ms0216/keyboard-foundry/projects/cckb/docs/fab-checklist.md

# 発注の直前に見るもの（cckb）

**ここに記録が無いと発注しない。書いたら消さない**（次の発注で同じ穴を踏まないため）。
`tools/kb cckb gate` が open-gaps の「発注をせき止めているもの」を見る。
ここに書くのは、それ以外に**機械では確かめられず人が見るもの**。

## 発注履歴

| 日付 | 対象 | 実装枚数 | 表面処理 | 備考 |
|---|---|---|---|---|

## §0 発注フォームで選ぶもの（JLCPCB）

| 項目 | 値 | 根拠 |
|---|---|---|
| 層 / 厚さ / 銅 | 2 層 / 1.6mm / 1oz | 2 層で足りた（HHKB） |
| 表面処理 | 有鉛 HASL | ¥0（無鉛は +¥222） |
| Remove Order Number | Yes | |
| PCBA | Economic・実装面は裏 | Standard は部品から板端 2.5mm 以上・70×70 以上が条件。**電源スイッチ SW_PWR は JLC に実装させない**（2026-09-24 から秋月の SS-12D00G3・スルーホールで LCSC に無い。前の MK-12C02-G025 はつまみが外形から 1.95 出た。Economic は部品を縁から 0.3 以上・はみ出す SMT 部品はキャリアが要る——JLC PCBA FAQ Part 2・PCB Assembly Fixtures。決定記録 2026-09-24-audit-fixes §R2）。利用者が秋月電子で買って手はんだ |
| Confirm Parts Placement | Yes | §1 を見るため |
| Via Covering | **Tented**（既定のまま） | 板の設定が表裏ともテント（`(tenting (front yes) (back yes))`・ガーバーのマスクの開口はパッドの数と一致）。エポキシ充填などは選ばない——XIAO の D0〜D6 の穴はビアではなく部品の穴（スルーホールパッド）で、この選択は効かない（2 回目の監査 C 軽微 4） |

## §0b 実際に発注する道具を本番の板に通した結果

自前の出力で直したつもりの誤りが、発注道具（Fabrication Toolkit）の出力では
直っていなかった（HHKB）。**実際に使う道具で出して、出力を読む。**

    tools/kb cckb fab-fields
    cd ~/Documents/KiCad/10.0/3rdparty/plugins
    "$KICAD_PYTHON" -m com_github_bennymeg_JLC-Plugin-for-KiCad.cli -p <板の絶対パス> -t -nI -nB
    # 出力は projects/cckb/pcb/production/（gitignore）。**道具は板を書き換えなかった**（前後で sha1 と指紋が同じ）

| 見たもの | 期待 | 結果（日付） |
|---|---|---|
| BOM の LCSC Part # | 全行に番号 | ✅ 6 行すべて（C49678・C54110×62・C8598・C17514・C778186・C52287685）（2026-09-24）→ **監査の直しの後: 5 行すべて**（C49678×2・C54110×62・C8598・C17514×2・C52287685×2。電源スイッチ C778186 は手はんだで外れた）（2026-09-24）→ **2 回目の監査の直しの後: 4 行すべて**（C49678×2・**C54110×63**〔キー 62＋D_PWR。D_PWR の既定を BAT46W にした・open-gaps O12〕・C17514×2・C52287685×2）（2026-09-24）→ **電源スイッチを SS-12D00G3 に替えた後も同じ 4 行・69 個**（Fabrication Toolkit で出し直して読んだ・2026-09-24） |
| CPL の Layer | 裏実装の部品が bottom | ✅ 70 行すべて bottom（2026-09-24）→ **69 行すべて bottom**（2026-09-24・監査の直しの後） |
| 手で付ける部品（XIAO・ホルダ・キーのスイッチ 62・**電源スイッチ**） | BOM・CPL に無い | ✅ どれも無い（2026-09-24・監査の直しの後も） |
| CPL の座標と回転で JLC が置く位置 | JLC の部品データ（EasyEDA の原点とパッド）を CPL どおりに置くと、板の同じ番号のパッドに乗る | ✅ 69 個すべて 0.09mm 以内（`tests/test_cckb_pcb.py::test_jlc_places_every_part_of_the_cpl_on_its_pads`。**検査が Fabrication Toolkit を板の写しに毎回通す**。回転を 90°/180° 違える・原点を 0.45 ずらすと落ちる）（2026-09-24） |
| TSSOP の回転 | `-t` で補正が入っている | ✅ U1/U2 は KiCad 180°（裏）→ CPL 270°（道具の表 `^TSSOP-` +270）。**正しいかは §1 のプレビューで**（2026-09-24） |
| ガーバーの層 | 2 層（内層が無い） | ✅ F_Cu・B_Cu・マスク・ペースト・シルク・外形・PTH/NPTH のドリルの 13 ファイル（2026-09-24） |
| ペーストの開口（B_Paste のフラッシュ） | JLC が実装するパッドだけ（ダイオード 63×2・C 2×2・R 2×2・595 2×16 ＝ 166）。手はんだの電源スイッチ（2026-09-24 からスルーホール 3 本・ペーストの層を持たない）に無い | ✅ B_Paste 166・F_Paste 0（2026-09-24・2 回目の監査 B2-1 の直しの後。前は 173 で SW_PWR の 7 個に盛られた。`test_only_the_jlc_parts_get_solder_paste`） |

## §1 配置プレビューで向きを見る

KiCad と JLC ライブラリの回転は一致しない。プレビューの Bottom 表示は X だけ裏返る。
**「+」は Pin 1 ではなくアノード**だった（SOD-123・HHKB で確認）。判定は 3D 本体の
帯（カソード）で。同じフットプリントなら 1 個読めれば全部に同じ結論が使える。

| 部品 | 面 | KiCad の板（CAD 座標・上から見て） | JLC のプレビュー | 判定（日付） |
|---|---|---|---|---|
| U1 SN74LVC595 | 裏 | 1 番 (−73.34, −5.93)＝**右上**（16 番は左上で C_U1 の隣）。CPL 270° | | 未 |
| U2 | 裏 | 1 番 (79.06, −5.93)＝右上（16 番は左上で C_U2 の隣）。CPL 270° | | 未 |
| D1〜D62 BAT46W（**62 個とも縦**。V2 = `cckb-v2`） | 裏 | カソード（帯・パッド 1・行の網）が**手前（−y）**・アノードが奥。板の上で 90°・CPL 90°（2026-09-26 に板と CPL で数えた: 62 個とも同じ） | | 未 |
| ~~D42・D43・D58・D60（横 4 個）~~ | 裏 | **V1 の行**。V2 ではスタビのキーのダイオードもほかと同じ縦（上の行） | — | 対象外 |
| D_PWR BAT46W（既定。O12 で B5819W に戻すなら読み直す） | 裏 | カソード（パッド 1・V3V3）が**右**（x −122.35・XIAO の 3V3 へ。V2 で (−124.0, −28.45) に動いた）。板の上で 180°・CPL 0° | | 未 |
| ~~SW_PWR SS-12D00G3~~ | 表（スルーホール） | **手はんだ（CPL に無い）**。2026-09-24 に MK-12C02-G025（裏）から置き換えた。足 3 本 (141.225, −36.1 / −38.6 / −41.1)・向きは問わない（足が対称） | — | 対象外 |

## §2 在庫（発注の直前に API で取り直す）

    tools/kb cckb parts

| 確認日 | 結果 | 薄い部品と代替 |
|---|---|---|
| 2026-09-24 | 全部在庫あり（parts-audit.md の表） | 74LVC595 C52287685 が 1,446（要 10）→ 代替 C426713（3,534）。電源スイッチ C778186 3,260（**利用者が LCSC で買う**・監査の直しで手はんだに）。**同日に秋月の SS-12D00G3（115707・通販在庫 38,944）へ置き換え** |

## §3 ピン配置を独立した視点で確かめる（**3 つ済むまで「確認した」と書かない**）

同じ人が同じ表を読んだ 1 視点では、読み違いは全視点で同じ方向に外れる。
IC・MCU・基板間コネクタのピン誤りは 0Ω では救えない。コネクタは「面」だけでなく
**口の向きと口から口までの経路**を追う。

| 部品 | A データシート ↔ pinmap | B 商品写真の 1 番 ↔ 描画 | C KiCad GUI でクリック | D 1:1 印刷に実物を載せる |
|---|---|---|---|---|
| 74LVC595 | ✅（TI SCASE93A Table 4-1 ↔ pinmap。HHKB で同じ表） | 未 | 未 | 未 |
| XIAO（表面実装） | ✅（公式 STEP のキャステレーション ↔ 板のパッド。検査） | 未 | 未 | 未 |
| SS-12D00G3 | ✅（図面の 3-φ0.8・2.5 間隔 ↔ 板のパッド。検査） | 未 | 未 | 未（入の向き・open-gaps P5、爪の出・O13） |
| BS-16-B4AK003 | ✅（図面のランド・＋の側 ↔ 板。検査） | 未 | 未 | 未 |

## §4 リスクを承知して発注する記録

open-gaps の `### 承知して発注する #N` と対応させる。

- **発注の前に利用者が決める・測るもの**（監査の直しで残ったもの）: open-gaps O11（595 の末端を D9 に戻すか）・
  P7（アンテナのまわりをアルミ箔で ¥0 で 1 回測る）・P11（スタビのワイヤが上か下か。実物が届いていれば）・
  P5・O13（電源スイッチ SS-12D00G3 の入の向きと、レバーの先の高さ。届いた 1 個と基板の厚さを測る・order-steps §1 の 3）・
  O14（電池の側にバルクコンデンサを後から足す場所を置くか。task-10a §6 の使える量が 96mAh 未満なら決める）
- ~~**O12（D_PWR を BAT46W のままにするか B5819W に戻すか）**~~ **2026-09-25 に BAT46W で決まった**（保証値で決まる・open-gaps O12）。受け入れた差 A1（USB を挿す前に電源スイッチを OFF）は
  どちらでも手順で残す（~~部品を替えられる品が無いことはデータシートで確かめた~~ ← 1 回目の比べ方は誤り。決定記録 §S2）

## §5 通電前の導通試験（基板が届いたら）

GND↔GND・電源↔電源が導通、電源↔GND が非導通。**通るまで電源を入れない。**

## §6 独立監査（電気 / DFM / 機械 / 外部の事実）

| 見つかったもの | 基板に効くか | どうした |
|---|---|---|
| 監査 A〜F（2026-09-24・HEAD 86611d4・`.superpowers/sdd/cckb-autonomy/audit-*.md`）: 致命 0・重要 5（A-1・B-1・C 重要 1/2・D 重要 1・E 重要 1/2/3。うち C 重要 2 と E 重要 1 と B-1 は同じ電源スイッチ）・軽微 23 | 効く: C 重要 1（パッドの中のビア）・C 重要 2/E 重要 1/B-1（電源スイッチ）・D 重要 1（XIAO の NFC2 の下）・E 重要 3（H3 の下）・軽微 C1/C2/C3/D4 | 裁定 R1〜R7 のとおり直した（決定記録 `decisions/2026-09-24-audit-fixes.md`・報告 `.superpowers/sdd/cckb-autonomy/fix-report.md`）。所見ごとの行き先は報告の一覧。直したものは各々に検査を足し、**直す前の板（HEAD 86611d4）でその検査が落ちる**ことを確かめた |
| 2 回目の監査 A〜E（2026-09-24・HEAD f95a7c9・`audit2-*.md`）: 致命 0・重要 2（A2-1 ダイオードの比べ方・E 重要 1 の H5/H6 のナットの下の CS）・軽微 13 | 効く: E 重要 1（禁止域と CS の置き直し）・B2-1/C1（ペースト）・C2（パッド内ビアの輪）。A2-1 は板は同じで BOM の品番 | 裁定 S1〜S3（決定記録 §S1〜S3・報告 `.superpowers/sdd/cckb-autonomy/fix2-report.md`）。**直す前の板（f95a7c9）に新しい金属の検査を当てると H5・H6 の CS（1.603）を出す**。配線が変わった網は CS（1 本 → 3 本）と GND（縫いのビア）だけ |
| 3 回目の監査（2026-09-24・2 回目の直しを・`audit3.md`）: 致命 0・重要 0・軽微 4 | 効かない | 行き先は status.md §5（直した 3・台帳 A10 に 1） |
| 電源スイッチの置き換えの監査（2026-09-24・`audit-psw.md`）: 重要 1（レバーの先の最悪値に基板の厚さの公差が抜けていた）・軽微 4 | 効かない（ケースと文書） | 最悪 0.2 → 0.36 に訂正（open-gaps O13）・軽微は 3f77086 で直した・台帳 A11・A12 |
| 4 回目の監査 A〜F と文書（2026-09-25・main 3f77086・`audit4-*.md`）: 致命 0・重要 3（E ふたの垂れ壁の隙 0・F 打ち止めの判定・文書 ゴーストの試験）＋文書の重要 2・軽微 60 余り。6 視点すべて「発注してよい」 | **効かない**（板の銅・穴・部品の位置は変えていない。sha1 05e23dfe… は前後で同じ） | ケース・ファーム・文書を直し、重要には検査を足して壊して落ちることを確かめた（branch cckb-fix4）。軽微の行き先は status.md §6。D 軽微 4（バルクの置き場）は利用者の判断 O14 |

**問題なしを確認したもの（母数）:** / **見ていないもの:**
