ms0216/keyboard-foundry/projects/cckb-click/docs/decisions/2026-10-04-knob-out-pilot.md

# 電源スイッチを 0.75 外へ（JLC の「2.5 mm」は満たさない）・下穴 φ1.6・蓋は考え直し

- **日付:** 2026-10-04
- **状態:** 決定（**直した板 b442b865… は、まだ独立に見直していない**: open-gaps #36。蓋は決まっていない: #34b・P21）
  **→ そのあと: #36 は 4 回目の監査で閉じた。蓋は「ねじ 2 本で留める」に一度決まり（決定記録 [2026-10-04-cover-screw](2026-10-04-cover-screw.md)）、同じ日に「道具なしで上から落とし込む」に置き換えた（決定記録 [2026-10-04-cover-latch](2026-10-04-cover-latch.md)。枠の口の形も、そこで変えた）**
- **決めた人:** 利用者（試し刷り v2 を刷って触った結果。下の 3 つ）。寸法と形は Claude

利用者の決定（2026-10-04・試し刷り v2 の結果。docs/coupon-test.md 8 章「結果」）:

1. **電源スイッチは (ii) = 0.75 外**。JLC の実装の規約「部品の本体と基板の縁は 2.5 mm 以上」より、**使いやすさを取る**
2. **ねじの下穴は φ1.6**（ふつうの M2×4 の小ねじ。3 つの径とも空回りしなかった。φ1.5 は入れ始めにかなり力が要った）
3. **蓋は 3 つとも使えない。蓋そのものを考え直す**（利用者が考える。ここでは作り直していない）

この記録は、決定記録 2026-10-04-switch-cover の「スイッチを 2.5 内側へ」と「差し込み式の蓋」を**置き換える**（そちらの冒頭に書いた）。

## 1. なぜ決める必要が生じたか

- 2.5 内側の位置（つまみの先は枠の外面の 1.35 内）は、刷って触ると**奥すぎた**（v1 の角の試し刷り）。v2 で 0.75 外の位置と並べて、利用者が (ii) を選んだ
- 下穴 φ1.8 は、最後まで締めると空回りした（v1 のねじの試し刷り）
- 蓋は v1（掛かり 0.25）も、v2 の 3 つ（折り返しばね・細い腕・筋）も留まらなかった

## 2. 事実はどうか（測った・読んだもの）

| 何 | 前の板（fe90b1e6…） | いまの板（b442b865…） | 何で確かめたか |
|---|---|---|---|
| 電源スイッチの足跡の原点 | (141.125, −38.1) | **(141.875, −38.1)**（x だけ +0.75） | 板（前の板と今の板の部品を全部突き合わせた: 動いたのは SW_PWR だけ） |
| 本体の縁 → 基板の縁 | 2.50 | **1.75** | 板の上の突起の穴（本体の中心線）＋ 図面の本体の幅 2.8（tests `psw_edge_problems`） |
| つまみの先 → 基板の縁／枠の外面 | 1.05／1.35 内 | **0.30／0.60 内**（入でも切でも同じ。つまみは前後に滑るだけ） | 同上 ＋ 図面のつまみの出 1.45 |
| スイッチのランドの外の端 → 基板の縁 | 2.45 | 1.70 | 板のパッドの外接 |
| スイッチのランドの左の端 → C_BAT のランド | 1.375 | 2.125（C_BAT は動かしていない） | 同上 |
| 入の向き | つまみを奥 = 入 | **変わらない**（奥の端子 3 番が VBAT_SW・真ん中 2 番が VBAT_IN・手前 1 番は空き） | 板のパッドの網（検査） |
| 枠の入の印 | 切り欠きの内側の面の 1.2 内・入に寄せたつまみの奥の縁の高さ | **高さ（y）は同じ**。x は、斜めに落とした面のすぐ内の平らな上面（内側の面から 3.2 内） | 枠の立体（検査）。斜面の上に置くと、上面から掘る印は空を切る |
| 線・ビア（右手前の角の外） | — | **角の中の 8 本のほか、長い VBAT_SW の右の端が 0.75 延びた**（変わった線は 9 本。x 138.125 → 138.875〔監査の座標では 288.125 → 288.875〕。差は x ≥ 287.6・y 127.9〜143.2 に収まる〔4 回目の監査で言い直した〕） | 板どうしの突き合わせ（線 772 本・ビア 906 → 907 個・ルール領域 134 個・両面のベタの塗り） |
| 線・ビア（角の中） | — | 線 8 本を引き直した（VBAT_IN・VBAT_SW の端と C_BAT の枝・スイッチの枠のランドの GND の 4 本）。GND のビアは 6 個消えて 7 個足した | 同上 |
| ベタの塗りの違い（角の外） | — | 表も裏も 0（角の中は 表 17.7・裏 4.2 mm²） | 同上（塗りの多角形どうしの差） |
| SPI・595 どうし・電源の枝 | 監査した板の線を置き直し | **同じ**（pcb/freerouted.json・線 100・ビア 17） | 検査 `frozen_problems`・route.json |
| DRC | 違反 0・未配線 0・警告 0 | **違反 0・未配線 0・警告 0** | kicad-cli |
| BOM・CPL | 7 行・133 行 | 7 行・133 行。SW_PWR の行は (291.875, −138.1)・90° | 発注道具の出力 |
| 下穴の径（設計） | φ1.8 | **φ1.6**（外周 20 ＋ 予備 2 = 22 個とも） | 枠の立体（検査が 22 個を見る） |
| 下穴の径（刷る線が空ける径） | 1.76〜1.79 | **ふつうの壁 19 個: 1.54**（平均 1.537〜1.543）・**薄い壁 3 個（H16・H17・H18）: 1.49〜1.50** | 本番の枠 2 枚をスライスした G-code（`tools/slice_main.py`・Bambu Studio 2.8.2） |
| 　試し刷り v2 で利用者が締めた切れ端 | — | φ1.6: 1.54／1.50・φ1.5: 1.44／1.40・φ1.7: 1.64／1.60（ふつうの壁／薄い壁） | v2 の G-code（`tools/slice_v2.py`・同じ測り方） |
| ねじ山の掛かり（半径） | 0.10（山の 46 %） | 0.20（92 %） | ISO 724 の M2（外径 2.0・めねじの内径 1.567）から |
| 下穴のまわりの肉（内側） | 0.70／薄い所 0.49 | 0.80／0.59。**ねじの外径 2.0 の外に残る壁は変わらない**（0.6／0.39） | 枠の立体（検査） |
| 指先（半径 7.5 の硬い球・机の上）が、つまみの先より奥へ入る量 | −0.03（新しい切り欠きでも届かない） | **+0.16** | 本番の枠の角の立体に球を当てた（`click_case.finger_reach`）。**球の半径は仮定** |

## 3. 効く条件（候補を並べる前に）

| # | 条件 | 実データ | 何で確かめたか |
|---|---|---|---|
| 1 | 指でつまみを動かせる | 利用者が (ii) を選んだ。物差しでは −0.03 → +0.16 | **外: 利用者が刷って触った**（v2 の B）。数は自分の生成物（物差し） |
| 2 | 外へ出る物が無い（鞄の中で引っ掛からない） | つまみの先は枠の外面の 0.60 内・基板の縁の 0.30 内 | 板の突起の穴と図面（検査）。枠の立体でも見る |
| 3 | JLC の実装の規約「本体と基板の縁は 2.5 mm 以上」 | **満たさない（1.75）** | 外: JLC の規約の頁（docs/order-steps.md の出どころ・2026-10-04 に読んだ値）と、板の寸法 |
| 4 | Economic の注意書き「線と部品は縁から 0.3 mm 以上」 | つまみの先で **名目ちょうど 0.30**（ランドは 1.70・本体は 1.75） | 同上 |
| 5 | JLC が載せないと言ったときの手 | 手はんだ（端子 3 ＋ 枠 4 = 7 か所・C431540 を 1 個）。**基板は変わらない** | 足跡のパッドの数（板） |
| 6 | 監査した配線を変えない | 上の表（線 9 本 = 角の中 8 本＋VBAT_SW の右の端） | 板どうしの突き合わせ |
| 7 | 切り欠きのまわりの壁が弱くならない | 下の §5「枠」。厳しい見方で 20.4 MPa（上限 38）・前の形は 7.3 | 計算（断面は枠の立体から測る）。**利用者が触った (ii) の切れ端と同じ形**（式から作った切れ端と本番の枠が同じ立体であることを検査で見る） |
| 8 | ねじが空回りしない | φ1.5／1.6／1.7 とも空回りしなかった | **外: 利用者が締めた**（v2 の A）。**締め直した回数は聞いていない** |
| 9 | ねじを入れ始められる | φ1.5 は入れ始めにかなり力が要った。φ1.6 は薄い壁でも問題なし | 同上 |
| 10 | 壁が割れない | 利用者の報告に割れは無い（φ1.6・薄い壁でも問題なし） | 同上。本番の枠でも 1 本入れて確かめる（P1） |
| 11 | 本番の枠の下穴が、利用者が締めた物と同じ径で刷られる | 1.54／1.50 で同じ | 本番の枠と v2 の、両方の G-code を同じ測り方で |

## 4. 影響範囲（力と信号の流れに沿って）

- **スイッチの位置 → 足跡 → 電池の＋（VBAT_IN）の最後の区間・VBAT_SW の縦の区間と C_BAT の枝・枠のランド 4 つの GND のビア → 角の GND の縫いのビア**。
  どれも決まった形で引く線（click_routes）なので、足跡と一緒に 0.75 動いた。長い線（VBAT_SW・263 mm）は右の端が 0.75 延びただけ。
  SPI・595 どうし・電源の枝（左手前）は置き直しで、変わらない
- **スイッチの位置 → JLC の規約 → 頼み方**: 2.5 mm を満たさないので、JLC が載せないと言うことがありうる。そのときは手はんだ（docs/order-steps.md の冒頭）
- **スイッチの位置 → 枠の逃げ・切り欠き・厚い屋根 → 壁の強さ**: 切り欠きの内側の面は本体の縁 ＋ 0.4（枠の外面から 1.65）。切り欠きの形は v2 の B と同じ
- **指 → 切り欠き → つまみ → スイッチの本体 → はんだ（端子 3・枠 4・突起 2）→ 基板**: つまみを動かす力（最大 2.45 N）は基板が受ける（前と同じ）。
  ランドと基板の縁の間は 1.70（前は 2.45）
- **下穴 → ねじ山の掛かり → 壁の内側の肉 → キーの穴 → キャップ**: 穴の位置は変えていない。肉は 0.1 増えた。ねじが押し広げる樹脂は増える
  （ねじの外径の外の壁 0.6／0.39 は同じ）
- **下穴 → 試し刷り（ねじ・角・v2）**: どれも本番の枠から切り出すので、下穴と切り欠きが新しい形になる（v2 は、刷った物と同じ形を出し続けるように、
  位置を本番から測り直した: (i) = 本番から 0.75 内・(ii) = 本番）
- **蓋 → 枠の口のまわり・基板の穴 H30・H31**: 蓋を刷る物から外しただけ。枠のひさし・溝・指の切り欠き・基板の穴は前のまま

## 5. 決めたこと

### 基板

| 何 | 決定 |
|---|---|
| 電源スイッチ | 足跡の原点 (141.875, −38.1)。向き・端子の網は同じ。**JLC に載せてもらう（BOM・CPL に入れたまま）。断られたら手はんだ** |
| C_BAT | 動かさない（(136.2, −33.0)。スイッチのランドから 2.125） |
| 決まり（spec） | `PSW_TIP_INSIDE = 0.3`（つまみの先は基板の縁の 0.30 以上内側。これより外へは寄せない）・`PSW_BODY_TO_EDGE = 1.75`（記録。検査が板と突き合わせる） |
| 蓋のねじ穴 H30・H31 | 残す（使い道は蓋を考え直すときに決める） |

### 枠

| 何 | 決定 | 刷って直せるか |
|---|---|---|
| つまみの切り欠き | **利用者が (ii) で触った形**: 内側の面で幅 10・外面へ向かって片側 2.4 ずつ広がる（外面で 14.8）・内側の面の上の縁を 2.0 斜めに落とす（45°）。`PSW_NOTCH = (10.0, 2.4, 2.0)` | 直せる（右の枠だけ） |
| 切り欠きの内側 | 屋根を基板の上 1.8 まで厚くして塞ぐ（前と同じ）。斜めに落とした後、内側の面で 1.2 残る | — |
| 入の印 | 斜面のすぐ内の平らな上面。高さ（y）は前と同じ | 直せる |
| 下穴 | **φ1.6**・22 個とも。**薄い壁の 3 個も補正しない**（下） | 直せる（きつければドリルで広げる） |
| 電池の口のまわり | **変えない**（ひさし・溝・指の切り欠きは前のまま） | — |

**薄い壁の下穴を補正しない理由**: 薄い壁（幅の広いキーの脇の H16・H17・H18）では、刷る線が設計より 0.04〜0.05 内へ寄る（壁が線 1 本になるため）。
φ1.6 は線で 1.49〜1.50 になる。これは、利用者が v2 で「薄い壁でも問題なし」とした切れ端（線で 1.50）と**同じ径**で、入れ始めが固かった φ1.5（線で 1.44／1.40）ではない。
補正して φ1.65〜1.7 にすると、利用者が確かめていない組み合わせになり、ゆるい側へ寄る（ゆるい穴は直せない・きつい穴はドリルで広げられる）。
`tools/slice_main.py` が、本番の枠の 22 個を G-code で測って、利用者が確かめた径（1.54 ± 0.03／1.50 ± 0.03）から外れたら NG を出す。

**切り欠きのまわりの強さ（計算。材料は Bambu PLA Basic の TDS の曲げ強さ 76 MPa の半分 = 38 MPa を上限に置く）**

| 見方 | 前の形（外の角を 1.0 落とすだけ） | いまの形（内側の上の縁を 2.0 斜めに） |
|---|---|---|
| 内側の縁を指で下へ 10 N。**縁の 2.0 幅だけ**が、幅 10 を渡る梁として働く（いちばん厳しい見方） | 7.3 MPa | **20.4 MPa**（上限の 0.54 倍。断面は台形 = 内側の面で 1.2・2.0 奥で 3.2） |
| 同じ。厚い屋根の全幅 5.4 が働く | — | 3.5 MPa |
| 切り欠きの手前に残る壁（角まで）を y の向きに 10 N（せん断） | 0.44 MPa（長さ 7.525） | 0.49 MPa（外面で長さ 5.125） |

余裕は前より減った（5.2 倍 → 1.9 倍・厳しい見方で）。**20 N なら、厳しい見方では上限を超える**（検査に入れた）。断面は枠の立体から測る（式で置いた台形と合うことも検査で見る）。
利用者が触った (ii) の切れ端と同じ形なので、割れやすさは刷った物で分かっている範囲（利用者の報告に割れは無い）。

### 刷る物

| 何 | 決定 |
|---|---|
| 電池の蓋（`cover_battery.stl`） | **刷る物から外した**（STL を出さない・組んだ絵にも入れない）。形（`click_case.cover_solid`）と検査は、枠の口のまわりの形の説明として残してある |
| 試し刷り（ねじ・角・v2） | 済み。作り続ける（本番の枠から切り出す検査が、本番の形を見張る） |

## 検討して捨てた案

| 案 | 捨てた理由 |
|---|---|
| (i) のまま（本体は縁から 2.5）で、爪で使う | 利用者が (ii) を選んだ |
| つまみに被せる刷り物で、位置は (i) のまま | 作っていない（利用者は (ii) を選んだ）。JLC に断られて、手はんだもしたくないときの手として残る |
| 0.75 より外へ | つまみの先が基板の縁の 0.30 内 = Economic の「縁から 0.3 以上」の下限。これより外は、その注意書きも満たさない |
| 薄い壁の下穴だけ φ1.65〜1.7 にして、線の径をふつうの壁に合わせる | 上の「補正しない理由」 |
| 下穴 φ1.5 | 入れ始めにかなり力が要った（利用者）。めねじの内径 1.567 より小さく、ねじが樹脂を押し広げる |
| 下穴 φ1.7 | 空回りはしなかったが、掛かりが半径 0.15（69 %）で、φ1.8（空回り）に近い側 |
| 蓋をこの作業で作り直す | 利用者が蓋そのものを考え直している（頼まれた範囲の外） |

## この決定が乗っている前提（動いたら読み直す）

- **JLC の規約の「2.5 mm」と Economic の「0.3 mm」は 2026-10-04 に読んだ値**（出どころは docs/order-steps.md §2-1）。JLC が実際にどう扱うかは、注文してみるまで分からない
- 電源スイッチは MSK12C02（本体 8 × 2.8・つまみの出 1.45・行程 1.6）。**つまみの出は図面の名目**（置くずれ・基板の外形の公差 ± 0.2 は見ていない）。
  **つまみの出の公差（4 回目の監査 2026-10-04 で直した）**: MSK12C02 の図面（LCSC C431540・2024-12-14）は、つまみの出 1.45・中心から先まで 2.85 に**個別の公差を書いていない**。表題欄の未注の公差は X.xx = ± 0.2（± 0.1 はつまみの幅 1.3・本体の幅 2.8・突起 φ0.75 だけ）。**前の記録の「± 0.1」は誤り → ± 0.2**。出どころ: 図面を自分で開いて読んだ（datasheet.lcsc.com の PDF 1 頁目の表題欄。2026-10-04）。**最悪の場合**: 基板の縁に対して 0.30 − 0.20 − 0.075（φ0.75 の突起と φ0.9 の穴の遊び）= **+0.025**（細い突起 φ0.65 なら −0.025）= 先は**実質、基板の名目の縁まで届きうる**。枠の外面に対して 0.60 − 0.20 − 0.075〜0.125 − 0.1（ねじ穴の遊び）− 0.1（刷りの誤差）≒ **+0.10〜+0.13** = 枠の外へは出ない。
  **利用者の選択肢（まだ決めていない）**: スイッチを 0.2 内へ戻す（先は基板の縁の 0.50 内）と余裕は戻るが、利用者が触って選んだ位置から離れる。
- ねじは**ふつうの M2×4 の小ねじ**で試した（買う物の表のスリムヘッドではない。ねじ山は同じ M2 並目）。掛かりの長さ 2.4
- 刷り方は 0.4 ノズル・層 0.1・Bambu PLA Basic（下穴の線の径は、この設定での値）
- `pcb/freerouted.json` は板 4dc68901… から写した物のまま（左手前の配置は変えていない）
- 利用者の指は 1 人ぶん。指先の球（半径 7.5）は物差し

## 覆す前に読むこと

- スイッチの位置は発注後に直せない。**内へ戻す（2.5）と JLC の規約は満たすが、利用者が「奥すぎる」と言った位置に戻る**
- 下穴を変えるなら、`tools/slice_main.py` の許す幅（利用者が確かめた径）も一緒に見る。小さくする側は φ1.5 が固かった
- 切り欠きの斜めに落とす量を増やすと、内側の縁が薄くなる（3.0 にすると、厳しい見方で上限を超える: 検査）

## まだ決めていないこと・分からないこと

| 項目 | なぜ |
|---|---|
| JLC が電源スイッチを載せるか | 注文画面か、注文の後の確認でしか分からない（docs/order-steps.md）。断られたら手はんだ |
| ねじを何回締め直せるか | **利用者が締め直した回数を聞いていない**（open-gaps P1）。分解のたびに締め直す |
| スリムヘッドのねじでも同じか | 試したのは、ふつうの小ねじ。ねじ山は同じだが、頭が薄いのでドライバーの掛かりが違う |
| 本物のスイッチのつまみを指で動かせるか | 試し刷りのつまみは樹脂の小片（P22） |
| 電池の蓋をどうするか | 利用者が考え直している（#34b・P21）。**新しい蓋が基板に何か要るなら、発注の前に決める** |
| 直した板の独立した見直し | まだ（#36） |
