ms0216/keyboard-foundry/projects/cckb-click/docs/decisions/2026-10-03-board-and-case.md

# 基板と枠: 部品の足跡・配置・配線の形・枠の留め方・分け方・角・電池の出し入れ・底

- **日付:** 2026-10-03
- **状態:** 決定（設計）。`[暫定]` の値は docs/provisional-values.md
- **⚠️ 先に読むこと（2026-10-04）:** 1 回目の独立した監査（致命 0）で、下の数字のうち次が変わった。**正は [2026-10-04-audit-1](2026-10-04-audit-1.md)。**
  ねじの穴: 外周 20 ＋ 予備 2・枠の外面から 2.4（前は 2.5）・下穴のまわりの肉は外 1.5・内 0.7（前は 1.6・0.6）／
  電池: 止めに当たる所に座る（クリップの原点から 0.51 奥）・指の切り欠きの奥行き 4.5（前は 4.0）／
  GND: 595 のいるキーの中も 15 mm 以内（前は 17.2）／ 載せないコンデンサのランド 2 つを足した ／
  JLC の頼み方（Economic か Standard か）は利用者が決める（docs/order-steps.md §2-1）
- **決めた人:** 部品（スイッチ・ダイオード・595・電池クリップ・電源スイッチ・XIAO は表に平置き・裏には何も置かない・基板 1.6・1 枚）は利用者。
  形と数値は Claude。**利用者にしか決められないこと**（底のシート・ねじを買う・基板の表面処理）は status.md にまとめた

## 1. なぜ決める必要が生じたか

試し刷りで 1 マスの形（案 B・穴 17.05 角・つばのキャップ）が決まった（2026-10-03-coupon-result）。基板は発注すると直せないので、
基板・枠・キャップ・ファームを通しで設計し、機械で確かめられる所まで確かめてから、独立した監査へ渡す。

## 2. 事実はどうか（読んだもの・測ったもの）

**部品（データシート・製造元の図・JLC の部品ページ。2026-10-03）**

| 部品 | 読んだ物 | 事実 |
|---|---|---|
| スイッチ SKRAAWE010（C202383） | Alps の製品ページの図（Land dimensions・Circuit Diagram）・製品仕様書 | ランド 4 つ（外外 8.5 × 5.0・内内 3.0 × 3.0）。端子 ①—②・③—④ が中でつながる。定格の下限 1 V・10 µA。跳ね ON・OFF とも 10 ms 以下。10.3(4)「スイッチの下・近くに穴を置かない」。はんだペーストの厚さ 0.15 |
| 同じランドの実績 | 販売者が JLC に実装させた基板（PCB_Data/ClickBoard Tenkey/Assemble Alps Silent・MIT）の足跡 SKRACAE010_1u | Alps の図と同じランド（2.75 × 1.0 を ±2.875, ±2.0） |
| 電池クリップ MY-1632-03-R（C20606805） | MYOUNG の図面 MY-CP-0247 | 高さ 4.0・板の幅 16.9・端子込み 23.2 ± 0.3・止め（幅 6.35）から口まで 15.10。＋のランド 4.15 × 4.20 を中心の間 20.05。**−は電池が基板に直に当たる**（図に寸法なし。LCSC の足跡は中心に φ7.0）。口の縁の真ん中は 1.4 えぐれている（LCSC の足跡の外形） |
| 電源スイッチ MSK12C02（C431540） | SHOU HAN の承認書（2024-12-14）の外形図・安装参考图 | 本体 8 × 2.8・**高さ 1.4**・つまみ 1.3 幅が**本体の横へ** 1.45 出る・行程 1.6・位置決めの突起 φ0.75 × 2・1P2T（2 が共通）・枠は回路図でアースへ。12 V 50 mA・1 万回 |
| JLC の実装の種類 | 部品ページ（jlcpcb.com/partdetail/…）の「PCBA Type」 | 8 品とも **Economic and Standard**（projects/cckb-click/tools/parts_check.py が取り直す） |
| ねじ | MISUMI の規格表（スリムヘッド小ねじ・超極低頭 M2） | 頭 φ4.0・頭の高さ 0.5 ± 0.1 |
| XIAO nRF52840 | 公式 STEP（lib/xiao.3dshapes）を測った | シールド缶の上面が下面から 3.25・USB のシェルの上面 4.47 |

**在庫と単価（JLC の API・2026-10-03）**: docs/shopping-list.md。

## 3. 効く条件

| # | 条件 | 実データ | 何で確かめたか |
|---|---|---|---|
| 1 | 足跡が部品に合う | スイッチ・電池クリップ・電源スイッチ | 外（製造元の図の値・LCSC の部品データ・販売者の足跡）＋検査（0.1 ずらすと落ちる） |
| 2 | JLC が置く位置と向きが板のパッドに合う | 133 個とも 0.15 以内・番号ごと | 外（発注道具の CPL ＋ JLC の部品データ）＋検査（180° 回す・0.3 ずらすと落ちる） |
| 3 | 回路が CCKB と同じ（ファームを共有できる） | 違うのは電池の部品・電源スイッチ・試験用のランドだけ | 検査（CCKB の回路の宣言と突き合わせる） |
| 4 | 宣言どおりに繋がっている | 567 パッド・未配線 0 | 外（KiCad の DRC・板から読んだパッドのネット） |
| 5 | JLC の規則（線・間隔・穴・縁）・短い長円が無い | 違反 0・警告 0・穴は全部丸 | 外（kicad-cli の DRC・規則は foundry.pcb_rules）＋発注道具のドリルのファイル |
| 6 | アンテナの下に銅が無い・XIAO の裏の露出パッドの下の表に銅が無い | 0 mm²（対照は銅あり） | 板から測った面積（CCKB と同じ禁止域の決め方） |
| 7 | ねじの頭（金属）の下に裏の銅が無い | 28 か所とも 0 | 同上 |
| 8 | 電池の下と抜き差しの道に表の銅が無い（電池の缶〔＋〕が擦れても GND に触れない） | 電池のパッドだけ | 同上 |
| 9 | スイッチの本体の下にビアが無い（Alps 10.3(4)） | 84 か所（空きランドも） | 板のビアの位置 |
| 10 | GND の細い帯の先がビアから遠くない | 表 13.3・裏 14.2 mm（595 のいるキーの中だけ 17.2） | 板の塗りを格子に落として銅の上の道のりを測る（ビアを消すと落ちる） |
| 11 | スイッチの定格の下限（1 V・10 µA）を走査で満たす | 打ち止め 2.0 V でも約 109 µA | 計算（BAT46W の Vf の保証値・nRF52840 のプルダウンの最大 16 kΩ）。**実機で測る**（open-gaps #7） |
| 12 | キャップが、置いたとき・押し切り・縁を押し切った傾きで何にも当たらない | 62 個 × 5 通り・干渉 0 | 立体を動かして重ねる（背の高い部品・穴の下の柱・深い押し込みで落ちる） |
| 13 | 組める・外せる | キャップ 62 個が枠の下からまっすぐ入る・基板の部品が枠へまっすぐ入る・電池が口から抜ける・USB が挿さる | 立体の道を枠と重ねる |
| 14 | 刷れる | 枠は上面をベッドに・支え無し・A1 mini に入る（156.4 と 140.0） | 立体の「上を向いた面」を数える＋実際にスライス |
| 15 | 誤入力しない剛性 | 下の §2-2 | 計算（断面は立体から）。**材料の値と、ねじの効きは測っていない** |

### 2-2. たわみ（click_stiffness.py・build/cckb-click/main_stiffness.png）

重さ 約 207 g・長さ 291.75。材料は一般値（FR-4 18〜24 GPa・PLA 2.3〜3.5 GPa。**測っていない**）。枠の断面は作った立体を切って測った。

| 持ち方 | 基板だけ | 枠を載せただけ（ねじが効かない） | 一体（ねじでずれ 0） |
|---|---|---|---|
| 片端を持つ（手の中 30） | 5.3（4.9〜6.5） | 3.6（3.0〜4.2） | 1.2（0.9〜1.3） |
| 両端を持つ | 0.9 | 0.6 | 0.2 |
| 両端を持って真ん中を 10 N で押す | 6.8 | 4.5 | 1.5 |

（mm。かっこは材料の幅。）実物は「載せただけ」と「一体」の間。**どこになるかは、外周のねじ 20 本がずれをどれだけ止めるかで決まり、計算では分からない**
（穴 φ2.2 にねじ φ2.0 = 片側 0.1 の遊び。締めた摩擦でどこまで止まるか）。

**誤入力に効くのは、この全体のたわみではない。**枠の下面と基板の距離が、押していないキーの所で 0.1 縮むと（公差の端の個体で）ON になる。
枠と基板は全部のキーの脇の柱（141 本）で突っ張っているので、縮むのは柱と柱の間だけ:

| 縮む原因 | 量（材料は柔らかい側） | 余裕 0.1 に対して |
|---|---|---|
| 指が底を突いて、枠のリブの交点を 3 N で押す | 0.026 | 26% |
| 同じ所を 10 N で強く押し込む（断面は作った枠を切って測った 2.64 mm²。式だけのときは 2.8 と置いて 0.078 だった） | 0.086 | 86% |
| 柱 1 本が 10 N で縮む | 0.002 | 2% |
| 一緒に曲がるときの、柱の間の弧の差 | 0.000001 以下 | — |

名目の個体（浮き 0.2 ＋ ON まで 0.3 = 0.5）なら 10 N でも 16%。

## 4. 影響範囲（信号・力・手の流れに沿って）

- **指 → キャップ → スイッチ → ランド → ダイオード → 行のバス → XIAO**／**595 → 列の束 → 列のビア → 裏の縦線 → 各段のスイッチ**。
  行は表の横一直線、列は裏の縦線。XIAO からバスまでは裏（XIAO の下の表は銅の禁止）。595 から列までは、段 2 と段 3 の間の表を束で走る
- **指 → 枠のリブ → 柱 → 基板**／**枠の壁 → ねじ → 基板**。ねじは外周だけ（下の「中の押さえ」）
- **電池 → 口（手前の壁）→ クリップの下 → 基板の裸の銅**。指は切り欠きから電池の上面へ
- **USB のプラグ → 枠の切り欠き → XIAO の口**。プラグの樹脂は枠の外面の外 0.7
- 枠を 2 枚に分ける → 継ぎ目の列のキャップは、左の枠のリブと右の枠の穴の両方に触る → 左右のずれが隙 0.2 を食う（open-gaps P3）
- 基板の縁を枠が 0.3 覆う → ~~電源スイッチのつまみは基板の縁から 0.7・枠の外面から 0.4 出る → **JLC が縁からはみ出す部品を載せるか**（order-steps §3）~~
  **2026-10-04 に変えた**: スイッチを 1.75 内側へ。つまみは枠の外面の 1.35 内側（決定記録 2026-10-04-switch-cover）。
  **同じ日にもう一度変えた**: 刷って触ると奥すぎたので 0.75 外へ戻した。つまみは枠の外面の 0.60 内側・本体は基板の縁から 1.75
  = **JLC の「2.5 mm 以上」は満たさない**（決定記録 2026-10-04-knob-out-pilot）

## 5. 決めたこと

### 基板

| 何 | 決定 | なぜ |
|---|---|---|
| 外形 | 291.15 × 100.65・角 R2.0・1.6 mm・1 枚・2 層 | キー領域 ＋ 枠の縁 3.0 − 枠が覆う 0.3 |
| スイッチのランド | Alps の図のまま（SW_Alps_SKRA_6.2x6.2）。**EVQQ2 と重ねたランドにしない** | 大きなランドは、リフローで部品が自分で中心に寄る力を弱め、浮き・傾きを出しやすい。押す面の余裕は 0.1〜0.2。安全と言い切れない |
| 幅の広いキー 11 個 | 真ん中のスイッチ（JLC が実装）＋左右に**空きランド**（真ん中と並列・実装しない・はんだを載せない）。中心は穴の端から 4.3（1.5u ±8.99・1.75u ±11.37・2.25u ±16.13） | 外に置くほど、端を押したときの傾きが小さい。ランドの外端が穴の端のすぐ内側（柱の下に入らないいちばん外） |
| ダイオード | 表・スイッチの手前 5.6・横置き。アノードが手前右のランドの真下 | スイッチ → ダイオードが縦の 1 本。背 1.35 は、縁を押し切ったキャップの下面（公差の端で 1.6）より低い |
| 595 ×2 | **左 Shift（2.25u）の、真ん中のランドと左右の空きランドの間**に 270° で。U2 が左・U1 が右 | 1u のキーの中には入らない（本体と穴の縁の間 5.4）。XIAO のすぐ奥で SPI が短い。奥の列のピン（Q1〜Q7）が束の帯に向く |
| 列の束 | 段 2 と段 3 の間の表を 15 本（0.4 おき）。行き先の近い線ほど手前 | 裏は列の縦線の櫛で、横に長く走れない。段 3 にはほぼ全部の列のキーがある（列 0・12 は裏の縦線へビアで） |
| VBAT_SW の長い線 | 決まった形（段 3 のバスの 1.9 手前・電源スイッチ → 試験用のランド TP_VSW） | Freerouting に任せると、バスとの間にビアの打てない GND の帯（263 mm）ができた |
| 電池の −のランド | 裸の銅 φ7.0・はんだを載せない・中にビア 3 個で裏の GND へ。電池の下と抜き差しの道は表の銅なし | 平らでないと電池が浮く。電池の缶（＋）が GND に触れない |
| 電源スイッチ | ~~つまみを右の縁へ。先が枠の外面から 0.4 出る。~~ **2026-10-04 に変えた: つまみは枠の切り欠きの中。本体は基板の縁から ~~2.5~~ → 1.75**（決定記録 2026-10-04-switch-cover → 2026-10-04-knob-out-pilot）。奥へ寄せると入（**図の読み**。これは変わらない） | 入の向きは基板が届いたらテスターで |
| ねじの穴 | 外周 20（キーの辺の真ん中）＋ 中 8（下） | 下 |
| Freerouting | SPI・595 どうし・電源・電池電圧の 8 網だけ。「最適化」は切る | 行列の 628 本を障害物として渡すと、最適化 1 回が 17 分で何も変わらなかった |

### 枠・ねじ・底

| 何 | 決定 | なぜ |
|---|---|---|
| 外形 | 291.75 × 101.25 × 5.0（基板の上）。縁はキー領域から 3.0 | 外周の壁に M2 を立てる肉（外 1.6・内 0.6） |
| 留め方 | **スリムヘッド M2×4 を基板の下から、枠の壁に直に切る**（下穴 ~~φ1.8~~ → **φ1.6**〔2026-10-04・試し刷り v2 の結果〕・深さ 2.8・掛かり 2.4）。20 本 | 厚さを足さない。インサート（外径 3.2）・ナット（二面幅 4.0）は壁 4.0 に入らない |
| 中の押さえ | **基板に穴だけ開ける（8 個）。枠の足は既定では付けない** | 足は柱から横へ出た円盤で、枠を上面を下にして刷ると宙に浮く（支え材が、キャップの滑る面のすぐ脇に立つ）。掛かりも 1.4 しか取れない（キーの縁を押し切ったキャップの下面が 1.6 まで下りる）。誤入力には要らない（縮む向きは柱が止める）。枠が反って真ん中が浮く（がたが増える）ときの手。**基板の穴は後から開けられない**ので開けておく |
| 分け方 | 左右 2 枚（156.4 と 140.0）。段ごとにキーの境目で。継ぎ目のリブは左が持つ。隙 0.1 | A1 mini（168）。リブを半分に割ると、くぼみを掘って 0.4 しか残らない |
| 左の角（XIAO） | 屋根 1.3（下面 3.7）。USB の口の上は切り欠き（屋根なし） | シェルの上 4.57 から枠の上面まで 0.43 しか無い |
| 右の角（電池） | 屋根 0.7（下面 4.3）。**手前の壁に電池の口**（幅 16.6 × 高さ 3.6）と、その上の指の切り欠き（幅 13 × 奥行き 4） | **分解せずに電池を替える**。クリップの口のえぐりと切り欠きを合わせ、電池の上面が手前から約 3 mm（23 mm²）見える |
| 底 | 基板の下面に厚さ 0.5 のシート（ねじの頭の所は φ5 の穴）。**何を貼るかは利用者**（status.md）。刷った板は付けない | 基板の下へ出るのはねじの頭 0.5 だけ。刷った板は 0.6 以上厚くなる |
| 厚さ | **8.1**（シート 0.5 ＋ 基板 1.6 ＋ キャップの上面 6.0）。枠の上面まで 7.1 | 目標どおり。シートの厚さは買う物で変わる |

## 検討して捨てた案

| 案 | 捨てた理由 |
|---|---|
| 595 を 1u のキーの奥の帯に | 本体 ±3.1 と穴の縁 8.525 の間は 5.4。TSSOP の長さ 5.0 ＋ 余白が収まらない（DRC の重なり） |
| 595 を右の角（屋根の下） | 列 15 本を角から各列へ運ぶ道が無い（裏は列の縦線で塞がる・表は行のバスで塞がる） |
| 列を全部 Freerouting に | 16 回回して 15 本残った。595 を自分の線で囲んでいた・表に通れる所が少ない |
| 表のベタの最小幅を 1.1（ビアの打てる幅）に | 595 の GND のピンのビアが表のベタから切れて、配線の道具が止まった |
| キー領域の中にもねじ（リブの下の柱に） | リブ 2.0 に M2 は立たない。柱を太らせると、押し切ったキャップ・つばの下に入る |
| インサート・ナット | 壁 4.0 に入らない。厚さを足すことになる |
| 枠で基板の縁を巻く | 壁がさらに 1.5 要る。ねじの肉が無くなる |
| USB の口の上に厚さ 0.4 の皮 | 刷れても、押すと割れる |
| 電池を上から替えるふた | ふたとその留め（ねじ・爪）に厚さが要る。横から抜く方が部品が無い |
| 電源スイッチを基板の縁に揃える（つまみが 1.45 出る） | 鞄の中で引っ掛かる |

## この決定が乗っている前提（**動いたら読み直す**）

- 1 マスの形（穴 17.05・つば F・押す面 3.6）。変えたら、押し切り・傾きの検査と、ダイオード・595 の背の余裕を見直す
- スイッチが SKRAAWE010（本体 2.5・ランドは SKRACAE010 と同じ）
- 行列の割り当てが CCKB と同じ（列 0・12 だけ段 3 にキーが無い）。変えたら列の束の形（click_routes.fanout）が成り立つか
- JLC が Economic で、~~縁からはみ出す電源スイッチと、~~背 4.0 の電池クリップを載せる（**注文画面で確かめる**）。電源スイッチは 2026-10-04 に縁の内側へ動かした
- 底のシートが 0.5（買う物で変わる。厚さとねじの頭の出が変わるだけ）

## 覆す前に読むこと

tests/test_cckb_click_pcb.py・test_cckb_click_board.py・test_cckb_click_case.py の、壊すと落ちる検査。build/cckb-click/main_sections.png・main_top.png・pcb_F.png・pcb_B.png。

## まだ決めていないこと

| 項目 | 決められない理由 |
|---|---|
| 底のシートの材料 | 利用者（買う物）。Alps の仕様書 D3 は「硫化ガス・酸化ガスを出す材料（ゴム・接着剤）と一緒に使わない」と書いている |
| 基板の表面処理（HASL か ENIG か） | 利用者（費用）。電池の −は裸の銅に当たる |
| 中の押さえを使うか | 本番の枠を刷って、真ん中の浮きを見てから |
| 入の向きの刻印 | 基板が届いてテスターで確かめてから（枠は刷り直せる） |
