ms0216/keyboard-foundry/projects/cckb-click/docs/decisions/2026-10-04-audit-1.md

# 1 回目の監査の直し: 電池の位置・載せないコンデンサのランド・予備のねじ穴・ねじ穴を 0.1 外へ・戻りの道

- **日付:** 2026-10-04
- **状態:** 決定（**直した板は、まだ独立に見直していない**。open-gaps #30）
- **決めた人:** Claude（監査の所見と裁定 `.superpowers/sdd/cckb-autonomy/audit-click-findings.md` に従った）。
  JLC への頼み方（Economic か Standard か・表面処理）は**利用者が決める**（docs/order-steps.md §2）

## 1. なぜ決める必要が生じたか

5 視点の独立した監査（HEAD 852342f・板 f44c5825…）で、致命 0・発注前に直す物が出た。基板は発注すると直せないので、
**直せない側の余裕を先に取る**向きで直した。

## 2. 事実はどうか（測った・読んだもの）

| 何 | 監査の時の板 | 直した板 | 何で測ったか |
|---|---|---|---|
| 止めに当てた電池の缶の縁から、表の銅まで | **0.00** | **0.72**（抜き差しの道は 0.50） | `tools/click_facts.py`（KiCad が読んだ板の銅と、電池の円の距離） |
| 電池の中心（クリップの原点から奥へ） | 0 と置いていた | **0.51** | 図面 MY-CP-0247（止めから口 15.10・板厚 0.25）と足跡（止めの外面 8.76）: 8.76 − 0.25 − 8.0 |
| 試験用のランドのシルクの輪 → マスクの開口 | 0.124（輪の半径 0.7） | 0.2 以上（半径 0.85・太さ 0.15） | 同上（シルクの図形 207 個を全部） |
| 外周のねじの下穴のまわりの肉（いちばん薄い所） | 0.49（斜め内向き）・真内向き 0.6 | **0.70**（奥・手前の壁と 1u の脇の 19 本）・0.49（幅の広いキーの脇の 3 本） | 作った枠の立体を下穴のまわりで切って、10° おきに測った |
| C_U2 の GND → U2 の GND（8 番）の、GND の銅の上の道のり | 31.6 mm（U1 は 23.7） | 22.3 mm（U1 は 19.7） | tests の `gnd_return`（両面のベタ・線・ビアを 0.25 mm の升で） |
| 同じく OE（13 番）まで | U2 39.1・U1 13.4 | U2 11.5・U1 11.5 | 同上 |
| 表の GND で、ビアから銅の上でいちばん遠い所（595 のいるキーの中） | 17.2 mm | 13.3 mm（板の全部が 15 以内） | tests の `gnd_far` |
| VBAT_SENSE の裏の縦線と行 0 の縦線の間 | 0.76 mm を 23 mm 並走 | 1.8 mm | 板の線の座標 |
| DRC | 違反 0・未配線 0・警告 0 | 違反 0・未配線 0・警告 0（下限をビア φ0.6・穴 0.3 に上げた上で） | kicad-cli |

## 3. 効く条件と、決めたこと

### 3-1. 電池の座る位置（E 重要 1）

| # | 条件 | 実データ | 確かめ方 |
|---|---|---|---|
| 1 | 電池の缶（＋）が、擦れてマスクの剥げた GND に触れない | 止めに当てた位置で 0.72・道で 0.50 | 板の銅を測る検査（電池を 1.0 奥へ置くと落ちる） |
| 2 | 電池を指で出せる | 指の切り欠きを奥行き 4.0 → 4.5（電池の上面が 2.79 見える・真上に枠の無い面積 22.5 mm²。前は 2.8・23） | 枠の立体を点で数える |
| 3 | クリップの位置（基板の上・発注後は直せない）は動かさない | — | 配置の指紋 |

**決めたこと**: クリップは動かさない。電池の中心の想定を「原点」から「止めに当てた位置（0.51 奥）」に直し、表の銅を置かない範囲の奥の端を
「止めの外面 ＋ 1.0」にした（`spec.CELL_KEEPOUT_BACK`）。電池の手前の縁は枠の外面から 1.71（前は 1.2 と置いていた）。

捨てた案: クリップを 0.51 手前へ寄せて電池を元の想定の位置に戻す → クリップの口の縁が指の切り欠きを 0.51 塞ぐ。枠の切り欠きは刷り直せるので、そちらで合わせた。

### 3-2. 載せないコンデンサのランド 2 つ（A 重要 1・D 重要 1）

CR1632 で起動できるか（#32）がまだ分かっていない。だめだったとき、板に打てる手が無い。**ランドを置くだけなら害が無く、後からは足せない。**

| # | 条件 | C_BAT（VBAT_SW–GND） | C_3V3（V3V3–GND） |
|---|---|---|---|
| 1 | どの網に | 電源スイッチの後ろ・D_PWR の手前（**スイッチを切ると電池から外れる**） | D_PWR の後ろ（レール） |
| 2 | 載る部品 | 1206 と 0805 の両方（ランドは内端 ±0.45・外端 ±2.225・高さ 1.8） | 同じ |
| 3 | 部品の背 | **2.8 まで**（右の角の屋根の下。枠の下面 3.0） | **1.45 まで**（Z のキーのキャップの下。縁を押し切ったキャップと立体で重ねた。背 1.9 では当たる） |
| 4 | JLC | 実装しない（BOM・CPL に出ない）・はんだも載らない（ペーストの層が無い） | 同じ |
| 5 | はんだ付け | 手はんだ。GND の側はサーマル | 同じ |
| 6 | 配線 | 電源の長い線の縦の区間へ横に 2.7 mm | U1 のパスコンから裏を 13 mm |

- 置き場所: 表に置けて、背の高い部品が入るのは、枠の屋根の下（左右の角）だけ。左の角は XIAO とアンテナの禁止域で埋まっている。
  V3V3 は板の左にしか無いので、C_3V3 はキャップの下（背の低い 0805 か、薄い 1206）にした。
- **載せるかは利用者が #32 の結果で決める。**載せるのが正しいとは限らない（docs/knowledge/power.md: HHKB では 100 µF で 53 秒リセットできなかった）。
  品番は載せると決めたときに決める（背の上限を満たす物を `foundry.jlcpcb_lookup` で）。
- CCKB の O11（U2 の QH' を D9 へ戻す）は**足していない**（記録だけ。open-gaps O11）。

### 3-3. 予備のねじ穴（E 重要 3）

- **手前の継ぎ目の両側に 2 つ**（H28・H29。継ぎ目から ±6.5）。基板の穴・裏の頭の下の銅の禁止・枠の下穴と厚い壁まで作った。
  **既定では締めない**（継ぎ目が浮く・段が付くときに締める）。±6.5 は、壁を厚くする所（± 2.0）がスペースのキーのつば（穴の角から 3.5）に掛からないいちばん継ぎ目寄り。
- **左手前の角（XIAO のそば）には置けない。**測った理由:
  1. XIAO のいる範囲（x −144.4〜−122.7）は、XIAO の逃げが手前の壁を 1.135 まで・左の壁を 1.43 まで削っていて、下穴 φ1.8 が入らない
  2. その右（x −122.7〜−114.3）は、ねじの頭の下の銅の禁止（r 2.3）の奥の端が y −45.925 で、アンテナの禁止域の手前の端 −45.6 との間が 0.33。
     行 4 の裏の線（y −46.4）が通れなくなる
  3. 鉄のねじが、チップアンテナの中心から 7〜11 mm に来る（open-gaps P9 の電波は実機でしか分からない。金属を足さない）
  4. 左の壁は、左 Shift の空きランドとつばの間にもう 1 本ぶんの幅が無い（いまの H17 でいっぱい）
  いちばん近いねじは左 Alt の手前（H9・XIAO の右端から 18 mm）と左の壁の H17。

### 3-4. 外周のねじ穴を 0.1 外へ・壁を厚くする幅を広げる（E 重要 2）

| # | 条件 | 前 | いま | 限度 |
|---|---|---|---|---|
| 1 | 下穴の内側の肉（発注後は直せない: 基板の穴の位置で決まる） | 0.6（斜めは 0.49） | 0.7（斜めも 0.7 以上。壁を厚くする幅 ±1.2 → ±2.0） | — |
| 2 | 基板の穴の縁から基板の縁まで | 1.1 | **1.0** | foundry の下限 1.0（HHKB #53。JLC の外形の公差 ±0.2 でも 0.8 残る） |
| 3 | ねじの頭（φ4.0）の縁から基板の縁まで | 0.2 | 0.1 | 0 以上（頭が基板からはみ出さない） |
| 4 | 下穴の外側の肉 | 1.6 | 1.5 | 0.4 ノズルの外周 3 本 1.26 |

**決めたこと**: 0.1 だけ外へ（`SCREW_FROM_EDGE` 2.5 → 2.4）。これ以上は基板の縁の下限を割る。**良くなるのは 0.1（17%）だけ**で、効いたのは
壁を厚くする幅の方（斜めの 0.49 → 0.70）。幅の広いキーの脇の 3 本（H16・H17・H18）は、空きランドとつばに挟まれて幅を広げられず、0.49 のまま。
**樹脂に直に切るねじが割れないかは、刷って締めるまで分からない** → 発注の前に `coupon_screw` を刷って試す（open-gaps #33・docs/coupon-test.md）。

### 3-5. 電気の小さな直し（D 軽微 1〜4・C 軽微 1・5）

| 所見 | 直したこと |
|---|---|
| D 軽微 1（C_U2 の戻り 31 mm） | パスコンの GND から 595 の GND（8 番）までを、**GND の線で決まった形に**引いた（`spec.GND_RETURN`・click_routes.gnd_return_run: Q0 のビアの手前を回る・23.9 mm 以下）。**Q0 の裏の線が裏のベタを切る構造は残る**（ピンの並び: VCC 16 番と GND 8 番の間に Q0 15 番）。まっすぐ 11.1 mm に対して 20〜22 mm |
| （途中で捨てた形） | 先に「裏の線を通さない領域」で Freerouting を縛った。配線のたびに結果が変わり（同じ入力で 21〜32 mm）、広げると別の線が XIAO の下を 45 mm 回り込んだ。**ベタの形に頼るのをやめて線で引いた** |
| （595 の本体の下の表の帯） | Freerouting がここに線を通すと、帯が幅 0.5 の 2 本に割れた（ビアから 26.8 mm）。帯に表の線を通さない（`spec.IC_BAND`）・帯のビア 4 本を配線の前に打つ → 595 のいるキーの中も 15 mm 以内（open-gaps P4 の表の方を閉じた） |
| D 軽微 2（表の GND の指 16.8 mm） | 監査が名指しした点（−119.7, −27.35）は、配線し直したら線が通っていてビアを置けなかった。**指そのものが無くなった**（表のいちばん遠い所 13.3 mm）。検査 `gnd_far` が上限 15 で見張る |
| D 軽微 3（VBAT_SENSE） | 決まった形で引く（`spec.SENSE_RUN`）。行 0 の縦線から 1.8。コンデンサは足していない |
| D 軽微 4（アンテナの禁止域を手前の縁まで・任意） | **禁止域は広げない**（広げると行 4 の裏の線 y −46.4 が通れない）。禁止域の手前の端と行 4 の線の間に残っていた裏の GND の帯（幅 0.45・長さ 5・右の端だけで繋がる）は、ベタを塗らない領域（`ANT_FRONT_NO_FILL`）で消した。絵: build/cckb-click/audit/before_B_antenna.png・after_B_antenna.png |
| C 軽微 1（TP_VSW のシルク） | 輪を半径 0.85・太さ 0.15 に。**シルクの図形**（文字でない物）とマスクの開口の距離・太さを見る検査を足した |
| C 軽微 5（DRC の下限） | `spec.DRC_RULES`: ビア φ0.6・穴 0.3。機種は下限を上げられるが、JLC の下限より下げられない（foundry.pcb_rules） |
| （配線し直して見つけた物） | Freerouting が試験用のランドの中にビアを置いた → ランドのまわりにビアの禁止（`TP_VIA_KEEPOUT`）。C_3V3 への線を任せると左 Alt のキーを一周した → 決まった形で引く（`spec.V3V3_RUN`） |

## 4. 影響範囲（端から端まで）

- **基板 → 枠**: ねじ穴が 0.1 外へ → 枠の下穴・厚い壁・底のシートの穴が同じ座標から動く（click_layout を両方が読む）。予備の 2 本も同じ
- **基板 → 発注**: BOM 7 行・CPL 133 行は**変わらない**（足したのは載せない物だけ）。部品 189 個（＋ランド 2・穴 2）
- **基板 → ファーム**: 回路の網は CCKB と同じ（足したのは部品の載らない銅）。overlay の行・列・ADC は変わらない
- **枠 → 刷り方**: 枠 2 枚を刷り直した物でスライスし直した（docs/printing-guide.md）
- **foundry（核）**: `pcb_rules.sync_project_rules(tighten=…)`・`pcb.npth_too_close_to_edge`（丸め 1e-6）・`pinmap` の `cap_land`。HHKB の再現検査と CCKB の検査は緑

## 検討して捨てた案

| 案 | 捨てた理由 |
|---|---|
| ねじ穴を 0.3〜0.5 外へ（内の肉 0.9〜1.1） | 基板の縁までが 0.8〜0.6 になり foundry の下限 1.0 を割る。頭が基板からはみ出す |
| キー領域の端から枠の外形までを 3.0 → 3.5 にして壁ごと厚く | 外形・XIAO・電池・電源スイッチの位置が全部動く（監査の範囲を超える作り直し）。ねじの試し刷りの結果が悪ければ、このときに考える |
| U2 の列を Q1〜Q7 に寄せて Q0 の裏の線を無くす | ファームの列の番号が CCKB と変わる（同じシールドの形でなくなる）。U1 は 8 本使うので Q0 が残る |
| C_3V3 を左の角（アンテナの右）に置いて背の高い部品も載るように | 金属がアンテナの禁止域のすぐ外に来る |
| 595 のまわりを全部手で引く（Freerouting をやめる） | 効果は大きいが監査の範囲を超える。いまは「通さない領域」で Freerouting を縛った（open-gaps P4 に残した） |

## この決定が乗っている前提（**動いたら読み直す**）

- 電池クリップは MY-1632-03-R（止めの外面 8.76・板厚 0.25）。品番を変えたら電池の座る位置が変わる
- 外周の壁の厚さ 3.0・下穴 φ1.8・M2×4。ねじの試し刷りの結果で下穴の径や壁を変えたら、3-4 の数字が変わる
- foundry の「穴の縁から基板の縁まで 1.0 以上」
- 595 の向き（270°）と置き場所（左 Shift の中）。動かしたら `GND_RETURN`・`IC_BAND` は引き直す

## まだ決めていないこと

| 項目 | 決められない理由 |
|---|---|
| C_BAT・C_3V3 に部品を載せるか・品番 | #32（CR1632 の起動の試験）の結果 |
| 予備のねじ 2 本を締めるか | 組んでみないと分からない |
| JLC の Economic か Standard か・電源スイッチを手はんだにするか・表面処理 | 利用者の判断（費用・手間）。docs/order-steps.md §2 |
| 下穴の径・壁の厚さ | ねじの試し刷り（open-gaps #33） |
