ms0216/keyboard-foundry/projects/cckb-click/docs/decisions/2026-10-03-license.md

# ライセンス: 形は CC BY-NC 4.0・名前は借りない

- **日付:** 2026-10-03
- **状態:** 決定
- **決めた人:** 利用者

## 1. なぜ決める必要が生じたか

キャップと枠の形は、Salicylic_acid3 さんの公開データ（ACC_Keycaps・Case_Data）を測って作る。このリポジトリは公開なので、
どの条件で載せるかを先に決めないと載せられない。

## 2. 事実はどうか

| データ | ライセンス | 読んだ物 |
|---|---|---|
| ACC_Keycaps（キャップの STEP） | CC BY-NC 4.0 | リポジトリの LICENSE |
| Case_Data（ケースの STEP） | CC BY-NC 4.0 | LICENSE.txt・README「非商用の範囲で」 |
| PCB_Data・KiCAD_FootPrint | MIT | Licence.txt |

CC BY-NC 4.0 は、改変した物の公開を「出どころの表示・改変したことの表示・非営利」の条件で許す（第 2 条・第 3 条(a)）。

## 3. 効く条件

| # | 条件 | 実データ | 何で確かめたか |
|---|---|---|---|
| 1 | 元のライセンスが二次的な物の公開を許すか | 許す（BY-NC。ND ではない） | 外（各リポジトリの LICENSE） |
| 2 | 非営利か | 利用者の自作・販売しない | 利用者 |
| 3 | 出どころと変えた所を示しているか | projects/cckb-click/LICENSE | 検査（test_the_license_notice_…） |
| 4 | 元の製品名を自分の部品に付けていないか | STL・小片の名前に無い | 検査（test_no_part_is_named_after_…） |
| 5 | 元の STEP をリポジトリに入れていないか | 入れていない（測った数だけを spec.py に） | `git ls-files` に .step が無い |

## 4. 影響範囲

形を作るコード（click_parts.py ほか）→ 生成物（STL・絵・.blend）→ それを刷った物 → 将来この形を核（foundry/）へ抜き出す場合。
**核へ抜き出すと、核のその部分も CC BY-NC 4.0 になる**ので、抜き出す前にこの記録を読み直す。

## 5. 決めたこと

- キャップと枠の形（コード・生成物）は **CC BY-NC 4.0** で公開し、Salicylic_acid3 さんの名前・元のリポジトリ・変えた所を
  projects/cckb-click/LICENSE に書く
- 「ACC」「Acid Caps」「ClickBoard」を自分たちの部品の名前に使わない（出どころの表示と記録の中の言及だけ）
- 公開 STEP はリポジトリに入れない。形は測った寸法からコードで作る
- PCB_Data・KiCAD_FootPrint から借りる物（基板の段）は MIT の表示を残す

## この決定が乗っている前提

- 非営利（販売しない）。販売するなら元の作者の許諾が要る
- 元のリポジトリのライセンスが変わっていない（2026-10-03 に読んだ）
