ms0216/keyboard-foundry/projects/cckb/docs/decisions/2026-09-24-interface.md

# 基板・プレート・ケースの境界を凍結する（角・ネジ・電源スイッチ・スタビの逃げ・継ぎ目・高さ）

- **日付:** 2026-09-24
- **状態:** 決定（利用者に確認したいこと 3 件は仮の既定で進めた。末尾）。**2026-09-24 利用者の決定**: 1（ケースの形）はトレイ＋ふたのまま・3（厚さ）は床を 1.2 にして 13.8（§2-5 を書き換えた）
- **決めた人:** Claude（利用者の不在中、自走の段階 1。利用者の指示「発注できる状態まで」のもとで）

## 結論（先に）

| 何 | 決めたこと | 図 |
|---|---|---|
| ケースの形 | **トレイ（底＋外壁）に、はんだ付けした基板＋プレートを上から落とし、左右の角に「ふた」を載せる。**ネジは全部下から（M2×6 皿、相手は基板の上面に置いたナット） | `build/cckb/interface_plan.png` |
| 外形 | **289.95 × 99.45mm**（目標 約 292×100）。壁 1.6・キャップと壁の隙間 1.025（→ 2026-09-24 の監査の直し R5 で壁 1.3・隙間 1.325。外面は同じ・`spec.CASE_WALL`） | 同上 |
| 厚さ | 机からキャップ上面まで **13.8mm**（目標 約 12 を 1.8 超える。内訳は §2-5。**前は 14.2**: 2026-09-24 利用者の決定で床を 1.6 → 1.2、滑り止めの所だけ 1.6 の島） | `build/cckb/interface_zstack.png` |
| 基板の厚さ（O3） | **1.6mm**。1.2 にしても全体は薄くならない（効いているのはスイッチの足）うえ、たわみが 2.4 倍 | 同上 |
| 左の角 | XIAO を表に**平らに**はんだ付け（キャステレーション）。USB-C の口は外面から 0.3 内側。アンテナの下の銅を抜く | `build/cckb/interface_corner_left.png` |
| 右の角 | 電池ホルダ **BS-16-B4AK003**（C964732）＋CR1632。ふたは 1 本のネジで上から留める | `build/cckb/interface_corner_right.png` |
| 電源スイッチ | **MK-12C02-G025**（G-Switch・C778186）を**裏面**（JLC 実装）の右端に。つまみは右の側面から操作 〔2026-09-24 に SS-12D00G3（表・右のふたの穴から爪で）へ置き換え・decisions/2026-09-24-power-switch.md〕 | 同上（断面 C） |
| スタビの逃げ（O2） | 基板を Keebio の輪郭＋片側 0.5 で切り抜く。ハウジングの下端は床の上 1.3 | `interface_zstack.png` |
| 取付（O4） | **10 か所**（うち 1 つは左のふた）。5 条件を生成した基板と突き合わせて全部満たす。支えの柱 38 本 | `interface_plan.png` |
| 分割（D12・D13） | プレートは段ごとにキーの境目で 2 つ（152.7 / 147.9）。トレイは継ぎ目の案 C（奥 9.53・手前 4.76）で 2 つ（154.5 / 140.2）。ふた 2 つ。**全部 168.4 以下** | `build/cckb/interface_seams.png` |

値は `projects/cckb/spec.py`、形は `projects/cckb/interface.py`、検査は
`tests/test_cckb_interface.py`（各検査の隣に「故意に壊すと落ちる」検査）。図は
`.venv/bin/python3 projects/cckb/tools/draw_interface.py` が出す。

## 1. なぜ決める必要が生じたか

基板は発注すると直せない。基板・プレート・ケースが共有する寸法（角の部品の位置、ネジ穴、
スタビの逃げ穴、外形、電源スイッチ、アンテナの禁止域）を先に固め、基板の段（次）と
ケースの段（後）が手戻り無しに進めるようにする。open-gaps の #2（角の断面）と
O2〜O6 を閉じる。

## 2. 事実はどうか（読んだもの・測ったもの）

### 2-1. 部品（データシート。PDF は再配布の許しが明らかでないので保存せず、URL と読んだ値を書く）

**電池ホルダ BS-16-B4AK003（MYOUNG）** — 図面 MY-CP-0085（2020-04-01）
<https://wmsc.lcsc.com/wmsc/upload/file/pdf/v2/lcsc/2012181808_MYOUNG-BS-16-B4AK003_C964732.pdf>・
製品写真 <https://assets.lcsc.com/images/lcsc/900x900/20230131_MYOUNG-BS-16-B4AK003_C964732_front.jpg>

| | 値 |
|---|---|
| 外形 | 全長 27.0（端子込み）・本体 23.70・幅 16.00・**高さ 5.50**・電池の座 φ16.10 |
| ランド | 3.75 × 4.5 を 2 つ、外外 28.0（中心間 24.25） |
| 極性 | 端子（＋）は片端の**上から押さえるクリップ**、端子（−）は反対の端から出て**座の底のばね**。成形の「＋」「−」の刻印が本体の角にある |
| 出し入れ | 上から。＋のクリップの下へ電池の縁を斜めに差し込み、反対側を押し下げる。座は長辺の中央が開いていて、電池の縁が外に出る（φ16.10 > 幅 16.00）。取り出しはクリップと反対の縁を爪で起こす |
| 材質・定格 | LCP・りん青銅 Sn めっき・接触抵抗 30mΩ 以下・−40〜85℃・1.34g |
| JLC（2026-09-23 API） | C964732・Extended・在庫 1,688・$0.2278 |

比べた候補: **GT-CR1632-1Au**（G-Switch・C2829975・在庫 2,207・$0.40）は全長 28.7・高さ 5.4・
ランド中心間 26（<https://wmsc.lcsc.com/wmsc/upload/file/pdf/v2/lcsc/2208171800_G-Switch-GT-CR1632-1Au_C2829975.pdf>）。
品名は Au だが図面の注記は「NICKEL PLATE」で食い違う。**MY-1632-03**（C2902337）は高さ 4.0 と
1.5 低いが、− 極が基板のパッド（電池の下）で、HASL の凹凸と金めっきが要る。
**QJ BS-1632-1**（C969910）は BS-16 と同形（全長 27.3・高さ 5.5）。
→ **BS-16-B4AK003 に決めた**: 国内（eleshop ¥220）と JLC で同じ品番が買え（設計書 §3）、
全長が最短で角の横に余裕が残り、高さ 5.5 は GT と 0.1 しか違わない。MY-1632-03 の −1.5mm は
魅力だが、縁（リム）の高さは XIAO の USB との兼ね合いで効き方が小さく（§2-5）、基板パッドが
接点になる形は接触の信頼性を基板の仕上げに預けるので採らない。

> **2026-09-24 置き換え**: 電源スイッチは利用者の決定で秋月の SS-12D00G3（表・レバーが上・右のふたの穴から）に替えた。
> 下の表と「右の側面の窪み」は当時の記録。いまの形は [2026-09-24-power-switch.md](2026-09-24-power-switch.md)。

**電源スイッチ**（側面操作・表面実装・JLC 在庫）。条件を先に並べた:
高さ（裏に付けるなら下の空き 1.8 − 余裕 0.3 = 1.5 以下）・つまみの長さ（本体の縁から壁の逃げ 0.2＋
壁 1.6 を抜けて外面に届くこと）・ストローク・在庫・ランドが縁に置けるか・どちらの面か。

| 品番（LCSC） | 高さ | つまみ（本体の縁から） | ストローク | 在庫（09-23） | 判定 |
|---|---|---|---|---|---|
| **MK-12C02-G025**（C778186） | 1.4±0.05 | **2.5±0.1** | 1.5 | 3,260 | **採用**。耳のパッドを縁から 0.3 内に置いてつまみの先が外面と面一（+0.15） |
| MK-12C02-G020（C963206） | 1.4 | 2.0 | 1.5 | 24,386 | 先が外面の 0.35 内側。窪み 1.0 でも爪のかかりが 0.65 しかない。**予備**（在庫が多い） |
| MSK12C02（C431540） | 1.4±0.1 | 1.45 | 1.6 | 167,314 | 先が外面の 0.9 内側で届かない |
| K3-1296S-E1（C128955） | 1.4±0.2 | 図に無い（L±0.2） | 1.5 | 3,108 | 高さの公差が大きく 1.6 まであり得る・つまみの長さが不明 |
| PCM12SMTR（C&K・C221841） | 1.4 | 1.5 | 1.5 | 1,179 | 届かない・$1.05 |

出典: <https://wmsc.lcsc.com/wmsc/upload/file/pdf/v2/lcsc/2304140030_G-Switch-MK-12C02-G025_C778186.pdf>・
汎用図 <https://wmsc.lcsc.com/wmsc/upload/file/pdf/v2/lcsc/2012062037_G-Switch-MK-12C02-G020_C963206.pdf>・
<https://wmsc.lcsc.com/wmsc/upload/file/pdf/v2/lcsc/2304140030_SHOU-HAN-MSK12C02_C431540.pdf>・
<https://wmsc.lcsc.com/wmsc/upload/file/pdf/v2/lcsc/2108131530_Korean-Hroparts-Elec-K3-1296S-E1_C128955.pdf>・
<https://wmsc.lcsc.com/wmsc/upload/file/pdf/v2/lcsc/1912111437_C-K-PCM12SMTR_C221841.pdf>。
**裏面（JLC が実装）**にする理由: 設計書 D8（表は XIAO とホルダだけ・利用者の手はんだ）と、
高さ 1.45 が下の空き 1.8 に 0.35 残して入ること。定格 0.3A/5V（負荷は mA 級）。

**XIAO nRF52840** — Seeed 公式 STEP（`lib/xiao.3dshapes`）を build123d で測った（検査
`test_the_xiao_numbers_are_the_official_step` が毎回測り直す）: 基板 20.95 × 17.78・厚さ 1.25・
USB シェルの上面まで 4.47・シェル 8.94 × 3.2 × 7.3 が基板の端から 1.53 出る・シェルの中心は
下面から 2.87・アンテナのチップ 1.6 × 3.2 は USB と反対の端から 0.27〜1.87、幅方向は中心から
D0〜D6 の列の側へ 0.21〜3.41（フットプリントの 3D の変換で向きを解いた）。HHKB のノギスの
実測 21×18×3・USB 込み 4.5 と一致。

**Kailh Choc V1（CPG135001D01-16）** <https://raw.githubusercontent.com/keyboardio/keyswitch_documentation/master/datasheets/Kailh/CPG135001D01-16.pdf>:
基板の上面からプレートの上面まで 2.20・ハウジングの上面 5.00・ステムの上面 8.00（ハウジング上 3.00）・
足 3.00（公差 L≦5 の欄 ±0.10）。**BAT46W**（CJ データシート <https://wmsc.lcsc.com/wmsc/upload/file/pdf/v2/lcsc/1810251820_Jiangsu-Changjing-Electronics-Technology-Co---Ltd--BAT46W_C54110.pdf>）
の SOD-123 は高さ最大 1.25。

### 2-2. 取付位置の探索（生成した基板の実物から）

`tools/kb cckb pcb` で作った基板を KiCad の Python で世界座標に解き（`projects/cckb/tools/board_geometry.py`・
パッド 434・部品 124）、0.5mm 刻みで 5 条件（下）を**同時に**見た（`projects/cckb/tools/find_mounts.py`）。
置ける点は 2,163、54 区画。**1u のキーが並ぶ所には 1 つも無い**（スイッチの間の桟 5.25 に、ナットの
六角の穴 4.2＋肉 1.2×2 が入らない）。置けるのは 1.5u 以上のキーの端と、角だけ。

探索の途中で自分の道具の誤りを 2 つ見つけて直した（検査を先に疑った）:
- 輪郭を広げる関数の符号が逆で**縮めていた**（スタビの逃げを 1mm 小さく見ていた）→
  `test_poly_offset_matches_build123d` で build123d と突き合わせる
- 高速化で絞ったパッドから配線の通り道を作り、**通り道が欠けて 5 か所を見逃した** → 通り道は基板全体から作る

### 2-3. 5 条件（interface.mount_problems）

1. 縁: 穴の縁から外形まで 1.0 以上
2. キーとプレートの開口: ナットの穴（二面幅 4.2 の外接円）のまわりに肉 1.2 を、スイッチ・スタビの開口・
   プレートの外形・プレートの継ぎ目から残す。角（プレートが無い所）は左のふたの 1 本だけ
3. 部品: 上はナット（外接円 2.31）、下はトレイのボス（φ5.6）が、パッド・足・穴・スタビの逃げ穴・
   角の部品（XIAO＋パッドの張り出し・ホルダ・電池・電源スイッチ・ふたの柱）から 0.3 以上
4. コートヤード: 穴のコートヤード（r 2.45）と表のコートヤード、ボスと裏のコートヤードが重ならない
5. 配線の通り道（設計書 §12）: 行（裏の横・ダイオードの ROW 側のパッドを結ぶ線）と列（表の縦・
   段の境目の帯 ±1.0 で横に渡る）から、穴の縁＋0.3＋線幅の半分

### 2-4. たわみ（O3）

柱と取付の配置で、キーの中心から最寄りの支えまで最大 d = 21.5mm。両端支持の梁（幅 19.05・
スパン 2d = 42.9・中央集中荷重）で δ = F L³ / (48 E I)、I = b t³ / 12、E = 18.6 GPa（FR4 の保守側）:

| F | t = 1.6（I = 6.50） | t = 1.2（I = 2.74） |
|---|---|---|
| 3 N（強い打鍵） | 0.041 mm | 0.097 mm |
| 10 N（手のひら） | 0.136 mm | 0.322 mm |

足の先の最悪の余裕（基板 −10%・足 +0.1 で床まで 0.14）に対し、1.6 は 10N でも収まり、1.2 は超える。
全体の厚さは基板の厚さで変わらない（足は基板の**上面**から 3.0 出るので、薄い基板ほど下の空きが要る）。
→ **1.6**。代償は重さ +約 21g（289 × 99 × 0.4mm × 1.85g/cm³）。検査 `test_the_pcb_thickness_is_stiff_enough`。

### 2-5. 高さの積み上げ（机 = 0）

**2026-09-24 に書き換えた**（利用者の決定・O10）。前の表（床 1.6・キャップ上面 14.2）は §2-5-2 に残した。

| 高さ | 何 | 根拠 |
|---|---|---|
| 0〜1.2 | 床 1.2（0.4×3）。**四隅の滑り止めの所だけ上面 1.6 の島**にして、その下から 0.4 のくぼみ（残り 1.2） | O6・O10 |
| 0.5〜1.7 | 下からの皿ネジの頭（机から 0.5 沈む）。頭の座は床より上に来るが、取付のボス φ5.6（床から基板の下面まで詰まった柱）の中 | `interface.z` の screw_head = ナットの上面＋0.3−6 |
| 1.2〜3.0 | 下の空き 1.8 | 足の最悪 1.66（3.10 − 1.44）＋0.14。ダイオード 1.25・595 1.2・電源スイッチ 1.45（前の裏の電源スイッチ。いまは表で、裏に出るのは切った足〔基板の下面から 1.0・`spec.PSW_PIN_TRIM`〕） |
| 3.0〜4.6 | 基板 1.6 | O3 |
| 5.6〜6.8 | プレート 1.2（基板の上 1.0 空く） | Choc 規格 |
| 9.6 / 12.6 | スイッチのハウジング上面 / ステムの上面 | Kailh 図面 |
| 11.6 | 縁（トレイの壁・角のふたの上面）= 基板＋7.0 | ホルダ 5.5＋隙 0.3＋ふた 1.2 |
| 13.8 | キャップ上面（[暫定] ステムの上 1.2） | 自分で刷る（D14） |

目標の 12 に対し 13.8。超えた 1.8 の内訳: 床 1.2＋下の空き 1.8（スイッチの足）＋キャップ 1.2 − 目標の余裕。
**足は切りそろえない**（利用者の決定: 手間が大きい。切れば −0.25）。

基板より上はすべて 0.4 下がっただけで、基板・プレート・ネジ・インサート・ナットの互いの関係は変わらない
（**板は触っていない**: `cckb_main.kicad_pcb` の sha256 05c75c25…9d20 と `board_geometry.json` は前と同じ）。
床に乗っていた物の追いかけ:

| 何 | 前 | いま | どう追いかけたか |
|---|---|---|---|
| 柱・取付のボス | 床 1.6 → 基板の下面 3.4 | 1.2 → 3.0（長さ 1.8 のまま） | `floor_top`・`pcb_bottom` から |
| 右のふたの柱 | 1.6 → 10.8 − 2.0 | 1.2 → 10.4 − 2.0 | 同上 |
| 下からのネジ（M2×6） | 頭 0.9・先 6.9（ナットの上面 6.6 の 0.3 上・プレート上面 7.2 の 0.3 下） | 頭 0.5・先 6.5（6.2 の 0.3 上・6.8 の 0.3 下） | **沈めを直に書くのをやめ**、先の出（`SCREW_PAST_NUT` 0.3）から導く。沈め 0.9 のままだと先 6.9 がプレートの上面 6.8 を越えた |
| ネジのかかり | ナット 1.6 全部・H3 のインサート 1.9・右のふた 2.8 | 同じ | 3 山（1.2）以上を `retention_problems` が見る |
| 皿の頭（ISO 7046 / DIN 965 / JIS B 1111 の M2 皿の頭の高さ 1.2） | 座 0.9〜2.1 | 座 0.5〜1.7。**床 1.2 より上へ 0.5 出るが、ボス φ5.6 の中**（座の円錐の z 1.2 での径 3.15 → ボスの肉 1.2）。頭の上に 1.3 残る（検査は 1.2 以上） | 島は要らない。断面 `section_mount_h0.png` で見た |
| スタビの下端（O2） | 2.9（床の上 1.3） | 2.5（床の上 1.3） | 変わらない |
| 電源スイッチの指の窪み | 1.2〜3.6 | 1.2〜3.2（上端はひれの下端に揃えて**導く**。前は直書きで、床を下げるとひれを 0.4 削った） | — **電源スイッチの置き換えで窪みごと無くなった**（2026-09-24） |
| 滑り止め | 四隅・外面から 3.0・16 × 10 | **島の上面 1.6 が足の先の最悪 1.34・電源スイッチの下面 1.55（前の裏の電源スイッチ）より高い**ので、島を裏に出る物の下に置けない。前の四隅は奥の 2 つが Esc / BS の足の下、右手前が電源スイッチの下（板の形で数えた）。奥 2 つは最上段と 2 段目の間の帯へ（y 31.4）、右手前は左へ 4.875（前の電源スイッチのコートヤードから島まで 0.53。置き換えの後は、表の電源スイッチの切った足から島まで 2.9・case_spec.py の ANTISLIP_AT の注記）、左手前は前と同じ。帯の高さで 16 × 8 に | `case_spec.ANTISLIP_AT`。隙 0.5 以上を `assembly.island_problems`（板の形）、当たらないことを組み立ての干渉が見る。前の位置に戻すと両方落ちる |

#### 2-5-1. 床のたわみ（1.6 と 1.2）

力の流れ: 打鍵 → 基板 → 柱 38・ボス 10・右のふたの柱 → 床 → 滑り止め（机）。床の下面は机から 0.1 浮いている
（シート 0.5 がくぼみ 0.4 から出る分）。

見積もり（基板の O3 と同じ梁）: 床の上の点から最寄りの柱・ボス・壁までの距離の最大 **d = 22.4mm**
（(−117.7, −9.4)。0.5mm の格子で数えた）。両端支持の梁、スパン L = 2d = 44.8、幅 b = 19.05（1u）、
PLA の E = 3,500MPa、中央に集中荷重 F。δ = F·L³ / (48·E·I)、I = b·t³/12、L³ = 89,800。

| | t = 1.6（I = 6.50 mm⁴） | t = 1.2（I = 2.74 mm⁴） |
|---|---|---|
| ばね k = 48·E·I / L³ | 12.2 N/mm | 5.1 N/mm |
| 3 N（強い打鍵） | 0.25 mm | 0.58 mm |
| 10 N（指で押す・手のひら） | 0.82 mm | 1.95 mm |

1.2 は 1.6 の (1.6/1.2)³ = **2.37 倍たわむ**。効くかどうか:

1. **机の上で打つ**: 床は 0.1 下がると机に着き、それ以上は机が受ける。机に着く力は 1.6 で 1.2N、1.2 で 0.5N
   （Choc の押下圧 約 0.5N）。どちらもキーの沈みの増え方は 0.1 以下で、ストローク 3.0 に対して感じない。**効かない**
2. **手で持つ・鞄の中で下から押される**: 床が上へたわみ、スイッチの足の先（床の上 最悪 0.14・公称 0.40）や
   裏の部品（0.35）に当たる。当たる力は 1.6 で 1.7N（最悪）／4.9N（公称）、1.2 で **0.7N／2.0N**。当たっても
   床は PLA（絶縁）で、足ははんだ付けで何本もの足と柱に力が分かれるので壊れはしないが、**1.2 は指で底を押すと
   柔らかく感じる**。10N ではどちらも当たる（1.6 でも防げていなかった）
3. 梁の見積もりは床を 1u 幅の帯として両端で支えた物で、板としての広がり（2 方向で支える）と壁の剛さを
   無視しているので実際より柔らかく出る。点で支えることは逆に柔らかくする。**大きさの見当**として使う

→ 機能には効かない（打鍵は机が受け、下から押されて足に当たっても壊れない）。代償は「底を指で押すと
たわむのが分かる」こと。刷ったトレイで確かめる（open-gaps P10 と一緒に）。

#### 2-5-2. 前の表（2026-09-24 の最初の決定・**上の表で置き換えた**）

| 高さ | 何 | 根拠 |
|---|---|---|
| 0〜1.6 | 床（四隅は 0.4 のくぼみに滑り止め。残り 1.2） | O6 |
| 1.6〜3.4 | 下の空き 1.8 | 足の最悪 1.66（3.10 − 1.44）＋0.14。ダイオード 1.25・595 1.2・電源スイッチ 1.45 |
| 3.4〜5.0 | 基板 1.6 | O3 |
| 6.0〜7.2 | プレート 1.2（基板の上 1.0 空く） | Choc 規格 |
| 10.0 / 13.0 | スイッチのハウジング上面 / ステムの上面 | Kailh 図面 |
| 12.0 | 縁（トレイの壁・角のふたの上面）= 基板＋7.0 | ホルダ 5.5＋隙 0.3＋ふた 1.2 |
| 14.2 | キャップ上面（[暫定] ステムの上 1.2） | 自分で刷る（D14） |

当時の文: 目標の 12 に対し 14.2。**縮める手段**（利用者の判断）: 足を切りそろえる（−0.25）・床のくぼみを
四隅のパッドだけに（床 1.2 にして −0.4、くぼみの所だけ 1.6 の島）。→ 後者を採った（上）。

### 2-6. スタビ（O2）

Keebio の輪郭（ハウジング 6.30×6.60＋奥行 0.25・切り欠き 0.4）を片側 0.5 広げて基板を切り抜く。
ハウジング（製造図の最大公差 6.32 × 6.60・突起 3.28）との隙は最小 0.5（外形公差 ±0.2 を引いて 0.3）。
ハウジングの高さ 4.30 で、上面がプレートの上面より下がることはない（上からはめて爪で留まる）ので、
下端は最も低くて 7.2 − 4.3 = **2.9**（基板の下面 3.4 の 0.5 下・床の上面 1.6 の 1.3 上。**床 1.2 にした後は** 6.8 − 4.3 = 2.5・床の上 1.3 で同じ）。
二次資料の「プレートの下に 2.5〜3.5 出る」の大きい方（プレートの下面から）でも 6.0 − 3.5 = 2.5 で
床の 0.9 上。**床に穴もくぼみも要らない**（厚くもしない）。実物ではめて確かめる（P1）。

## 3. 効く条件（候補を並べる前に）

| # | 条件 | 実データ | 何で確かめたか |
|---|---|---|---|
| 1 | 基板は発注後に直せない | — | 前提 |
| 2 | 印刷する部品は平面 168.4 角以内 | A1 mini の CLI 実効（HHKB 実測） | 外（HHKB の実測） |
| 3 | 表は XIAO とホルダだけ、JLC は裏だけ | D8 | 設計書 |
| 4 | 電源は側面から・ふたを開けずに | D9 | 設計書 |
| 5 | 電池はふたから替える・ふたの縁はキャップの隙間と外周に重ねる | D6 | 設計書 |
| 6 | 印刷部品は基板に留め、部品どうしの継ぎ目に力をかけない | D13 | 設計書 |
| 7 | USB-C に市販のケーブルが届く | 挿しきると金属が 1.0 見える | 外（HHKB 実機の実測） |
| 8 | アンテナの近くに金属・銅を置かない | 電池 5mm で RSSI 変化なし | 外（HHKB の実測） |
| 9 | ナット・ネジ・インサートは肉が要る | インサート外径 3.2 は薄いボスを割る | 外（HHKB の失敗） |
| 10 | 部品の寸法 | 上の表 | 外（データシート・公式 STEP） |
| 11 | 取付の 5 条件 | §2-3 | **生成した基板**（自分の生成物だが、宣言ではなく基板そのもの） |

## 4. 影響範囲（力と信号の流れに沿って）

- **打鍵の力**: キャップ → スイッチ → （はんだ）→ 基板 → 柱 38 本・取付のボス 9 → トレイの床 → 机。
  プレートはスイッチのはんだで基板に留まるだけで、力の通り道ではない
- **持ち上げる力**: トレイ → ネジ（下から）→ ナット（プレートの六角の穴で回り止め）→ 基板。
  トレイの左右はそれぞれ 4〜5 本のネジで基板に留まり、継ぎ目に力はかからない（D13）
- **電池の電流**: CR1632 → ホルダ（右の角・表）→ 電源スイッチ（右端・裏。→ 表の右の縁へ置き換え）→ 分圧・B5819W → XIAO の 3V3
  （左の角）。**〔注・2026-09-24〕D_PWR の既定はこの後 BAT46W（C54110）に替えた（decisions/2026-09-24-audit-fixes.md §S2・open-gaps O12）。経路は同じ**。右端から左端まで約 250mm を基板で引く（直流・mA 級）
- **電波**: アンテナ（左の角の +x の端）→ 銅の禁止域（XIAO の中へ 3.14・外へ 5.0・幅 ±6.0）→ 樹脂のふた。
  左のふたのネジ H3 はチップから 6.6（要件 5）
- **利用者の手**: USB-C（左の側面）・電源スイッチ（右の側面の窪み → 右のふたの穴から爪で。置き換え）・電池（右のふたをネジ 1 本で外す）・
  ネジ（全部底面から）
- **foundry の核**: `foundry/plate.py` に 2 つ足した（`MOUNT_POCKET_AF` があれば取付をナットの六角の穴に、
  `PLATE_SPLIT` があればプレートを左右に分ける）。どちらも無い機種（HHKB）は挙動が変わらない
  （`tests/test_regression_hhkb.py` で確認）
- **基板の生成**: 取付穴 10 個が増えた（`MOUNTS`）。DRC 違反 0・警告 silk_edge_clearance 2（以前は 17。外形が 0.3 広がった）

## 5. 決めたこと

### 5-1. ケースの形: トレイ＋角のふた（設計書 §5 の「上枠」から変えた）

設計書 §5 は「上枠が角を覆い、基板とプレートを下から入れ、底板で閉じる」だった。作図して、
**上枠の前後の長い辺を基板に留める場所が無い**と分かった: 上枠は外周にしか無く、キャップの
下へは降りられない。外周で基板に届くには、キャップの縁の外に柱（インサート φ3.2 ＋肉）を
立てる幅が要り、前後に 5〜6mm 深くなる（外形 約 105〜108mm）。角にしか留められない上枠は、
継ぎ目の端（中央）が 115〜145mm 先で浮く。

トレイ（底＋外壁を 1 つの部品に）なら、トレイは**キーの下のナット**で基板に何か所でも留められ、
壁と床が一体なので浮く端が無い。D6（ふたの縁をキャップの隙間と外周に重ねる）・D13（印刷部品を
それぞれ基板に留める）はそのまま満たす。代償は、上から見えるキャップ↔壁の隙間からプレートの
縁が見えること（隙間 1.025。→ R5 で 1.325）。**利用者に確認したいこと 1**。

> **✅ 2026-09-24 利用者が決めた: トレイ＋角のふた（案 A）のまま。**上枠には戻さない。
> 見た目（プレートの縁）を隠したくなったら、あとで**案 C**——トレイの壁の上に嵌める飾りの縁（基板には
> ネジで留めない。壁に被せて留める）——を足せる。縁は壁の上に載るだけなので**基板は変わらない**
> （取付穴も外形も使わない）。

### 5-2. 角

- **左**: XIAO を表に平らに（ピンヘッダは使わない。浮かせると 2.5mm 厚くなり、アンテナと地板の距離も変わる）。
  パッドは XIAO の外形から幅方向へ 0.6 出す（こて先用。前は基板の銅の限界、奥はプレートの開口の縁）。
  **XIAO はプレート・スイッチより先にはんだ付けする**（奥のパッドはプレートの下になる）。
  USB-C の口は外面から 0.3 内（HHKB と同じ）。壁は口の下までがトレイ、上はふたの舌（基板を上から
  落とすため）。ふたは奥の垂れ壁を持たない（XIAO 17.78 がセル 19.05 − 隙に入らない）。
  ふたは H3 のネジ 1 本で下から留める（ふたのボスのインサート。2026-09-24-case.md §4-1 で変更）
- **右**: ホルダの＋のパッドの外端を基板の縁から 0.675 内（→ 電源スイッチを右の縁に置くためにホルダを左へ 3.8 動かし 4.475 内・`spec.HOLDER_AT`）。ふたは天板 1.2＋キー側の垂れ壁 2 辺で、
  トレイから立つ柱（φ5.2・基板の穴 φ6.0 を通る・上端に M2 インサート）へ上から 1 本のネジで留める。
  柱はホルダの左、電池を起こす指の場所の外（ホルダから 3.0 以上）
- **電源スイッチ** 〔2026-09-24 に SS-12D00G3（表・右のふたの穴から爪で）へ置き換え・decisions/2026-09-24-power-switch.md〕。以下は当時の形: 裏の右端、ホルダのパッドから位置決めの穴を 0.6 離す y。トレイの右の壁に上に開いた
  切り欠き（ふたの舌が上を塞ぐ）と、外面に深さ 1.0 の指の窪み。つまみの先は外面と面一で、鞄の中で
  引っかからない

### 5-3. 取付 10・支え 38

`spec.MOUNTS`（H0〜H9）: Tab の左右・Ctrl の左・左のふた・左 Meta/左スペースの間・真ん中のスペースの左端・
右スペースの右端・右 Shift の左・Del の左・Enter の右。左のトレイに 5（＋ふた）、右のトレイに 4、
継ぎ目の両側に 1 つずつ（−22.7 と 48.3）。**奥の中央（x −100〜+100 の上 2 段）には置ける所が無い**（1u だけ）。
トレイは壁と床が一体の箱なので、奥の継ぎ目の角は近くのネジ（約 60mm）から支える。
`spec.SUPPORTS`: 段の境目の帯に 2u おきの柱（ネジ無し）。基板の次の段は、**裏の電子部品（595・電源）を
柱とボスに重ねない**（検査が見る）。左右の角の裏は電子部品の場所として柱を置いていない。

### 5-4. 分割

- プレート: 上の段から x = 9.525 / 0.0 / 4.7625 / −4.7625 / 4.7625（どれもキーの境目）。段の境目で横に渡る。
  左 152.7 × 95.85・右 147.9 × 95.85
- トレイ: **案 C（既定）** 奥の壁は最上段の 7|8 の隙間（9.525）、手前の壁は真ん中と右のスペースの隙間
  （4.7625）。どちらもキャップの隙間の線の上で、新しい線に見えない。床は y = 0 で段を付ける。
  左 154.5・右 140.2。案 A（x = 0 まっすぐ・145.0 / 145.0）、案 B（x = 4.76 まっすぐ・149.7 / 140.2）も図に描いた。
  **利用者に確認したいこと 2**
- ふた: 左 30.2 × 20.65・右 49.2 × 20.65（`interface.cover` から計算した値。前は左 30.7 × 20.7 と書いていた）

### 5-5. 基板の次の段に渡すもの（凍結）

1. 外形 286.35 × 95.85（キー領域＋0.3）・角 R1.0（foundry が出す）
2. 取付穴 10（foundry が出す）。**右のふたの柱の穴 φ6.0**（`LID_PILLAR_AT`）は pcb_extra で開ける
3. スタビの逃げ穴 8 つ（`interface.stab_reliefs()` の多角形を Edge.Cuts に）。**スタビのキー 4 つの
   ダイオードを動かす**（O7。いまの位置は逃げ穴にかかる。`test_the_stab_relief_clears_the_diodes` が
   strict xfail で見張り、直ると XPASS で落ちる）→ **O7 で決着**（`spec.DIODE_OVERRIDE`・中心穴の下へ横置き。xfail は外した）
4. XIAO: 表・中心 `XIAO_AT`・USB が −x。表面実装のフットプリント（パッドを幅方向に 0.6 出す・穴なし）。
   XIAO の下の表の銅はソルダーマスクで覆う（XIAO の裏のパッドと短絡させない）
   → 置き換わった: 手前の列 D0〜D6 はパッド内ビア φ0.8/0.3（open-gaps P6）、XIAO の下の表の銅は 0（監査の直し R3）
5. アンテナの禁止域（全層・塗った後のベタで確かめる）: `interface.antenna_keepout()`
6. ホルダ: 表・中心 `HOLDER_AT`・ランド 3.75 × 4.5 を中心間 24.25
7. 電源スイッチ 〔2026-09-24 に SS-12D00G3（表・右のふたの穴から爪で）へ置き換え・decisions/2026-09-24-power-switch.md〕。当時: 裏・中心 `PSW_AT`・つまみ +x。**LCSC の C778186 のフットプリントを取り込み、
   `PSW_*` の値（耳のパッド 0.25・端子 1.35・穴 φ0.9 間隔 3.0）と突き合わせる**
8. 柱・ボス（`SUPPORTS`・`MOUNTS` のまわり φ5.6）と角の部品に、裏の部品を重ねない

## 検討して捨てた案

| 案 | 捨てた理由 |
|---|---|
| 上枠＋底板（設計書 §5 の元の案） | 上枠の前後の辺を基板に留める場所が無い（§5-1） |
| XIAO をピンヘッダで浮かせる | +2.5mm 厚い。アンテナと地板の距離が変わる（rf-antenna.md） |
| 電源スイッチを表（角の中）に | JLC の実装が表に増える（D8）か手はんだの小さい SMD が増える。**→ 2026-09-24 に利用者の決定で採った**（スルーホールの SS-12D00G3 を手はんだ・power-switch.md） |
| 電源スイッチのつまみを外へ 0.7 出す（本体の縁を基板の縁に合わせる） | つまみ側の耳のパッドが外形に 0.25 はみ出す（図を読み直して判明） |
| 取付を 1u のキーの間に | 桟 5.25 にナットの穴と肉が入らない。穴のコートヤード r2.45 がスイッチのコートヤードに重なる |
| 基板 1.2 | 全体は薄くならず、たわみが 2.4 倍（§2-4） |
| 壁 2.4 | XIAO の基板が壁に 0.57 食い込む（USB の口を 1.0 以内に保つと） |
| 電池ホルダ MY-1632-03（高さ 4.0） | − 極が基板のパッド。接触を基板の仕上げに預ける |

## この決定が乗っている前提（動いたら読み直す）

- スイッチの足が基板の上面から 3.0 出る（Choc V1 直付け）。**足を切りそろえるなら §2-5 の下の空きを読み直す**
- ケースに基板を**上から**落とす（だから USB と電源スイッチの壁の切り欠きが上に開き、ふたの舌で塞ぐ。電源スイッチの切り欠きは置き換えで無くなった）
- ネジの相手は基板の上面のナット。**プレートの六角の穴はナットの回り止め**（プレートを外すとナットが回る）
  → **2026-09-26 にプレートを外した（`cckb-v2`・decisions/2026-09-26-plateless.md）**。この前提が動いたので読み直した: ナットは締める・緩めるときに上から押さえる（手順書 手順 8・open-gaps P15）。取付の位置と数（§5-3）はプレートに依らないので変えていない
- 左右の角のプレートの開口は外周まで開いている（`PLATE_OPENINGS`）
- XIAO のアンテナの位置は公式 STEP の向き（フットプリントの 3D 変換で解いた）。XIAO の版が変われば測り直す
- 1u のキーが並ぶ所に取付は置けない（1u の桟 5.25）。配列が変われば find_mounts を回し直す

## 覆す前に読むこと

- `tests/test_cckb_interface.py`（角・高さ・スタビ・分割・取付・支え。各々に故意に壊す検査）
- `projects/cckb/tools/find_mounts.py` の出力（置ける区画の一覧）
- 図: `build/cckb/interface_plan.png`・`interface_corner_left.png`・`interface_corner_right.png`・
  `interface_zstack.png`・`interface_seams.png`

## まだ決めていないこと

| 項目 | 決められない理由 |
|---|---|
| スタビの開口・逃げの嵌め合い（P1） | 実物が無い。試し刷りの小片ではめて押す |
| アンテナの禁止域の外の長さ 5.0・幅 ±6.0（[暫定]） | HHKB の実測を借りた。試作で RSSI を測る |
| ~~電源スイッチの指の窪み 1.0（[暫定]）~~ | 置き換えで無くなった。いまは右のふたの穴に爪がかかるか（open-gaps P4） |
| キャップの寸法（[暫定]） | キーキャップの段（D14） |
| トレイの継ぎ目の位置 | 利用者に確認したいこと 2 |

## 利用者に確認したいこと（仮の既定で進めた）

1. ~~**ケースを「トレイ＋角のふた」にした**~~ → **2026-09-24 利用者の決定: このまま（案 A）**。あとで壁に嵌める飾りの縁（案 C・基板は変わらない）を足せる。以下は当時の文: **ケースを「トレイ＋角のふた」にした**（設計書の「上枠＋底板」から変更。§5-1）。上から見ると
   キャップと壁の隙間（1.025。→ R5 で 1.325）の底にプレートの縁が見える。上枠の案に戻すなら前後が 5〜6mm 深くなる
2. **トレイの継ぎ目**: 案 C（奥 7|8 の隙間・手前はスペースの隙間）を既定にした。A（中央まっすぐ）・B（手前の隙間でまっすぐ）も
   `build/cckb/interface_seams.png` にある
3. ~~**厚さ 14.2mm**（目標 12）。縮めるなら「足を切りそろえる（−0.25）」「床を 1.2 にして滑り止めの所だけ厚く（−0.4）」~~
   → **2026-09-24 利用者の決定: 足は切らない（手間）。床を 1.2 にし、滑り止めの所だけ 1.6 の島 → 13.8**（§2-5・§2-5-1）
