ms0216/keyboard-foundry/projects/cckb/docs/decisions/2026-09-26-plateless.md

# スイッチのプレートを使わずに組む（戻せるように全部残す）

- **日付:** 2026-09-26
- **状態:** 決定（`cckb-v2` の枝。Choc V2 静音・ねじ留めのスタビ）
- **決めた人:** 利用者（2026-09-26）。実装と確かめは Claude

## 1. なぜ決める必要が生じたか

プレート（PLA 1.2・左右 2 枚＋スペースの枠 2）は、**Choc V1 のスタビがプレート留めだった**から要った（設計書 D11。
V1 の枝ではスタビがプレートの 1.2 の開口に掛かる）。V2 の枝ではスタビを遊舎工房のねじ留め（A050001-01-1）に決め、
**スタビは基板にねじで留まる**（決定記録 2026-09-25-choc-v2 §10-9）。プレートが担っていた「スタビを留める」役目が無くなり、
プレートのせいで残っていた重さ・欠け（スペースのキーの周りのプレートが外形まで抜ける・別に刷る枠・O15）だけが残った。

## 2. 事実はどうか（測った・読んだもの。出所を書く）

| 事実 | 出所（外 / 自分の生成物） |
|---|---|
| ねじ留めのスタビはプレートに掛からない。「プレートに引っかかるタイプではないので厚みは何ミリでも良い」「構造的にスイッチプレートレスでも使用できます」 | **外**: 販売者の記事 <https://salicylic-acid3.hatenablog.com/entry/chocv2-stab-guide>（2026-09-26 に本文を取得して引用を確かめた） |
| Choc V2 は基板に中心の突起 φ4.80（穴 φ5.05）・位置決めの突起（丸穴 φ2.1）・足 2 本で立つ。プレートの無い直付けで位置は基板の穴が決める | **外**: Kailh の図面 CPG135301D01・静音 CPG1353S01D0x（決定記録 2026-09-25-choc-v2 §10-1）。板の穴は発注する板 abcd20ff |
| プレートの重さ: 左 7.84・右 7.20・枠 0.29 cm³ = 15.33 cm³ ≒ **19.0g**（PLA 1.24）・刷る時間 1h15m ＋ 1h10m ＋ 3m ≒ **2h28m**。プレートの小片 3 つは 2.85 cm³（約 3.5g）・29 分 | 自分の生成物を**スライサー**（OrcaSlicer・A1 mini・Generic PLA・0.20mm Standard）に通した値（2026-09-26・`build/cckb/plate_optional/` を slice_check と同じ設定で） |
| キャップの底突きはどちらの形でもスイッチ（ステムの底）で止まる。押し切りからさらに 0.1 下げると、プレートの有無によらず最初に当たるのはスイッチ | 組み立てモデル（`assembly.py`・発注する板）で 0.1 刻みに下げて確かめた（2026-09-26） |
| プレートが無いと、キーの下の M2 ナット 9 個の**回り止めが無い**（プレートの六角の穴が回り止めだった・決定記録 2026-09-24-interface.md「前提」） | 自分の設計の記録。**プレートを外したときに初めて効く前提**で、端から端までたどって見つけた（§4） |
| ナットの中心からスイッチの胴まで 3.79〜6.62・つば（基板の上 2.2〜）まで 3.26〜6.09・スタビの箱まで 7.33 以上（ナットの外接円は半径 2.31） | 組み立てモデル（`assembly.nut_access`）。検査 `test_the_nuts_can_be_held_from_above_without_the_plate` |

## 3. 効く条件（候補を並べる前に全部書く）

| # | 条件 | 実データ | 何で確かめたか |
|---|---|---|---|
| 1 | スタビがプレート無しで留まる | 販売者「プレートレスでも使用できます」・スタビは基板にねじと爪（§10-9） | 外（販売者の記事・足跡の実測） |
| 2 | スイッチが基板の上で傾かず・ぐらつかない | はんだ 2 点＋中心の突起＋位置決めの突起。**打鍵感・傾きは評価していない** | **まだ**（実物でしか分からない → open-gaps P16） |
| 3 | 基板は変えない | 板 abcd20ff…（sha256 の前後を比べた） | 外（ファイルの sha256） |
| 4 | ケース・キャップの高さの関係が崩れない | 縁の高さは電池で決まる（`RIM_ABOVE_PCB`）・底突きはスイッチで決まる。プレートに依っていない | 組み立てモデルの干渉・押し切りの干渉（両方の形で 0） |
| 5 | 組み立て・保守ができる | ナットの回り止めが無くなる → 上から押さえる空き（§2） | 組み立てモデルで空きを測った。道具が入るかは実物（open-gaps P15） |
| 6 | 戻せる（プレートを刷ればいつでも戻る） | `spec.PLATE = True` で STL・組み立て・検査が全部戻る | 検査が毎回両方の形で組む（§5） |
| 7 | 重さ・刷る時間 | 本番 −19.0g・−2h28m（小片も −3.5g・−29 分） | スライサー |

## 4. 影響範囲（力と信号の流れに沿って）

- **打鍵の力**: キャップ → スイッチ →（はんだ）→ 基板 → 柱・ボス → 床。**プレートは前から力の通り道ではなかった**
  （決定記録 2026-09-24-interface.md §4）。変わるのは、スイッチの**傾き・横の揺れ**を止めるものがはんだ 2 点と
  基板の穴の突起だけになること（条件 2・P16）
- **持ち上げる力**: トレイ → ネジ（下から）→ ナット → 基板。**ナットの回り止め（プレートの六角の穴）が無くなる**。
  締める・緩めるときに上から押さえる（手順書 手順 8 の 4）。締めた後は座面の摩擦で止まる。
  外すときは、ナットの上のキャップ 7 個（Tab・左 Ctrl・左 Meta・スペースの真ん中・右のスペース・右 Shift・Del）を抜く（P15）
- **スタビ**: 基板にねじと爪で留まる。プレートの羽の開口との隙（V9）・静音の爪とプレート 1.2（V4・V10）は**プレートを戻すときだけ**
- **キャップ**: 底突きはスイッチ。プレートが無いぶんキャップの縁の下は空く（縁が下がっても当たるのはスイッチ）
- **ケース**: トレイ・ふたの形は変わらない（プレートは壁の内側に落とすだけで、ケースの形はプレートに依っていなかった）。
  上から見ると、キャップの隙間の底に**プレートの代わりに基板（緑）とナット**が見える（見た目だけ）
- **刷る物**: プレート 2 枚・枠・プレートの小片 3 つ（`coupon_switch`・`coupon_stab`・`coupon_nut`）を刷る物から外し、
  `build/cckb/plate_optional/` に出す（`case.py` と `tools/kb cckb plate` が毎回作る）
- **検査**: 組み立て（`assembly.Assembly(plate=...)`）の干渉・押し切り・経路・留め方を、**spec の形と逆の形の両方**で毎回回す
  （`tests/test_cckb_case.py` の `both`）。プレートの立体の検査（`tests/test_cckb.py`・`test_cckb_interface.py`）はそのまま残す
- **核（foundry/）**: `foundry.plate` に `uses_plate`・`plate_dir` を足した。`PLATE` を書いていない機種（HHKB）は挙動が変わらない
  （`tests/test_regression_hhkb.py`）

## 5. 決めたこと

1. **`spec.PLATE = False`**。プレートを使わずに組む
2. 戻せるように**全部残す**: プレートの形・妥協（羽・枠・欠け）・コード・検査。`PLATE = True` にすれば `case.py` が
   `build/cckb/` にプレート 2 枚と枠を出し、組み立てがプレートを置く。戻し方は手順書「プレートを戻すとき」
3. 発注の門の **#6（見本を基板の発注の前に）を取り下げた**。スタビの穴は販売者の足跡（実物の実測）、スイッチの穴は
   Kailh の推奨の足跡で決まっていて、見本は刷る物（キャップの受け口・小片）を合わせるためにしか要らない。見本は発注の後でよい
4. ナットは上から押さえて締める（手順書 手順 8）

**重さ・時間**（A1 mini・Generic PLA・0.20mm Standard。2026-09-26 に刷る物を出し直してスライス）:
本番 6 個（トレイ 2・ふた 2・キャップ 2 枚）**12h53m・81.6 cm³（約 101g）**、小片 3 個 1h22m・7.6 cm³（約 9g）。13/13 スライス成功。
プレートがあると本番は 15h21m・96.9 cm³（約 120g）で、**−19.0g・−2h28m**。

## 検討して捨てた案

| 案 | 捨てた理由 |
|---|---|
| プレートを消す（コードごと） | 利用者の指示: 戻せるように。傾き・打鍵感は未評価で、戻す可能性がある |
| プレートを残す | 役目（スタビを留める）が無くなり、重さ・欠け・枠・O15 だけが残る |
| ナットの回り止めに小さな六角の座を刷って足す | 合意の外（黙って足さない）。締めるときに押さえれば足りる見込み。締められなければ P15 で利用者と決める |

## この決定が乗っている前提（動いたら読み直す）

- スタビが**ねじ留め**（基板に留まる）であること。プレート留めのスタビ（V1・Kailh CPG1353G24D01 など）に替えるならプレートが要る
- スイッチを**直付け**すること（D3）。ホットスワップのソケットに替えるならスイッチを押さえるプレートが要る
- ナットを上から押さえられる空き（`nut_access`）。取付の位置を動かしたら検査が見る
- 打鍵感・傾きが許せること（P16。許せなければ戻す）

## 覆す前に読むこと

- 決定記録 2026-09-25-choc-v2 §10-6（プレートの欠けと枠）・§10-9（スタビの穴）
- 決定記録 2026-09-24-interface.md の「前提」（プレートの六角の穴はナットの回り止め）
- 販売者の記事（上の URL）

## まだ決めていないこと

| 項目 | 決められない理由 |
|---|---|
| **傾き・揺れ・打鍵感**（open-gaps P16・暫定） | 実物でしか分からない。組んでからキーの縁を押して比べる。刷ったプレートを 1 枚載せた場合と比べる |
| ナットを上から押さえる道具が入るか（open-gaps P15） | 空きはモデルで測った（胴まで 3.79 以上）。ピンセット・ナット回しの実物で |
