ms0216/keyboard-foundry/docs/templates/decision.md

# 決めたこと（1 行で）

- **日付:** YYYY-MM-DD
- **状態:** 決定 / 確定 / ❌撤回（撤回したら冒頭に「⚠️ 先に読むこと」を置き、本文は取り消し線で残す）
- **決めた人:**

## 1. なぜ決める必要が生じたか

## 2. 事実はどうか（測った・読んだもの。出所を書く）

## 3. 効く条件（**候補を並べる前に全部書く**）

| # | 条件 | 実データ | 何で確かめたか（外 / 自分の生成物） |
|---|---|---|---|

## 4. 影響範囲（信号や力の流れに沿って端から端まで。「隣」で止めない）

## 5. 決めたこと

## 検討して捨てた案

| 案 | 捨てた理由 |
|---|---|

## この決定が乗っている前提（**動いたら読み直す**）

「構造上できない」で決めたなら、その構造を書く。前提が別の変更で消えると、
この決定は嘘になる（HHKB #32 は 5 日間、人を止めた）。

## 覆す前に読むこと

## まだ決めていないこと

| 項目 | 決められない理由 |
|---|---|
