ms0216/keyboard-foundry/docs/templates/open-gaps.md

# 実機・要求とまだ違うところ（$NAME）

**差があること自体は悪くない。悪いのは、差があるのに気づけないこと。**

ここは「まだ解けていないもの」「受け入れた差」の台帳。`python -m foundry.gate $NAME`
（発注の門）が下の「★ 発注をせき止めているもの」の表を読み、取り消し線の無い行が
残っていれば止める。

**書き方の約束**（HHKB で実際に起きたことが理由）:

- 節を直したら**同じ変更で一覧も直す**。一覧を見る人と節を書く人は別人になる
  （解決済みが 4 日間「未解決」で残った）。行の頭だけ「済」にして次の一手を古いまま
  残さない（2 週間残った）
- 閉じるときは**行を消さずに取り消し線**を引き、何で確かめたか（外の事実か・自分の
  生成物か）と「故意に壊して検査が落ちることを確かめた」を書く。次の一手は「無し」
- 見出しは目次のアンカーなので書き換えない。決着は見出しの直下に `> **✅ 日付 …**`
- 番号は発見順。衝突したら改番して、その旨を書く
- 「構造上できない」で閉じるときは、**その構造**を書く（前提が動いたら再評価できるように。
  HHKB #32 は前提が消えたのに 5 日間「不成立」として人を止めた）
- 解けないと結論したあとで先へ進むなら `### 承知して発注する #N` を立て、誰が・いつ・
  駄目だったとき何を作り直すかを書く。**最初に書くものではない**

---

## いま残っているもの（YYYY-MM-DD に棚卸し）

### ★ 発注をせき止めているもの

| # | 何 | 次の一手 |
|---|---|---|

### 物を買う・刷るまで進まないもの

| # | 何 | 要るもの |
|---|---|---|

### まだ決めていない判断

| # | 決めること | いつ決まるか |
|---|---|---|

### 受け入れた差（塞がない。忘れないために残す）

| # | 何 | なぜ |
|---|---|---|

### ファーム（CI でビルド成功・実機未確認）

| # | 何 | 状態 |
|---|---|---|

---

<!-- 項目の雛形（コピーして使う）

## #N (YYYY-MM-DD) 題

**きっかけ**（誰の指摘・どの検査・どの測定）

### 事実（測った）

| | 値 | 出所（実測 / データシート / API / 二次） |
|---|---|---|

### 原因 ／ なぜ検査が気づけなかったか

### 選択肢（決めるのは利用者）

| 案 | 中身 | 代償 |
|---|---|---|

### 決めたこと（誰が・いつ）／やったこと

### 確かめたこと（故意に壊して落ちることを確認: 検査名）

### 触った先（コード / 検査 / 生成物 / 記録 — 消した名前で grep 0 件）

### この節を消してよいのは

-->
