ms0216/keyboard-foundry/docs/templates/task.md

# Task <ID> — 題名

**所要時間の目安:** 

> 先に <前のタスク> を済ませておくこと。失敗したときの原因がそこまでに絞れる。

## 1. なぜやるか

**太字 1 行で主張。**

| # | 確認対象 | 不成立だと |
|---|---|---|

**N が本命。** このタスクが確認しないこと:

## 2. 構成（本番と何が違うか・なぜ変数を 1 つに絞るか）

## 3. 用意するもの

| 品目 | 数 | 備考 |
|---|---|---|

## 4. 配線

図は生成器から出す（**SVG を手で直さない**。挿す穴の出どころは生成器の表だけ）。

| # | 挿すもの | 場所 |
|---|---|---|

### 通電する前に、これだけは見る

| 見るもの | 期待 | 意味 |
|---|---|---|

## 5. 手順

焼くファームはファイル名で名指しする（どのコミットのものか確かめる）。

## 6. 判定

### 測る前の予測（日付に固定。あとで書き換えない）

| 結果 | 見立て | 根拠 |
|---|---|---|

### 測定条件（測る前に書く）

| 条件 | 記入 |
|---|---|

### 対照実験を忘れない

ゼロは「流れていない」でも「測れていない」でも出る。死んだキーはゴースト試験に
自動で「合格」する。**対照が無い合格は無意味。**

### 記録

| 項目 | 期待 | 実測（YYYY-MM-DD） | 判定 |
|---|---|---|---|

## 7. うまくいかないとき

## 8. このタスクで確定しないこと

## 9. 不成立だった場合（順に試す。飛ばさない）
