ms0216/keyboard-foundry/projects/cckb-click/docs/coupon-cover-snap.md

# 電池の蓋の別案 B3（左右のばねの腕で掛ける蓋）の試し刷り

- **日付:** 2026-10-05〜06（B = コミット c62fe4c・B2 = 8dd3d54・**B3 = B2 を、独立の見直しを受けて直した物**。この文書は B3 の説明）
- **状態:** **試し刷りの候補。**本番の蓋（落とし込み式 A・決定記録 [2026-10-04-cover-latch](decisions/2026-10-04-cover-latch.md)）・本番の枠・基板は変えていない。
  門 #34b は閉じていない。採るかどうか・基板を変えるかどうかは、利用者が試し刷りを触って決める
- **経緯:** 利用者の問い「口の両側に爪があって、蓋がそれに掛かる、ふつうの板ばね式では駄目なのか」→ B を作った → 利用者が B を土台に選んだ（「自分の絵にいちばん近い」）→ 弱い所を直したのが B2 → 見直しで「外れない側は固いが、**入らない・戻らない・抜けない側が弱い**」と分かり、直したのが B3

絵: `build/cckb-click/cover_snap.png`（しくみ・開け方・B から直した所・基板の提案・数）・`coupon_cover_snap_howto.png`（組み方・手で見る所）・`slice_cover_snap.png`（スライスした線）。
刷る物: `build/cckb-click/coupon_cover_snap_plate_n04.gcode.3mf`。
コード: `projects/cckb-click/click_cover_snap.py`（立体と数）・`click_cover_snap_figs.py`（絵）・`tools/slice_cover_snap.py`（スライスと G-code の検査）・
`tests/test_cckb_click_cover_snap.py`（検査 18 件）。

## 結論

**形は B のまま、基板を 3 か所変える前提で、強さは足りる所まで来た。残る不確かさは「奥の案内の隙」1 つで、蓋 3 つはそれを振ってある。**

- 形: 蓋 1 個 = 手前の板 ＋ 左右に 1 本ずつのばねの腕 ＋ 腕の先のかぎ。足したのは、角を斜めに落とす所・つまみの段・丸みだけ
- **基板の前提（提案。いまは何も変えていない）**: ① クリップと電池を奥へ 2.0 ② ねじ H15 を右へ 3.5 ③ 使っていない穴 H30・H31 を消す
- 強さ: 指で強く押す 20 N（仮定）を、電池がいちばん悪い所（蓋の真ん中）で当てても、力の道のどこも TDS の強さの半分以内。強さに届くのは 38 N から
- **「片方だけでは開かない」は、案内の隙 0.10 の蓋 1 でしか言えない。**0.25 の蓋 3 は、片方ずつ 2 回に分ければ開く（わざとでないと起きない動きなので、
  利用者の条件「人がわざと外したときだけ」には反しないが、B2 の文書は言い過ぎていた）
- **きつい蓋は、爪で抜けないかもしれない。**蓋を動かす力（座る力 0.2〜0.4 N・爪で引く力）は、案内が 0.05 噛んだときの摩擦（数 N）より 1 桁小さい。
  本番では電池を裏から押せないので、**爪で抜けない蓋は不合格**。どの隙が合格かは、刷らないと分からない

## B2 から直した所（独立の見直しの 6 つ。確かめてから直した）

| # | 見直しで分かったこと | 確かめた結果 | B3 で直したこと |
|---|---|---|---|
| 1 | 蓋を動かす力が、案内 0.10 が噛んだときの摩擦より 1 桁小さい。3 つの蓋が同じ 0.10 | そのとおり（座る力 0.21〜0.39 N・腕 1 本の力は外す所でも 1.2 N。案内の壁の固さ 170 N/mm は見直した人の見積もり）| **蓋 3 つで、案内の隙を 0.10／0.15／0.25 に振った。**腕（0.90）と予圧（0.30）は 1 種類にした。枠の壁は 0.25 の位置で、蓋の側の当てで詰める |
| 2 | 引き抜くのが、爪の摩擦だけ（つまむと、つまみの面が 10° 手前へ開く） | そのとおり（つまみの外の面は、まっすぐな面だけだった） | つまみの手前の端を、外へ 0.4 出す段にした（厚さ 0.4）= **爪が引っ掛かる、奥を向いた面**。入り口の幅 1.0・段の奥の深さ 0.4。入れる道を塞がない・外面より出ない（検査） |
| 3 | 「片方だけでは開かない」は、隙 0.10 のときだけ | そのとおり。片方で出る量: 隙 0.10 で 0.26・0.15 で 0.39・0.25 で 0.66（式: 隙 ÷ 12.5 × 31。探した値は 0.26／0.29／0.57）。かぎの角の斜めは 0.35 | **蓋ごとに正直に書いた**（下の表）。斜めを 0.7 にすれば 3 つとも戻るが、直角の面が 0.4 になるので、やらない。検査を 3 つの蓋に広げた |
| 4 | 「腕の付け根の丸み 0.25」が、形に入っていない（隣の柱を削っていた。丸みを 0 にしても検査が通った） | そのとおり | 腕の内の面と付け根の塊の間の角を、円弧で**埋めた**（腕の付け根に、本当に丸み 0.25）。柱の欠けを無くした。**立体で測る検査を足した**（0 にすると落ちる）。かぎの付け根の埋め・つまみの段・45° の面も同じ検査で測る |
| 5 | 電池を出せるかが判断できない（クリップを動かした後、上から見える電池は 0.94） | そのとおり。ただし、いまの本番も 1.14 で、同じ動き（上面を爪で押し下げながら引く）。違いは、外面から 2.0 奥になること | 出し方を数で書いた（下の「電池の出し方」）。**枠の角に、クリップの板の代わりを付けた**（屋根を、板の下面の高さ 3.5 まで厚くした）→ 見える量と、爪の届き方を試せる。舌の固さは試せない、と手順の絵に書いた |
| 6a | 右の奥の案内の壁が、C_BAT のランドから 0.06 | そのとおり（ランドの手前の縁は −35.22。B2 は部品の箱 −34.7 で見ていた） | **奥の壁をやめた**（薄さ 0.8 で、屋根だけに付いていた壁）。案内の壁の奥の端は −35.95 = ランドから 0.73（検査が、基板のファイルから読む） |
| 6b | 腕の先の 45° の面の重なりが 0.07（ほぼ角） | そのとおり（縁の斜めが、腕の斜めより 0.2 手前から始まっていた） | 腕の先に 0.2 の段を付けて、斜めどうしを 0.25（面の長さ 0.35）重ねた |
| 6c | 電池の上の帯は、7.7 mm を宙に渡る。電池との隙 0.3 | そのとおり | 隙を 0.4 に（帯の厚さ 1.5 → 1.4。板の応力は 13／18 MPa のまま）|
| 6d | 奥の止めの壁（0.8）が、層を跨いで力を受ける | 6a で無くした | 押し切りの止めは、口の真ん中の溝の奥の縁（屋根・隙 0.15）と、その先の電池＋クリップの止め |

### 蓋 3 つ（切り欠きの数で見分ける）

| 蓋 | 案内の隙 | 片方だけつまんで引くと | 見ること |
|---|---|---|---|
| 1 | 0.10（きつい） | 0.26 出る < 斜め 0.35 → **手を離すと戻る**（差 0.09 は、刷りの誤差と同じ桁） | 噛まずに入るか・**爪だけで抜けるか** |
| 2 | 0.15（中） | 0.39 出る ≈ 斜め → 戻るとは言えない | 同じ |
| 3 | 0.25（緩い） | 0.66 出る > 斜め → **片方ずつ 2 回で開く** | 噛まないはず。がたつくか |

腕（厚さ 0.90・予圧 0.30）と、かぎは 3 つとも同じ。

### 電池の出し方（蓋を外した後）

- 口の真ん中は、幅 19 × 奥行き 4.65 × 深さ 5 の、**手前と上の両方へ開いた箱**。電池は外面から 3.7 奥（いまの本番は 1.7）
- 上から見える電池の上面: 奥行き 0.94 × 幅 7.3（クリップの板が公差の端まで手前なら 0.89）。その奥は、クリップの板の下。**いまの本番は 1.14** で、同じ板に隠れている
- 動き: 見えている上面と手前の縁を、爪か指の先で**下へ押しながら手前へ**引く。出てくるほど、押せる面が増える（本番の蓋の手順と同じ）
- **本物では、クリップの舌が電池を押さえている。その固さは、図面に値が無く、試し刷り（代わりは、ただの円板）でも分からない。**基板とクリップが届いてから見る
- 固かったときの手（**作っていない**）: クリップの板は、口の側の真ん中に切れ込みがある（図面 MY-CP-0247 の絵から読んで 幅 4〜5・奥行き 1.5 ほど。**寸法の記入は無い**）。
  その上の屋根（厚さ 0.7）に爪の窓を開ければ、電池の上面を 2.4 ほど押せる。代わりに、上面に穴が 1 つ見え、電池の缶（＋）が上から見える。
  切れ込みの寸法を実物で測ってから決める
- 電池の缶（＋）と、−のランド: −のランドは電池の真下（縁から 3.9 内）で、蓋を外しても見えない。缶は、蓋を外した口から見える（本番の蓋と同じ）

## B から B2 で直した所（前 → 後。B3 でも同じ）

| # | 弱い所 | B | B2 | 直し方 |
|---|---|---|---|---|
| 1 | 手前の板が薄い | 厚さ 1.27。20 N・真ん中で当たると 44／75 MPa（引っ張り／圧縮）。**22 N で強さに届く** | 厚さ 3.28。同じ条件で **13／18 MPa**（強さ 35／76 の 37 %／24 %）。板が強さに届くのは 54 N | クリップと電池を奥へ 2.0（基板の提案 ①） |
| 1' | 柱・腕（板の次に弱い所） | 柱 53・腕 32 MPa（20 N） | 柱 37・腕 35 MPa（強さ 76 の 49 %・46 %）。強さに届くのは 柱 41 N・**腕 38 N（いちばん弱い所）** | ランドが奥へ動いた分、柱の細い所が腕の撓みの小さい側へ移り、太くできた（0.96 → 1.10） |
| 2 | 右の腕の通り道に H15 | 140.0 へ動かす | 同じ（ほかの手は下の表で捨てた） | 基板の提案 ② |
| 3 | 片方ずつ 2 回で開く | 片方をつまんで 0.3 引くと、その側は外れたままになる | **案内の隙 0.10 の蓋 1 だけ**: 片方では 0.26 しか出ず、手を離すと、ばねが引き戻す。隙 0.15・0.25 の蓋は、戻るとは言えない／片方ずつで開く（上の「蓋 3 つ」）| かぎの外の角を 45° に 0.35 落とす |
| 4 | 押さえが弱い・座りが決まらない | 腕が縁を横へ 0.11 N で押すだけ（前後は摩擦だけ） | 腕 2 本が 45° の面を押して、**蓋を手前（かぎが縁に当たる向き）へ 0.21〜0.39 N**（摩擦 0.3 を引いて〜引かずに）= 蓋の重さ（0.86 g）の 25〜46 倍。予圧が誤差の端でも 0.10〜0.58 N | 腕の先と口の縁を 45° の面で当てる・予圧 0.15 → 0.30 |
| 4' | カチッと入るか | 奥へ押し切る余裕 0.15 だけ | 押し切る 0.35 手前から、かぎの角の斜めが蓋を引き込む（誤差を引いて 0.10 残る） | 3 と同じ斜め |
| 5 | 爪の掛かり・角 | 掛かり 0.75・角は鋭い | つまみに、爪が引っ掛かる段（出 0.4）・入り口の幅 1.0。腕の付け根に丸み 0.25（**B3 で本当に入れた**）・かぎの付け根を 0.2 埋める。入れるとき 0.3 ずれていても真ん中に寄る | 段・丸み・角を落とす |
| 6 | 確かめていなかったこと | 枠の角・クリップの公差 | 下の「数」の表 | 検査にした |

**直せなかった所・新しく弱くなった所（正直な所）**

- 座りの力は 1 N に届かない。腕の力は「外すときのひずみの上限」で頭が決まる（腕 1 本が出せる力は、外す所でも 1.2 N）。0.2〜0.4 N は、蓋が自分の重さで鳴らない力であって、指で押せば 0.15 引っ込む
- かぎの掛かり 1.10 のうち、直角の面は 0.75（残り 0.35 は 3 の斜め）。誤差を全部悪い側に取ると、掛かり 0.65・直角の面 0.30
- 奥の案内の隙は、蓋 3 つで振った（0.10／0.15／0.25）。**どれが合格かは、刷らないと分からない**
- Shift・Fn の穴のくぼみと、クリップの上の薄い屋根の間に残る厚い屋根が 4.1 → 2.1 になる（基板の提案 ① の代償）
- 力の仮定（20 N）と強さ（TDS）は、どちらも測った値ではない

## 比べた手と、選んだ理由

### 1. 手前の板

| 手 | 測った数 | 判断 |
|---|---|---|
| (a) クリップと電池を奥へ動かす | 板の厚さ = 1.28 ＋ 動かす量。1.5 で 20 N・真ん中当たりの引っ張りが強さの約 49 %（手計算）・2.0 で 37 %（立体から）。**2.3 を超えると**、電池の下の銅の逃げが、奥のビアの列（y = −29.1）に掛かり、3.0 では VBAT_SW の線（y = −28.35）に 0.2 まで寄る。枠は、Shift・Fn のくぼみまでの厚い屋根 約 4.1 が、動かした分だけ減る（3.0 動かすと 1.1） | **2.0 を採った** |
| (b) かぎを電池の近くへ | 腕の付け根はランドの外（x < 109.5）にしか置けず、かぎは腕の先に要る。腕を斜めにすると、押し縮める柱が曲がる | 作れない |
| (b') 板を、枠の屋根・基板の縁にも掛ける | 手前からまっすぐ入れる蓋は、入れる向きに枠の出っ張りを越えられない（上下に動かす動きが要る = 形が増える） | 捨てた |
| (c) 板の形（帯・高さ） | B で、電池の上の帯（高さ 1.5）まで使い切っている。真ん中の奥行きは、電池の手前の縁で決まる | これ以上は無い |
| (d) 電池を、支えの近くで当てる | くぼみの角で当てるのは B で入れてある（真ん中当たりの 0.74 倍）。角は、クリップの板の端より手前にしか置けない | 入れてある。検査は、悪い側（真ん中）で見る |

### 2. H15

| 手 | 測った数 | 判断 |
|---|---|---|
| (140.0, −48.225) へ動かす | H14（104.0）と、電池の中心で対称。動かす先の、穴の縁 ＋ 0.5 以内に線は無し・ビア 1 つ。つまみの切り欠きと電源スイッチのランドから 3 以上。右の壁の内面まで 2.1。手前の辺のねじの間隔 32.5 → 36.0（ほかは 18〜60） | **採った** |
| 右だけ、腕を非対称にする | 右のランドの外の縁 134.5 と、H15 の下穴の縁 135.7 の間は 1.2。腕 0.9 ＋ 隙も入らない | 作れない |
| 腕を H15 の上・下に通す | 下穴は基板の上 0〜2.8・腕も 0〜2.8・屋根の下面 3.0 | 作れない |
| H15 を消す | H14 から右の壁のねじ（143.475, −19.05）まで、角を回って 73 mm 空く（いまの最大は 60）。しかも口で壁を 30 mm 切る場所 | 捨てた |
| クリップと蓋ごと左へ寄せる | 左は H14 の下穴とランドの間 4.7 がいっぱい。寄せるなら H14 を動かす | 変える物が増えるだけ |

### 3. 片方ずつ

| 手 | 測った数 | 判断 |
|---|---|---|
| 案内をきつくして、回る量を 0 に近づける | 回る量 = 案内の隙 ÷ 12.5（かぎから案内までの奥行き）× 31（かぎの間）。隙 0.10 で 0.26・0.15 で 0.39・0.25 で 0.66。0 にはできない。きついと噛む | 蓋 3 つで振った |
| かぎの角を斜めに落として、ばねに引き戻させる | 斜め 0.35 > 出る量 0.26（隙 0.10 のとき）。代わりに、直角の面が 1.10 → 0.75。斜め 0.7 なら隙 0.25 でも戻るが、直角の面が 0.4 | **0.35 を採った** |
| 真ん中に鍵（回り止め）を足す | 口の真ん中の溝（隙 0.15）が、すでにその役。奥行き 4.4 しか無く、案内（奥行き 12.5）より効かない | 足さない |

### 4. 座り

| 手 | 測った数 | 判断 |
|---|---|---|
| 腕の先を 45° の面で当てる | 外へ開く力がそのまま前後の力になる（摩擦 0.3 で 0.54 倍）。腕 2 本で 0.21〜0.39 N | **採った** |
| 予圧を増やす | 0.30 で、外すときのひずみが 1.49 %（上限 1.52 %）。これ以上は、かぎを小さくするしかない | 上限まで使った |
| 腕を高く（屋根を薄く）して力を増やす | 高さ 2.8 → 4.1 で 1.46 倍。代わりに、窓の上の壁が 2.0 → 0.7（10 N で 2.5 下がる） | 捨てた |
| かぎの掛かる面を斜めにして引き込む | 電池に押されたとき、かぎが内へ逃げる向きの斜め | 捨てた（掛かる面は直角のまま） |

## しくみ（座標は CAD・基板の上面 = 0。左右は電池の中心 x = 122 で対称。クリップと電池は、いまより 2.0 奥）

| 働き | 形 |
|---|---|
| 入れる | 手前からまっすぐ押し込む。かぎの斜めの面が口の縁に乗って、腕が内へ逃げる → 縁の裏でカチッ |
| 腕 | 蓋の奥（y = −37.5）で付いて、手前へ戻る片持ち梁。長さ 13.0 × 高さ 2.8 × 厚さ 0.90。付け根に丸み 0.25。先（つまみ）が手前の面に出る |
| かぎ | 腕の先から 1.5 奥・外へ 1.3（縁との掛かり 1.1）。掛かる面は直角。口の縁（手前の壁の残り・厚さ 1.6）の裏に掛かる |
| 電池が押す力 | 電池 → 蓋のくぼみの左右の角（隙 0.2）→ 蓋の板 3.28 → 左右の柱（引っ張り）→ 腕（押し縮め）→ かぎ → 口の縁。かぎは外へ開く向きに押され、外は縁が止める |
| 座る | 腕は、先が 0.3 外へ開いた形で刷る → 掛けた後、腕の先の 45° の面（長さ 0.35）が、縁の 45° の面を押す → 蓋が手前へ寄り、かぎが縁に当たって止まる |
| 上・下・倒れ | 上は枠の屋根（腕の通る窓の上に、手前の壁が高さ 2.0 × 奥行き 3.0 残る）・下は基板。蓋は奥行き 14 の間、屋根の下にいる |
| 左右・奥 | 奥の左右に、枠の案内の壁（隙は蓋ごとに 0.10／0.15／0.25）。口の真ん中の溝（隙 0.15。奥の縁が、押し切りの止め） |
| 開ける | 左右の口の縁の斜めの面から爪を入れ、つまみの手前の端の段の奥に掛け、内へ 1.6 つまんで（1.2 N ずつ）手前へ引く |
| 刷る向き | 蓋は**底をベッドに**（腕とかぎは平面の形そのまま）。枠は上面をベッドに。支え無し |

## 基板の変更の提案

**いまは何も変えていない**（`pcb/cckb-click_main.kicad_pcb`・`spec.py` はそのまま）。下の数は、配線済みの基板のファイルを読んで数えた物（検査 `test_the_board_proposal_against_the_routed_board` が同じ数え方をする）。

| # | 変えること | 座標（CAD） | 一緒に動く・消える物 | 掛かる銅 |
|---|---|---|---|---|
| ① | 電池クリップ BT1 を奥へ 2.0 | `CLIP_AT` (122.0, −41.425) → **(122.0, −39.425)** | ＋のランド 2 つ（中心 (111.975／132.025, −41.425) → (同, −39.425)・4.15 × 4.2）・−のランド φ7 と、その中のビア 3 つ（フットプリントごと）・電池の下の銅の逃げ CELL_KEEPOUT の奥の端 −31.665 → −29.665（手前の端は基板の縁のまま）・VBAT_IN の線（ランドから出る 5 本と、裏の y = −44.06 の線・ビア 2 つ。配線の生成が CLIP_AT から引き直す） | 逃げの奥に入る **GND のビア 3 つを外す**: (115.375／121.375／127.375, −30.625)。その奥のビアの列（y = −29.1）までは 0.26・VBAT_SW の線（y = −28.35・幅 0.3）までは 1.2 残る。動かした＋のランドと、まわりのビアの隙は 0.4 以上。C_BAT（136.2, −33.0）・電源スイッチは動かさない |
| ② | ねじ H15 を右へ 3.5 | (136.5, −48.225) → **(140.0, −48.225)** | 枠の座と下穴・底のシートの穴（`click_case.sheet_solid` は `spec.SCREWS_PERIMETER` から作るので、自動で動く）・**裏の、ねじの頭の銅の逃げ SCREW_HEAD_KEEPOUT**（`pcb_extra.py` が、ねじの位置から作る） | **GND のビア 1 つを外す**: (139.375, −48.625)。穴の縁 ＋ 0.5 以内に線は無い |
| ③ | 使っていない穴 H30・H31 を消す | (115.0, −48.225)・(129.0, −48.225) | `spec.SCREWS_COVER` を空に。底のシートは、もともと塞いでいる。裏の、頭の銅の逃げがこの 2 つにもあれば、一緒に消える（`pcb_extra.py` を見て確かめる）| なし（銅の無い穴）。消さなくても B2 は成り立つ（蓋の真ん中の塊の下になるだけ） |

任意: 手前の面の左右の隙間（腕と胴の間）の床に、GND の縫い付けのビアが 2 つ見える: (108.375, −42.625)・(109.375, −48.625)。GND なので害は無いが、動かせば床に銅が見えなくなる。

**C_BAT との隙**: 蓋の右の案内の壁（枠・y ≤ −35.95）は、C_BAT の手前のランド（−35.22〜）から 0.73。C_BAT は動かさない。手はんだの盛りが、ランドの外へ 0.7 以上はみ出すなら当たる。

**電池の出し方が変わる**: 電池が外面から 1.7 → 3.7 奥になる（上の「電池の出し方」）。手順書の「電池の替え方」を書き直す。

**枠の側で変わること**（本番に採るとき）: クリップの空間（屋根の下面 4.3）が奥へ 2.0 伸びる・その手前の 2.0 は厚い屋根（下面 3.0）に戻る・口・窓・縁・案内の壁・H15 の座。

**変えた後に、見直す・回し直すこと**

- 基板: DRC・配線の生成（`tools/route_click.py`）の引き直し・`tests/test_cckb_click_board.py`／`_pcb.py`（電池の逃げ・ランド・ねじの検査）・縫い付けのビアの数・発注用のファイル一式
- 監査 1 回目（決定記録 2026-10-04-audit-1）の E 重要 1「電池の缶の縁と、表のベタの縁」: 逃げが動くので、缶の縁（止めに当てた位置）との関係を取り直す
- 枠: Shift・Fn のくぼみまでの屋根 2.1 で、キーを押したときの枠のたわみ（`click_stiffness.py`）・右の枠の刷り（屋根 0.7 の範囲が 2 mm 広がる）
- 底のシートの穴・組み立ての手順書（ねじの位置）・`docs/open-gaps.md` の #34b と P25
- 落とし込み式（A）の決定記録の前提「クリップの位置 CLIP_AT」「基板を変えない」が動く → 読み直す

## A・S・B3 の比べ

| | A（落とし込み式 v2 = いまの本番） | S（横ずらし） | B3（左右のばねの腕） |
|---|---|---|---|
| 複雑さ | 斜めの耳 ＋ 上下 2 本の棒 ＋ 歯 2 つ ＋ つぶれる筋 | 耳 ＋ 斜面の出っ張り ＋ 枠の板ばね ＋ つぶれる筋 ＋ 橋 2 つ | **板 ＋ 腕 2 本 ＋ かぎ 2 つ**。枠は 縁・案内の壁 |
| 電池の力を受ける物 | 樹脂の塊（耳 → 溝）。ばねを通らない | 樹脂の塊（耳 → 縁）。ばねを通らない | かぎと腕（押し縮め）と、蓋の板の曲げ |
| 20 N（指で強く・仮定）での応力 | 板 18／26 MPa | 18／42 | 板 13／18（真ん中当たり）・柱 37・腕 35 |
| 強さに届く力（計算） | 39 N（板の引っ張り） | 38 N（板の引っ張り） | **38 N（腕）**・柱 41・板 54 |
| 開き方 | 棒 2 本を押して上へ = 爪 1 つの 1 回の擦り | 板ばねを奥へ ＋ 右へ ＋ 上へ | 左右 31 mm 離れた 2 か所を、内へつまんで手前へ引く |
| 片方だけ | その端が 1.1 浮き、浮いたままになりうる | 浮かない | 案内の隙しだい: 0.10 なら 0.26 出て、手を離すと戻る。0.25 なら 0.66 出て、片方ずつ 2 回で開く |
| ばねを押す力 | 2.2 N（2 本） | 0.7〜0.9 N | 1.2 N ずつ |
| がた | 上下 0.2〜0.4 は摩擦だけ | つぶれる筋 | 腕のばねが、かぎの当たる向きへ 0.2〜0.4 N で押す |
| 見える隙間 | 手前の面の切れ目 0.4 × 3 本 | 手前のくぼみ・上面の穴 2 つと溝 | 手前の面の左右に 幅 1.8 × 高さ 3 の隙間（行き止まり）と、爪の入る斜めの角。上面は蓋の輪郭だけ |
| クリップの上（公差の端 4.35） | 上の板の下面 4.3 に当たりうる | 同じ | 蓋はクリップの板の上に掛からない。板が 0.25 手前へずれても 0.1 空く |
| 基板 | 変えない | 変えない | **クリップを奥へ 2.0・H15 を右へ 3.5・H30 と H31 を消す** |

## 数と、何で確かめたか

| 項目 | 値 | 確かめ方 |
|---|---|---|
| 掛けた蓋の動ける量 | 手前 0.05 未満・上 0.2。胴の遊び（腕を 0.3 内へ逃がして）: 奥 0.15・左右は蓋ごとの案内の隙（0.10／0.15／0.15。蓋 3 は、口の真ん中の溝の 0.15 が先に当たる）| 立体を 0.05 ずつ動かして当たるまで。縁の無い枠・かぎの無い蓋では 2 以上進む（壊して見た） |
| 電池の代わりが手前へ | 0.2 で蓋に当たる。蓋を外せば 15 以上、何にも当たらない | 立体 |
| かぎの掛かり | 1.10（立体で測って 1.08）・直角の面 0.75。誤差を全部悪い側で 0.65 | 立体の重なりの幅・最後は計算 |
| 片方だけつまむ | **腕を、外す所まで実際に撓ませた形**で、蓋 3 つとも: まっすぐは 0.05。ずらす・回すを探して 0.26／0.29／0.57（式の見積もり 0.26／0.39／0.66 と 0.15 以内で合う。文書と絵は、大きい方を書く）。蓋 1 だけが、斜め 0.35 − 0.05 以内。蓋 1 で、その姿勢で手を離した形は、縁に重なる（そこでは止まれない）。両方をつまめば、同じ探し方で 1.2 以上 | 立体を平面の中で乱数で動かして探す。**残り**: 蓋と枠は固いと見ている。片方をつまんだまま強く引けば、腕と柱が撓んで、もう少し出る（手を離せば戻る向きは同じ） |
| 入れる・抜く道 | 腕を外す所まで内へ動かせば、14 手前から座る位置まで当たらない。0.3 横へずれていても、口に入り始める所で当たらない | 立体（0.5 おき） |
| 腕のひずみ | 外すとき 1.49 %（上限 1.52 %）・入れるとき 1.39 %・胴に当たって止まるとき 1.68 %（曲げ強さのひずみ 2.76 %） | 計算（TDS の値・名目の断面）。**付け根の丸み 0.25 での集中は、入れていない**（A・S と同じ扱い）。丸みそのものは、立体で測る |
| つまむ力 | 1.2 N ずつ | 計算 |
| 座る力（腕 2 本・手前へ） | 0.21〜0.39 N。予圧が ± 0.15 ずれて 0.10〜0.58 N。**案内が噛んだときの摩擦（数 N）には勝てない** | 計算。小さい側は摩擦 0.3（仮定）を引いた値 |
| 応力（20 N・真ん中当たり） | 板 13／18・柱 37・腕 35・かぎのせん断 1.4・縁の面圧 4.8 MPa | 板の断面は立体から測る（A と同じ測り方）。柱は、腕と柱の間の偶力を全部柱が受けると見た上側の見積もり |
| 強さに届く力 | 腕 38・柱 41・板の引っ張り 54・板の圧縮 86・腕の座屈 147 N | 同じ式を逆に解く。**38 N は、電池 1.8 g の慣性に直すと 2130 G**（導いた値。要求ではない・落として測った値でもない） |
| 落下 1500 G（仮定）で、かぎが自分の重さで揺れる量 | 0.49（外れるのは 1.40 = 2.9 倍） | 計算（固有の振動数と半波 0.5 ms の倍率） |
| クリップの公差 | クリップが前後・左右に ± 0.25 ずれても、蓋・枠に当たらない。蓋は、クリップの板の範囲の、電池の上面より上に何も無い | 立体（図面から作ったクリップを、4 つの向きにずらす）。0.6 手前なら当たる（壊して見た） |
| 窓の上の壁 | 高さ 2.0 × 奥行き 3.0・張り出し 5.6。先を 10 N で押して、下がり 0.11（蓋との隙 0.2）・付け根 28 MPa | 計算（奥の屋根とのつながりを数えない、弱い側）。高さ 0.7 なら 2.5 下がる |
| 裸の銅 | −のランドは電池の真下で、電池の縁から 3.9 内。左右の隙間は、蓋の付け根の塊で行き止まり。床のビアは GND 2 つ。＋のランドは、蓋の柱の内側 | 立体と、基板のファイル |
| つまみの段・丸み・45° の面 | 段: 出 0.4 × 厚さ 0.4・入り口 1.0。丸み: 腕の付け根 0.25・かぎの付け根 0.2。45° の面: 重なり 0.25（面の長さ 0.35） | 立体に点を打つ（丸みを 0 にした蓋では落ちる）。入れる道は、段があっても当たらない |
| 電池の出し方 | 上から見える電池 0.94 × 7.3（公差の端で 0.89）・本番は 1.14。電池の代わりは、クリップの板の代わりの下を通って抜ける | 立体（枠に、板の代わり）。**舌の固さは、試せない** |
| C_BAT のランドと、案内の壁 | 0.73 | 配線済みの基板のファイルから、ランドを読む |
| 電池の缶（＋）が触れる物 | クリップ（＋）・蓋と枠（樹脂）・基板の、銅の逃げの中（−のランドは缶の底の真ん中だけ）| 形から。逃げが動いた後の基板で、取り直す |
| 刷れるか | 蓋: 宙に浮くのは、電池の上の帯だけ。枠: 上を向いた面を足していない | 立体。G-code: 腕は線 2 本以上・腕と胴の隙に線が無い（1 層目も）・帯の最初の層は左右へ渡る線・縁と案内の壁は線・空洞と窓は空 |

## 刷り方

- `coupon_cover_snap_plate_n04.gcode.3mf`: A1 mini・0.4 ノズル・層 0.1・PLA・支え無し。**造形 47 分 23 秒（準備込み 53 分 52 秒）・5.89 cm3・7.42 g**・6 個
  （枠の角・当て板・電池の代わり・蓋 3 つ）。刷り方の設定は、精度優先のまま変えていない
- **当て板は、提案どおりに変えた基板の形**（クリップの脚と止めが 2.0 奥・H15 が 140.0・H30 と H31 なし）。いまの本番の試し刷りの当て板とは合わない
- **枠の角には、クリップの板の代わりが付いている**（試し刷りだけ。屋根を、板の範囲で、下面の高さ 3.5 まで厚くした）
- 蓋の見分け: 上の板の奥の縁の切り欠きの数 = **奥の案内の隙**: 蓋 1 = 0.10・蓋 2 = 0.15・蓋 3 = 0.25（上の「蓋 3 つ」）。腕・予圧・かぎは 3 つとも同じ
- **きつくて、爪だけで引き抜けない蓋は、その隙が不合格。こじらない**（本番では、電池を裏から押せない）
- 回した検査: 立体の検査 18 件・スライスと G-code の検査（設定 25 個・警告 0・支えの線なし・見る点をずらすと落ちる）。
  **回していない検査: 刷った物での全部**

## 刷らないと分からないこと

| 項目 | 理由 |
|---|---|
| a〜l（`coupon_cover_snap_howto.png`） | 前の 4 つの差し込み式は、計算が 4 回とも「留まる」と言って外れた |
| **どの案内の隙なら、噛まずに入り、爪だけで抜けるか** | 蓋を動かす力が、噛んだときの摩擦より 1 桁小さい。蓋 3 つで見る |
| 蓋 1 で、手を離すと本当に戻るか（片方だけ）・押し切る手前で引き込まれるか | 斜め 0.35 と出る量 0.26 の差 0.09 は、刷りの誤差と同じ桁 |
| 爪が、つまみの段に掛かるか・段（0.4 × 0.4）が欠けないか | 手でしか分からない |
| **本物のクリップで、電池を爪で出せるか** | 舌の固さの値が無い。試し刷りでは再現できない。基板とクリップが届いてから |
| 座りの固さ（0.2〜0.4 N）が、手で触って足りるか・へたって抜けないか | PLA のクリープは計算していない |
| 腕・柱が、何 N で白くなるか | 38 N は TDS の値での計算 |
| 本物のクリップ・電池での固さ | 当て板にクリップの板と舌の代わりは無い |

## どれを刷るか

利用者が B を土台に選んだので、**B3 を刷る**。A の試し刷り（`coupon_corner_plate_n04.gcode.3mf`）は基板を変えずに済む形なので、B3 が駄目だったとき・基板を変えたくないときの比べる相手として残す。

## 採るなら要ること（いまは何もしていない）

- 上の「基板の変更の提案」を決める（費用と、配線・検査のやり直し）
- 寸法を `spec.py`（`[暫定]`）と `click_layout` に移し、`click_case` の枠・蓋・試し刷りを置き換える（落とし込み式の名前を、コード・生成物・記録から消す）
- 決定記録を書く（この文書は試し刷りの説明で、決定ではない）
