ms0216/keyboard-foundry/projects/cckb-click/docs/coupon-cover-slide.md

# 電池の蓋の別案 S（横ずらしで掛ける蓋）の試し刷り

- **日付:** 2026-10-05
- **状態:** **試し刷りの候補。**本番の蓋（落とし込み式・決定記録 [2026-10-04-cover-latch](decisions/2026-10-04-cover-latch.md)）・本番の枠・基板は変えていない。
  門 #34b は閉じていない。採るかどうかは、利用者が 2 つの試し刷り（いまの蓋 = `coupon_corner_plate`・S = `coupon_cover_slide_plate`）を触って決める
- **なぜ作ったか:** いまの蓋は「爪 1 つで、棒 2 本を押しながら上へ擦ると開く」（決定記録の「満たせていないこと」）。
  S は、上へ抜けないことを**ばねを通さずに**作り、開ける動きを 3 つの別の向きに分ける

絵: `build/cckb-click/cover_slide.png`（しくみ・開け方・数）・`coupon_cover_slide_howto.png`（組み方・手で見る所）・`slice_cover_slide.png`（スライスした線）。
刷る物: `build/cckb-click/coupon_cover_slide_plate_n04.gcode.3mf`。
コード: `projects/cckb-click/click_cover_slide.py`（立体と数）・`click_cover_slide_figs.py`（絵）・`tools/slice_cover_slide.py`（スライスと G-code の検査）・
`tests/test_cckb_click_cover_slide.py`（検査 16 件）。

## 結論

**「上へ抜けない」は形で満たせた。「わざとでないと開かない」は、いまの蓋より形で決まる部分が増えたが、形だけでは言い切れない。刷って決める。**

- 掛けた蓋は、板ばねを押し切っても・板ばねが折れても、**右へ 1.45 ずらすまで上へ抜けない**（立体を 6 つの向きに動かして探した）
- 板ばねに触れなければ、蓋は右へ **0.25 までしか動かない**（板ばねの鼻に、直角の面で当たる）
- 板ばねを押せる所は、蓋の右の外にある幅 1.0 の溝の中。**そこにある物が蓋を押せる向きは、左（閉まる向き）だけ**。
  開けるには「溝の中で奥へ押す物」と「蓋を右へ動かす物」が別々に要る = いまの蓋の「1 回の擦り」では開かない
- **言い切れない所:** 板ばねを押す力は 0.7〜0.9 N と小さい。細い物が溝に入って板ばねを押し、同時に別の物が蓋の上面を右へ擦れば、蓋は右へずれる
  （その後、上へ持ち上げる 3 つ目の動きが要る）。鞄の中でこれが起きるかは、刷って擦って見る
- **S がいまの蓋より悪い所**（下の表）: 蓋の胴の応力・見える隙間・枠の刷りの危険（橋が 2 つ）・開け閉めに両手の指が要る

## しくみ（座標は CAD・基板の上面 = 0）

| 働き | 形 |
|---|---|
| 入れる | 蓋を、掛ける位置より 1.6 右で上から落とす → 左へ 1.6 ずらす → 枠の板ばねがカチッと戻る |
| 電池が手前へ押す力 | 電池 → 蓋の手前の塊の真ん中（隙 0.2）→ 蓋の胴 → 左右の耳（上から下まで）→ 口の左右の縁（手前の壁の残り。左 1.25・右 1.0）の奥の面 |
| 上へ抜けない | 耳の奥の「出っ張り」（上面が 45° の斜面）が、枠の屋根（左）と出っ張り（右）の下に入る。掛かりは左右とも 1.45。持ち上げる力は、斜面で「下へ・手前へ」に変わり、手前は縁が受ける |
| 右へ戻らない（留め） | 枠の右の壁の上面に切れ目で作った板ばね（厚さ 1.0 × 高さ 1.3 × 長さ 9.0・**前後に撓む**）。先の「鼻」が、蓋の右端の「当て」の端面と直角に突き合う |
| がたを取る | 枠の斜面の細い筋（つぶれる筋・高さ 0.30）に、蓋の出っ張りの斜面が乗る。蓋を「下へ・手前へ」押すので、上下と前後の遊びを 1 つで取る。蓋 3 つで斜面の隙を振る |
| 開ける | ① 右の溝に爪の先を入れ、板ばねを奥へ押す ② もう 1 本の指で蓋を右へずらす ③ 上へつまみ上げる |
| 刷る向き | 枠も蓋も上面をベッドに（支え無し） |

## いまの蓋（落とし込み式 v2）と S の比べ

| | いまの蓋（落とし込み式 v2） | S（横ずらし） |
|---|---|---|
| 電池の力を受ける物 | 樹脂の塊（耳の 45° の面 → 溝） | 樹脂の塊（耳の平らな面 → 縁） |
| 上へ抜けないのは | **ばね**（棒 2 本の先が歯の下） | **樹脂の塊**（出っ張りが屋根の下・掛かり 1.45） |
| 留めのばねが受ける力 | 蓋を持ち上げる力の全部 | 蓋が右へ戻ろうとする力だけ（蓋の重さ × 1500 G = 4.3 N・座屈は 9.1 N と見積もった） |
| 開く動き | 棒 2 本を 0.43 押す ＋ 上へ = **爪 1 つの 1 回の擦り** | 板ばねを奥へ 0.6〜0.75 ＋ 蓋を右へ 1.6 ＋ 上へ = **向きの違う 3 つ・押す物と動かす物が別** |
| ばねを押す力 | 2.2 N（2 本） | 0.7〜0.9 N（1 本）。**S の方が小さい** |
| ばねが無くなったら | 上へ抜ける | 右へ 1.45 ずらすまで抜けない（振れば、ずれうる） |
| 片側だけ浮く | 棒 1 本を押すと、その端が 1.1 浮く | 浮かない（どちらの端も、塊の下） |
| 上下の遊び | 0.2〜0.4（摩擦で押さえるだけ） | つぶれる筋が効けば 0。筋なしで探すと 四隅が 0.31（いちばん緩い蓋が誤差ぶん緩いと 0.55）まで |
| 蓋の胴の応力（電池 26.5 N） | 引っ張り 23.7・圧縮 34.1 MPa | 引っ張り 24.4・**圧縮 55.3 MPa**（真ん中で受けるので、曲げが 81 → 134 N·mm）。**S の方が悪い** |
| ばねの落下の余裕 | 1.1〜1.9 倍 | 先の揺れ 0.10 に対し重なり 0.5 = 5 倍 |
| 見える隙間 | 手前の面の切れ目 0.4 × 3 本 | **手前の面の右に 幅 1.75・奥行き 1.15 のくぼみ**・上面の右に 穴 2 つ（1.75 × 1.25・2.15 × 1.25）と、板ばねのまわりの溝（幅 2.2〜2.8 × 長さ 9.1）。**S の方が悪い** |
| 開け閉めの手数 | 押し下げるだけ／爪 1 つ | 落として左へ寄せる／**指 2 本** |
| 無くす危険 | 0.22 g の蓋 | 0.29 g の蓋（同じ） |
| 枠の刷りの危険 | 歯（角柱）2 つ | **橋 2 つ**（板ばねの溝の底 幅 2.2〜2.8・右の空洞の底 1.6 × 2.9）と、板ばね（溝の底と 0.4 しか離れていない）。**S の方が悪い** |
| 蓋の刷り | 手前の面をベッドに（棒・切れ目 0.4） | 上面をベッドに（切れ目なし・宙に浮く面なし） |
| 枠を変える範囲 | 口の左右の溝・歯 | 口の左右の空洞・屋根・右の壁の上面 9 mm（ねじ H15 の上を通る） |
| 基板 | 変えない | 変えない |

## 数と、何で確かめたか

| 項目 | 値 | 確かめ方 |
|---|---|---|
| 蓋が上がる量（板ばねは上がったまま・筋なし） | 名目の蓋 0.31・いちばん緩い蓋が誤差ぶん緩いとき 0.55（検査の上限 0.75）・傾き 約 1.4°（上限 2.5°） | 立体を 6 つの向きに乱数で動かして探す（`wiggle`）。屋根を取った枠では 2 mm 以上上がる = 探し方が抜け道を見つけられる |
| 板ばねが無いとき、抜けるまでのずらし | 1.4 まで上がらない・1.5 で抜ける | 同じ探し方で、ずらす量を決めて |
| 掛かり（上へ）| 1.45／1.25（右は枠の出っ張りの幅）。蓋が右へ 0.25 寄り、両側が 0.15 ずつ短く刷れても 0.9 | 立体の重なりの長さ |
| 掛かり（縁の裏）| 左 2.2・右 1.5（同じ端で 1.2 以上） | 立体 |
| 電池が出ない | 26 の向きとも 1.0 以内で当たる（手前 0.2） | 立体（電池の代わりを動かす）。蓋を外せば、手前へ 22 mm 何にも当たらない |
| 入れ方・外し方 | 落とす 25 歩・ずらす 17 歩で、枠・当て板・クリップ・電池と重ならない | 立体。クリップは図面から作った形（外） |
| クリップの板の下を通らない | 耳より奥の出っ張りは、落とす位置から掛けた位置まで、板の外（x ≤ 113.35／≥ 130.65） | 立体 |
| 板ばね | 重なり 0.65（蓋が座ると 0.5・誤差で 0.35）・押し込み 0.6〜0.75・力 0.7〜0.9 N・ひずみ 1.39 %（上限 1.52 %）・止めで 1.48 % | 計算（TDS の値・名目の断面）。押し込みで通れることは立体 |
| 板ばねの座屈 | 9.1 N（先が自由と見て）／74 N（先が滑らないと見て）。受ける力は 4.3 N | 計算。**上下に撓む薄い舌（厚さ 0.6）は 1.6 N で、捨てた** |
| 応力（電池 26.5 N） | 蓋の胴 24.4／55.3・耳の首 18.4・枠の縁 14.9 MPa | 断面を立体から測る。同じ測り方で本番の蓋を測ると `cover_beam` と合う |
| がた取り（筋のしめしろ） | 蓋 1 +0.16・蓋 2 +0.09・蓋 3 +0.02。刷りの誤差 ±0.15 のどこでも、1 つは 0〜0.2 に入る。蓋 1 がきつく刷れると、筋の無い所も当たる（そのときは 2・3） | 計算と立体（座った蓋は、筋とだけ重なる） |
| 右の空洞から、ねじ H15 の下穴まで | 1.45。板ばねの溝の底は、下穴の上 0.5 | 立体に点を打つ |
| 刷れるか | 蓋: 45° より寝た下向きの面なし。枠: S が足した宙に浮く面は、橋 2 つだけ | 立体の面の向き。G-code: 橋の線が溝の短い方へ渡っている・板ばねのまわりに線が無い・板ばねと溝の底の間の 4 層に線が無い・筋が線になっている |

## 刷り方

- `coupon_cover_slide_plate_n04.gcode.3mf`: A1 mini・0.4 ノズル・層 0.1・PLA・支え無し。**造形 36 分 54 秒（準備込み 43 分 22 秒）・4.40 cm3・5.55 g**・6 個
  （枠の切れ端・当て板・電池の代わり・蓋 3 つ）。当て板と電池の代わりは、いまの蓋の試し刷りと同じ物
- **刷り方を 1 つだけ変えてある: 橋の向きを板の前後に固定（`bridge_angle = 90`）。**自動のままだと、板ばねの溝の底の橋が、長い方（左右 9 mm）へ渡る
  （G-code で見た）。**Bambu Studio で STL から切り直すときは、この設定を入れること。**渡した `.gcode.3mf` は、入れて切った物
- 回した検査: 立体の検査 16 件（`tests/test_cckb_click_cover_slide.py`）・スライスと G-code の検査（設定 26 個・警告 0・支えの線なし）。
  **回していない検査: 刷った物での全部**（留まるか・固さ・擦る・振る・落とす・回数）

## 検討で分かったこと（次に形を変えるときに効く）

- **横ずらしの蓋は、左右の足で電池を受けられない。**蓋を 1.6 右で落とすので、左の足（電池の円のすぐ外まで詰めた塊）が電池の上に載る（検査が見つけた）。
  電池と同じ中心の丸い面を残せるのは、真ん中の左 1.3 ほどまで（検査が立体で見る）→ 真ん中で受けるしかなく、蓋の胴の曲げが大きくなる。これが、S の応力が悪い理由
- **ずらすと、蓋の一部がクリップの板の下を通る。**耳より奥の部分は、板の外（x ≤ 113.35／≥ 130.65）にいなければ、上から落とせない
- **蓋を手前の面をベッドに刷る限り、平らな受け面の耳は作れない**（縁の裏に入る耳が宙から始まる）。S の蓋は上面をベッドに刷る
- **上面をベッドに刷ると、蓋に板ばねを置けない**（長さ 7 mm 以上が要り、電池の力を運ぶ手前の板が切れる）。留めのばねは枠の側に置いた
- **ずらす分の隙間は、どこかに必ず見える**（落とす位置で蓋がいた所が、掛けると空く）
- **薄い舌を軸の向きに押すと座屈する**（厚さ 0.6 × 幅 0.9 × 長さ 8.3 で 1.6 N）。板ばねは、高さを取れる向き（ベッドから立つ板）にした
- 決定記録が横ずらしを捨てた理由「掛かりを作れるのは片側だけ」は、離れていく側に「奥の壁から出た出っ張り」を置けば成り立たない

## まだ確かめていないこと

| 項目 | 理由 |
|---|---|
| 刷った物で、留まるか・固さ・擦る・振る・落とす・20 回の開け閉め | 刷っていない。見る所は `coupon_cover_slide_howto.png` の a〜l |
| 板ばねが、溝の底（橋）に付かずに刷れるか | G-code では 0.4（4 層）離れている。橋の垂れは刷って見る。**刷り上がったら、まず板ばねを爪で押して見る** |
| つぶれる筋の固さ（手で左へ寄せ切れるか）・何回で削れるか | しめしろは計算。筋は、蓋が横から擦って乗る |
| 細い物が溝に入り、別の物が蓋を右へ擦って開くことが、鞄の中で起きるか | 形では防げていない。利用者が擦って決める |
| 蓋の胴が、電池に強く押されて白くならないか | 圧縮 55 MPa は曲げ強さ 76 の 1/1.4。1500 G は借りた仮定 |
| 本物のクリップで、上の板（下面 4.3）とクリップの上（公差の端 4.35）が当たらないか | いまの蓋と同じ未解決。当て板にクリップの板の代わりは無い |
| 左右の空洞（基板まで抜けている所）の下の基板の面に、裸の銅が見えないか | 見ていない（本番に採るときに、基板の検査に足す）。右の空洞の右半分と、板ばねの溝には底がある |
| キャップ・電源スイッチのつまみとの取り合い | 変えた範囲は口のまわりと右の壁の上面だけで、つまみの切り欠きは範囲の外（検査）。キャップは変えた範囲に無い |

## 本番に採るなら要ること（いまは何もしていない）

- 寸法を `spec.py`（`[暫定]`）と `click_layout.cover` に移し、`click_case` の枠・蓋・試し刷りを置き換える（置き換えられた落とし込み式の名前を、コード・生成物・記録から消す）
- 右の枠の刷り方に `bridge_angle = 90` を入れてよいかを、枠全体の橋で見直す
- 決定記録を書く（この文書は試し刷りの説明で、決定ではない）
- **基板を変える提案は無い。**S は基板を変えずに成り立つ。蓋の胴の応力を下げるには、蓋の奥行きを増やすしかなく、それを止めているのはクリップの板
  （基板の上 3.5〜4.35）で、基板の形ではない
