ms0216/keyboard-foundry/projects/cckb-click/docs/provisional-values.md

# まだ実測していない値（cckb-click）

`spec.py` で `[暫定]` を付けた値の一覧。**tests/test_meta.py が名前と数値をコードと突き合わせる。**
確定したら行を消し、コードのタグも外す（残ると落ちる）。

| 定数 | 現在値 | 何の値か | どうやって確かめるか | 外したときの影響 |
|---|---|---|---|---|
| `SW_OVERTRAVEL` | 0.1 | ON のあと底を突くまで | 基板が来たら実物を押して測る | 押し切りでキャップが沈む量・スイッチの本体までの残り 0.1 |
| `POCKET_DEPTH` | 1.0 | 枠の下面のくぼみの深さ（押す面の高さを決める） | 試し刷り standin・基板が来たらステムの高さ | 浮き・押しっぱなし |
| `TAB_T` | 0.4 | つばの厚さ（押す面から掛かる面まで） | 試し刷り latch（1 番 0.4 と 2 番 0.6） | 押す面の高さ・つばの強さ |
| `HOLE_A` | 16.5 | 案 A の 1u の穴（x。y は 16.0） | 試し刷り a | キャップの大きさ・リブ |
| `HOLE_CHAMFER` | 0.4 | 穴の上の縁の面取り | 試し刷りで見る・触る | くぼみの上の皮の厚さ（0.6）・見た目 |
| `CAP_TOP_CHAMFER` | 0.8 | キャップの上の縁の面取り | 試し刷りを触る | 指ざわり |
| `TAB_R` | 1.0 | つばの外の角の丸み | 試し刷りで、斜めにこじっても抜けないか | 角の掛かり |
| `POCKET_CLEAR` | 0.3 | つばとくぼみの横の隙 | 試し刷りで擦れないか | 擦れ・壁の厚さ |
| `SEAM_NOTCH` | 2.0 | 継ぎ目の溝（幅。深さは 0.5）。キャップの胴の奥の面と、枠の穴の奥の壁 | 最小の一式を刷って、継ぎ目のこぶが溝の中に収まっているか・見た目が許せるか | 継ぎ目が滑る面に出る（擦れる）／上から見える切れ込み |
| `POST_W` | 1.6 | 柱（リブを横切る向き） | 試し刷り strip・基板の段 | 柱の強さ・基板の置けない場所 |
| `POST_L` | 5.0 | 柱（リブに沿う向き） | 同上 | 同上 |
| `FRAME_SEAM_GAP` | 0.1 | 左右の枠の間の隙 | 本番の枠を刷って合わせる | 継ぎ目の列のキャップが挟まる／隙が見える |
| `HOLDDOWN_H` | 1.4 | 中の押さえの足の高さ | 本番の枠を刷る。キーの縁を押し切って当たらないか | キャップの下面に当たる／ねじの掛かりが足りない |
| `HOLDDOWN_D` | 4.4 | 中の押さえの足の直径 | 同上 | 足が割れる／スイッチのランドに近づく |
| `BOTTOM_SHEET_T` | 0.5 | 底に貼るシートの厚さ | 利用者が買う物で決まる | 全体の厚さ・ねじの頭が出る量 |
| `COVER_CLEAR` | 0.15 | 電池の蓋（落とし込み式）と枠の口の隙（片側） | 蓋の試し刷り（docs/coupon-test.md 10 章）で、入るか・片方だけ押したときに端がどこまで浮くか | きつくて入らない／片側が大きく浮く（蓋だけ刷り直す） |
| `COVER_MAIN` | 2 | 本番の蓋にする組（歯と棒の上下の隙 0.3・つぶれる筋 0.50）。蓋 1 は 0.2・0.40、蓋 3 は 0.4・0.60 | 蓋の試し刷りで、利用者が 3 つを触って選ぶ | 留まらない（隙が 1 層目の太りで食われる）／がたつく・入れるのが固い（蓋だけ刷り直す） |
| `FOOT_REACH` | 0.4 | 比べる形（S・C）の足が穴の縁から出る量 | 試し刷り latch の 3〜6 番 | 本番の形には効かない |
| `FOOT_H` | 1.0 | 比べる形（S・C）の足の高さ | 試し刷り latch の 3〜6 番 | 本番の形には効かない |

**2026-10-04 に確定して外した値**: `SCREW_PILOT_D` = 1.6（利用者が試し刷り v2 で締めて決めた）・`PSW_NOTCH` = (10.0, 2.4, 2.0)（利用者が試し刷り v2 の (ii) で触った形）。
決定記録 2026-10-04-knob-out-pilot。

## 確定させる順番

1. 試し刷りで決まるもの（docs/coupon-test.md の記入表）
2. 基板の段で決まるもの（外形・柱）
3. 基板が届いてから測るもの（ステムの高さ・底を突くまで）
