ms0216/keyboard-foundry/projects/cckb/docs/provisional-values.md

# まだ実測していない値（cckb）

`spec.py` で `[暫定]` を付けた値の一覧。**tests/test_meta.py が名前と数値をコードと
突き合わせる**（文書を見て部品を買うので、ずれていると入らない物を買う。HHKB で
倍以上ずれていたことがある）。確定したら行を消し、コードのタグも外す（残ると落ちる）。

| 定数 | 現在値 | 何の値か | どうやって確かめるか | 外したときの影響 |
|---|---|---|---|---|
| `ANTISLIP_SHEET_T` | 0.5 | 底の四隅に貼る滑り止めシートの厚さ（くぼみ 0.4 より 0.1 出て接地） | 買うシートの型番を決め、ノギスで測る | 薄いと接地せずがたつく・厚いと浮く（くぼみの深さを直す） |
| `KEYCAP_GAP` | 0.525 | セルの境目からキャップの縁まで（キャップ 18.0 角） | キーキャップの段（自分で刷る）で決め、刷った物を測る | 角のふた・壁とキャップの隙間（1.0 以上を検査が見る）が変わる |
| `KEYCAP_TOP_T` | 1.0 | ステムの上面からキャップの上面まで = ステムの真上の膜（2026-09-28 利用者の決定で 1.2 → 0.6、**2026-10-03 利用者の決定で既定 1.0**: 0.6 は見積りでつばの上の輪 0.2 が縁の押しに割れる。決定記録 2026-09-28-keycap-skin §8） | `coupon_skin`（膜 0.6 / 0.8 / 1.0 の本番の 1u のキャップ）を静音のスイッチに 10 回抜き差しし、縁を押して、膜・つばの上の輪（0.2 / 0.4 / 0.6）が割れないか・筒が抜けないか。0.8 が割れなければ 0.8 に下げてよい | 全体の厚さ（キャップ上面 14.2）が変わる。0.8 にすると 14.0・つばの上の輪は 0.4 |
| `STAB_SCREW_HEAD_H` | 1.6 | スタビのねじの頭の厚さ（基板の下面から下へ。仕入れ先の図の断面を画素で。読みが 2 つ: 1.5〔監査 E 重要 2〕・1.6〔2 回目の V2 監査 E-6〕。大きい方） | 届いたスタビのねじをノギスで | 床の止まり穴の底まで 0.6（床の上面まで 0.2）。1.9 を超えると穴の底に 0.1 残らない |
| `STAB_SCREW_HEAD_D` | 3.85 | スタビのねじの頭の径（同。読み 3.7 / 3.85 の大きい方） | 同上 | 床の止まり穴 φ4.85（頭 ＋ 片側 `STAB_SCREW_POCKET_CLEAR` 0.5 = 位置のずれ ±0.275 ＋ 0.2）。刷った穴の縮み 0.2 とずれ 0.275 の最悪を重ねても、頭 φ3.9 までは縁に当たらない。超えたら `STAB_SCREW_POCKET_CLEAR` を広げて床を刷り直す（基板は変わらない） |
| `ANT_KEEPOUT_OUT` | 5.0 | アンテナの端から外（Alt の側）へ銅を抜く長さ | HHKB の「電池から 5mm」の実測を借りた。試作で RSSI を測る（rf-antenna.md の手順） | 短いと電波が弱る・長いと配線の場所が減る |
| `ANT_KEEPOUT_HALF_W` | 6.0 | 同、幅（XIAO の中心から ±） | 同上 | 同上 |
| `USB_PLUG_BODY_W` | 12.0 | 利用者が挿す USB-C プラグの樹脂の幅 | HHKB で利用者が手持ちのケーブル数本を測った最大。使うケーブルを測る | 樹脂が隣の物に当たる（いまは外に何も無い） |
| `USB_PLUG_BODY_H` | 7.0 | 同、厚さ | 同上 | 樹脂の下端が机に当たる（いま 4.37 の余裕） |
| `USB_SHELL_EXPOSED` | 1.0 | 挿しきったとき樹脂と口の間に見える金属 | HHKB 実機＋ケーブル 1 本の実測。使うケーブルで測る | 口を引っ込められる上限（いま 0.3 引っ込め） |
| `FLOOR_POCKET_CLEAR` | 0.4 | 床の内側の止まり穴（V2 の中心の突起 φ4.8・スタビの箱の下）を物の外形から広げる量（半径） | 試し刷りの小片で、突起・箱が穴の縁に触れずに入るか見る（突起は基板の穴 φ5.05 の中で 0.125 ずれ、基板はネジで 0.1 ずれ、刷った穴は縮む） | 狭いと突起・箱が床に乗って基板が浮く・広いと床の肉が減る |
| `SWITCH_COLLAR_D` | 7.9 | 静音の V2 のステムの周りのつば（ハウジングの上 0.40・上面 5.70）の径。図に数字が無く、上面図を縮尺で読んだ | 見本（静音 PG1353S）をノギスで | キャップの窪み（φ8.7 = これ ＋ 0.8。天板は窪みの所で膜より 0.4 薄い。膜 1.0 で 0.6・2026-10-03）がつばを避けきれないと、押し切りでキャップがつばに当たる（打鍵が硬く・静音の効きが変わる） |
| `PSW_TAB` | 0.4 | 電源スイッチ SS-12D00G3 の枠の爪が台座の下面から下へ出る量（本体はこの分浮く。図面に寸法が無く、図面の縮尺で 0.30〜0.39・秋月の写真で 0.36） | 部品が届いたらノギスで、基板に押し付けたときの基板の上面からレバーの先までを測る（名目 6.9） | レバーの先の高さ（ふたの上面との差・いま名目で 0.1 下）と、足の出（切る長さ）が変わる |

## 確定させる順番

1. 買う・刷る前に決まるもの（データシート・API で閉じるもの）
2. 部品が届いたら測るもの（ノギス。**定義と測定対象を一致させる**——「箱」と書いて
   測ったのが電極だった）
3. 組んでから測るもの

## 確定させたときの手順

1. spec.py の値を直し、`[暫定]` を外す
2. この表から行を消す（残ると検査が落ちる）
3. 根拠（測り方・日付・値）を docs/ のどこかに残す
4. `.venv/bin/pytest tests` と、形に関わるなら `tools/kb <機種> plate` / `pcb` を回す
