ms0216/keyboard-foundry/projects/cckb/docs/provisional-values-case.md

# まだ実測していない値（cckb のケース・キーキャップ）

`projects/cckb/case_spec.py` で `[暫定]` を付けた値の一覧。**tests/test_cckb_case.py が名前と数値を
コードと突き合わせる**（spec.py の [暫定] は provisional-values.md。ケースの段の値はこちらに分けた）。
確定したら行を消し、コードのタグも外す（残ると落ちる）。組の値は最初の数を書く。

| 定数 | 現在値 | 何の値か | どうやって確かめるか | 外したときの影響 |
|---|---|---|---|---|
| `INSERT_OD` | 3.2 | M2 熱圧入インサートの外径 | 買う品の型番を決め、図面かノギスで測る（3 回目の監査 軽微 4） | 基板の H3 の表の銅の禁止域（半径 1.9 ＝ 1.6＋0.3）がこの値に乗っている。外径 3.6 なら縁から銅まで 0.1、3.8 を超えると銅に触れる。下穴 `INSERT_HOLE_D` もこの値で選び直す |
| `INSERT_L` | 3.0 | M2 熱圧入インサートの長さ | 買う品の型番を決め、ノギスで測る | 下穴の深さ・ネジのかかり（いま右のふた 2.8・H3 1.9） |
| `INSERT_HOLE_D` | 3.0 | インサートの下穴 | `coupon_insert` の 2.9 / 3.0 / 3.1 に実物を熱圧入して選ぶ | 緩いと回る・きついと柱（肉 1.1）が割れる |
| `CAPTIVE_HOLE_D` | 1.6 | 電池のふたのネジを捕まえる膜の穴 | `coupon_insert` の膜 1.4 / 1.6 / 1.8 に M2 をねじ込んで、抜け落ちず・回せるものを選ぶ | 大きいとネジがふたから落ちる・小さいと膜が割れる |
| `PSW_SLOT_NAIL` | 1.0 | 右のふたの電源スイッチの穴を、レバーの動く向きの両端で伸ばす長さ（爪を差し込む場所） | ケースの試し刷りに部品を付けた基板を入れて、爪でレバーを両向きに動かせるか | 短いと爪が入らない・長いと穴が大きくなる（鞄の中の物が入りやすい） |
| `PSW_MARK_SIZE` | 5.0 | 右のふたの「ON」の刻印の文字の大きさ（Text の size） | 刷って読めるか（1 層目の潰れ） | 小さいと潰れて読めない |
| `ANTISLIP_PAD` | 12.0 | 滑り止めのくぼみの大きさ（12 × 6。2026-09-26 に V2 で 16 × 8 から: V2 の位置決めの長穴が最上段の中心の 5.15 下に来て、段 0|1 の帯が高さ 5.9 しか空かない。4 つとも同じ大きさ） | 買うシートを決めて切る大きさ | ネジの座ぐりとの取り合い・島と裏に出る物の隙（検査が見る）。大きくすると島がスイッチの足の下に入る |
| `STEM_CROSS_SLOT` | 4.15 | キャップの十字の穴（4.15 × 1.40。スイッチの十字 4.00 × 1.30 に +0.15 / +0.10） | `coupon_stem` の格子（幅 1.35〜1.50 × 長さ 4.10〜4.20）に静音の V2 を挿して、抜けず・割れず・ぐらつかない物 | きついと筒が割れる（腕の先の肉 0.675）・緩いとキャップが抜ける |
| `STEM_TUBE_OD` | 5.5 | 筒の外径（静音の窪み φ5.70 の中） | `coupon_stem` の 5.3 / 5.4 / 5.5 | 太いと窪みに入らない・細いと腕の先の肉が減る |
| `STEM_TUBE_L` | 3.0 | 筒の長さ（天板の下面から） | 見本の窪みの深さをノギスで（図に無い。標準 V2 の立体で約 4.3） | 長いと窪みの底に当たってキャップが浮く |
| `STAB_CROSS_SLOT` | 4.10 | スタビの十字の穴（4.10 × 1.36。スタビの十字 3.95 × 1.26 に +0.15 / +0.10・非公式の図） | `coupon_stem` のスタビの板 3 枚（幅 1.31 / 1.36 / 1.41・支点は本番の 23.8・切り欠き 1〜3 本）に届いたスタビを挿し、`coupon_stab_return` で軸が戻るか | きついと挿さらない・緩いとスタビがキャップから外れ、軸がキャップと一緒に戻らない。長さ 4.10 は変えない（台 φ5.1 との端の肉 0.5 = (5.1 − 4.10)/2。長くすると 0.4 ノズル 1 本を割る） |
| `STAB_SOCKET_GRIP` | 2.0 | スタビの受け口の台の高さ = 軸を掴む深さ（2026-09-26 に 0.45 から・監査 E 重要 1） | `coupon_stab_return` で、押し切って離したときスタビの両端の軸がキャップと一緒に戻るか（10 回） | **戻らなければ、まず `STAB_CROSS_SLOT` の幅を締める**（`coupon_stem` の 1.31 の板で戻るか見る。掴む強さを上げる方が先・2 回目の V2 監査 E-3）。それでも戻らなければ深くする（上限は軸の出 3.60 − 0.1。keycaps.stab_grip が落とす）。深いと挿すのが固い |
| `STAB_SLIDER_W` | 5.5 | スタビの箱の上面の口（スライダーの胴）の幅（仕入れ先の図の断面を縮尺で。組み立てモデル用） | 届いたスタビをノギスで | 口がこれより狭いと、押し切りで台（φ5.1）が箱に当たる |
| `STAB_SOCKET_BOSS_D` | 5.1 | スタビの受け口の台の径（口 5.5 − 片側 0.2） | `coupon_stab_return` で押し切りに擦れ・引っ掛かりが無いか。見本の口をノギスで | 太いと押し切りで箱に当たる・細いと十字の穴の端の肉（0.5）が減る |
| `KEYCAP_PLATE_T` | 1.0 | ステムから離れた所の天板の厚さ（2026-09-28。押し切って何にも当たらない所だけ。1u はハウジングの逃げがスカートまで届くので無く、1.5u 以上の両脇とスタビの上だけ） | 刷った 2.25u のキャップ（`coupon_stab_return` のキャップ）の縁を押して、たわみ・透けを見る。決定記録 2026-09-28-keycap-skin §3 の見積り（縁に 3N）と比べる | 厚いとスタビの箱（上面 5.00）に押し切りで当たる（上限 1.05。`keycaps.plate_levels` が落とす）・薄いと 2.25u の端がたわむ |
| `KEYCAP_SKIRT_H` | 1.0 | キャップの縁（スカート）の高さ | 刷って押し切り、どこにも当たらないか | プレートを使わない（2026-09-26）いまは、押し切りでスイッチが先に止まり、縁の下に当たる物は無い。プレートを戻すと、高すぎれば縁がプレート（7.2）に当たる（1.8 空く） |
| `SW_RECESS_FLOOR` | 4.3 | 静音の V2 の十字の窪みの底（基板の上面から・検査用のモデル） | 見本をノギスで | 筒の長さの余裕（いま 1.3） |
| `STAB_SHOULDER_H` | 3.0 | スタビの箱と爪の間の肩の高さ（検査用のモデル。側面図を縮尺で） | 届いたスタビをノギスで | プレートの羽の開口の大きさの検査（肩はプレートを貫く）。**プレートを戻したときだけ** |
| `STAB_WIRE_Z` | 1.47 | スタビのワイヤの中心の高さ（同） | 同上 | ワイヤがプレートの帯を通る検査（**プレートを戻したときだけ**）・基板と床の間の干渉 |
| `STAB_CLAW_TOP` | 1.8 | スタビの爪の上端（同） | 同上 | 同上 |
| `CELL_Z_IN_HOLDER` | 1.3 | 電池の下面が基板の上面から上がる量 | ホルダの実物に電池を入れて測る（図面 MY-CP-0085 に無い） | 電池とふたの隙（いま 1.3） |
| `USB_PLUG_INSERT` | 6.5 | プラグの金属がメスの口から奥へ入る長さ | 使うケーブルで測る | メスの奥行 7.3 との取り合い |
| `DRIVER_D` | 3.0 | 下からネジを回す精密ドライバーの軸の径 | 手持ちのドライバーを測る | 座ぐり φ4.2 に入らないと回せない |
| `PSW_NAIL_REACH` | 0.5 | 爪が電源スイッチのレバーの横の面にかかる長さ（レバーの先から下へ） | 試し刷りで爪がかかるか | 爪がかからない |
| `NAIL_T` | 1.0 | 爪の厚さ（レバーの横に入る箱・レバーの動く向き） | 同上 | 同上 |
