ms0216/keyboard-foundry/projects/cckb-click/docs/decisions/2026-10-04-cover-latch.md

# 電池の蓋は、道具なしで上から落とし込む形にする（電池が押す向きと、外れる向きを分ける。基板は変えない）

- **日付:** 2026-10-04（作業は 10-05 にかけて。**v2 = 独立の見直しを受けて直した形**: 下の「見直しで分かったことと、直したこと」）
- **状態:** 決定（形）。**刷って確かめるまでは「立体と G-code では成り立つ」まで**（蓋の試し刷り: docs/coupon-test.md 10 章・蓋 3 つ）。門 #34b は閉じていない。
  **利用者の条件「しっかり付いた蓋を、人がわざと外したときだけ」のうち、「わざと」の部分は、形だけでは満たし切れていない**（下の「満たせていないこと」）
- **決めた人:** 利用者（道具なし・しっかり留まる・電池は CR1632 のまま・枠の外形を太らせない・押しても振っても電池が出ない・人が蓋を外したときだけ出せる・
  基板は、蓋が成り立つために要るなら変えてよい）。形と寸法は Claude が測って出した（刷って直す値は `[暫定]`）

絵: `build/cckb-click/cover_latch.png`（しくみ・開け方・閉め方・電池の替え方）・`main_corner.png`・`assembly_main/corner_front.png`。
試し刷り: `build/cckb-click/coupon_corner_plate_n04.gcode.3mf`・見る所は `coupon_cover_howto.png`・スライスした線は `slice_cover.png`。
見直しの絵（見直した人が作った物）: `build/cckb-click/study/review_cover_states.png`・`review_gcode_cover2_tips.png` ほか。

## 1. なぜ決める必要が生じたか

- ねじで留める蓋（決定記録 2026-10-04-cover-screw）を見た利用者が、**道具が要る蓋は使えない**と決めた（「出張先で電池が切れたときにドライバーが要るのは致命的」）。
- 同じ日に分かった事実（open-gaps P25）: 電池クリップは電池を上から押さえるだけで、手前の止めが無い。**電池を手前へ止める物は蓋だけ** = 蓋は飾りではなく、力を受ける部品。
- 差し込み式の蓋は 4 つ刷って 4 つとも使えなかった（v1 の掛かり 0.25・v2 の折り返しばね 0.60／細い腕 0.45／筋）。計算は 4 回とも「留まる」と言っていた。
  共通の弱さ: **同じ小さな爪が、(a) 蓋の抜ける向きの力を受け、(b) 刷りの誤差 0.1〜0.15 と隙 0.1 の中で掛かる、の両方を、長さ 6.3 以下の腕でやっていた。**

## 2. 事実はどうか（測った・読んだもの。出所を書く）

| 事実 | 値 | 出所 |
|---|---|---|
| 電池 CR1632 | φ16.0（15.75〜16.00）× 3.2（3.00〜3.20）・**1.8 g** | Energizer のデータシート CR1632（Form No. 1632NA0618。2026-10-05 に取り直した） |
| 電池の蓋の作り方の注意 | 「道具（ねじ回し・硬貨）で開ける形」か「手で、同時に行う 2 つの独立した動きで開く形」に | 同じデータシートの Safety (2)（子どもの誤飲の注意書き）。**この蓋は、これを満たしていない**（指 1 本の「押して上へずらす」は 1 つの動きに数えられる: 見直しの指摘 2） |
| クリップ MY-1632-03-R | 板厚 0.25・高さ 4.0・止め（幅 6.35）は奥だけ・電池を押さえる舌 2 本・**手前の止めも保持力の値も無い**・未注の公差 ± 0.25 | 図面 MY-CP-0247（build/cckb-click/ds_MY-1632-03-R.png） |
| 止めに当てた電池 | 中心 (122.0, −40.915)・手前の縁は枠の外面から 1.71 内 = **手前の壁（厚さ 3.0）の中に 1.29 入り込んでいる** | 立体（図面の寸法から） |
| クリップの板の口の側の端 | 外接の矩形で、枠の外面から 2.85。その手前だけが、蓋の足を上から下まで置ける場所 | 図面・立体 |
| 落下の加速度 | **1500 G・半波 0.5 ms を仮定に置く** | JEDEC JESD22-B111（携帯機器の部品の基板落下試験）の条件 B。携帯機器を落としたときの厳しい側の値として借りた。**キーボードを実際に落として測った値ではない** |
| 材料 | 曲げ弾性率 2750 MPa・曲げ強さ 76 MPa・引っ張り強さ 35 MPa・密度 1.24 | Bambu PLA Basic の TDS。**刷った物を測った値ではない** |
| 1 層目の太り | 0.2〜0.3（この機種がほかの所で見ている量。スライスの設定に、太りの補正は入っていない） | spec の面取りの注記・見直しの G-code の絵（1 層目の線が名目の縁まで来ている） |
| 参考にした実物 | 屋根ごと外れる板を手前から滑らせる蓋（板の左右の縁に段・金具の舌が見える窓） | 利用者が示した写真（X の投稿・2026-09-30）。寸法は読めない |
| 刷り | A1 mini・0.4 ノズル・層 0.1・PLA。刷りの誤差は 0.1〜0.15 と見る | 利用者の試し刷り 4 回（docs/coupon-test.md 7・8 章） |

## 3. 効く条件（**候補を並べる前に全部書く**）

| # | 条件 | 実データ（決めた形 v2 で） | 何で確かめたか（外 / 自分の生成物） |
|---|---|---|---|
| 1 | 道具なしで開け閉めできる | 棒 2 本を爪で押し込みながら持ち上げる／閉めるのは上から押すだけ | 立体（押し込んだ形を 0.25 おきに上へ動かす）。**爪でできるかは刷って見る** |
| 2 | 電池の止めは、形で止まる（ばね・摩擦を通らない） | 電池 → 蓋の足 → 蓋の胴（横向きの梁）→ 耳の 45° の面 → 枠の溝の手前の壁。棒を切り取った蓋でも同じ所で止まる | 立体（電池と蓋を動かす）。応力は、立体から測った断面で計算 |
| 3 | 電池が押す向きと、蓋が外れる向きが違う | 押す向き = 手前・外れる向き = 上（直角） | 立体（棒を押し込んだ蓋は、上にだけ動く） |
| 4 | 蓋を付けたら、電池はどの向きにも出ない | 10 の向きとも 1.0 以内で枠・蓋・クリップ・基板に当たる（手前 0.23・上 0.5） | 立体。クリップは図面の名目の形（外） |
| 5 | 蓋は、わざとでないと開かない | 留めは直角の面。**棒 1 本を押しただけでは開かない**（その側の端が 1.1 浮くまで）。**2 本にまたがる物で押しながら上へ擦れば開く = 形では防げていない**。押す力は 2 本で 2.2 N | 立体（姿勢を振って探す）・計算。**刷って、擦る・振る・落とすを見る** |
| 6 | 内側へ落ちない・倒れない | 平行に 6 の向き・回す 5 つの軸 × ± 4〜12° のどれも、枠か基板に当たる | 立体（回す） |
| 7 | 枠の外へ出る物が無い・手前の壁を厚くしない | 上面は枠と面一・手前の面は外面の 0.25 内（溝に座っても 0.04 内）。枠の外形・壁の厚さ 3.0 は変えない | 立体 |
| 8 | 蓋を外せば、電池を指で出せる | 歯の間 17.0 を電池 16.0 が通る・手前へ 22 mm 何にも当たらない | 立体 |
| 9 | サポート無しで刷れる | 枠: 上面をベッドに。蓋: **手前の面をベッドに**（宙に浮くのは、幅 0.7・長さ 1.6〜1.8 の橋 2 つだけ） | 立体と G-code（Bambu Studio 2.8.2・外）: 切れ目に線が通っていない |
| 10 | 刷りの誤差 ± 0.15・1 層目の太りでも掛かる | 耳: 1.7 → 寄り切って 1.1 以上。棒の先と歯: 左右 0.85・前後 0.73 → 寄り切って 0.55・0.59。ベッドの面の縁は全部 0.25 落とした。**歯との上下の隙は、蓋 3 つで 0.2／0.3／0.4 に振る** | 立体（蓋を寄せて、重なりの大きさを測る） |
| 11 | 50 回以上の開け閉め | 外すときの棒の付け根のひずみ 1.49 %（上限に置いた 1.52 % いっぱい）。行き過ぎの止めで 1.68 % まで。閉じている間は棒に力が掛からない | 計算。**回数は刷って見る**（試し刷りで 20 回） |
| 12 | 電池・クリップ・基板・部品・キャップに当たらない | 重なり 0。足はクリップの板の下へ入れない | 立体（クリップは図面から作った形 = 外） |
| 13 | −の裸の銅に触れない・電池の缶（＋）を何かに短絡させない | 蓋は樹脂だけ。足は電池の道（表に銅の無い範囲）に立つ | 立体・基板の検査 |
| 14 | がたつかない | 耳の奥の面のつぶれる筋が、蓋を手前へ寄せる（しめしろ 0.04／0.14／0.24 を蓋 3 つで振る）。**上下の遊び 0.2〜0.4 は、摩擦で押さえるだけ** | 立体。**固さは刷って見る** |
| 15 | 無くしにくい（任意） | **満たしていない**（つなぎ留める穴は作れなかった）。本番の板に予備を 1 つ並べた | — |
| 16 | 基板を変えない（変えてよいが、費用が掛かる） | 変えない（b442b865… のまま）。穴 H30・H31 は使わない | 板のハッシュ |

## 4. 影響範囲（力の流れに沿って端から端まで）

- **電池が手前へ押す力**（1500 G で 26.5 N）: 電池の缶の縁 → 蓋の左右の足の、内の奥の角（0.23 動いた所で当たる）→ **蓋の胴が横向きの梁として曲がる**
  （力の入る所が、受ける耳より 6.15 内にある = 4 点曲げ・曲げモーメント 81 N·mm）→ 耳の付け根の柱（上から下まで）→ 耳（45° のくさび・上から下まで 5.0）
  → 枠の溝の斜めの面（面圧 1.6 MPa）→ 手前の壁。
  **いちばん苦しいのは蓋の胴の真ん中**（立体から測った断面 4.4 mm²）: 手前の縁の引っ張り 23.7 MPa（引っ張り強さ 35 の 0.68 倍）・奥の縁（上の板の端・厚さ 0.7）の圧縮 34.1 MPa
  （曲げ強さ 76 の 0.45 倍）。**余裕は 1.5 倍で、大きくない**（750 G なら 3 倍）。上の板は、クリップの上の隙 0.2 のために 0.7 より厚くできない。
- **蓋が上へ抜ける力**（蓋の重さ 0.22 g × 1500 G = 3.2 N・指でこじる力）: 蓋 → 棒の先の下の硬い受け（隙 0.2）→ 棒の先 → 枠の歯の下面（直角）。
  歯は枠の上面から生えた 1.0 × 1.0 の角柱（右は高さ 2.6・左は 1.2）。こじる力が大きいと、先に壊れるのは歯か棒の先。
- **枠**: 右手前の角だけ変わる。口の幅 19.0・口の左右に溝（先に壁 = 左右の案内）・手前の角に歯 2 つ・溝の奥に壁。→ **右の枠は刷り直し**（まだ本番は刷っていない）。
- **基板**: 変えない。穴 H30・H31 は残る（使わない）。底のシートは、この 2 つの所に穴を開けない。
- **ねじ**: 20 本（＋ 予備の穴 2）。
- **組み立て**: 枠を外すとき、蓋は先に外す（蓋は枠の歯に掛かっている）。

## 5. 決めたこと（v2）

1. **蓋は上からまっすぐ落とし込む。**外れる向きは上だけ。
2. **電池の止め**: 蓋の左右の耳（45° のくさび・左右へ 1.7・先は平ら）が、口の左右の壁の溝に入る。足（幅 5.3）の内の奥の角が電池を受ける（隙 0.2）。
   耳は、蓋の側面のすぐ内の柱（幅 0.7・上から下まで）で胴につながる。上の帯（基板の上 3.9 から上）は、足の奥の端まで詰まった梁。
3. **留め**: 口の手前の左右の角に、枠から歯（1.0 出る・厚さ 1.0）。蓋の手前の面の 2 本の棒（高さ 1.0・厚さ 1.05・長さ 13.4）の先が、歯の下に入る（直角の面）。
   棒の先は 1.2 で柱に当たって止まる（行き過ぎの止め）。棒の先の下には、0.2 の隙で硬い受け。
4. **がたつきを取る**: 耳の奥の面に、縦のつぶれる筋 2 本ずつ。溝の奥の面に当たって、蓋を手前（耳が座る向き）へ寄せる。
5. **1 層目の太りの逃げ**: 蓋の手前の面（ベッドの面）の横の縁を、全部 0.25 落とす。
6. **刷って決める寸法**: 蓋 1（歯との隙 0.2・筋 0.40）・蓋 2（0.3・0.50）・蓋 3（0.4・0.60）。本番の候補は蓋 2（`COVER_MAIN`）。棒は 3 つとも同じ。
7. **基板は変えない。**

## 見直しで分かったことと、直したこと（2026-10-05・独立の見直し。前の形 = コミット e4b7cdd）

| # | 分かったこと（自分でも確かめた） | 直したこと | 残っていること |
|---|---|---|---|
| 1 | 蓋のベッドの面の縁のうち、**歯のすぐ下の棒の先の上の縁**と**足の下の縁**が落としてなかった。歯との隙 0.2 が 1 層目の太りで食われると、棒が歯の下へ戻れない（3 つの蓋に共通） | 横の縁を全部 0.25 落とした。**蓋 3 つで、歯との隙を 0.2／0.3／0.4 に振った**（前は 3 つとも 0.2） | 刷って、どの隙で留まるかを見る |
| 2 | **棒を 1 本押すだけで、その側が傾いて上がった**（同じ探し方で 1.8 以上。見直した人の探し方で 2.1〜3.0）。前の検査は、まっすぐ上へ動かすだけだった。押す力も 0.25〜1.5 N と小さい。「同時に行う 2 つの動き」には当たらない | 耳の先を平らにして、溝の先の壁と隙 0.15 で向き合わせた（左右の案内）→ **棒 1 本を止めまで押しても、端が上がるのは 1.13**（上限 1.5 と置いて検査にした）。行き過ぎの止め・付け根の丸み・棒を高さ 1.0 に（力 2.2 N）。電池メーカーの注意書きを根拠に使うのをやめた | **下の「満たせていないこと」** |
| 3 | 落下で棒が動く量を、静的に見ていた。固有の振動数（1.0 厚で約 1300 Hz）と半波 0.5 ms の揺れの倍率 1.7 を入れると、前の蓋 1（厚さ 0.8）は自分の仮定で外れる・蓋 2 は余裕 1.3 倍 | 棒を 1 種類（厚さ 1.05・1407 Hz・倍率 1.75）に。つぶれる筋で蓋を座らせ、外れる量を 1.06 に → 揺れ 0.51 に対して **余裕 1.9 倍**（蓋が奥へ寄り切っていれば 1.5 倍・棒が 0.15 薄く刷れれば 1.4／1.1 倍） | 余裕は 2 倍に届かない。棒が一瞬外れても、その瞬間に蓋が「歯との隙」より多く浮かなければ戻る。実物で落として見る |
| 4 | 耳は、幅 0.53 の首と上の板（0.7）だけで胴につながり、右の耳は棒の高さで離れ小島だった。「面圧 1.3 MPa」は力の道を単純にしすぎていた | 耳の付け根に、上から下までの柱。上の帯を足の奥まで詰めた梁に。**応力を、立体から測った断面で出す検査にした**（引っ張り 23.7・圧縮 34.1 MPa） | 余裕 1.5 倍（上の §4）。上の板を厚くできない限り、これ以上は増やせなかった |
| 5 | 押さえが無い（上 0.2・前後 0.36・左右 0.15〜0.2 の遊び）・閉めるときの斜めの面の余りが 0.1・開けるには爪が要る・0.2 g で無くしやすい・上の手前の縁もベッドの縁 | つぶれる筋・歯の上の斜め 0.6 → 0.8（余り 0.5）・手順を「爪で」に・予備を本番の板に並べた・上の縁も落とした | 上下の遊びは摩擦で押さえるだけ。つなぎ留める穴は作れなかった（穴を開けられる厚い所が、電池の空間に面している） |
| 6 | 棒の先と歯の掛かりの検査が、設計値の足し算だけだった | 蓋を寄せて持ち上げ、**重なりの大きさを立体で測る**検査にした | — |

### 満たせていないこと（**利用者が決めること**）

- **爪 1 つで開く。**2 本の棒は上下に並んでいて、真ん中では 0.4 の切れ目を挟んで隣り合う。0.4 より太い物が 2 本にまたがって 0.43 押し込み、押したまま上へ動けば、蓋は開く。
  力は約 2.2 N（キーボードの重さ 約 1.9 N と同じ桁）。**鞄の中で、角のある物が手前の面を下から上へ強く擦れば、開きうる。**
- **端を 1 つずつ、2 回に分けても開く。**棒 1 本を押して、その側を 1.1 持ち上げると、棒の先が歯の奥の面に寄り掛かって、浮いたままになりうる。そこからもう 1 本を押せば開く。
- **なぜ形で防げなかったか**（測った範囲で）:
  - 押す力を上げるには、棒を厚く・短くする。厚さ 1.05 で、外すときの付け根のひずみが、上限に置いた 1.52 % いっぱい。3〜5 N にするには、棒の高さを 2 倍にするか（2 本を上下に並べられなくなる）、ひずみを 2 倍にする
  - 棒の真ん中を押せなくする物（棒の手前の覆い・奥の止め）は、蓋を手前の面をベッドに刷る限り、棒の上に宙に浮く（刷れない・棒に張り付く）。ほかの向きに刷ると、棒そのものが宙に浮く
  - 片側だけ浮く量は、高さ 5 の蓋と左右の隙の合計 0.3 で決まる（18.7 × 0.3 ÷ 5 = 1.1）。上から落とす形の限り、0 にはならない
- **利用者の選べる道**: (a) この蓋を刷って、擦る・振る・落とすを試し、足りるかを見る。(b) 足りなければ、樹脂のばねをやめる: 小さな磁石か金属のばね（**買う物が増える**）、
  または硬貨で回す留め（**道具に当たるか**は利用者が決める）。(c) 蓋の形から考え直す（下の表の「屋根ごとの戸」は、電池の力を爪が受ける形になる）。

## 検討して捨てた案（同じ条件で比べた）

| 案 | 捨てた理由（測った数） |
|---|---|
| **屋根ごと外れる戸を、手前から滑らせて入れる ＋ 長い爪**（利用者の写真の形） | **電池が押す向き = 戸が抜ける向き**なので、爪が電池の力 26.5 N を受ける。屋根の板の中の腕（幅 1.0 × 高さ 2.0 × 長さ 12）で計算すると: 付け根が奥なら腕は圧縮で、座屈する力が 7.4 N。付け根が手前なら引っ張りだが、爪の出 1 mm の偏りで先が外れる向きに 4.3 mm 曲がる計算。爪を外す動きは「上面を押す ＋ 手前へ滑らす」= **鞄の中で上面を押されながら、電池が中から押すと開く向き**。屋根はクリップの上で厚さ 0.7 しか無い |
| **屋根ごと外れる戸を、奥の壁に差し込んで手前を押し下げる**（奥の 4.9 の壁を使う） | 奥の差し込みは屋根（基板の上 3.0 から）の下にしか作れず、回る軸の高さが 3.0 になる。電池の力（高さ 1.6）の線が軸の 1.4 下を通る → 電池が押すと戸が開く向きに 36 N·mm。棒は戸を平らに刷ると橋になって刷れない。**大きくて無くしにくい・奥は形で留まる・片側だけ浮かない、は良い所**（見直しを受けて、もう一度比べた: 留めが 1 か所になり、指 1 本で開くのは同じ） |
| 落とし込み ＋ 奥の縁を枠の下に引っ掛ける（手前を回して下ろす） | 片側だけ浮く動きを、形で止められる（奥の左右の引っ掛け ＋ 手前の棒 1 本で、3 点が押さえる）。しかし耳（高さ 5）は、溝の中で前後に 2° しか傾けられない（傾けるには、溝の手前の面を上へ向かって逃がす = 電池の力が蓋を持ち上げる向きの面になる） |
| 落とし込み ＋ 棒を左右に 1 本ずつ・真ん中に硬い柱（真ん中を押しても開かない） | 棒の長さが 8.4 になり、外すたわみ 1.1 で付け根のひずみ 2.6 %（上限 1.52 %）。歯の厚さを 0.5 に減らせば成り立つが、掛かり 0.5 は前の 4 つと同じ寸法 |
| 落とし込み ＋ 歯を段々にする（半分浮いても、上の段に掛かり直す） | 棒の先を、段に合う斜めの形にする要がある（平らな先は、下の段の斜面に寄り掛かって、上の段の下へ入れない）。左の歯は高さ 1.2 で 1 段しか取れない |
| 落とし込み ＋ 棒 1 本（片側だけ留める）／片側は固定の爪（傾けて入れる） | 留めていない側が 1.1〜2.2 浮く／高さ 5 の蓋は 3.4° しか傾かないので、固定の爪の掛かりは 0.3 以下 |
| 落とし込み ＋ 足をクリップの板の下まで伸ばす | 作って測った: 上へ 0.5 持ち上げた所で板に当たる |
| 上から落としてから横へずらす（差し込み錠） | 固定の掛かりを作れるのは片側だけ（もう片側は、ずらすと掛かりから出ていく）。口の脇に、ずらす分 1.2〜1.5 の隙間が見える |
| 基板の穴 H30・H31 に、蓋の足のピンを落とす（電池の力を、足の真下で受ける = 胴の曲げを減らす） | ピンの手前の面は、刷る向きで宙から始まる（斜めにすると、電池の力が蓋を持ち上げる）。枠と基板の位置のずれ（ねじ穴の遊び 0.1〜0.2）と、耳の座りが取り合う |
| 差し込み式のまま、掛かりを増やす／ねじで留める | 前者は 4 つ刷って 4 つとも使えなかった。後者は道具が要る（利用者が退けた） |
| **基板を変える**（穴・切り欠き・クリップの位置） | 測った範囲では、樹脂のばねの限り、得る物が無い（棒の力を決めているのは、ひずみの上限）。磁石や金属のばねを使うなら、置き場所のために変える所が出うる（そのときに決める） |

## この決定が乗っている前提（**動いたら読み直す**）

- クリップが MY-1632-03-R のまま・位置 `CLIP_AT`（足の奥の端・電池の縁の位置・上の板の高さが、これで決まる）。電池を CR2032 にするなら、口の幅から全部やり直す。
- 手前の壁の厚さ 3.0（`PLATE_MARGIN_Y`）。歯 1.0 と、耳の溝が、この中と、そのすぐ奥にある。
- 蓋を**手前の面をベッドに**刷ること（上面をベッドに刷ると、棒と下の帯が宙に浮く: 検査が見ている）。
- 刷り方 `cckb-click precise 0.10 @A1M 0.4`（切れ目 0.4・棒の先の下の隙 0.2 が線で埋まらないことは、この設定の G-code で見た）。
- PLA の値（TDS）と、落下の仮定 1500 G・0.5 ms。**どちらも外から借りた数で、この蓋を測った値ではない。**

## 覆す前に読むこと

- 棒を厚くしたい・短くしたい（押す力を上げる・落下に強くする）: 厚さ 1.05 で、ひずみが上限いっぱい。`tests/test_cckb_click_case.py` の「棒の数」の検査が落ちる。
- 足を奥へ伸ばしたい: クリップの板の下に入ると、上へ抜けない（検査 `under_clip`）。足を狭くすると、電池が足より先に棒・下の帯に当たる。
- 耳の面を平らにしたい: 蓋を刷るとき宙に浮く。耳の先の平らな面を無くすと、片側が 1.5 より上がる（検査が見ている）。
- 歯を大きくしたい: 歯の間 17.0 が電池 16.0 の道。右の歯は電池の高さ（3.2 まで）に掛かっている。
- 上の板を薄くしたい: 蓋の胴の応力が 40 MPa を超える（検査が見ている）。

## まだ決めていないこと・確かめていないこと

| 項目 | 決められない・確かめていない理由 |
|---|---|
| **刷った蓋で、留まるか・擦っても振っても落としても外れないか・爪で開けられるか・何回もつか** | 刷っていない。計算は前の 4 つで外れた。蓋の試し刷り（docs/coupon-test.md 10 章）で見る |
| **この留め方で足りるか（爪 1 つで開く・力が小さい）** | 利用者が、試し刷りを擦って・振って決める。足りなければ、上の「利用者の選べる道」 |
| 歯との隙・つぶれる筋（蓋 1・2・3 のどれか） | 利用者が触って選ぶ |
| 落下で棒が一瞬引っ込むか | 計算の余裕は 1.1〜1.9 倍（上の表の 3）。実物で落として見る |
| 蓋の胴・耳の付け根が、電池に強く押されて白くならないか | 計算の余裕は 1.5 倍（1500 G の仮定で）。試し刷りで、電池の代わりを強く押して見る |
| 本物のクリップ・電池で、足と電池の隙 0.2・上の板とクリップの隙 0.2 が足りるか | 試し刷りの当て板には、クリップの板の代わりが無い。クリップの上面は公差の端で 4.35（上の板の下面 4.3 より上）になりうる。基板が届いたら見る |
| 歯（右は高さ 2.6・左は 1.2）が、こじる力で折れないか | 刷って見る。折れたら右の枠を刷り直す |
| つぶれる筋が、何回の抜き差しまで効くか | 刷って見る（筋は、つぶれて低くなる） |
| 門 #34b を閉じるか | **利用者が、試し刷りを触って決める** |
