ms0216/keyboard-foundry/projects/cckb-click/docs/decisions/2026-10-04-coupon-v2.md

# 試し刷り v2: ねじの下穴・電源スイッチの位置・蓋の留め方を、刷って決め直す

- **日付:** 2026-10-04
- **状態:** **結果が出た**（2026-10-04 に利用者が刷って試した）: 下穴は φ1.6・電源スイッチは (ii) 0.75 外・蓋は 3 つとも使えない（考え直す
  → ねじで留める形（決定記録 [2026-10-04-cover-screw](2026-10-04-cover-screw.md)）を経て、道具なしの落とし込み式に決まった: 決定記録 [2026-10-04-cover-latch](2026-10-04-cover-latch.md)。**蓋 3 つの形と検査は、そのときコードから消した**）。
  決めたことは決定記録 [2026-10-04-knob-out-pilot](2026-10-04-knob-out-pilot.md)・結果そのものは docs/coupon-test.md 8 章「結果」。
  ここは、何を試すことにしたかと、その理由の記録（下の「いまの位置」は、この記録を書いた時の位置 = 本体が縁から 2.5 の位置のこと）
- **決める人:** 電源スイッチの位置と蓋の見た目は利用者。下穴の径と蓋のばねの形は、刷った結果で Claude が出す

## 1. なぜ決め直すか（利用者が刷った結果・2026-10-04）

| 何 | 結果 | 記録 |
|---|---|---|
| ねじ（下穴 φ1.8・M2×4 の小ねじ） | 入るが、最後まで締めると空回りする。割れは無い | docs/coupon-test.md 6 章の「結果」 |
| つまみ | 動かせるが奥に入りすぎ | 同 7 章 |
| 電池の代わり | 楽に出し入れできる（クリップのばねが無いので、本物の固さは分からない） | 同 |
| 蓋 | 留まらない（載っているだけ・傾けると落ちる） | 同 |

## 2. 事実（測った物）

| 何 | 値 | 何で確かめたか |
|---|---|---|
| M2 並目: おねじの外径・めねじの内径 | 2.0・1.567（山の高さ 半径 0.2165） | 外: ISO 724（検索で確かめた値） |
| φ1.8 の下穴の掛かり | 半径 0.10（46 %） | 上の値から。G-code の下穴の外周の線は 1.76〜1.79 を空けていた |
| v1 の蓋の山 | 設計 0.25。線では、頂まで届くのは 1 層（0.1 mm）・前後 2 層は 0.10 | v1 の G-code（Bambu Studio）を読んだ |
| v1 の蓋の上下の遊び | 下へ 0.1・上へ 0.15。下がると掛かり 0.15 | 立体（検査 `test_v1_cover_diagnosis…`） |
| 指先（半径 7.5 の硬い球・机の上）が、つまみの先より奥へ入る量 | v1 −0.22・切り欠きを広げて −0.03・0.75 外へ寄せて +0.16 | 立体を当てた（`click_coupon_v2.finger_reach`）。**球の半径は仮定** |
| M2 のナットの二面幅 | 4.0（六角 ISO 4032・四角 DIN 562） | 外: 販売者の規格の表（検索） |
| ねじの中心 → キーの穴の縁 | 1.6 | 立体（下穴 φ1.8 の肉 0.70 ＋ 半径 0.9） |

## 3. 効く条件

| # | 条件 | 数 | 何で確かめたか |
|---|---|---|---|
| 1 | ねじが空回りしない | 掛かり 0.15〜0.22（φ1.7〜1.5） | 計算だけ。**効くかは v2 を締めないと分からない** |
| 2 | 壁が割れない | 内の肉 0.77〜0.87／薄い所 0.55〜0.65。ねじの外径の外は 0.6／0.39 で変わらない | 立体。割れるかは v2 |
| 3 | 基板を変えない（できれば） | 下穴だけなら枠の直し。ナット・インサートは穴を 0.8 以上外へ = 基板 | 立体・規格 |
| 4 | 指でつまみを動かせる | 上の表 | 立体（物差し）。実物の指では v2 |
| 5 | JLC の「本体と縁は 2.5 以上」 | (i) 2.50・(ii) 1.75 | 板の寸法（(ii) は割る） |
| 6 | 蓋が留まる（刷る誤差 0.1〜0.15 と遊び 0.1 を引いても掛かる） | 蓋 1: 0.60 → 残り 0.35 以上・蓋 2: 0.45 → 0.2 以上 | 立体から測った掛かり。留まるかは v2 |
| 7 | ばねが折れない | ひずみ 0.71 %／0.84 %（刷り上がりの太りで 0.77 %／0.96 %）・許容 1.0 % | 骨組みを解いた値（片持ち梁の式と突き合わせ）。回数は v2 で 20 回 |
| 8 | 0.4 ノズルで刷れる | 腕は線 2 本／1 本・山の頂まで 3〜4 層・隙間に線が無い | スライスした G-code（Bambu Studio・OrcaSlicer） |
| 9 | 枠と面一・電池とクリップに触れない・道具なしで外せる・蓋が無くても使える | — | 立体の検査 |

## 4. 影響範囲

- **ねじ → 壁 → キーの穴 → キャップ**: 下穴を変えても穴の位置は同じ。ナットにすると壁からはみ出して、キャップの胴に当たる
- **つまみの位置 → スイッチの足跡 → 電池の＋の線（VBAT_IN・VBAT_SW の右の端）・C_BAT・GND のビア → JLC の規約 → 監査**:
  (ii) にするなら、前に 1.75 動かしたときと同じ所を直して、監査し直す（決定記録 2026-10-04-switch-cover）
- **蓋 → 枠の口の上の壁の溝 → 右の枠**: 蓋 1・2 は溝を深くした枠が要る。基板には触れない

## 5. 試す物（v2）と、捨てた案

v2 の中身は docs/coupon-test.md 8 章の表。蓋の留め方で**捨てた案**:

| 案 | 捨てた理由（数） |
|---|---|
| v1 の腕のまま掛かりを 0.6 に | ひずみ 2.1 %（許容 1.0 %） |
| 長い腕 1 本（口の幅いっぱい・山は片側） | ひずみは 0.6 % で足りるが、山の無い側が留まらない: 蓋が山を軸に回って、反対の端が約 1.1 mm 開く（上の板の案内 4.35 と隙 0.15 × 2 から） |
| くさび（先細り）で擦り合わせる | 面一にならない: 刷る誤差 0.1 で、止まる深さが 0.6〜2.9 mm 変わる（傾き 10°〜2°） |
| 手前の面が垂直の山（引いても抜けない・押して外す） | 蓋を手前の面を下にして刷ると、垂直の面は宙に張り出す（0.75）。刷れない |
| 上の板の中の腕・枠の屋根の中の腕 | 上の板の下はクリップまで 0.2 しか無い（たわめない）。枠の側に付けると、傷むのが 4 時間かけて刷る枠になる |
| 横へ滑らせて掛ける | 口を蓋より 0.8 広くする = 手前の面に 0.8 の隙が見える |
| ナット・熱圧入インサート（ねじ） | 壁から 0.4 はみ出す。基板の変更になる（下穴の 3 通りが全部だめだったときの手） |

## この記録が乗っている前提

- 刷り方は 0.4 ノズル・層 0.1・Bambu PLA Basic（腕の太さ 0.7 = 線 2 本・0.45 = 線 1 本）
- ねじは M2×4 の小ねじ（タッピングではない）。掛かりの長さ 2.4
- 電源スイッチは MSK12C02・電池クリップは MY-1632-03-R

## まだ分からないこと

| 項目 | なぜ |
|---|---|
| どの下穴で効くか・薄い壁が割れないか | 刷って締める（v2 の A） |
| 指でつまみに届くか・(ii) にするか | 刷って触る（v2 の B）。決めるのは利用者 |
| どの蓋が留まるか・何回もつか | 刷って 20 回抜き差し（v2 の C） |
| 本物の電池クリップでの電池の出し入れの固さ | 基板が来るまで分からない（P2） |
