ms0216/keyboard-foundry/projects/cckb-click/docs/decisions/2026-10-04-cover-screw.md

# 電池の蓋は、基板の下から M2×4 のねじ 2 本で留める（基板は変えない）

> ⚠️ **先に読むこと（2026-10-04・同じ日に撤回）**: 利用者が、この蓋を見て「**道具が要る蓋は使えない**（出張先で電池が切れたときにドライバーが要るのは致命的）」と決めた。
> 蓋は、道具なしで上から落とし込む形に置き換えた → 決定記録 [2026-10-04-cover-latch](2026-10-04-cover-latch.md)。**この蓋は刷っていない。**
>
> - **もうコードに無い名前**: `COVER_BOSS`・`COVER_ROOT`・`COVER_RAIL`・`COVER_GRIP`・`COVER_TOP_RELIEF`・`click_case.cover_screw_solids`・`screw_solids(cover=…)`・
>   絵 `cover_screw.png`・蓋の下穴を G-code で測る検査（`tools/slice_cover.py` は、同じ名前で新しい蓋の検査に書き換えた）
> - **生きているもの**: 基板の穴 H30・H31 は基板に残る（使わない。`spec.SCREWS_COVER`）。下の §2 の事実（クリップの板の高さ・電池の位置）と、
>   「ねじを上から、は、いまの基板では成り立たない」の測定。**クリップの板の下へ蓋の足を入れる形は、上から落とす蓋では使えない**（上へ抜けなくなる）
> - 下の本文は、退けた形の記録としてそのまま残す（数は当時の形の値）

- **日付:** 2026-10-04
- **状態:** ❌ 撤回（上）。~~決定（留め方）~~
- **決めた人:** 利用者（ねじで留める・基板の穴 H30・H31 を使う）。ねじの向き・蓋の形・枠の口の形は Claude が測って出した

絵: `build/cckb-click/cover_screw.png`（ねじを通る断面・上から・電池の替え方）・`main_corner.png`・`assembly_main/corner_front.png`。
試し刷り: `build/cckb-click/coupon_corner_plate_n04.gcode.3mf`・見る所は `coupon_cover_howto.png`。

## 1. なぜ決める必要が生じたか

差し込み式の蓋は、刷った 4 つ（v1 と、v2 の折り返しばね・細い腕・筋）がどれも使えなかった（ゆるくて外れる・内側へ落ちる。
決定記録 2026-10-04-knob-out-pilot・docs/coupon-test.md 7 章・8 章）。利用者が 2026-10-04 に「ねじで留める。基板に取ってある穴 H30・H31 を使う」と決めた。
基板（b442b865…）は 4 回の監査を通っていて、変えたくない。**いまの基板のままで、ねじで留める蓋が成り立つか**を測る必要があった。

## 2. 事実はどうか（測った・読んだもの。出所を書く）

| 事実 | 値 | 出所 |
|---|---|---|
| 蓋のねじ穴 H30・H31 | (115.0, −48.225)・(129.0, −48.225)。電池の中心から x ± 7.0。φ2.2 の素通しの穴（めっき無し） | 基板（tests/test_cckb_click_pcb.py が板と突き合わせる） |
| 電池（止めに当てた位置） | φ16 × 3.2・中心 (122.0, −40.915)。x 114〜130 を通って出入りする | Energizer のデータシート・クリップの図面 |
| ねじの軸から電池の縁まで（横） | 1.12（穴の中心から電池の中心まで 10.12 − 半径 8 − ねじの半径 1） | 立体 |
| クリップの板 | 厚さ 0.25・上面は基板の 4.0 上（はんだで ＋0.1）。未注の公差 ± 0.25 → **下面のいちばん低い所は 3.5** | 図面 MY-CP-0247（build/cckb-click/ds_MY-1632-03-R.png） |
| クリップの板の、口の側の端 | 外接の矩形で y −47.775。本物は丸い 2 つの出っ張りで、これより奥（図面に半径の寸法が無いので、矩形で見る） | 図面・LCSC の足跡 |
| クリップの板の下で、電池の通り道の脇 | 金属は無い（脚はランドの上 = y −43.5 より奥・止めはいちばん奥）。電池を押さえる舌 2 本は電池の円の中 | 図面の上面図・正面図 |
| 樹脂に直に切るねじ | 下穴 φ1.6・ふつうの M2×4 で止まる（空回りしない）。線が空ける径で ふつうの壁 1.54・薄い壁 1.50 | **利用者が試し刷り v2 の A を締めた**（決定記録 2026-10-04-knob-out-pilot） |
| 締め直しの回数 | **聞いていない**（open-gaps P1） | — |

## 3. 効く条件（**候補を並べる前に全部書く**）

| # | 条件 | 実データ | 何で確かめたか（外 / 自分の生成物） |
|---|---|---|---|
| 1 | 基板を変えない（穴 H30・H31 だけを使う） | 蓋・ねじは基板の面とこの 2 つの穴にしか触れない | 立体の重なり 0（基板・部品・クリップ・電池）。穴の位置は板と突き合わせ済み（外） |
| 2 | ねじ山を切る相手がある | 基板の穴は素通し → 相手は**蓋の樹脂**しか無い。下穴 φ1.6 × 深さ 2.8・掛かり 2.4（基板が厚い側で 2.24） | 径と留まることは利用者の試し刷り（外）。掛かりは立体 |
| 3 | ねじの頭が机に当たらない | 頭は基板の下面・シート 0.5 の厚さの中（外周のねじと同じ。公差の端で 0.1 出る） | spec（頭の高さは MISUMI の規格表）・立体 |
| 4 | ねじの先・蓋の足が、電池・クリップ・枠・部品・キャップに当たらない | 先は基板の上 2.4（基板が薄い側 2.56）: クリップの板まで 0.94・電池の縁まで横に 1.12。足は板の下で高さ 3.1 まで（板まで 0.4）・電池の縁から 0.3 | 立体（クリップは図面から作った形 = 外） |
| 5 | 下穴のまわりの肉 | 0.87（基板の上 0.3〜1.9）。先の近く（2.3）は奥の斜めの面で 0.47。利用者が締めた壁は 0.81／0.59 | 立体。比べる相手は利用者の試し刷り（外） |
| 6 | 内側へ落ちない・浮かない・面一 | ねじを入れれば、前後・左右・倒れる向きはねじの軸・下は基板・上はねじ山。上面と外面は枠と同じ面 | 立体（動かす・倒す） |
| 7 | 枠を組んだまま入れられる・外せる | ねじを抜けば、手前へまっすぐ 6.35 抜ける間、何にも当たらない | 立体（0.25 おきに動かす） |
| 8 | 蓋が無くても使える・電池を替えられる | 蓋とねじ 2 本を外せば、電池の道は蓋の無いときと同じ | 立体 |
| 9 | サポート無しで刷れる・利用者が確かめた下穴と同じ刷り方 | **上面をベッドに**（枠と同じ向き）: 下穴は縦の穴。線が空ける径 1.49〜1.50（利用者が締めた薄い壁の 1.50 と同じ）。宙に浮く面は爪の溝の底（幅 0.4）だけ | G-code（Bambu Studio 2.8.2・外）と立体 |
| 10 | 電池を替える手間 | **替えるたびに、裏返してねじ 2 本**（ねじは電池の通り道に立つ: 穴は x 115・129、電池は x 114〜130） | 立体。穴の位置は基板で決まっていて動かせない |

## 4. 影響範囲（信号や力の流れに沿って端から端まで。「隣」で止めない）

- **ねじを締める力**: 頭 → 基板の下面（頭の下は裏の銅を抜いてある）→ 基板 → 蓋の足の下面（基板の表。電池の道なので表にも銅は無い。足の外の端 0.25 だけ、
  銅を置かない範囲の外に掛かる = マスクの上に樹脂が載るだけ）→ 足のねじ山。**枠には力が掛からない**（蓋は枠に 0.15 の隙で入っているだけ）
- **枠**: 電池の口を、手前の壁を上から下まで抜く 1 本の溝（幅 17.8）にした。前は、下が幅 16.6 の口・上が幅 13.0 の切り欠きで、その間に幅 1.8 × 高さ 1.4 の
  出っ張りが左右にあった（前の蓋の山の溝があった所）。**その出っ張りと溝が無くなった。**口の左右の壁・クリップの上の屋根・ねじ H14・H15 の厚い壁は変わらない。
  → **右の枠は刷り直し**（まだ本番は刷っていない）
- **電池**: 蓋の足は、止めに当てた電池の縁の 0.3 手前まで来る。電池が奥まで入っていないと、蓋を入れるときに足が電池を奥へ押す（害は無い向き）
- **底のシート**: 蓋のねじの頭の所にも φ5 の穴（全部で 24 か所: 外周 20・予備 2・蓋 2）。シートを貼ったまま蓋のねじを外す
- **ねじの数**: 20 → **22 本**（買う数は 30 のままで足りる）
- **試し刷り v2 の蓋 3 つ**: 形と検査をコードから消した（口の形が変わり、同じ物はもう出せない。刷った結果は docs/coupon-test.md 8 章に残る）
- **基板・ファーム・配線・発注のファイル**: 変わらない（板のハッシュ b442b865… のまま）

## 5. 決めたこと

1. **ねじは基板の下から**。外周と同じ M2×4（スリムヘッド）を H30・H31 に通し、蓋の左右の「足」の下穴 φ1.6 に切る。
2. **蓋の形**: 手前の板（厚さ 1.2）＋ 上の板（厚さ 0.7・枠の上面と面一）＋ 左右の足（基板の上に立つ。幅 3.5・奥行き 4.05）。足は、手前は上の板までつながる柱。
   クリップの板の下へ入る奥の所は、柱から 45° で下がる（板の下で高さ 3.1 まで）。電池の縁から 0.3 離す。上面に爪を掛ける溝。
3. **枠の口**: 手前の壁を上から下まで幅 17.8 で抜く（外面から奥行き 4.5）。上の縁に、内へ 0.6 のひさし（前と同じ）。前の蓋の山の溝は消した。
4. **刷る向き**: 上面をベッドに（枠と同じ）。サポート無し。
5. **電池の替え方**: 裏返してねじ 2 本を外す → 蓋を手前へ抜く → 電池を替える → 蓋を入れる → ねじ 2 本（docs/assembly-guide.md）。
6. **蓋を付けないなら、ねじ 2 本も入れない**（何も留めていないねじが、電池の通り道に立つだけになる）。

## 検討して捨てた案

| 案 | 捨てた理由 |
|---|---|
| **ねじを上から**（蓋の上面から通す。電池を替えるのに裏返さなくて済む） | **いまの基板では成り立たない。**(1) 基板の穴は φ2.2 の素通しで、上からのねじにはねじ山を切る相手が無い。基板の下にナットを置くと厚さ 1.6（M2 の六角ナットの規格の値。今回取り直してはいない）で、シート 0.5 から 1.1 出て机に当たる。(2) ねじの軸が、クリップの板の端（外接の矩形）に 0.55 重なる（立体で測った。軸 φ2.0 を穴の位置で基板の上 0〜5 に立てた重なり 0.42 mm³）。(3) 頭 φ4 が口の幅から 0.1 はみ出して、枠のひさしに掛かる。**基板を変えれば別の答えがありうる**（穴を手前へ寄せる・圧入ナット）が、基板は変えない条件 |
| ねじを上から、枠の樹脂に切る（基板の穴を使わない） | 利用者の決定は「基板の穴 H30・H31 を使う」。それに、口のまわりで枠の樹脂が厚いのは左右の壁だけで、蓋の耳を壁の上へ伸ばす形になり、外へ出っ張る |
| 蓋を手前の面をベッドに刷る（前の蓋の向き） | 下穴が横向きの穴になる = 利用者が確かめた穴（縦の穴）と違う刷り方。ねじ山の力が積層を割る向きに掛かる |
| 口の幅は 16.6 のまま、足を口の幅に収める | 下穴の外側の肉が 0.35 しか残らない（線 1 本ぶんも無い）。口を左右に 0.6 ずつ広げて 0.95 にした |
| 足を、クリップの板の下でも高くする | 板の下面はいちばん低くて 3.5。足の上面はその 0.4 下（3.1）まで |
| 差し込み式のまま、掛かりを増やす | 4 つ刷って 4 つとも使えなかった。利用者が、ねじにすると決めた |

## この決定が乗っている前提（**動いたら読み直す**）

- 基板の穴 H30・H31 の位置（電池の中心から x ± 7.0・基板の縁から 2.1）と、電池クリップの位置（`CLIP_AT`）・止めに当てた電池の位置
- 基板の厚さ 1.6（ねじの掛かり 2.4・先の高さ 2.4 がこれで決まる。JLC の ± 10 % は見てある）
- クリップが MY-1632-03-R のまま（板の高さ 4.0・厚さ 0.25・脚と止めの位置）。**クリップを替えたら、足が板の下に入る所を読み直す**
- ねじが M2×4（長いねじを入れると、先がクリップの板に届く: 検査が M2×6 で落ちることを見ている）
- 下穴 φ1.6 が、上面をベッドに刷った縦の穴で止まること（利用者の試し刷り v2。刷り方 `cckb-click precise 0.10 @A1M 0.4`）

## 覆す前に読むこと

- 「ねじを上から」に変えたいとき: 上の「捨てた案」の 1 行目。**基板を変えないと成り立たない**。
- 蓋の足を太く・高くしたいとき: クリップの板（3.5）と電池の縁（0.3）が上限。tests/test_cckb_click_case.py の蓋の章が、足を高くする・電池へ寄せると落ちる。
- 口の幅を戻したいとき: 下穴の外の肉が 0.35 になる。

## まだ決めていないこと・確かめていないこと

| 項目 | 決められない・確かめていない理由 |
|---|---|
| **刷った蓋で、ねじが止まるか・何回締め直せるか** | 刷っていない。蓋の試し刷り（docs/coupon-test.md 9 章）で 5 回まで見る。電池を替えるたびに 1 回ずつ使う |
| 蓋の足が、本物のクリップの板の下に入るか | 図面から作った形では 0.4 空く。**試し刷りの当て板にはクリップの板の代わりが無い** → 基板が届いてから本物で見る。当たるなら蓋だけ刷り直す（足を低く） |
| 蓋と枠の隙 0.15 がちょうどよいか | 刷って決める（前の蓋は同じ隙で滑って入った）。きつければ蓋だけ刷り直す |
| なぜ前の蓋が内側へ落ちたか | 立体では再現できていない（硬い立体としては、前の形も同じ所で止まる）。**ねじを入れた後は、どの向きにも動かないことを立体で見た**。ねじを入れる前（滑らせただけ）は、下が奥へ入る向きに 2〜3° の遊びがある |
| スリムヘッドのねじでの手応え | 利用者が試し刷りで締めたのは、ふつうの M2×4 |
| 門 #34b を閉じるか | **利用者が決める**（「基板はいまのままでよい」と言えば閉じる）。測った限りでは、基板に足す物は無い |
