ms0216/keyboard-foundry/projects/cckb-click/docs/decisions/2026-10-04-switch-cover.md

# 電源スイッチを内側へ・電池の蓋（差し込み式）・蓋のねじ穴を取っておく

> ⚠️ **先に読むこと（2026-10-04・同じ日に前提が動いた）**: 利用者が角の試し刷りと試し刷り v2 を刷って触った結果、この記録のうち 2 つは**置き換えた**
> （決定記録 [2026-10-04-knob-out-pilot](2026-10-04-knob-out-pilot.md)）:
>
> - **電源スイッチの位置**: 「本体は基板の縁から 2.50（JLC の規約を満たす）」→ **1.75**（0.75 外。つまみの先は基板の縁の 0.30 内・枠の外面の 0.60 内）。
>   **JLC の「2.5 mm 以上」は、いまの板では満たさない。**切り欠きの形も変えた（外へ広がる・内側の上の縁を斜めに）。下の「2.50」「1.05／1.35」
>   「幅 10・外の角を 1.0 落とす」「手はんだの案は要らなくなった」は、前の板（fe90b1e6…）の話
> - **差し込み式の蓋**: v1 も、v2 の 3 つも留まらなかった。→ ねじで留める形（決定記録 [2026-10-04-cover-screw](2026-10-04-cover-screw.md)）を経て、
>   **道具なしで上から落とし込む形に変えた**（決定記録 [2026-10-04-cover-latch](2026-10-04-cover-latch.md)。穴 H30・H31 は使わない）。下の蓋の寸法・ばねの計算は、刷って使えなかった形の記録。
>   **そこに出てくる名前（`COVER_ARM`・`COVER_BUMP`・`PLA_STRAIN_LIMIT`・`cover_spring`・`cover_detent`・口の上の壁の溝）は、もうコードに無い**
>
> 生きているもの: つまみを枠の外へ出さない・蓋のねじ穴 H30・H31 を基板に取っておく・電池は CR1632・載せないコンデンサのランド・
> VBAT_IN の決まった形・SPI ほかの線を置き直す仕組み。（枠の電池の口のまわりの形は変えた: 手前の壁を上から下まで幅 17.8 で抜く溝・ひさしは残した・山の溝は消した。
> 下の「蓋のねじ穴にねじを入れる設計をするときは…立体で見る」は、cover-screw の記録でやった。）

- **日付:** 2026-10-04
- **状態:** **一部を置き換えた**（上）。直した板（fe90b1e6…）は 3 回目の監査〔差分・2026-10-04〕で見直した: 基板は致命 0・重要 0。蓋のばねに重要 1 件 → 直した: 下の「3 回目の監査と直し」。そのあと角の試し刷りを刷って、位置と蓋を決め直した
- **決めた人:** 利用者（下の 4 つ）。寸法と形は Claude（刷って直す値は `[暫定]`）

利用者の決定（2026-10-04・下調べの絵 build/cckb-click/study/s1〜s3 を見て）:

1. **電源スイッチを内側へ動かす**（つまみを外へ出さない = 鞄の中で勝手に切り替わらない・JLC の Economic で載る）。枠に爪を入れる切り欠き
2. **蓋をねじで留める日のための穴を 2 つ、基板に取っておく**（既定では使わない）
3. **電池の蓋は差し込み式**（枠だけで留まる・道具なし）。蓋が無くても同じに使える。厚さ 8.1 のまま・外形から出ない・ねじ 20 本を外さない
4. 電池は **CR1632 のまま**。載せないコンデンサのランド 2 つも残す

## 1. なぜ決める必要が生じたか

- 前の板は、電源スイッチ MSK12C02 のつまみの先が**基板の縁から 0.70・枠の外面から 0.40 外へ出ていた**。本体は縁から 0.75。
  JLC の実装の規約は「部品の本体と基板の縁は 2.5 mm 以上」で、載るかは注文してみないと分からなかった（open-gaps #31・D4 の「手はんだにするか」）。
  鞄の中で引っ掛かって勝手に切り替わるおそれもあった（P8）
- 電池の口は開いたままで、電池の縁（＋の缶）が手前の壁の口から 1.71 奥に見えていた

## 2. 事実はどうか（測った・読んだもの）

| 何 | 前の板（4dc68901…） | いまの板 | 何で確かめたか |
|---|---|---|---|
| 電源スイッチの本体の縁 → 基板の縁 | 0.75 | **2.50** | 板の上の突起の穴（本体の中心線）＋ 図面の本体の幅 2.8（その時の検査 `jlc_edge_problems`。いまは `psw_edge_problems` に置き換えた） |
| つまみの先 → 基板の縁／枠の外面 | +0.70／+0.40（外） | **−1.05／−1.35（内）**。入・切のどちらでも | 同上 ＋ 図面のつまみの出 1.45 |
| スイッチのランドの左の端 → C_BAT のランド | 2.125 | 1.375（C_BAT を 1.0 左へ。クリップの右のランドまで 1.2・高さは重ならない） | 板のパッドの外接 |
| つまみの行程・力 | — | 1.6 ± 0.2 mm・150 ± 100 gf（最大 2.45 N） | 承認書 2024-12-14 の 4.1・4.2（build/cckb-click/study/ の絵・docs の PDF） |
| 蓋のねじ穴 | 無い | 非めっき φ2.2 を (115.0, −48.225) と (129.0, −48.225) に（H30・H31） | 板の事実（tests `cover_hole_problems`） |
| 　止めに当てた電池の缶の縁まで | — | 1.02 | 電池の中心（図面から）と穴の中心 |
| 　穴の縁 → 基板の縁 | — | 1.0（ほかのねじと同じ） | 同上 |
| 　裏の VBAT_IN の線まで | — | 穴の中心から 4.16（頭の禁止円 r 2.3 の外 1.7） | 板の線 |
| 止めに当てた電池の缶の縁 → 表の銅 | 0.72 | 変わらず 0.5 以上（検査の下限） | `tools/click_facts.py` |
| SPI・595 どうし・電源の枝の線 | Freerouting が引いた | **同じ線**（線 100・ビア 17 を置き直した） | 前の板と今の板の線・ビア・部品を全部突き合わせた: 右手前の角の外で違うのは VBAT_SW の長い線の右の端だけ |
| DRC | 違反 0・未配線 0・警告 0 | 違反 0・未配線 0・警告 0 | kicad-cli |
| 入の向き | つまみを奥 = 入 | **変わらない**（足跡を x に 1.75 動かしただけ。奥の端子 3 番が VBAT_SW） | 板のパッドの網・図面の回路図（つまみのある側の端子と共通が繋がる） |

## 3. 効く条件（候補を並べる前に）

| # | 条件 | 実データ | 何で確かめたか |
|---|---|---|---|
| 1 | JLC の実装の規約: 本体と基板の縁 2.5 mm 以上・縁から出る物が無い | 本体 2.50・つまみは縁の 1.05 内側 | 外: JLC の規約の頁（docs/order-steps.md の出どころ）・板のパッド |
| 2 | つまみを爪で動かせる（上からも横からも） | 切り欠き 10 幅・壁を上まで抜く・つまみの脇に 3.0 ＋ 余り 0.55 | 自分の生成物（立体で包絡を当てる検査）。**指で動かせるかは、角の試し刷りでしか分からない** |
| 3 | 切り欠きのまわりの壁が弱くならない | 切り欠きの内側は屋根を基板の上 1.8 まで厚くした（厚さ 3.2）。指で 10 N 押して 7.3 MPa（目安の上限 38） | 計算（click_case.notch_strength）。材料は Bambu PLA Basic の TDS の曲げ強さ 76 MPa の半分 |
| 4 | 蓋は枠だけで留まる・電池とクリップに触らない・厚さと外形を変えない | 手前の板と電池の隙 0.51・上の板はクリップの上 0.2・枠の上面と外面に面一 | 立体の検査（当たらない・出ない・滑らせて抜ける・ひさしと山で留まる） |
| 5 | 蓋のばねが折れない | 腕 6.3 × 0.7・山は腕の先の 0.8 だけ・掛かり 0.25 → **ばねとして効く長さ 5.5**（付け根から、壁の下面が最後まで当たる所まで）→ ひずみ 0.87 %（許容 1.0 %）。3 回目の監査の前は「腕 5.5・山 1.5」で、効く長さ 4.0・ひずみ 1.64 % だった（式が腕の全長を使っていた） | 計算（`click_case.cover_spring`）。**寸法は枠と蓋の立体の重なりから測る**（検査が、直す前の形で落ちることを見る）。許容は TDS の**曲げ**の 76 ÷ 2750 = 2.76 % の 0.36 倍（腕は曲げで使い、同じ梁の式で比べる。スナップフィットの手引きは繰り返しで 0.42 倍）。引張の 35 ÷ 2750 = 1.27 % で見ると 0.79 倍で、手引きの 0.42 倍（0.53 %）より上 = **何回もつかは計算では言えない。刷って 20 回試す** |
| 6 | 刷れる（支え無し） | 枠は上面をベッドに（足した形は全部、下を向かない）・蓋は手前の面をベッドに（45° より寝た下向きの面 0） | 立体の面の向きの検査・実際にスライス |
| 7 | 蓋が無くても同じに使える | 電池の道・指の届く面積は前と同じ | 前からある電池の検査（蓋なしの枠で） |
| 8 | 監査した配線を変えない | 上の表 | 板どうしの突き合わせ・検査 `frozen_problems` |

## 4. 影響範囲（力と信号の流れに沿って）

- **電池 ＋ → クリップの左右のランド → 電源スイッチの共通の端子 → 入の端子 → VBAT_SW の長い線 → TP_VSW・D_PWR・分圧**。
  スイッチを動かしたので、VBAT_IN（＋）と VBAT_SW の右の端を引き直した。**VBAT_IN は決まった形にした**（前は Freerouting）。
  C_BAT はスイッチのランドに近づくので 1.0 左へ（VBAT_SW の縦の区間に横で繋がるのは同じ）
- **Freerouting は同じ入力でも引くたびに形が変わる**（前の監査の所見）。角だけ直すのに SPI・電源の枝が変わらないよう、
  監査した板の線を `pcb/freerouted.json` に写して置き直すようにした（`route_click.py --freeroute` で引き直せる）
- **指 → 切り欠き → つまみ → スイッチの本体 → はんだ（端子 3・枠 4・突起 2）→ 基板**。つまみを動かす力（最大 2.45 N）は基板が受ける。枠には掛からない
- **蓋 → ひさし（上）・切り欠きの壁（左右）・奥の壁（奥）・山と溝（手前）→ 枠**。基板には触れない（下の隙 0.1）。電池にもクリップにも触れない
- **蓋のねじ穴 → 電池を抜き差しする道の下**（表の銅は元から無い）。裏は頭の円の中の銅を抜いた（ほかのねじと同じ）。
  電池クリップの足跡のコートヤードは、口の側の両脇を欠いた（そこはクリップの板の端が基板の 3.7 上に張り出すだけで、基板の面には何も無い）
- **JLC の頼み方**: スイッチは縁の規則を満たすので、「電源スイッチだけ手はんだ」の案は要らなくなった（docs/order-steps.md §2-1）。
  Economic か Standard か（リフローの温度）は残る
- **試し刷り**: スイッチの位置は基板で決まり、発注後は直せない。だから発注の前に、角の試し刷りで爪が届くかを見る（#34）

## 5. 決めたこと

### 基板

| 何 | 決定 |
|---|---|
| 電源スイッチ | 足跡の原点 (141.125, −38.1)（前は 142.875）。向き・端子の網は同じ。JLC が載せる |
| C_BAT | (136.2, −33.0)（前は 137.2） |
| 蓋のねじ穴 | H30 (115.0, −48.225)・H31 (129.0, −48.225)。非めっき φ2.2。**枠に下穴は無い**。ねじは入れない |
| VBAT_IN | 決まった形（spec.VBAT_IN_RUN）: 左のランド → ビア → 裏を電池の下（y −44.065）→ 右のランドの手前のビア → 右のランド → スイッチの 2 番 |
| SPI・595 どうし・電源の枝 | 監査した板の線を置き直す（pcb/freerouted.json） |

### 枠

| 何 | 決定 | 刷って直せるか |
|---|---|---|
| つまみの切り欠き | 右の壁を幅 10・上まで抜く。内側の面は本体の縁 ＋ 0.4。外面の側の角を 1.0 落とす | 直せる（右の枠だけ刷り直す） |
| 切り欠きの内側 | 屋根を基板の上 1.8 まで厚くして塞ぐ（スイッチの本体の上 0.3）。薄い垂れ壁にしない | — |
| 入の印 | 切り欠きのすぐ内側の上面・つまみを入（奥）に寄せた所 | 直せる |
| 蓋の座 | 指の切り欠き（13 × 4.5）の壁の上の縁に、内へ 0.6・高さ 0.7 のひさし（斜め）。口の上の壁の下面に、山の入る溝（左右） | 直せる |

### 蓋（`cover_battery.stl`）

L 字。手前の板（厚さ 1.2・口を塞ぐ）＋ 上の板（厚さ 0.7・付け根 1.15）。手前の板の上の両端が腕（長さ 6.3・太さ 0.7。真ん中の柱は幅 3.7）で、**腕の先の 0.8 だけ**にある山（掛かり 0.25）が溝に入る。
上面の手前寄りに、爪を掛ける溝（幅 9）。**手前の面をベッドに刷る**（腕がベッドの面の中で曲がる）。引き抜く力の見積もりは約 1.6 N（腕 1 本 0.43 N・斜面 45°・摩擦 0.3。計算だけ）。絵: build/cckb-click/cover_spring.png（腕を手前から見た断面。直す前と並べた）。

## 検討して捨てた案

| 案 | 捨てた理由 |
|---|---|
| つまみを外へ出したまま（前の形） | JLC の規約に当たる・鞄で切り替わる |
| 上向きのつまみのスイッチ（MSS12C02 系）を枠の上面の長穴から | 利用者が案 1b（同じ部品を内側へ）を選んだ。部品を替えない |
| 切り欠きの内側を薄い垂れ壁（厚さ 0.5〜0.6）で塞ぐ | 爪で押すと根元が積層を剥がす向きに曲がる（5 N で 30 MPa 前後）。屋根を厚くする方が強くて刷りやすい |
| 蓋のばねを、上の板の脇（滑る向き）に付ける | 長さが 4.4 しか取れず、ひずみが 1.9 % になる |
| 腕を長さ 6.5・太さ 0.9 に | 手前の板の下半分が、真ん中の幅 3.3 の柱だけで繋がる。5.5 にして柱を 5.3 に。**3 回目の監査の直しで、腕は 6.3・柱は 3.7 になった**（この行の判断は目分量で、数は無かった。柱の数は下の「3 回目の監査と直し」） |
| 山を手前の板の真ん中（厚さの中ほど）に | 溝の手前に残る肉が 0.2 しか無い。奥へ寄せて 0.4 |
| 蓋を基板の穴にねじで留める | 利用者が「枠だけで留まる・道具なし」を選んだ。穴だけ取っておく |
| 角だけ Freerouting で引き直す | 引くたびに SPI・電源の枝の形が変わり、監査した配線でなくなる |

## この決定が乗っている前提（動いたら読み直す）

- 電源スイッチは MSK12C02（本体 8 × 2.8・つまみの出 1.45・行程 1.6）。**部品を替えたら、本体の縁・切り欠き・角の試し刷りを全部見直す**
- JLC の規約の「2.5 mm」は 2026-10-04 に読んだ値。名目でちょうど 2.50（本体の幅の公差 ± 0.1 の半分と、置くずれは見ていない）
- 電池クリップは MY-1632-03-R・電池は CR1632（φ16 × 3.2）。蓋の手前の板の隙 0.51 は、止めに当てた電池の位置（図面から）に乗っている
- 枠の上面 5.0・クリップの上 4.1・口の上の壁の下面 3.6
- 刷り方は 0.4 ノズル・層 0.1（腕の太さ 0.7・溝の手前の肉 0.4 は、線の幅 0.42 が前提。**G-code で数えた: 腕は幅 0.42 の線 2 本〔中心の間 0.34〕・1 層目だけ幅 0.5 の線 1 本**。Bambu Studio と OrcaSlicer で同じ）
- `pcb/freerouted.json` は板 4dc68901… から写した。**左 Shift のまわり（595・パスコン・分圧）の配置を変えたら、置き直せなくなる**（`--freeroute` で引き直して監査し直す）

## 覆す前に読むこと

- 基板の上の物（スイッチの位置・蓋のねじ穴）は発注後に直せない。枠と蓋は刷り直せる
- 蓋のねじ穴にねじを入れる設計をするときは、ねじの先（基板の上 2.4）と電池の道・クリップの板（基板の 3.7 上）を、そのとき立体で見る（いまは検査していない）。
  **H30・H31 に立てたねじは電池の道を塞ぐ**（穴は x 115・129、電池は x 114〜130 を通る）= 電池を替えるたびに、ねじを外すことになる。上からのドライバーは入るがぎりぎり（3 回目の監査）
- 蓋の腕と山の寸法を変えるときは、`click_case.cover_spring` の出すひずみ（立体から測る）を見る。**掛かりを上げる・腕を太くする・山を付け根の側へ延ばす、はどれもひずみを上げる**

## まだ決めていないこと・分からないこと

| 項目 | なぜ |
|---|---|
| 爪でつまみを動かせるか・切り欠きの幅 10 で足りるか | 刷って触らないと分からない（#34・角の試し刷り）。試し刷りのつまみは樹脂の小片で、**本物の固さ（150 ± 100 gf）ではない** |
| 蓋が何回の抜き差しに耐えるか・留まる強さ | 計算だけ（ひずみ 0.87 %・約 1.6 N。効く長さを立体から測り直した後の値）。刷って 20 回試す。蓋は基板の上 0.1 に浮いていて、引くと下へ 0.1 逃げうる（そのときの掛かりは 0.15・力は約 0.9 N）。上へこじりながら引くと、ひさしまで約 0.2 浮いて腕が約 0.45 たわむ（ひずみ 約 1.6 %。許容より上・曲げの 2.76 % より下）。**どちらも設計では消していない** |
| 蓋と枠の隙 0.15 で滑るか | 刷って決める（蓋だけ刷り直せる） |
| JLC の実装を Economic にするか Standard にするか | 利用者（リフローの温度。docs/order-steps.md §2-1） |

## 3 回目の監査（差分・2026-10-04）と直し

直した板（fe90b1e6…）と角の枠・蓋を、前の板（4dc68901…）との差分で独立に見た。**基板は致命 0・重要 0。板は変えていない**（sha256 は同じ）。
重要 1 件は刷る蓋で、直した。軽微は記録だけ（open-gaps「軽微・承知しているもの（3 回目の監査）」）。

### 重要: 蓋のばねのひずみ（直した）

- **何が違っていたか**: ひずみの式 ε = 1.5·t·δ/L² に、腕の全長 L = 5.5 を入れていた。山は腕の先の 1.5（口の上の壁の下いっぱい）にあり、
  壁の下面は平らなので山の全体に当たる。たわんだ腕は先へ下がるから、**最後まで当たっているのは山の、付け根の側の端**（付け根から 4.0）。
  正しくは 1.5 × 0.7 × 0.25 ÷ 4.0² = **1.64 %**（許容 1.0 % を超える）。記録の 0.87 % は、効いていない長さで出した数だった
- **型**: 式に入れた寸法が、作った立体の寸法ではなかった（自分の定数どうしの一致 = 作法 3）。いまは `click_case.cover_detent` が
  蓋を手前へ 0.1 ずつ引いて**枠と蓋の立体の重なり**を取り、たわむ量・当たる所・付け根・太さ・幅・隙間を全部そこから測る

| 案（どれも 0.4 ノズル・幅 1.2） | 効く長さ | ひずみ | 腕 1 本の力 | 引き抜く力 | 判断 |
|---|---|---|---|---|---|
| 直す前: 腕 5.5 × 0.7・山 1.5・掛かり 0.25 | 4.0 | 1.64 % | 1.11 N | 4.1 N | 許容を超える |
| 山だけ 0.8 に縮める | 4.7 | 1.19 % | 0.68 N | 2.5 N | まだ超える |
| 山 0.6・掛かり 0.25 | 4.9 | 1.09 % | 0.60 N | 2.2 N | まだ超える |
| 山 0.6・掛かり 0.20 | 4.9 | 0.88 % | 0.48 N | 1.8 N | 通るが、掛かりが減る（蓋が基板まで 0.1 下がると掛かりは 0.10）。山 0.6 は線の幅 0.42 に対して細い |
| 山 0.8・掛かり 0.20 | 4.7 | 0.95 % | 0.55 N | 2.0 N | 余裕が 5 % しか無い。掛かりが減る |
| 山 0.8・腕 5.5 × **0.6** | 4.7 | 1.02 % | 0.43 N | 1.6 N | 超える。太さ 0.6 が線 2 本になるかも見ていない |
| **山 0.8・腕 6.3 × 0.7・掛かり 0.25（採用）** | **5.5** | **0.87 %** | **0.43 N** | **1.6 N** | 掛かり・太さ・力は元の狙いのまま。腕の付け根を 0.8 内へ |
| 山 0.8・腕 6.3 × 0.6 | 5.5 | 0.74 % | 0.27 N | 1.0 N | 力が下限。太さ 0.6 は切っていない |

（数は `click_case.cover_spring` が立体から測った物。力は E = 2750 MPa・幅 1.2。）

- **決めたこと**: `COVER_ARM = (6.3, 0.7, 0.5)`・`COVER_BUMP = (0.25, 0.8, 0.8)`（3 つ目 = 山の、腕に沿う長さ）。枠は変わらない（STL は前と同じ。溝は壁の幅いっぱいのまま）
- **山を越えるとき**の腕の先の下がりは 0.31（腕の下の隙間 0.5 に収まる）
- **代わりに払ったもの**: 真ん中の柱が幅 5.3 → 3.7（厚さ 1.2・高さ 1.6）。手前の板の下の端の角を 5 N で奥へ押すと、柱のねじりは約 28 MPa（前は約 18。目安の上限 38。
  式で置いた値）。蓋は枠の面と面一なので、指で下の角だけを押し込むことは起きにくい。**刷って、柱が白くならないかも見る**（P21）
- **刷れるか（G-code で数えた）**: 腕は 11 層のうち 10 層が幅 0.42 の線 2 本（中心の間 0.34 = 刷り上がりの太さは約 0.76。その太さならひずみ 0.94 %）・
  1 層目だけ面取りで細く、幅 0.5 の線 1 本。山は各層で長さ 0.35〜0.44 の線 1 本（山の頂の線は腕の線から 0.38 = 山の高さ 0.40 のうち 0.38 が線になっている）。
  Bambu Studio 2.8.2 と OrcaSlicer 2.4.2 で同じ
- **許容 1.0 % の出どころ**（spec.PLA_STRAIN_LIMIT のコメントと同じ）: Bambu PLA Basic の TDS の曲げ強さ 76 MPa ÷ 曲げ弾性率 2750 MPa = 2.76 % の 0.36 倍。
  **曲げの値を使う**: 腕は曲げで使い、ひずみも曲げ試験と同じ梁の式で出しているので、同じ物差しどうしで比べられる。
  引張強さ 35 MPa ÷ 2750 = 1.27 % で見ると、1.0 % はその 0.79 倍（1 回で切れる値よりは下）だが、手引きの繰り返しの係数 0.42 倍（0.53 %）よりは上。
  **だから「何回もつか」は計算では言えない**。角の試し刷りで 20 回抜き差しして、腕が白くならないかを見る。TDS の数は監査が挙げた物で、今回取り直してはいない
- **検査**: tests/test_cckb_click_case.py `test_the_cover_spring_strain_is_measured_from_the_solids_...`。spec を直す前の値（腕 5.5・山 1.5）に戻すと
  「0.0164 <= 0.01」で落ちることを見た。前の式（全長 5.5 で 0.87 %）なら通っていたことも同じ検査に書いた

### 軽微（記録だけ・基板は変えない）

| 何 | 中身 |
|---|---|
| #35 の「ほかは前の板と同じ」の言い方 | 正しくは: **角の中では GND の縫いのビアを置き直した**（8 個消えて 9 個足した。新しい 1 個は (261.7, 144.815)）。**角の外には、無視できる違いが 2 つ**: ビア 1 個が 1 nm 動いた・ベタの塗りの差が 2.6e-5 mm² 以下。線・部品は同じ（3 回目の監査が板どうしを突き合わせた数） |
| 電池クリップのコートヤードを欠いた所 | **KiCad はもう、そこに物が重なっても言わない。**そこにある物: クリップの板の、口の側の丸い端（基板の 3.7 上）と、電池の通る道。**将来そこに何か置くなら、自分で検査を書く**（P24） |
| 蓋のねじ穴 H30・H31 にねじを立てると | 電池の道を塞ぐ（電池を替えるたびに外す）。上からのドライバーは入るがぎりぎり（O15・P24） |
| 蓋の、45.7° の下向きの面 | 山の斜面。直す前 1.68 mm² → 山を縮めて 0.89 mm²（45° の検査の境目のすぐ上。害は無い） |
| 電源スイッチの本体から基板の縁まで | 名目でちょうど 2.500・つまみの先は縁の 1.05 内側。JLC に断られたときの手はんだの手は docs/order-steps.md §3 に残してある（P23） |
