ms0216/keyboard-foundry/projects/cckb-click/docs/decisions/2026-10-03-structure.md

# 構造: 積み上げ・キャップと枠の形・刷る向き

- **日付:** 2026-10-03
- **状態:** 決定（方式と、試し刷りに出す形）。数値は `[暫定]`——試し刷りを触って確定する。**刷る条件は 2026-10-03-print-recipe で置き換えた**（層 0.2 → 0.1・継ぎ目の溝を追加。高さは変えていない）
- **決めた人:** 利用者（方式・A と B の両方を刷る・まず基板なしで試す）／形と数値の案は Claude

## 1. なぜ決める必要が生じたか

販売者は「工業用の 3D プリントでもバリで 10% くらい動作不良が出たので射出成形にした」と書いている（記事 acc-introduction）。
こちらは家庭用の FDM（A1 mini・0.4 ノズル・0.2 層・PLA）で刷るので、販売者の形をそのまま刷ると同じ所で失敗する。
基板は発注すると直せないので、**基板を設計する前に**、刷れる形と高さを決める。

## 2. 事実はどうか

**販売者の形（公開 STEP を切って測った。build/cckb-click/clickboard_research.png・cap_ACC_1u_sections.png・case_hole_zoom.png）**

| 物 | 値（基板の上面 = 0） |
|---|---|
| 枠 | 下面 3.0・上面 5.0・穴 16.5 × 16.0・角 R2.25・穴の上の縁に面取り 0.5 |
| 1u のキャップ | 17.29 × 16.79 × 4.5。上面 6.0・押す面（φ3.08 の当て面）3.5・足の上面（掛かる面）3.0・足の下面 1.5 |
| 足 | 四隅・約 2.95 角・穴の縁から 0.395 外へ・首（押す面から掛かる面）0.5・掛かる面積 1 足 1.82 mm² |
| 隙 | 胴と穴 0.163（下端）〜0.293（上端）・首と穴の角 0.11 |

**スイッチ（SKRAAWE010 の仕様書。決定記録 2026-10-03-switch）**: 本体 2.5・ステムの上面 3.4 ± 0.2・ON まで 0.3 ± 0.2・戻す力 0.1 N 以上・
押す側は φ3 の平らな面・傾き 3° 以内。

**販売者の高さの読み**: 押す面 3.5 − ステム 3.4 = 浮き 0.1（公差で −0.1〜+0.3。ステムが高い個体は 0.1 押し込まれ、ON までの最小 0.1 を使い切る）。

**FDM で刷ると何が起きるか（販売者の形を上面を下にして刷る場合）**: 足の掛かる面は、首から 0.5 外へ宙に張り出す下向きの平らな面になる。
0.4 ノズルの外周 1 本（幅 0.42）が丸ごと宙に浮き、垂れる。垂れた分だけキャップは低い位置で掛かり、スイッチを押し込む。
0.1 垂れれば余裕が無くなる。**これが販売者の言う「バリで動作不良」の面。**

**スライサーの設定**: A1 mini の Bambu の設定は象の足の補正 0（当初ここに書いた「外周 2 本・Arachne・上 4 層・下 3 層」は、CLI が設定の継承をたどらずに出した OrcaSlicer の既定値だった。いまの設定は 2026-10-03-print-recipe）。
1 層目の太りは形で逃がす必要がある。

## 3. 効く条件（候補を並べる前に）

| # | 条件 | 実データ | 何で確かめたか |
|---|---|---|---|
| 1 | スイッチを押しっぱなしにしない（公差の端でも） | ステムの最大 3.6 ≦ 押す面 3.6 | 外（仕様書）＋検査 test_the_stack_never_preloads… |
| 2 | 掛かる面が垂れない（宙に張り出す平らな面にしない） | F: つばの上面は上向き・2 層目 | 検査 print_problems（S の形では落ちることも確かめた） |
| 3 | 押す面が平ら（傾き 3° 以内・φ3） | F: ベッドの面。横にずれ切っても φ3 が入る | 検査 test_the_production_cap_prints… |
| 4 | 機能する面の高さが層（当初 0.2・いま 0.1）の境目 | 0.4 / 1.0 / 2.0 / 2.4 / 5.0 | 検査 test_every_height_in_print_orientation… |
| 5 | キャップが擦れない（戻す力 0.1 N） | 胴と穴 0.20（販売者 0.16）。1 層目の太りは面取り 0.3 で逃がす | **まだ**（刷って触る。穴を 0.1 刻みで 3 通り） |
| 6 | 下から入り、上へ抜けない。横にずれ切っても掛かる | 掛かり 2.76 mm²／つば（穴を 0.2 広げて斜めにずれ切っても 0.52）。販売者 1.82 | 検査 insert_problems（立体を動かして重なりを見る） |
| 7 | 押し切っても基板の上の物に当たらない | 押す面の最低 2.6 ＞ 本体 2.5。柱はリブの幅の中 | 検査 assembly_problems |
| 8 | 幅の広いキーの端を押しても、遠い側が擦らず近い側が着かず、傾き 3° 以内 | 2.25u: 1.38°・押した側の縁 0.99 下がる・横 0.02（1u は 3.2°: open-gaps #9） | 検査 end_press_problems（立体を回す）。**感触は刷って** |
| 9 | 全体の厚さ | 0.5 ＋ 1.6 ＋ 6.0 = 8.1 | 計算（検査） |
| 10 | 隣のくぼみとの間の壁が刷れる | 案 B で 0.8（穴 +0.2 で 0.6） | 検査 pocket_wall（立体の中の点を数える）＋スライスした線（slice_n04.png: 線 2 本が出ている） |
| 11 | 見た目・指ざわり（キャップの上面は刷る向きの上 = 積層の跡が見える） | — | **まだ**（刷って見る。アイロンがけを試す） |
| 12 | 販売者のキャップ（買える）がそのまま入るか | 入らない（くぼみがあるので 1.0 余分に上がる） | 形から。**利用者に確認**（open-gaps #12） |

## 4. 影響範囲（力と寸法の流れ）

指 → キャップの上面 → 胴（穴の壁に沿って動く）→ 下面（押す面）→ ステム。戻りはスイッチ → 下面。上の止まりは つばの上面 → くぼみの底 →
枠 → 柱 → 基板。

- つばの厚さ 0.4・くぼみ 1.0・枠の下面 3.0 → 押す面 3.6 → 浮き 0.2（0〜0.4）→ がた・押し始めの空走り → 感触（試し刷りの standin）
- 押す面 3.6 と浮きの最大 0.4 → 押し切りの沈み最大 1.0 → **公差の端ではキャップの上面が枠の上面と同じ高さまで沈む**（販売者は 0.9）
- くぼみ（深さ 1.0・穴の縁から 0.6）→ リブの中の壁 0.8 → 枠の強さ・くぼみの上の皮 0.6
- 柱（1.6 × 5.0・リブの中点）→ 基板の上の置けない場所 → ダイオード・595 の置き場（基板の段）
- 枠は上面を下に刷る → 上面はベッドの肌・穴の上の縁の面取りが 1 層目の太りを逃がす → 枠の反り（試し刷りの strip）
- キャップは下面を下に刷る → 上面は刷る向きの上（見た目）・9 個で 27 分（精度優先の設定・0.4 ノズルのスライスの結果）なので 62 個で約 3 時間

## 5. 決めたこと

**積み上げ（基板の上面 = 0）**

| 面 | 高さ | 決め方 |
|---|---|---|
| スイッチの本体の上面 | 2.5 | 仕様書 |
| ステムの上面 | 3.4 ± 0.2 | 仕様書 |
| 枠の下面（= 柱の高さ） | 3.0 | 販売者と同じ。15 層 |
| 押す面（キャップの下面） | **3.6** | = ステムの最大。販売者 3.5 より 0.1 高い（押しっぱなしを無くす側） |
| 掛かる面（くぼみの底） | 4.0 | 枠の下面 ＋ くぼみ 1.0 |
| 枠の上面 | 5.0 | 販売者と同じ |
| キャップの上面 | 6.0 | 販売者と同じ。全体 8.1（底のシート 0.5 ＋ 基板 1.6 ＋ 6.0） |

**なぜ押す面を 3.6 にしたか（直せる側に倒す）**: 押しっぱなし（誤入力）は機能の失敗、浮き（がた）は感触の問題。キャップと枠は刷り直せるので
どちらも後から直せるが、基板が来て初めて分かる失敗（リフローでスイッチが浮く・個体差）は押しっぱなしの側にしか出ない。
層 0.2 の倍数で取れる押す面は 3.4 か 3.6 で、3.4 は公差の端で 0.2 押し込む。**3.6 が害の無い側。**（層を 0.1 にしたので 3.5 も取れるが、公差の端で 0.1 押し込むので取らない: 2026-10-03-print-recipe）浮きが気になるかは試し刷りで触る。

**キャップ（本番の形 F）**: 厚さ 2.4 の板（中は詰まっている）＋四隅の薄いつば（厚さ 0.4・穴の縁から 0.3 外へ・角から辺に沿って 3.0・
外の角は R1.0 で、穴の角 R2.25 の外に掛かりを作る）。
上の縁に面取り 0.8、下の縁に面取り 0.3。**下面をベッドに刷る。**
- 押す面 = 下面の全部 = ベッドの面（いちばん平らに出る）。φ3 の当て面を作らないので、当て面の高さの誤差が無い
- 掛かる面 = つばの上面 = 2 層目の上向きの面（宙に張り出さない・高さは層で決まる）
- 首が無い（販売者の「首と穴の角 0.11」という一番狭い隙が無くなる）
- 1 層目の太りは下の縁の面取りで穴・くぼみから離す

**枠**: 厚さ 2.0（3.0〜5.0）。穴の四隅の下面に、つばが入るくぼみ（深さ 1.0・つば ＋ 0.3。胴と穴の隙より広くして、横は胴で受ける）。穴の上の縁に面取り 0.4。
柱は 1.6 × 5.0 をリブの中点に。**上面をベッドに刷る**（くぼみの底・枠の下面・柱の先が上向きの面になる。支え無し）。

**平面**: A = 穴 16.5 × 16.0（販売者の 1u）、B = 穴 17.05 角（リブ 2.0）。どちらも 19.05 ピッチ・角 R2.25・キャップは穴より片側 0.20 小さい。
**A か B かは、試し刷りを触って利用者が決める。**

## 検討して捨てた案

| 案 | 捨てた理由 |
|---|---|
| 販売者の形のまま、上面を下に刷る（S） | 掛かる面が宙に張り出す（上の 2）。試し刷り latch の 5・6 番に入れて、実際にどれだけ垂れるかを見る |
| 掛かる面を 45° の斜面にする（C） | 垂れないが、掛かる高さが「首と穴の隙」で決まり、横の誤差 0.1 がそのまま高さ 0.1 になる。キャップが斜面で片側に寄る。試し刷り latch の 3・4 番で比べる |
| つばを「穴を一様に広げた形」にする | 穴を 0.1 広げた列で斜めにずれ切ると、角のつばの掛かりが 0.06 mm² まで減る（検査が落とした）。外の角を R1.0 にして角に掛かりを作った |
| 販売者の形を、足を下にして刷る | 押す当て面が宙に浮く（支えが要り、支えの跡が押す面に残る）。胴の下の縁も橋になる |
| 押す面 3.4（つば 0.6） | 公差の端で 0.2 押しっぱなし（検査が落とす）。試し刷り latch の 2 番で触る |
| くぼみを掘らず、枠の下面を 4.0 にする（枠を 1.0 薄く） | 枠の厚さが 1.0 になり、たわみで誤入力しやすい（販売者の記事「ケースの剛性が低いと誤動作」） |
| 中を空にして φ3 の当て面を立てる | 当て面の上が橋になる・幅の広いキーが柔らかくなる。板のままの方が硬くて刷りやすい（1u で 0.5 cm³ ≒ 0.62 g。スライスの結果） |

## この決定が乗っている前提（**動いたら読み直す**）

- スイッチが SKRAAWE010（ステムの上面 3.4 ± 0.2）。**SKRACAE010 は 3.5 ± 0.2 なので押す面を上げ直す**
- 刷る条件（当初 0.4 ノズル・0.2 層 → いまは 0.1 層。2026-10-03-print-recipe）。機能する面の高さ（0.4・1.0・2.4）は 0.1 でも 0.2 でも層の境目にある。**0.1 でも 0.2 でも割り切れない層にするなら取り直す**
- 基板の上の、キャップの下に来る部品がスイッチの本体（2.5）より低い
- キャップを刷る（買わない）。販売者のキャップを買って使うなら、枠はくぼみ無し（下面 3.0 で掛ける）にする

## 覆す前に読むこと

docs/coupon-test.md の記入表（刷った結果）。掛かり方を F から変えるなら、tests/test_cckb_click.py の print_problems が
その形を通すかを先に見る。

## まだ決めていないこと

| 項目 | 決められない理由 |
|---|---|
| A か B か | 触って決める（試し刷り a / b） |
| 穴の広げ方（隙 0.20 / 0.25 / 0.30） | 刷って擦れを見る |
| 押す面 3.6 のままか | 浮き 0.2 のがたを触る（standin）。基板が来たら実物のステムの高さを測る |
| キャップの上面の仕上げ | 刷って見る |
| 枠を何枚に分けるか・基板との留め方 | 基板の段 |
