ms0216/keyboard-foundry/projects/cckb-click/docs/decisions/2026-10-03-switch.md

# スイッチは Alps Alpine SKRAAWE010（JLC C202383）

- **日付:** 2026-10-03
- **状態:** 決定（品番）。基板の足跡・はんだ付けの可否は基板の段で確かめる
- **決めた人:** 利用者

## 1. なぜ決める必要が生じたか

cckb-click は「薄い表面実装のスイッチを JLCPCB に実装してもらい、軸の無いキャップで押す」方式。キャップ・枠・柱の
高さは全部スイッチの寸法（本体 2.5・ステムの上面 3.4±0.2・ON まで 0.3±0.2）から決まるので、形を作る前に品番が要る。

## 2. 事実はどうか（読んだもの）

| | SKRAAWE010 | SKRACAE010 | Omron D2LS-21 | Panasonic EVQQ2（0.6 N） |
|---|---|---|---|---|
| 種類 | タクト（6.2 角・表面実装） | タクト（本体 6.2 角・**ランドは同じ** 8.5×5.0） | 超小型の基本スイッチ（マウス用） | タクト（6.0 角・表面実装） |
| 作動力 | 0.6 ± 0.3 N | 0.6 ± 0.15 N | 0.6 ± 0.2 N | 0.6 N |
| ON までの移動量 | 0.3 ± 0.2 mm | 0.25 ± 0.1 mm | 自由位置 3.5±0.2 → 動作位置 3.2±0.2 | 0.3 mm |
| 戻す力 | 0.1 N 以上 | 0.1 N 以上 | 0.15 N 以上 | — |
| 高さ | 本体 2.5・ステムの上面 **3.4±0.2**・ステム φ2・端子込みの幅 6.8 | 本体 2.5・ステムの上面 **3.5±0.2**（0.1 高い）・ステム φ2・端子込みの幅 6.5 | 自由位置 3.5±0.2 | 本体 2.5 |
| 寿命 | 400 万回（1.2 N） | 1,000 万回（0.75 N） | 500 万回 | 200 万回 |
| 操作音の規格 | **仕様書に無い** | 60 dBA 以下（リフロー前） | —（販売者の記事: 「マウスのクリック音そのまま」） | — |
| 押す側の指定 | φ3 の平らな面・傾き 3° 以内・中心を押す | φ2.5〜3.0 の平らな面 | — | — |
| JLCPCB（2026-10-03 の API） | C202383・Extended・在庫 2,832・$0.20（50〜149 個） | C54897500・**在庫 0**・$0.35（30〜99 個） | C3823622・在庫 8,210・$0.52（30〜99 個） | 未調査（基板の段） |

出どころ（どれも外の事実。調査の作業場に保存した原本を読んだ）:

- SKRAAWE010 PRODUCT SPECIFICATIONS: 7.1 Operating force 0.6 ± 0.3 N / 7.2 Travel 0.3 ± 0.2 mm / 7.3 Return force 0.1 N Min. /
  9.1 Life cycles 4,000,000 / C10 中心を押す / C11 φ3 mm flat / C12 push angle within 3° / 外形図（6.2・2.5・3.4±0.2・φ2・ランド 8.5×5.0）
- SKRACAE010 製品仕様書: 7.1 0.6 ± 0.15 N / 7.2 0.25 ± 0.1 mm / 9.1 10,000,000 cycles / 11.1 Operating Sound 60 dBA Max. / 外形図（6.2・2.5・**3.5±0.2**・φ2・端子込み 6.5・ランド 8.5×5.0）。
  **AWE とランドは同じだが、ステムの上面が 0.1 高い**（build/cckb-click/ds_SKRAAWE010_outline.png と ds_SKRACAE010_outline.png を見比べた）
- Omron D2LS データシート: OF 0.6 ± 0.2 N / RF 0.15 N / OT 0.1 mm min / OP 3.2 ± 0.2 / FP 3.5 ± 0.2 / 5,000,000 operations
- Panasonic EVQP0/EVQQ2 カタログ: Short Push Travel 0.6 N・0.3 mm・2,000,000 cycles
- JLCPCB の部品 API（在庫・区分・単価。**発注の直前に `tools/kb cckb-click parts` で取り直す**）

## 3. 効く条件

| # | 条件 | 実データ | 何で確かめたか |
|---|---|---|---|
| 1 | JLCPCB が実装できる（在庫がある） | AWE 2,832・CAE 0・D2LS 8,210 | 外（JLC の API 2026-10-03） |
| 2 | 62 個＋予備が買える単価 | AWE $0.20 × 70 ≒ $14 | 外（同上） |
| 3 | 高さ（全体 8.1 mm に収まる） | AWE はステムの上面 3.4±0.2・CAE は 3.5±0.2・D2LS は 3.5±0.2 | 外（外形図） |
| 4 | ON までの移動量と公差（キャップの浮き・押しっぱなしの余裕を決める） | AWE 0.3±0.2（0.1〜0.5）・CAE 0.25±0.1 | 外（仕様書 7.2） |
| 5 | 戻す力（キャップが擦れても戻るか） | AWE・CAE とも 0.1 N 以上しか無い | 外（仕様書 7.3） |
| 6 | 音（利用者は静かな側を選ぶ） | AWE は規格値が無い。CAE は 60 dBA 以下。D2LS は販売者いわく「カチカチ」 | 外（仕様書・記事）。**AWE の音は実物まで分からない** |
| 7 | 寿命 | AWE 400 万・CAE 1,000 万・D2LS 500 万 | 外（仕様書 9.1） |
| 8 | 長押し（修飾キー） | AWE・CAE とも仕様書が「押しっぱなしで長く使わない」と注意（C8 / C1） | 外。**残る課題**（open-gaps #8） |
| 9 | 低い電圧・小さい電流での接触（CR1632・3.0→2.0 V・走査の電流） | 未調査 | **まだ**（open-gaps #7。基板の段で仕様書 6 章と突き合わせる） |
| 10 | リフローのあとの高さ・作動力の変化 | CAE の仕様書は「リフロー前」と断っている | **まだ**（open-gaps #2。実物まで分からない） |

## 4. 影響範囲（力の流れに沿って）

指 → キャップの上面 → キャップの下面（押す面）→ ステム → ドーム → 端子 → 基板のランド → 基板 → 柱 → 枠。

- ステムの上面 3.4±0.2 → 押す面 3.6（決定記録 2026-10-03-structure）→ つばの厚さ・くぼみの深さ・枠の下面・柱の高さ
- ON まで 0.1〜0.5 → 押し切りでキャップが下がる量 → キャップが枠から出る量 1.0・幅の広いキーの傾き
- 作動力 0.3〜0.9 N が基板を押す → 基板のたわみ → 隣のスイッチの誤動作（open-gaps #4）→ 柱の間隔
- ランド 8.5×5.0 → キーごとのダイオード・柱・つばの逃げと取り合う（基板の段）
- 62 個のスイッチの戻す力 0.1 N → キャップと穴の隙（擦れたら戻らない）

## 5. 決めたこと

- **SKRAAWE010（JLC C202383）を本番の品番にする。**在庫があり、利用者が静かな側として選んだ
- 基板のランドは SKRACAE010 も載る形にする（ランドが同じ 8.5×5.0。CAE は移動量の公差が半分・寿命 2.5 倍で、在庫が戻れば替えられる）。
  **ただし CAE はステムの上面が 0.1 高い（3.5±0.2）。**いまの押す面 3.6 のままだと公差の端（3.7）で 0.1 押しっぱなしになるので、
  CAE に替えるときはキャップか枠を刷り直して押す面を上げる（基板は同じでよい。試し刷りの台 3.7 がこの端に当たる）
- Panasonic EVQQ2 を同じ基板に載せられるか（ランドを重ねる）は、はんだ付けできるかを基板の段で確かめてから

## 検討して捨てた案

| 案 | 捨てた理由 |
|---|---|
| Omron D2LS-21（販売者と同じ系統のマウス用スイッチ） | 音が大きい（販売者の記事）。単価 2.6 倍 |
| SKRACAE010 を本番に | JLC の在庫が 0（2026-10-03） |

## この決定が乗っている前提（**動いたら読み直す**）

- JLC の在庫（C202383 がある・C54897500 が無い）
- AWE と CAE のランドが同じ（外形図を見比べた。基板の段でフットプリントを作るときに数字で突き合わせる）。ステムの高さは違う（上）
- 「AWE は静か」は実物で確かめていない（仕様書に音の規格値が無い）

## まだ決めていないこと

| 項目 | 決められない理由 |
|---|---|
| EVQQ2 を載せられるランド | はんだ付けの可否を基板の段で |
| 予備の数 | JLC の最小の単位・不良率を発注の直前に |
