ms0216/keyboard-foundry/projects/cckb/docs/decisions/2026-09-25-choc-v2.md

# スイッチを Kailh Choc V2（PG1353）に替える——事実の洗い出しと、スタビ・高さ・基板の決め方（下書き）

- **日付:** 2026-09-25
- **2026-09-26 追記:** **スイッチのプレートを使わないことにした**（[2026-09-26-plateless.md](2026-09-26-plateless.md)）。この記録のプレートの節（§10-6 の欠けと枠・V4・V8・V9・V10）は**プレートを戻すときだけ**効く。§10-5 の見本は基板の発注の後でよい（open-gaps #6 を取り下げた）
- **状態:** 下書き。**`cckb-v2` の枝で核・プレート・基板（§10）、プレートの欠けの直し・ケース・キャップ・小片（§10-6・§10-7、2026-09-26）まで V2 にした**。**スタビの穴は §10-9（2026-09-26・利用者と決めた）**。見本で確かめること（§10-5）が残る。
  main は V1 の完成した設計のまま（利用者が 2 つを比べて選ぶ）
- **決めた人:** 利用者（V2 に替えること）・Claude（事実の調査と、この記録の案）

**結論（案）**

1. **基板の端子の位置は変わらない。**kiswitch の `SW_Kailh_Choc_V2` の端子は (0, −5.9)・(5, −3.8) で、いまの V1 の足跡と同じ。
   Kailh の図面 CPG135301D01 の推奨穴から、V1 と同じ手順（パターン側 → 部品側）で変換し、V2 の十字は 90° ごとに対称なので
   180° 回した向きで一致する（§2-3）。**ただし穴が 2 つ変わる**: 中心穴 φ3.45 → **φ5.05**、ボス φ1.9 ×2 → **位置決め穴 φ1.6 ×1（−5, 5.15）**。
   この φ1.6 が**行のバス（キー中心の 4.3 下）に 62 キー全部で当たり**、基板の下の**支え 5 本にも当たる**（§5）。配線は引き直しになる。
2. **スタビは遊舎工房の「Choc v2用スタビライザー 2U（スクリュータイプ）」**（SKU A050001-01-1・¥330・在庫あり）を 4 個。
   基板 1.6mm にねじで留める型で、プレートには掛からない（§3）。
3. **厚さはキャップの上面で 13.8 → 14.7（+0.9）**が既定の案。内訳はスイッチの背 +0.6 と、基板の下の空き 1.8 → 2.1（+0.3）。
   V2 の中心の突起（φ4.8・ハウジングの下面から 3.30）が、基板が薄い側（1.44）で基板の下面から 1.96 出て、いまの空き 1.8 に収まらない。
   床に 66 個の穴を開ければ 14.4（+0.6）で済む（§4。**どちらにするかは利用者が決める**）。
4. **キャップの天板の下限は変わらない（1.2 = 0.4 × 3）。**キャップを V2 用にすると、ステムの「十字を受ける筒」が要る（§6）。

> **2026-09-25 時点で「まだ」が残っている。**
> スタビは非公式の図面しか無い。スイッチの下面の 0.30±0.2 の突起は何なのか分からない。
> プレートの厚さも決まっていない（V2 の爪の隙は 1.65 で、V1 の 1.30 と違う）。
> だから決定ではなく下書きにしてある。§8 の「まだ決めていないこと」が片付いたら「決定」に上げる。

---

## 1. なぜ決める必要が生じたか

利用者が 2026-09-25 に、Choc V1（PG1350）から V2（PG1353）へ替えると決めた。理由（利用者の観察）は次の 3 つ。

- V1 は終わりに向かっている様子がある（kailh.net のデータシートの頁に V2 しか載っていない。**この記録では確かめていない**）。
- V1 を選んだ当初の理由が 2 つとも消えた。CFX のキーキャップはやめて自分で刷る（D14）。ホットスワップのソケットもやめて直付けにした（D3）。
- 払うのは高さ 約 0.6mm。

基板はまだ発注していない。この段では**事実を集めて決め方を固める**。コード・基板・ケースは次の段で変える。

## 2. PG1353 の機構（Kailh の図面 CPG135301D01 を自分で読んだ）

出典: <https://raw.githubusercontent.com/keyboardio/keyswitch_documentation/master/datasheets/Kailh/CPG135301D01.pdf>
（1 ページ目が外形図。「临时版」＝暫定版と書かれている。2019-10-25 の日付。赤軸）。450dpi で描き出し、上面・側面・正面・底面・推奨穴の
5 つの図を切り出して読んだ。V1 の図面 CPG135001D01 も同じやり方で並べて描き方を比べた。
遊舎工房の商品ページにも同じ型番 CPG135301D01（赤）・D02（茶）・D03（青）とストローク 3.2±0.25 が書かれている。

### 2-1. 数値（高さはすべてハウジングの下面から＝基板の上面から。§8 の突起の件が片付くまでは前提）

| 項目 | V2（PG1353） | V1（PG1350・いまの値） | 出典（V2） |
|---|---|---|---|
| つば（上から見た外形） | 15.00 × 15.00 | 15.00 × 15.00 | 上面図 |
| プレートを通る下のハウジング | **13.95±0.05** 角 | 13.80 角（開口 13.8 に使った） | 底面図 |
| プレートの上面（＝つばの下面）の高さ | **2.20** | 2.20 | 正面図 2.20（正面図の 6.40・3.10 と同じ基準線） |
| ハウジングの上面 | **5.30**（プレート上 3.10） | 5.00（プレート上 2.80） | 側面図 5.30・正面図 3.10 |
| ステムの上面（押していない） | **8.60**（プレート上 6.40） | 8.00 | 正面図 6.40 ＋ 2.20 |
| ステムがハウジングの上に出る量 | 3.30 | 3.00 | 8.60 − 5.30 |
| ストローク（全行程） | **3.2±0.25** | 3.0 +0/−0.5 | 仕様欄 8・遊舎工房 |
| 接点の位置 | 1.3±0.30 | 1.5±0.5 | 仕様欄 7 |
| 押下圧 | 50±10gf（赤） | 50±10gf（赤） | 仕様欄 5 |
| つばの下面から爪の先まで（プレートが入る隙） | **1.65** | 1.30 | 側面図（V1 は同じ場所に 1.30） |
| 足（金属 2・位置決め 1）の長さ | **3.00±0.2**（「3-」＝3 本） | 3.00（L≦5 の欄で ±0.10） | 側面図 |
| 中心の突起 | **φ4.80 × 3.30**（下面から） | φ3.20 × 2.65 | 側面図 |
| 正体の分からない突起 | **0.30±0.2**（下面の下。正面図の足の脇） | 図に無い | 正面図（§8 の未確認 1） |
| 十字（ステム） | **4.00±0.05 × 1.30±0.03**（2 方向とも） | —（V1 は 1.20 × 3.00 の穴 2 つ・中心間 5.70） | 上面図「2-4.00」「2-1.30」 |
| 十字のまわりの窪み・ステムの外径 | **φ5.50**（窪み）・φ6.50（ステムの円柱） | — | 上面図・側面図 |
| 推奨の穴（パターン側から見た図・中心原点・Y 上） | 端子 φ1.20 ×2: (+5.90, 0)・(+3.80, +5.00)。位置決め φ1.60: (−5.15, −5.00)。中心 φ5.00。LED (−4.93, 0) | 端子 (−5.90, 0)・(−3.80, −5.00)。中心 φ3.40。ボス φ1.90 (0, ±5.50) | 推奨 PCB 図（Pattern Side） |

- 側面図の 0.80 は足の幅と読んだ（上の足のところの縦寸法）。穴 φ1.20 に対して十分に細い。
- 図面の一般公差（表題欄）: L≦5 ±0.10・5<L≦10 ±0.15・10<L≦30 ±0.20。中心の突起 3.30 は ±0.10 として扱った。

### 2-2. V1 との差（高さ）

- ステムの上面は **+0.60**（8.00 → 8.60）。プレートの上面の高さ 2.20 は同じ。
- 押し切ったときのステムの上面は 8.60 − 3.2 = **5.40**（V1 は 8.0 − 3.0 = 5.0）。つまり押し切りでも +0.40。
- ステムはハウジングの上に 3.30 出る。ストロークの上限 3.45 まで押すと、ステムの上面はハウジングの上面より 0.15 下がる。
  **平らなキャップはハウジングの上面に当たって 3.30 で止まる**（ストロークの公差の中）。止まる所はキャップの形で決まる（§6）。

### 2-3. 端子の位置（基板の配線を残せるか）

V1 で確かめた変換（tests/test_choc.py の `_to_kicad`: X を反転 → +90° → Y を反転）を V2 の推奨穴にそのまま当てた。

| | 図（パターン側） | `_to_kicad` の後 | さらに 180° 回す | kiswitch `SW_Kailh_Choc_V2` |
|---|---|---|---|---|
| 端子 | (+5.90, 0) | (0, +5.90) | **(0, −5.90)** | pad 1 (0, −5.9) |
| 端子 | (+3.80, +5.00) | (−5.00, +3.80) | **(5.00, −3.80)** | pad 2 (5, −3.8) |
| 位置決め φ1.6 | (−5.15, −5.00) | (5.00, −5.15) | **(−5.00, 5.15)** | 穴 1.6・ランド 2.6（スルーホール・網なし） (−5, 5.15) |
| 中心 | φ5.00 | | | NPTH **φ5.05** |

- **180° 回してよい理由**: V1 で +90° が要ったのは、キャップの脚 2 本（横並び）とステムの穴の向きを合わせるためだった。
  V2 の十字は 4.00 × 1.30 が 2 方向で同じ（90° ごとに対称）。だからスイッチはどの 90° の向きで座ってもキャップは挿さる。
  鏡映（左右反転）はしていない。X と Y を 1 回ずつ反転しているので、全体では回転になる。
- だから **V2 の端子は V1 の足跡の端子とぴったり同じ位置に置ける**。列の配線（端子 1 から）とダイオードへの L 字（端子 2 から）は形を残せる。
- 同じ向きの足跡を持つライブラリが 2 つある:
  - kiswitch（perigoso の後継）`library/footprints/Switch_Keyboard_Kailh.pretty/SW_Kailh_Choc_V2.kicad_mod`
    （<https://github.com/kiswitch/kiswitch>。V1 版はいまの `lib/keyswitch.pretty/SW_Kailh_Choc_V1.kicad_mod` と一字一句同じ）。
  - サリチル酸さんの `kbd_SW.pretty/Choc_v2.kicad_mod`（<https://github.com/Salicylic-acid3/KiCAD_FootPrint>）。
    端子 (0, 5.9)・(−5, 3.8)・中心 φ5.0 で、`_to_kicad` の後と同じ向き（kiswitch を 180° 回した物）。位置決めは (5, −5.55) の長穴で、図の 5.15 と 0.4 違う。**図に合うのは kiswitch**。
  - Keebio `MX-Alps-Choc_V1V2-1U-NoLED-Alt` は MX・Alps と兼用の穴で、単独の照合には使わない。
- **中心穴 φ5.05**: 図の推奨は φ5.00、突起は φ4.80 で、片側 0.10〜0.125 の隙になる。kiswitch の 5.05 を使う（JLC の穴の公差でも入る側）。

## 3. スタビ（2.25u ×4: Enter・左 Shift・スペースの左右）

### 3-1. 効く条件（候補を並べる前に全部書く）

| # | 条件 | なぜ効くか |
|---|---|---|
| S1 | V2 のステムと**同じ高さ・同じストローク**で動く | キャップの両端と真ん中が同じ高さで沈む。押していないときの上面は 8.60、ストロークは 3.2±0.25 |
| S2 | 支点の間隔がはっきり分かる | 自分で刷るキャップの脚の位置と、基板・プレートの穴の位置 |
| S3 | 軸の形がはっきり分かる | 刷るキャップの受け口（§6） |
| S4 | いま国内で 4 個（＋予備）買える | 発注前に品番を決める（CLAUDE.md） |
| S5 | 基板 1.6mm（O3）に付く／プレートの厚さを縛らない | V2 に替えるとプレートの厚さも決め直しになる（§4-3） |
| S6 | 基板の下に出る量が、床の上の空きに収まる | 床は肉厚の下限 1.2 で、削れない（O10） |
| S7 | 組み立ての順に入る（スイッチは直付け） | プレート・スイッチ・基板ははんだで一体になる（D11） |
| S8 | 図面がある | 寸法を外の事実で確かめる |

### 3-2. 候補

| 候補 | S1 高さ | S2・S3 | S4 国内 | S5 | S6 基板の下 | S8 図面 |
|---|---|---|---|---|---|---|
| **A. 遊舎工房 Choc v2用スタビ 2U スクリュー**（A050001-01-1） | **8.60**（スイッチと同じ） | 支点 24.00・十字 **3.95±0.05 × 1.26±0.03** | **¥330・在庫あり**（数は非公開） | 基板 1.6 にねじ止め。プレートは 2.2mm まで何でも | 箱が基板の上面から **3.30** 下（基板 1.6 で下面から 1.70）・ねじの頭 1.15・爪 2.65 | あり（**非公式**。販売者が仕入れ先から取った抜粋） |
| B. Keeb-On Choc V2 スタビ 2u（スクリュー・クリップ） | A と同じ物（スクリュー） | 同上 | **2u は両方とも売り切れ**（6.25u のクリップだけ在庫） | クリップはプレートに留める型（寸法の図は無い） | ― | スクリューは A と同じ・クリップは無い |
| C. Gateron KS-57（ロープロのプレート留め・KS-33 用） | **ステムはプレートの上 4.05**（V2 は 6.40）。2.35 低い | 支点 24.00±0.15・十字 3.90 × 1.08/1.25 | 国内の在庫は確かめていない | **プレート 1.20±0.1**（いまの PLA と同じ） | プレートの下 4.45 | Gateron の公式 PDF（KS-57B210T） |
| D. いまの Choc V1 スタビ（A0500ST-00-1）を V2 に流用 | V1 用（ステム 8.0 に合わせた物）。0.6 低い | 支点 24.0・軸は V1 の 2 枚刃 | 共立・遊舎で在庫あり | **プレート 1.2 が前提**（§4-3 の V2 の爪の隙 1.65 と取り合う） | プレートの上面から 4.3 下 | 製造図（二次・AliExpress） |
| E. スタビ無し | ― | ― | ― | ― | ― | ― |

- C を V2 に使うなら、キャップの脚を 2.35 長くして高さの差を吸収する必要がある。ただし次の 2 点が分からない:
  スライダーの行程が 3.2 以上あるか（KS-33 のストロークは 3.0±0.2・Gateron KS-33 の図面）、国内で買えるか。
  「KS-57 は KS-33／Choc V2 用」という前の調査の一行を裏付ける外の事実は見つからなかった。
- D も同じで、V1 のスタビに 3.2 の行程があるかが分からない。さらに V1 と同じく 1.2mm のプレートに留まる型なので、プレートの厚さを 1.2 に縛る。
- サリチル酸さんの記事は「未検証ですが、Choc v1用にも使用できないと思います」。これは A を V1 に使う話で、D の向きではない。

### 3-3. 選ぶ: **A**（遊舎工房・スクリュータイプ）

条件ごとに、何で確かめたか。

| # | 何で確かめたか | 外の事実か |
|---|---|---|
| S1 | スタビの図のステムの上面 8.60（基板の上面から）が、スイッチの 2.20 ＋ 6.40 = 8.60 と一致する | 外（2 つの図面。スタビの図は非公式） |
| S2 | 図の 24.00（支点の間）。**サリチル酸さんの足跡は ±11.9（実物を測った値・23.8）で 0.2 違う** | 外。ただし 2 出典が 0.2 食い違う（§8 の未確認 3） |
| S3 | 図の十字 3.95±0.05 × 1.26±0.03（スイッチの 4.00 × 1.30 と別の値）。立体図で十字の形を見た | 外（非公式） |
| S4 | 遊舎工房の Shopify の `/products/13985.js` で `available: true`・¥330（2026-09-25 取得）。在庫の数は非公開。Keeb-On は 2u が売り切れ | 外 |
| S5 | 図の「PCB-H = 1.6mm」。爪の隙 1.65。記事「基板は1.6mmを推奨」「スイッチプレートに引っかかるタイプではないので厚みは何ミリでも良いですが…2.2mmまでが上限」 | 外 |
| S6 | 図の 3.30（箱の下端・基板の上面から）・1.15（ねじの頭）・2.65（ワイヤ側の爪）。**いまの空き 1.8 には入らない側がある**（§4） | 外（数値）→ 自分の計算 |
| S7 | ねじは基板の裏から締める（断面 A-A に「螺母」＝ナットがハウジングの中）。スタビは先に基板へ留め、そのあとプレートとスイッチを載せてはんだ付けする | 外（図）。**外せるかどうか（保守）は確かめていない**（§8 の未確認 4） |
| S8 | 記事の「データシートは…ありません」「製造元は明言しません」。販売者が仕入れ先から取った図 3 枚を公開している | 外。ただし**メーカーの公式の図ではない** |

B は A と同じ物で、いま売り切れている。C と D は S1 を満たさず、行程が 3.2 あるかも確かめられない。E は、刷ったキャップの 2.25u が傾く。

### 3-4. A の寸法（非公式の図。基板への穴）

片側（支点を原点・図の向き）。

- 箱の穴: **8.00 × 6.00**（角を丸める）。サリチル酸さんの足跡では 6.0（X）× 7.5（Y）。
- ねじ: **φ3.00** を支点から 6.20（ワイヤの反対側）。ワイヤの爪（足）: **φ4.00** を支点から 8.50（ワイヤ側）。
  サリチル酸さんの足跡では、ねじ 3.2 × 3.4 の長穴が −6.2、爪 3 × 4 の長穴が +8.24。
- ワイヤ φ1.20（V1 は φ1.00）。爪の側にある。
- 基板の下に出る量（基板の上面から）: 箱 **3.30**・爪 2.65。ねじの頭は基板の下面から 1.15（φ2.78）。
- ステムの上面 8.60・ねじのボスの上面 2.85・箱の上面 5.00。**箱はプレートの上面（2.20）を突き抜ける**ので、プレートには大きな開口が要る。
  サリチル酸さんのプレート用足跡 `Stab_Hole_Choc_v2_PCBMount_2u` はスイッチの穴とつながった U 字で、±14.94 × (−9.45 〜 +10.85)。
  **キーのセル（±9.525）から 1.33 はみ出す**ので、隣の段のスイッチの開口との桟は 1.2 しか残らない。
- 記事: Shift キーは「スイッチを横にしないとスタビライザー裏の突起部分と干渉してしまいます」。
  載っている絵はホットスワップの足跡（ソケットが裏にある）。直付けの CCKB で同じことが起きるかは確かめていない。
  スタビの箱は X 9〜15 にあり、スイッチの端子（X ≦ 6.1）とは平面で重ならない。**組み立てモデルで見て決める**（§8 の未確認 5）。

## 4. 高さ（spec の数値から計算）

### 4-1. 基板の下の空き（いま `UNDER_PCB` = 1.8。床の上面から基板の下面まで）

基板の上面から下へ出る物を、基板の下面から測り直した。JLC の基板 1.6 は ±10% で、最小 1.44。

| 物 | 基板の上面から下へ | 基板の下面から（1.6） | 最悪（基板 1.44・長さは公差の上限） | 1.8 に対して |
|---|---|---|---|---|
| V1 の足（いま） | 3.00（+0.10） | 1.40 | 1.66 | 0.14 空く（いまの根拠） |
| V2 の足・位置決め | 3.00（**±0.2**） | 1.40 | 1.76 | 0.04 |
| **V2 の中心の突起 φ4.8** | 3.30（±0.10） | 1.70 | **1.96** | **−0.16（当たる）** |
| **スタビ A の箱** | 3.30（公差は不明） | 1.70 | **1.86** | **−0.06（当たる）** |
| スタビ A の爪 | 2.65 | 1.05 | 1.21 | 0.59 |
| スタビ A のねじの頭 | ―（下面から） | 1.15 | 1.15 | 0.65 |

中心の突起はプラスチックの円柱で、62 本を切るのは現実的でない。床は 1.2（肉厚の下限・O10）で、削れない。案は 2 つ。

- **案 1（既定）: `UNDER_PCB` 1.8 → 2.1。**V1 と同じ 0.14 の余裕を最悪の 1.96 に足した値。全体が +0.3。
- 案 2: 1.8 のまま、中心の突起 62 本とスタビの箱 4 つの下の床に穴を開ける（φ4.8 ＋ 余裕・箱 8 × 6 ＋ 余裕）。
  全体は増えないが、底面に 66 個の穴が見え、埃も入る。**見た目の判断なので利用者が決める。**

### 4-2. キャップの上面（interface.z() の式どおり。キャップの天板 `KEYCAP_TOP_T` 1.2 のまま）

| | いま（V1） | V2・案 1 | V2・案 2 |
|---|---|---|---|
| 床の上面 | 1.2 | 1.2 | 1.2 |
| 基板の下面 | 3.0 | **3.3** | 3.0 |
| 基板の上面 | 4.6 | 4.9 | 4.6 |
| プレートの上面（＋2.2） | 6.8 | 7.1 | 6.8 |
| ハウジングの上面 | 9.6（＋5.0） | 10.2（＋5.3） | 9.9 |
| ステムの上面 | 12.6（＋8.0） | 13.5（＋8.6） | 13.2 |
| **キャップの上面** | **13.8** | **14.7（+0.9）** | **14.4（+0.6）** |
| 縁（基板 ＋7.0。電池で決まる） | 11.6 | 11.9 | 11.6 |
| 押し切ったキャップの上面（ステム − ストローク ＋ 1.2） | 10.8 | 11.5 | 11.2 |
| 縁 − 押し切ったキャップ | 0.8 | **0.4** | **0.4** |

- **キャップの天板の下限は 1.2**（docs/knowledge/case-and-print.md「肉厚はノズル径の倍数（1.2 / 2.4）」。0.4 ノズルで 3 本、0.2 層で 6 層）。
  V1 と同じく「ステムの上面から天板の上面まで 1.2」として数えた。V2 は十字をキャップの筒に挿すので、
  **筒の底がステムの上面に当たる形なら 1.2 のまま、筒がステムの上に天板を足す形なら厚くなる**（§6）。
- 縁と押し切ったキャップの差は 0.8 → 0.4 に減る（「鞄の中でキーが押されにくい」の余裕）。まだ負にはならない。
- 設計書 §1 の目標「厚さ 約 12mm」からは、いま（13.8）よりさらに離れる。

### 4-3. プレートの厚さ（V2 で決め直し）

V1 はつばの下から爪の先までが 1.30 で、プレート 1.2 が 0.1 の遊びで挟まった。V2 はここが **1.65** ある。
1.2 のままだとプレートが 0.45 浮く。スイッチは基板にはんだ付けするので位置はずれないが、プレートがカタつく。
0.2 層で刷れる厚さなら **1.4（遊び 0.25）か 1.6（遊び 0.05）**。プレートの上面は 2.2 のまま動かないので、厚くしても全体の厚さは変わらない。
プレートの下面と基板の間は 1.0 → 0.8 / 0.6 に減る。そこに入る物（ナット 1.6 はプレートの六角の穴に入る・角は開口）は、次の段で確かめる。
スタビ A は厚さを縛らない（2.2 まで）。**試し刷りの小片で決める**（1.2 / 1.4 / 1.6）。
スイッチの開口は、下のハウジングの 13.95±0.05 を挟んで小片で 13.90 / 13.95 / 14.00 / 14.05 を比べる（V1 は図の 13.80 と同じ値を開口にした）。

## 5. 基板への影響（いまの板の座標で数えた）

`projects/cckb/interface.py` のキーの位置と `spec.py` の値で、V2 の穴（kiswitch の向き）を 62 キーに置いて数えた（2026-09-25）。

- **行のバス（裏・キー中心の `ROW_BUS_DY` 下）は 62 / 62 キーで位置決め穴 φ1.6 に当たる**（最悪 −0.65。穴と銅の間に要る 0.3 に対して）。
  φ1.6 の上端はキー中心の 4.35 下で、バス（4.3 下・線幅 0.2）の上に重なる。
  - 中心穴が φ5.05 になっても、下端は 2.525 下。バスをおおむね **3.9 下へ上げれば**、穴にも位置決め穴（上端 4.35 下）にも 0.3 以上空く。
    V1 でバスを 4.3 に下げた理由（V1 のスタビの逃げの下端 −3.55）は、スタビが替わると消える。
  - **スタビのキー 4 つでは、スタビ A の箱の穴（±4.0）とねじ（φ3.0 を 6.2 下）がバスの通り道にかかる。**
    ワイヤを奥にすると、箱の穴（+4.0）と爪の穴（+6.5〜+10.5）の間に 2.5 の隙があり、そこを通すか、ねじの下（−8.1 より下）へ回す。
    どちらにするかは `matrix_routes` で決める。最下段はねじの下を通すと外形（−47.925）に近い。
  - スイッチをどの 90° に回しても、何か（端子か位置決め）がキー中心の 4〜6 下の帯に来る。だから回して逃げることはできない。
- **支え（トレイから基板を下から押す柱 φ3.0）5 本が位置決めの足と重なる**: (−95.18, −26.43)・(−57.18, −26.43)・(−19.18, −26.43)・
  (18.82, −26.43)・(57.32, −26.43)。隙はそれぞれ −0.05〜−0.07・−0.03。ほかに (18.82, −44.43) は 0.35。支えの位置を選び直す。
- 取付（ナット・ボス）・U1/U2・C_U*・D_PWR・R_* と V2 の穴の間は 3.0 以上空いている（同じ計算）。
- V1 のボス穴 φ1.9 ×2 が消えるので、列の配線（`COL_JOG` 3.1「左のボスの縁から 1.35」）の根拠は書き直す。中心穴の縁（2.525）から 0.575 − 0.1 = 0.475 残る（0.3 以上）。
- スタビのキー 4 つのダイオード（`DIODE_OVERRIDE` の (5.55, 2.9, 180)）は V1 のスタビの逃げに合わせた位置なので、スタビ A の穴で置き直す。
- 実際の当たりは、生成し直した板の DRC で数え直す（ここの数は平面の円どうしの計算）。

## 6. キャップの軸（十字の受け口）

- スイッチの十字: **4.00±0.05 × 1.30±0.03**（2 方向とも同じ）。十字は **φ5.50 の窪み**の中に立つ（ステムの外径 φ6.50）。
  Gateron KS-33 の図面も同じ作りで、十字 4.00 × 1.10 / 1.28・窪み φ5.70。
- スタビ A の十字: **3.95±0.05 × 1.26±0.03**。
- **公開されている「MX-LP／Choc V2 のキャップ側の受け口の規格」は見つからなかった。**Kailh の図面はスイッチ側の寸法だけ。
  販売店の説明に「MX用のキーキャップは嵌りますが、スイッチプレートと干渉する」（遊舎工房・共立）とあり、MX のキャップの筒が窪みに入ることは分かる。
- 刷るキャップの筒は、窪み φ5.50 の中に入る太さにしなければならない。十字の穴 4.0 ＋ 嵌め合いに対して、腕の先の肉は片側 ≦ 0.75。
  **0.4 ノズル 2 本（0.8）より薄い**。刷れるかどうかが最大の不確かさ（§8 の未確認 6）。
  **窪みの深さ（十字の上端とステムの縁の段差）は図に無い**。筒の長さと、天板が 1.2 のままでよいかはこの深さで決まる。
- いまの `STEM_SLOT`・`STEM_PITCH`・`STEM_POST_*`・`coupon_stem` は V1 の 2 枚刃の穴に挿す脚で、全部置き換わる。

## 7. 入手（2026-09-25 に取った値。70 個＝62 ＋予備）

| 店 | 品 | 値段 | 在庫 | 取り方 |
|---|---|---|---|---|
| 共立エレショップ（シリコンハウス） | Kailh Choc v2 Red 単品 Q5DV1F（A0200C2-RE-1） | ¥115 | **135** | 商品ページの「在庫 : 135（現在庫数）」 |
| 同 | Kailh Choc v2 Red 35個入 Q5DV1T（A0200C2-RE-1-35P） | ¥2,695 | **3** | 同「在庫 : 3」 |
| 遊舎工房 | Kailh Choc V2 赤 35pcs（A0200C2-RE-35） | ¥2,695 | あり（数は非公開） | `/products/kailh-choc-v2.js` |
| 同 | 茶・青 35pcs／1pcs | ¥2,695／¥115 | **売り切れ** | 同 |
| Keeb-On | Choc v2 Deep Sea Silent・White Rain・Spring Mini | 10 個 ¥1,500 ほか | **全部売り切れ** | `/products.json` |
| 遊舎工房 | Choc v2用スタビライザー 2U スクリュー（A050001-01-1） | ¥330 | あり（数は非公開） | `/products/13985.js` |
| Keeb-On | Choc V2 スタビ 2u スクリュー／クリップ | ¥300 | 売り切れ | `/products/stabilizer-chocv2.js` |
| Amazon.co.jp | Kailh Choc V2（出品者 DRAOZA ほか・36/72/108 個） | ― | 見ていない | 検索で出品は見えた。「5ピン」と書かれていて図面（金属 2 ＋ 位置決め 1）と合わない。同じ品か確かめられないので候補にしない |

- **いま 70 個揃うのは赤（リニア・CPG135301D01）だけ。**共立なら 35 個入 2 箱で ¥5,390（2 箱とも在庫 3 の内）。単品 70 個だと ¥8,050。
  遊舎工房の 35 個入 2 つでも ¥5,390。
- 共立に V2 のスタビがあるかは見つからなかった（商品コードを当てて探した範囲で 0。**無いとは言い切れない**）。
  スイッチとスタビを 1 店で揃えるなら遊舎工房。共立はいまスイッチだけ。前の「シリコンハウス 1 店」（shopping-list）は崩れる。
- 図面（CPG135301D01）は**赤軸の物**。茶（D02）・青（D03）の図は見ていない。

## 8. まだ決めていないこと・未確認

| # | 何 | どうすれば決まるか |
|---|---|---|
| 1 | **ハウジングの下面の 0.30±0.2 の突起**（正面図）。これで立つなら、全部の高さが 0.3 上がり、足と中心の突起は 0.3 浅くなる | 実物をノギスで測る。スタビ A の 8.60 が「突起なし」の 2.20 ＋ 6.40 と合うので、下面が基板に着くと読んでいる（間接の根拠） |
| 2 | プレートの厚さ 1.2 / 1.4 / 1.6（爪の隙 1.65） | 試し刷りの小片にスイッチを挿す |
| 3 | スタビの支点 24.00（図）と 23.8（サリチル酸さんの実測の足跡 ±11.9） | 届いたスタビを測る。キャップの脚と基板の穴は同じ値を使う |
| 4 | スタビ A の爪の隙 1.65 と基板の最大 1.76（JLC ±10%）。ねじが付いてくるか。組んだ後に外せるか | 実物。基板の厚さの公差を詰める発注オプションがあるかは JLC の頁で確かめる |
| 5 | スイッチの向き（記事の「横にしないと干渉」）が直付けでも要るか | 組み立てモデルにスタビ A を入れて見る |
| 6 | 十字の窪みの深さと、刷った筒（肉 ≦ 0.75）が嵌まるか | 実物を測って、試し刷りの小片（筒の太さ・穴の幅を振る） |
| 7 | 案 1（空き 2.1・+0.3）か案 2（床に 66 個の穴） | **利用者** |
| 8 | 軸の色（いま 70 個あるのは赤だけ） | **利用者** |
| 9 | スタビの行程が 3.2 以上か | 実物（図に行程の記載が無い） |
| 10 | 見本を先に買うか（本番と同じ品番。スイッチ数個＋スタビ 1 個） | **利用者**（購入）。1〜6・9 は実物が無いと決まらない |

## 9. 影響範囲（grep で数えた。2026-09-25・`cckb-v2` の 38f7f11）

V1 固有の名前と値（`choc_v1|CHOC_V1|PG1350|CHOC_STAB_OUTLINE|STAB_KERF|SWITCH_*_ABOVE_PCB|STAB_HOUSING|STEM_*|SW_FLANGE|SW_POST_BELOW|A0500ST|A0200KL|stab_kind`
などと、`ROW_BUS_DY|COL_JOG|DIODE_OVERRIDE|UNDER_PCB|KEYCAP_TOP_T|3.45|13.8`）で `git grep` した。
ZMK の設定（`firmware/`・シールド）に当たりは無い（`battery_alkaline.c` の 3.45 は電圧で無関係）。**ファームは変わらない**
（端子の位置も行列も同じ）。

| ファイル | 何が変わるか |
|---|---|
| `foundry/mech.py` | `CHOC_V2 = Switch(...)` を足す（cutout 13.95〜14.0・plate_t 1.4/1.6・fp `SW_Kailh_Choc_V2`・value `PG1353`・stab_offset {2.25: 12.0}・stab_kind 新しい種類）。スタビ A の輪郭（プレートの U 字・基板の穴）の定数。`CHOC_V1`・`CHOC_STAB_OUTLINE` は HHKB に関係しないが、CCKB が使わなくなったら**消す**（作法 8）。`STAB_KERF` のコメント（Choc にも使う）を直す |
| `foundry/plate.py` | `choc_stab_polygons` と `stab_kind == "choc"` の枝 → スタビ A のプレートの開口（U 字）。**HHKB の再現検査を通す** |
| `lib/keyswitch.pretty/` | `SW_Kailh_Choc_V2.kicad_mod` を kiswitch から入れる（V1 と同じく無改変）。位置決め穴を NPTH にするかスルーホールのまま（kiswitch）にするか決める。V1 の足跡は使わなくなったら消す。`lib/README.md`（7 か所） |
| `lib/`（新規） | スタビ A の基板の穴（箱 8×6・ねじ φ3.0・爪 φ4.0）の足跡。図の値で作り、サリチル酸さんの `Choc_v2_PCBMountStab_2u` と突き合わせる |
| `projects/cckb/spec.py` | `SWITCH = "choc_v2"`。高さ `SWITCH_TOP_ABOVE_PCB` 5.0→5.3・`SWITCH_STEM_ABOVE_PCB` 8.0→8.6・`SWITCH_PIN_L` 3.0（公差 0.1→0.2 `SWITCH_PIN_TOL`）・中心の突起 3.30 を足す。`UNDER_PCB` 1.8→2.1（案 1）。`STAB_RELIEF_MARGIN`・`STAB_HOUSING_H` 4.3・`STAB_HOUSING` はスタビ A の値に。`ROW_BUS_DY`（−4.3 → 約 −3.9・スタビのキーは迂回）・`COL_JOG` の根拠・`DIODE_OVERRIDE` 4 キー・`SUPPORTS` 5 本・`RIM_ABOVE_PCB` のコメント（押し切りとの差 0.8 → 0.4） |
| `projects/cckb/interface.py` | `z()` に中心の突起・スタビ A の下端（基板の上面から 3.30）。`stab_reliefs`・`_stab_poly`・`stab_housings`（`CHOC_STAB_OUTLINE` 由来）をスタビ A の形に。`keycap_bottomed`（ストローク 3.2・ハウジングで止まる 3.30） |
| `projects/cckb/matrix_routes.py` | 行のバスの高さと、スタビのキーの迂回。列の `COL_JOG` はボスが無くなって条件が変わる |
| `projects/cckb/pcb_extra.py` | スタビの逃げ穴 8 つ（Edge.Cuts）→ スタビ A の箱の穴 8 つ＋ねじ・爪の穴 8 つ |
| `projects/cckb/pcb/`（`cckb_main.kicad_pcb`・`board_geometry.json` 62 か所・`route.json`・`production/`） | 生成し直し・配線し直し・DRC と発注の門をやり直す |
| `projects/cckb/case_spec.py` | `STEM_SLOT`・`STEM_PITCH`・`STEM_POST_FIT`・`STEM_FIT_STEPS`・`STEM_POST_L` → 十字の筒の寸法。`SW_FLANGE`（15.0 のまま）・`SW_FLANGE_T`・`SW_POST_BELOW` 2.65 → 3.30・`SW_STEM_BLOCK` → φ6.5 の円柱。`KEYCAP_SKIRT_H` のコメント（押し切りの下端）。`COUPON_SWITCH_CUTOUTS`（13.7〜14.0 → 13.90〜14.05）・`COUPON_STAB_KERFS` |
| `projects/cckb/keycaps.py` | 脚 2 本 → 十字の筒（スイッチ 4.00×1.30・スタビ 3.95×1.26）。`stem_xs` は ±12.0 のまま（未確認 3） |
| `projects/cckb/coupons.py` | `CHOC_V1` を直接 import している（3 か所）→ `switch_of(spec)`。スタビの小片を U 字に。キャップの軸の小片を十字の筒に。プレートの厚さの小片を足す |
| `projects/cckb/assembly.py` | スイッチの包絡（つば・胴・ステムの穴 2 つ・足の長さ `SW_POST_BELOW`）→ V2 の形。スタビ A を部品として入れる（ねじの頭・爪・箱）。支えと足の干渉 |
| `projects/cckb/case.py`・`tools/draw_interface.py` | 高さは `interface.z()` から読むので追随する。`draw_interface.py` の最悪の足の式（`SWITCH_PIN_L + SWITCH_PIN_TOL`）に中心の突起を足す |
| `tests/test_choc.py`（18 か所） | V2 の図面の生の値（§2-1 の推奨穴）を `_to_kicad` ＋180° で照合する検査に。**壊して落ちる検査**（端子を 0.1 動かす・鏡映・中心穴を 3.45 に戻す）も V2 で。スタビの検査は A の図面の値に |
| `tests/test_cckb.py`・`test_cckb_interface.py`・`test_cckb_case.py`・`test_cckb_pcb.py` | 開口 13.8・スタビの逃げ・ダイオードの逃げ・足の隙の検査を V2 の値で |
| `projects/cckb/docs/`（shopping-list 11・open-gaps 5・provisional-values・printing-and-assembly・assembly-guide・order-steps・status・references/README と `Kailh-PG1350-Stab-Cutout.kicad_mod`・decisions/README） | 部品（スイッチ・スタビ・店）と手順（スタビを先に基板へねじ止め）を書き直す。V1 のスタビの参照は、置き換えたら消す |
| `projects/cckb/docs/decisions/2026-09-23-choc-stabilizer.md`・`2026-09-24-interface.md`（§2-6 の O2 など）・`2026-09-24-case.md` | 前提（「Choc V1 をプレートマウントで使う」）が動いた。「置き換えた」と注記する |
| `docs/superpowers/specs/2026-09-23-cckb-design.md` | D2（V1 を選んだ理由と V2 を退けた理由）・§1 の妥協の表・§3 部品・§7（`choc_v1`）・D14（支点の出典） |
| `docs/superpowers/plans/2026-09-23-cckb-plan1-foundation.md`（89 か所） | 過去の計画。書き換えない（記録） |
| `docs/templates/spec.py.tmpl` | `SWITCH` の選択肢に `choc_v2` |
| HHKB（`tests/test_regression_hhkb.py`） | `MX_HOTSWAP` は触らない。核を直したら再現検査を通す |

## 10. `cckb-v2` の枝で実装した設計（2026-09-25・核・プレート・基板の段）

### 10-1. 静音の V2（利用者が買う見込みの物）の図面を読んだ

利用者は会議・出張用に**静音**を買う見込み。Kailh の静音の V2 の図面は 2 枚あり、どちらも「临时版」（暫定版）:

| 図面 | 品 | 入手先 | 読んだ値（標準 CPG135301D01 と違う所だけ） |
|---|---|---|---|
| CPG1353S01D01-01（2023-05-12） | PG1353 静音 赤（リニア 43±10gf） | keyboardio/keyswitch_documentation `datasheets/Kailh/` | 下記と同じ |
| CPG1353S01D02-01（2024-01-23） | PG1353 静音 茶（タクタイル 45±10gf・触感 55±10gf）。表題「**配1.2铝板**」 | 同上。Kailh の公式サイト <https://www.kailhswitch.com/uploads/15927/files/CPG1353S01D02-01-data-sheet.pdf> と**同じファイル**（sha1 b7654171…・並行して調べたエージェントの写しと突き合わせた） | ↓ |

- **位置決めの穴: 長円 2.0 × 1.5**（パターン側の図で横長。中心は標準と同じ (−5.15, −5.00)）。図の注「此孔开成此形状便于所有此系列轴共用」
  （この系列のどの軸にも共用できるようにこの形で開ける）。底面図は位置決めの足を中心から **5.15 と 5.50** の 2 か所に描いている。
  サリチル酸さんの足跡の長穴 (5, −5.55) は 5.50 の版に合わせた物と読める。
- **つばの下面から爪の先まで 1.35**（標準 1.65）→ プレートは 1.35 以下。
- ステムの周りの窪み φ5.70（標準 5.50）・ハウジングの上に高さ 0.40 のつば（プレートの上から 3.50 = 基板の上から 5.70）・
  全行程 2.8±0.25・接点 1.2〜1.3±0.3。
- 同じ所: 端子 φ1.20 の位置・中心 φ5.00・下のハウジング 13.95±0.05・つば 15.00・プレートの上から 6.40（ステム）・3.10（ハウジング）・
  足 3.00±0.2・中心の突起 φ4.80 × 3.30・正面図の 2.20。
- 「Deep Sea Silent MINI」（Kailh・Choc V2 静音）は、販売店の値（43gf リニア・45gf タクタイル・全行程 2.8）が上の 2 枚と同じ。
  **品番で同じ物かは確かめていない**（Deep Sea の図面は見つけていない）。

### 10-2. 決めたこと（値は foundry/mech.py・projects/cckb/spec.py。出典は各値のコメント）

| 項目 | 決めた値 | 理由 |
|---|---|---|
| スイッチの足跡 | **（2026-09-26 に §10-8 で置き換えた: `SW_Kailh_Choc_V2_Common`・位置決めは丸 φ2.1）** `lib/keyswitch.pretty/SW_Kailh_Choc_V2_Slot` = kiswitch `SW_Kailh_Choc_V2` の**位置決め穴だけ**を「非めっきの長円 1.6 × 2.0」に替えた物（上流の写しは docs/references/） | 標準の φ1.6 と静音の 2.0 × 1.5 の**和**。長穴の上端はキー中心の 4.15 下。めっき（kiswitch はランド φ2.6）を無くしたので行のバスを近くに通せる。tests/test_choc_v2.py が 3 枚の図と照合し、0.1 ずらすと落ちることを見る |
| プレートの厚さ | **1.2 のまま**（[暫定]） | 静音の爪の隙 1.35 と「配1.2铝板」。§4-3 の 1.4 / 1.6 は標準だけを見た値で、静音は入らない。標準なら 0.45 遊ぶ |
| プレートの開口 | 13.95（[暫定]。試し刷りで 13.90〜14.05） | 3 枚とも 13.95±0.05 |
| プレートのスタビの開口 | サリチル酸さんの U 字（スイッチの開口・帯・羽が 1 つの穴）を外接する矩形で・羽の外を +0.1（支点 24.0 用）。**最下段のスペース 2 つは、羽の手前の端が外形から 0.225 しか残らない**ので、羽を外形の外まで伸ばし、切り離される島（スイッチの開口の手前と桟）ごと抜いた → **スペースの左右 2 キーのスイッチの周りにはプレートが無い**（mech.choc_v2_stab_plate_polys・spec.PLATE_MIN_WEB 1.2）。**→ 2026-09-26 に置き換えた: 切り離した枠を捨てずに別に刷る・羽の奥の端 10.72（§10-6）** | 0.225 の帯は刷れず、刷れても島を 1 本の細い帯で吊るだけになる。スイッチは基板にはんだ付けで留まる（D11）。**利用者に見てほしい所**（下の V7） |
| スタビの足跡 | `lib/keyswitch.pretty/Stab_Kailh_Choc_V2_Screw_2u`（ねじ・爪の非めっきの長円）＋ 箱の穴（Edge.Cuts・pcb_extra） | 下の 10-3 |
| ダイオード | 全部のキーで (7.1, −1.0)・縦（V1 の DIODE_OVERRIDE は消した） | スタビのキーでも箱の穴からコートヤードまで 0.35 |
| 行のバス | キー中心の **3.35 下**（全段）。スタビの箱・ねじ・取付の穴の所だけ下へ回り道（matrix_routes.buses） | 中心穴 φ5.05 の下端 2.525 と長穴の上端 4.15 の間（両側 0.425） |
| 高さ | 基板の下の空き 1.8 のまま・床の内側に 0.4 の止まり穴（突起 62・スタビの箱 8）。**2026-09-26 に足（端子 2・位置決め 1）の下にも（§10-7）**。キャップの上面 13.8 → **14.4** | 利用者の決定（§4-1 の案 2）。穴の位置と大きさは `interface.floor_pockets()`（ケースの段はここから読む） |

### 10-3. スタビの図が非公式であることと、支点の 24.0 / 23.8

> **2026-09-26 に §10-9 で置き換えた**: 販売者の足跡（実物の実測）を正、図を参照にし、支点 ±11.9・丸穴 φ3.0 / φ4.0 に。下の「和で開ける」は前の考え方の記録。

- スタビの寸法は**メーカーの公式の図ではない**（販売者が仕入れ先から取った抜粋・サリチル酸さんの記事）。記事自身が
  「実測値と違ったりするので、あくまで参考程度に」と書く。もう 1 つの出典（サリチル酸さんの足跡）は実物を測った物。
- 支点の間が図 24.0・足跡 23.8 で 0.2 食い違う。**基板の穴は両方の実物が入る和にした**（どちらの支点でも入る）:
  箱の穴 = x は両方の支点の箱を含む ＋ 片側 0.3（JLC の外形公差 ±0.2 ＋ 0.1）、**y はサリチル酸さんの 7.5（±3.75）で広げない**
  （図の推奨 8.00 に余裕を足すと、ねじの穴との基板の橋が 0.2 まで細った。1 回目の板の絵で見つけた。7.5 なら橋 0.75 で
  サリチル酸さんの足跡と同じ。箱〔図の 7.30〕との y の隙は片側 0.1 で、見本で確かめる）、ねじの穴 = 長円 3.2 × 3.4（足跡の形。図の φ3.0 を含む）、
  爪の穴 = 長円 4.2 × 4.4（両方を含む最小に近い形）。プレートの羽も外へ 0.1 広げた。tests/test_choc_v2.py が
  「両方の出典の形を含む」「0.1 狭めると落ちる」を見る。
- **支点そのもの（キャップの脚の位置）は穴では決まらない。**キャップを刷る前に、届いたスタビの支点の間をノギスで測る（下の 10-5）。

### 10-4. 当たりと、その解き方（生成した板で数えた）

| 当たり | 解き方 |
|---|---|
| 行のバス（V1 は 4.3 下）が位置決め穴に 62 キー全部で当たる | 3.35 下へ上げた（長穴の上端 4.15 と中心穴の下端 2.525 の間） |
| スタビのキー 4 つで、バスが箱の穴・ねじの穴に当たる | その範囲だけ下へ回り道（Enter・左 Shift は 5.0 下、スペースは 5.1 下＝基板の縁の帯の手前）。取付 H4〜H7 の穴の所も同じ仕組みで回る |
| 列の線が段の境目で Enter のスタビの爪の穴をまたぐ | 渡る高さを境目から ±0.5〜2.0 ずらす候補を足した（matrix_routes.CROSS_OFFSETS） |
| XIAO から行 0〜2 へ上がる線が左 Shift の左のスタビ（ねじ・箱）に塞がれる | XIAO の下（裏は使える）で先に左へ寄せてからビアへ（spec.XIAO_ESCAPE の turn_y） |
| 行 3 の線と D_PWR が囲まれて、VBAT_SW（電源スイッチまで約 280mm）が Freerouting で引けない | D_PWR を XIAO の奥の縁の上へ下ろし（(−124.0, −28.45)）、VBAT_SW の長い 1 本を決まった形で引く（spec.POWER_RUNS）。V1 の通り道（y −28.39）はスペースのスタビの爪が 4 か所で塞ぐ |
| 基板の下の支え 8 本が長穴・スタビの穴に当たる | 最寄りの候補へ動かした（6 本は 0.6 下、ほか 2 本）。1 本は外して H9 の前の場所へ |
| 取付 H9（Enter の右）がスタビに当たり、Enter の右に置ける所が無い | Del の右下 (139.35, 14.95) へ。H0 はスイッチの開口 13.95 で肉が 0.01 欠け、0.25 左へ |
| Freerouting が長円の穴を正しく避けず、穴と銅 0.3 を割る（縫いの GND ビアも） | 長円の穴の縁に配線禁止の帯（NPTH_KEEPOUT）を置き、route_pcb のビアの判定を穴の実物の形にした |

### 10-5. まだ確かめていないこと（見本を買って測る。**発注の前**）

| # | 何 | どうすれば決まるか |
|---|---|---|
| V1 | ~~静音の足の**位置決めの足が 5.15 と 5.50 のどちら**か~~ **（2026-09-26 §10-8: 5.50 は穴の中の突起の位置と読み直した。穴は丸 φ2.1 で両方を含む。残りは V13）** | 見本を基板の試し（または刷った小片）に挿す |
| V2 | スタビの支点の間 24.0 / 23.8 | 届いたスタビをノギスで（キャップの脚の位置を決める） |
| V3 | スタビの箱の大きさ（図の 5.80 × 7.30）と基板の下へ出る 3.30・爪の隙 1.65 と基板 1.6（最大 1.76） | 同上 |
| V4 | 静音の爪の隙 1.35 にプレート 1.2 で遊び 0.15（刷った PLA の厚さのばらつき） | 試し刷りの小片 1.2 |
| ~~V5~~ | ~~足の先と床の上面の間が最悪 0.04~~ | **2026-09-26 閉じた**: 足（端子 2・位置決め 1）の下にも止まり穴を掘った（§10-7）。穴の底から最悪 0.44 |
| V6 | 下面の「0.30±0.2」（標準の図）の正体 | 見本をノギスで（§8 の 1） |
| ~~V7~~ | ~~最下段のスペース 2 キーの周りにプレートが無い~~ | **2026-09-26 閉じた**: 切り離された枠を別に刷る（§10-6）。一枚板にしたいなら V8 |
| V8 | **一枚のプレートでスペースを囲むか**（別に刷る枠 2 つをやめる）。そのためにはケースの手前の面を約 1.0〜1.1 前へ出す（奥行き 99.45 → 約 100.5・キャップと壁の隙が手前だけ 2.4）。§10-6 の (a) | **利用者**（見た目・大きさ）。何も言わなければ枠のまま |
| V9 | スタビのプレートの高さでの奥の端（図の数字で 10.25、上面図の 0.70 の先 10.95 は基板の下で開く爪と読んだ）と、羽の奥の端 10.72 の隙 0.47 | 届いたスタビを基板の試し（または coupon_stab）に留めて、羽の奥の縁に爪・ワイヤが触れないか。触れたら 10.85 に戻し、奥の帯 1.075 を認めるか利用者と決める |
| V10 | 静音の V2 の爪が **±x の辺**にあること（図の上面図のつばの切り欠きから読んだ）。枠は桟の爪 4 つで留まる | 見本をプレートの小片（coupon_switch）にはめて、爪の位置を見る。±y なら枠は手前の爪 1 つとつばで挟まる（落ちないが緩い） |
| V11 | キャップの筒の腕の先の肉 0.675（0.4 ノズル 2 本より薄い）が刷れるか・こじって割れないか。窪みの深さ（筒 3.0 に対し約 4.3 と読んだ）・静音のつばの径 φ7.9（縮尺で） | coupon_stem（格子・外径 3 通り・10 回の抜き差し）。見本をノギスで |
| V12 | スタビの受け口のかかりが 1.05 しかない（軸が箱の上 3.60 しか出ず、押し切りで 0.55 しか残らない）。キャップを押し上げたときにスタビの軸が外れないか。**2026-09-26 の監査 E 重要 1: 実は 0.45（天板の中の穴は軸より上の空洞）。スタビの品の選び直しの後で直す（§10-8）** | coupon_stem のスタビの板を届いたスタビに挿して押す。外れるなら台を低い物にして箱の上面の穴（図の 5.50 の枠）に入るか見本で確かめる |
| V13 | 静音・標準の下面の小さな突起（位置決めの穴の中に来る。画素で 約 0.9 × 0.4 の矩形を 5.50・約 0.5 × 0.4 の角を 4.71。§10-8） | 見本を位置決めの穴 φ2.1 の基板の試し（または刷った小片）に挿す |

### 10-6. プレートの欠け（2026-09-26 に直した）

**何が起きていたか**: 10-2 の表のとおり、スペース 2 キーの羽の手前の端が外形から 0.225 しか残らず、羽を外形の外まで伸ばして
スイッチの周りの板（開口の手前の板と桟）ごと抜いていた。絵 `build/cckb/v2_plate_bites.png`（前）・`v2_plate_bites_after.png`（後）。

**検査を先に足して、直す前の板で落ちることを確かめた**（tests/test_cckb.py）:

| 検査 | 直す前の板で見つけた物 |
|---|---|
| `test_every_switch_is_framed_by_plate`（62 個の開口の手前・左・右〔スタビでないキーは奥も〕に板があるか。辺から 0.3 と 1.0 を 5 点ずつ刺す） | スペース 2 キーの手前・左・右（6 か所） |
| `test_no_plate_web_is_thinner_than_the_minimum`（`foundry.plate.thin_webs`: 上面を 0.6 縮めて戻し、消えた所を数える） | 13 か所: 羽の奥の端と 1 段奥のスイッチの開口の間の帯 **1.075**（スタビのキー 4 つの羽 8 つ）・桟の上の小さな突起 **0.525 幅**（Enter・左 Shift） |

帯 1.075 は前の絵では見えていなかった（Enter は「問題なし」と書いていた）。

**効く条件**: (1) どのスイッチも周りに板があり爪が掛かる (2) 板の帯は PLATE_MIN_WEB 1.2（0.4 ノズル 3 本）以上
(3) スタビの本体・ワイヤがプレートに当たらない（サリチル酸さんの開口は実物を測った物で、狭めるなら図の数字で根拠を書く）
(4) ケースの外形・見た目を変えない（変えるなら利用者が決める） (5) 基板は変えない（配線済み・DRC 0）
(6) プレートは上から落とせる（壁との隙） (7) 刷れる・組める・外せる

**候補と、何で確かめたか**:

| 案 | 数（スペース） | 結果 |
|---|---|---|
| (a) プレートの外形をその所だけ手前へ伸ばす | 帯 1.2 には外形を **0.975** 伸ばす要がある。壁の内面までは CASE_PCB_GAP **0.5** しか無い。壁 1.3 は肉厚の下限 1.2 に近く削れない | **ケースの手前の面を約 1.0〜1.1 前へ出さないと成り立たない**（奥行き 99.45 → 約 100.5・キャップと壁の隙が手前だけ 1.3 → 2.4）。見た目と大きさの話なので**利用者が決める**（下の V8）。左 Shift は角（XIAO の上・y −29.21）へ伸ばす所が無い |
| (b) 羽をスタビが要るだけに縮める | 図の数字（上面図の全長 18.75・爪の輪 φ3.50 を 8.50 に）で、プレートの高さ（基板の上 1.0〜2.2）に出るねじの側の端は支点から **8.50**（ボスの上面 2.85 はプレートの上面 2.2 より上）。帯 1.2 には羽の手前の端（広げた後）が 8.625 より内でなければならず、**ボスそのもの（8.50）と隙 0.125 しか残らない**。支点の位置のずれ（箱と穴の y の遊び 0.1・外形の公差 ±0.2）と刷った穴の縮みを見ると成り立たない | スペースは**不可**。ただし奥の端は図の数字でプレートの高さの奥の端が **10.25**（爪の輪）で、サリチル酸さんの 10.85 は 0.6 余る → **10.72 に詰めた**（帯 1.205・図との隙 0.47 ＋ STAB_KERF 0.15）。上面図の「0.70」（10.95 まで）は基板の穴を通って下で開く爪の先と読んだ（側面図で返しは基板の下）。**読みなので見本で確かめる**（V9） |
| (c-1) 切り離されたスイッチの枠を捨てずに**別に刷る** | 枠 = 開口の手前の板（幅 2.85）と両脇の桟（幅 1.745）。どちらも 1.2 以上。爪は図の上面図のつばの切り欠き（2.00 幅 ×2・両辺）から ±x の辺と読み、**桟に 4 つとも掛かる**。つばが上から押さえるので落ちない | **採った**（スペース 2 キー。`build/cckb/plate_frames_main.stl`・2 個で 1 枚・約 3 分）。**2026-09-26 訂正（監査 E 重要 4）: 枠はプレートにも基板にも留まらず、スイッチに挟まってぶら下がるだけ。スイッチを留めるのは基板のはんだで、枠は見た目と爪の掛かる所。「落ちない」は枠がスイッチから落ちないの意で、スイッチを保持してはいない** |
| (c-2) ワイヤの帯の上に橋を架けて枠を奥の板と繋ぐ | ワイヤの上端 2.07（側面図を縮尺で）＋0.3 → 橋 2.4〜3.6。押し切ったキャップの縁の下端は 4.15（標準）/ 4.55（静音）。橋はスペースのキャップとその奥の段の間から見える | 捨てた（見える・縮尺の読みに乗る・刷り方が難しい） |
| (c-3) スペースのスタビを 180° 回す（ワイヤを手前） | 爪の穴（支点から 8.37 ± 2.2）が基板の外形（キーの中心の 9.825 下）の外へ出る | 不可（基板） |
| (c-4) スタビを前後にずらす | スペースは手前（外形）と奥（段 3 の開口）の間 21.9 に羽 20.6 で、ずらしても和は 1.3 | 不可 |
| そのまま（板の無いスイッチ 2 つ） | — | 捨てた（依頼: 黙って受け入れない） |

**左 Shift** は左の羽が角の開口（XIAO の角）へ 0.075 かかって抜けるが、スイッチの枠は右の羽の外側（x −114.3〜−112.72・幅 1.58）で板に繋がっている。
枠は要らない（`test_the_frames_are_the_two_space_keys`）。**Enter** は奥の帯が 1.205 になった。

**壊して落ちることを確かめた**: 奥の端を 10.85 に戻す・突起を戻す → `thin_webs` が 1.08 / 0.5 を見つける（`test_the_web_check_notices_salicylics_back_edge`）。
枠を刷らない → 6 か所（`test_the_frame_check_notices_a_plate_without_frames`）。奥の端を 10.5 にする → 図との隙が 0.4 未満
（`tests/test_choc_v2.py::test_the_back_check_notices_a_back_edge_at_the_ring`）。サリチル酸さんの開口を含む検査は、奥の端だけを 0.13 の例外にした。

### 10-7. ケース・組み立て・キャップ（2026-09-26）

- **床の止まり穴を足の下にも**（V5 を閉じた）: `interface.switch_holes` が板に置いた足跡のファイルから穴 4 つを読み、
  端子 φ1.2 ×2・位置決めの長穴にも止まり穴（＋片側 0.4・深さ 0.4）。全部で 62 × 4 ＋ スタビの箱 8 = **256**。トレイが実際に掘り、
  外の底面は平ら・穴の下の床は 0.8（生成したトレイを刺して測る `test_the_floor_under_the_pockets_is_0_8`）。
  足の先の最悪（基板 1.44・足 3.2）は穴の底から **0.44**。剛性の検査は裏に出る物の最小の余裕（中心の突起 0.24）とたわみ 0.136 を比べる。
- **支えの柱 6 本を 0.5〜0.55 動かした**（止まり穴との肉 0.4。`interface.support_problems` と `assembly.pocket_problems`）。基板は変わらない。
- **滑り止めを 12 × 6 に**（4 つとも）。V2 の位置決めの長穴が最上段の中心の 5.15 下に来て、奥の 2 つの島（前は y 27.0〜35.8）の中に入った。
  段 0|1 の帯は高さ 5.9 しか空かず、16 × 8 は奥の角の近くのどこにも入らない（0.25 おきに総当たり）。奥は (−130.25, 31.5)・(136.75, 31.5)（左奥は §10-8 で −130.05 へ）。
- **組み立てモデルを V2 に**: 静音のスイッチ（胴 13.95・つば 15・上の胴 5.30・静音のつば φ7.9 を 5.70 まで・ステム φ6.5・窪み φ5.7・十字 4.00 × 1.30）、
  ねじ留めのスタビ（ボス・箱・肩・爪・ワイヤ・ねじの頭・軸。数字は図、図に無い肩・ワイヤ・爪の高さは縮尺で読んで [暫定]）、別に刷る枠。
  下へ出る物は**薄い板（−0.16）の分を足した包絡**（板は下面でボスに載るので、薄い板ほど先が下がる）。押し切りは静音の最大 **3.05**。
  干渉 0・入れる経路 0・止まり穴を消すとスタビの箱と突起がトレイに当たる（`test_the_stab_check_notices_a_tray_without_pockets`）。
- **電源スイッチのレバー（O13）とふた**: 基板の上面からの縁の高さ（7.0）は変えていないので、レバーの先とふたの上面の差は同じ（名目 0.1 下・最悪 0.36 出る）。
  ふたの検査（嵌め合い・爪・レバー）は全部通る。押し切ったキャップの上面は縁より 0.25 低い（V1 は 0.8・V2 の下書きの案 2 では 0.4 と見積もった。静音の行程で 0.25）。

**キーキャップ**（keycaps.py）: V1 の脚 2 本を、**静音の窪み φ5.70 に入る十字の筒**に替えた。

| 所 | 値 | 理由 |
|---|---|---|
| 筒 | 外径 5.5・長さ 3.0・十字の穴 4.15 × 1.40 | 研究の数。**腕の先の肉 0.675**（0.4 ノズル 2 本 0.8 より薄い）。窪みの深さは図に無く、標準 V2 の立体で約 4.3 → 1.3 余る |
| つばの窪み | 天板の下面を輪 φ6.5〜8.7・深さ 0.25 | 押し切り 3.05 で天板の下面は 5.55、つばの上面は 5.70。0.25 − 0.15 = 0.1 残る。**最初は内径 6.7 にして、押し切りの干渉検査でつばの内の縁（0.05 幅）に当たった**ので 6.5（ステムの外径）に |
| スタビの受け口 | 天板の下の台 φ5.5・高さ **0.45** に十字の穴 4.10 × 1.36、穴は天板の中へ（上に 0.6 残す）。かかり 1.05 | スタビの軸は箱の上面（5.00）から 8.60 まで 3.60 しか出ず、押し切り 3.05 で 0.55 しか残らない。**筒にすると押し切りで箱に当たる**。支点は ±12.0（図の 24.0）。23.8 かは見本で（V2） |
| 天板 | 1.2（いまの決まり）。つばの窪みの所だけ 0.95 | 依頼どおり 1.2 のまま。**→ 2026-09-28 に天板を場所ごとの厚さへ（ステムの上は膜）。2026-10-03 から既定の膜 1.0（上面 14.2）: decisions/2026-09-28-keycap-skin.md §8** |

**天板 0.8 の案（実装していない・測った数の記録）**: 天板を 1.2 → 0.8 にすると全体は 0.4 薄く（キャップの上面 14.4 → 14.0）、
キャップ 62 個の天板の面積 23,170mm² × 0.4 で約 −9.3cm³・約 −11.5g（PLA 1.24。研究 calc.py と同じ数え方）。0.2 層で 4 層。つばの窪み（0.25）の所は 0.55 で 3 層を割る。
縁との差（押し切り）は 0.25 → 0.65 に増える（鞄の中で押されにくい）。刷ったときのたわみ・透けは見ていない。**利用者が決めること**。

**試し刷りの小片**（coupons.py）: スイッチの開口 13.90〜14.05・V2 のスタビの U 字の開口（広げ 0.05 / 0.15 / 0.25）・
`coupon_stem` = 十字の穴の格子（幅 1.35 / 1.40 / 1.45 / 1.50 × 長さ 4.10 / 4.15 / 4.20）＋筒の外径 5.3 / 5.4 / 5.5 の小さな天板 3 枚
（**こじって外し、腕の先が割れないかを見る**: 1 枚ずつ静音のスイッチに挿し、天板の縁に爪をかけて 10 回抜き差しする）
＋スタビの受け口の板 2 枚（支点 24.0 / 23.8。届いたスタビを基板の試しか手で持って、両端が同時に入る方）。

### 10-8. 発注前の独立監査（5 視点）の直し（2026-09-26。所見と裁定は .superpowers/sdd/cckb-autonomy/audit-v2-findings.md）

**板**（前 sha256 dae52e33… → 後 **6b886491…**。DRC 違反 0・未配線 0・警告 0〔前は silk_edge_clearance 4〕）。
描いた絵: `build/cckb/pcb_v2_locator_round_{one_key,enter,left_shift,space_left}.png`（前と後を並べた）。

**スタビに関わる所見（C 重要 1 のうちスタビのねじ・爪の長円 16 個・C 軽微 1〔箱の穴〕・C 軽微 2・E 重要 1〜3・E 軽微 2・C 軽微 4 の
スタビのコートヤード）は保留**。利用者の依頼で、24.0 / 23.8 を両方含めて逃げるのでなく本当の仕様を探したところ、Kailh 公式の
Choc V2 スタビ **CPG1353G24D01**（プレート留め・Keebio が販売。Keebio の KiCad の足跡 `Kailh-Choc-V2-2u-Stabilizer-CPG1353G24D01-Cutout`
の切り抜きは x ±8.75〜±15.25・y ±4.75 = 支点 ±12.0）が見つかり、スタビの品を選び直すかもしれない（選べば基板のねじの穴そのものが
無くなる）。**スタビの足跡・穴・キャップの受け口・手順書のスタビの手順は 931af25 のまま。**スタビのねじ・爪の長円 16 個は JLC の
長円の規則を満たさないので、**発注は止める**（open-gaps ★ #6）。

**C 重要 1（位置決めの長円 62 個）: 丸 φ2.1 にした。**JLC の能力表（<https://jlcpcb.com/capabilities/pcb-capabilities>・2026-09-26 に読んだ）:
「The length of the slot should be at least 2 times of the width」・非めっきの長円の最小幅 1.0・長円の公差 ±0.2・穴の位置 ±0.05。
丸穴の公差は JLC のブログ（npth-design-guide）で ±0.08、能力表の穴で +0.13 / −0.08。前の長円 1.6 × 2.0 は比 1.25。Kailh の静音の推奨の
長円 2.0 × 1.5 も比 1.33 で、そのままでは作れない。**KiCad の DRC はこの比を見ない。**

| 条件 | 何で確かめたか |
|---|---|
| 1. JLC が作れる形（長さ/幅 ≧ 2 か丸） | 丸 φ2.1。発注の道具が出した NPTH.drl を読む検査（下） |
| 2. 入る物 | 3 枚の図の推奨の穴（標準 φ1.60・静音 長円 2.0 × 1.5・どちらも中心から (5.15, 5.00)）の和を、公差 −0.08 でも含む（2.02 ≧ 2.0）。**底面図の「5.50」は穴の位置ではなく穴の中の突起**（細い矩形の中心。静音 茶の図 CPG1353S01D02-01〔Kailh 公式サイトの PDF〕を 600dpi で描き出し画素で読んだ。5.15 の寸法線は破線の長円の中心に当たる。標準 CPG135301D01 の底面図にも同じ突起）。突起の最も遠い角 約 0.79 に対し、公差の最悪（−0.08・位置 ±0.05）の半径 0.96。前の「位置決めの足が 5.15 と 5.50 の 2 版」の読みは改めた |
| 3. 銅との間 | 前の板の銅に丸 φ2.1 を当てて最短 0.336（GND の縫いビア。縫いは穴の形で打ち直す）。DRC 違反 0 |
| 4. 波及 | 床の止まり穴が丸 φ2.9 に（x に 0.25 広がる）→ 支えの柱 4 本を 0.1・左奥の滑り止めの島を 0.2 動かした（肉 POCKET_WALL 0.4） |

捨てた案: Edge.Cuts の切り抜き（ルータ・外形の公差 ±0.2 で幅 1.6 が 1.2 まで縮む）・比 2 の長円 1.6 × 3.2（奥へ伸ばすと行のバスに近づき、
幅は公差で 1.2 → 突起 0.9 が入らない）・そのまま出して JLC の確認に任せる（裁定で不可）。足跡は名前も替えた
（`SW_Kailh_Choc_V2_Slot` → `SW_Kailh_Choc_V2_Common`）。

検査を先に足し、**前の板で落ちることを確かめた**: `tests/test_cckb_pcb.py::test_every_slot_on_the_board_is_long_enough_or_round`（板の穴 285・
非めっき 151・長円 78。保留したスタビの 16 を除いて前の板で 62 件）と `test_the_drill_files_sent_to_jlc_have_no_short_slot`（**発注の道具が出した
zip の NPTH.drl** を読む。前の板で短い長円 78 ≠ 保留の 16）。いまの板の長円は保留したスタビの 16 だけで、数を固定した例外（`HELD_STAB_SLOTS`）。位置決めの 1.6 × 2.0 に戻すと
`test_the_slot_check_notices_the_first_v2_board` が落ちる。`tests/test_choc_v2.py` は丸であること・推奨の穴を公差の最悪で含むこと・突起が
入ることを見て、長円に戻す・φ2.0 / φ1.6 にすると落ちる。

**配線**: 全部を引き直すと Freerouting が COL5・COL6（U1 の 5・6 番から SW34・SW35 へ）を余裕 30・35µm で引けなかった（位置決めの穴が
x に 0.25 広がって U1 の脇が狭まった）。**監査の済んだ配線を動かさない**ために `route_pcb.py --reroute CS` で前の板の線とビア
（GND と計画が引く ROW*・SW*_D を除く 22 網・315 本）をそのまま持ってきた。持ってきた線は新しい禁止域に掛からず、Freerouting を回さずに
繋がった（島・縫いの数も前と同じ）。route_pcb は、計画が引く網を前の板から持ってこないようにした（計画が変わったとき前の線が残る）・
長円が無いときは NPTH_KEEPOUT を求めないようにした。

**C 軽微 3: 名札。**D42・D43・D58・D60 の名札をダイオードの左へ（spec.REF_TEXT_AT）。DRC の警告 4 → 0。

**E 重要 4**（スペースの枠がスイッチを保持していない）: 記録・手順書・検査の説明を直した。枠をやめるか・ケースを前へ出すかは利用者（O15）。
**E 軽微 1**: ダイオードの向き（62 個とも帯が手前・D_PWR だけ左。板のパッド 1 の位置で数えた）を手順書に。**B 軽微 3**: 端子 2 のはんだ。
**A 軽微 1**: `&xiao_i2c { status = "disabled"; }`（commit ecc3ca9・main にも要る）。

### 10-9. スタビの穴を販売者の実測に合わせ、きつい側に倒す（2026-09-26・利用者と決めた）

**何を正にするか**: 販売者（遊舎工房／自キ温泉街販売所・サリチル酸さん）に確かめた結果、記事の仕入れ先の図
（支点 24.00・ねじ φ3.00・箱の穴 8.00 × 6.00・爪 φ4.00 を 8.50）は「参考程度」、KiCad の足跡
（`Choc_v2_PCBMountStab_2u`・`Stab_Hole_Choc_v2_PCBMount_2u`）は「実際のパーツの実測から割り出しています」。
**足跡（実測）を正、図を参照**にする。足跡に無い値（箱の大きさ・高さ・十字・爪の輪・ねじの頭）だけ図から読む（[暫定]・見本で測る）。

**なぜ前の決め方（2 出典の和・§10-3）を捨てたか**: 和は「どちらの実物でも入る」だけを見て、ゆるさの害を見ていなかった。
ねじ留めのスタビは締める前に穴の遊びの分だけ動く（監査 E 重要 3: x ±0.2）のに、キャップの受け口の隙は片側 0.05〜0.075。
しかも長円 3.2 × 3.4・4.2 × 4.4 は JLC の「長さ ≧ 幅 × 2」を満たさず作れない（C 重要 1）。基板は発注後に直せないので、
**直せる側（きつい・小さい）に倒し、直す手段（広げる余地）を設計に入れる**（docs/method/lessons.md K・CLAUDE.md）。

**基板の穴（決めた値。スタビの座標: 箱の中心が原点・y はワイヤ〔爪〕の側が +。板ではワイヤは奥）**

| 所 | 値 | 理由 |
|---|---|---|
| 支点 | **±11.9**（23.8） | 足跡の実測。1 つのスタビの穴は全部この x に揃う |
| ねじの穴 | **丸 φ3.0（非めっき）を y −6.2** | 図の φ3.00・足跡の y。前の長円 3.2 × 3.4 を置き換え。箱の中のナットの胴 φ2.78（図）が下から 1.15 入る: 片側 0.11。JLC の丸穴の公差 −0.08 でも 2.92 |
| 爪の穴 | **丸 φ4.0 を y +8.24** | 足跡の位置（図は 8.50）と足跡の長円 3 × 4 の長い幅（= 図の φ4.00）。前の長円 4.2 × 4.4 at 8.37 を置き換え |
| 箱の穴（Edge.Cuts） | **x 支点 ± 3.0（8.9〜14.9）・y ±4.0** | x は足跡・図とも 6.0。y は図の推奨 8.00（足跡 7.5 より広い。箱 7.30 との隙 片側 0.35）。前の「x に片側 0.3 足す」（`STAB_RELIEF_MARGIN`）は消した。x の隙は片側 0.1 で、外形の公差 ±0.2 できつければやすりで広げる |
| 穴の周りの禁止域 | **ねじ・爪の穴の中心から半径 2.6 の中は GND のベタのほかに銅なし**（線・ビア・ほかの網のパッド。両面。`spec.STAB_HOLE_KEEPOUT_R`・`pcb_extra` の `STAB_HOLE_KEEPOUT`） | 穴がきつければ手でリーマ・やすりで広げる。そのとき信号を切らない。2.6 = 爪の穴の半径 2.0 ＋ 0.6（広げる余地 0.3 ＋ JLC の穴と銅 0.3） |

- ねじの穴と箱の穴の間の基板の橋: 6.2 − 1.5 − 4.0 = **0.7**（外形の公差 ±0.2・穴の位置 ±0.05 の最悪で約 0.45）。**ねじを締めすぎない**（C 軽微 2・手順書 手順 5）。
- 締める前のずれ（E 重要 3 を丸穴で計算し直した）: ナットの胴 φ2.78 とねじの穴 φ3.0 で **±0.11**（穴の公差 +0.13 の最悪で ±0.175）、
  箱 5.80 と箱の穴 6.0 で x ±0.1（最悪 ±0.3）、爪の輪 φ3.5 と爪の穴 φ4.0 で ±0.25。x はナットと箱の小さい方の **±0.1**。
  キャップのスタビの十字の穴 4.10 × 1.36 と軸 3.95 × 1.26 の隙は片側 0.075 / 0.05 なので、**2.25u のキャップ（かスイッチ）を挿した状態で本締めする**（手順書 手順 5・6）。
- 足跡 `lib/keyswitch.pretty/Stab_Kailh_Choc_V2_Screw_2u` に**コートヤード**を付けた（スタビの本体・図の全長 18.75 ＋ 0.25。C 軽微 4 のスタビの分）。
  DRC の courtyards_overlap は見るが、missing_courtyard を ignore にしている事情（A15 (2)）はスタビについては無くなった。
- 検査: `tests/test_cckb_pcb.py::test_the_stab_holes_are_what_we_decided`（**発注する板**を KiCad で読み、決めた数そのものと比べる:
  4 つのスタビ・16 の丸穴の位置と径・長円でない・箱の穴の 4 辺・半径 2.6 の中の線 / ビア / パッド 0・GND 以外のベタ無し）と、
  壊す検査 `test_the_stab_hole_check_notices_a_break`（線を通す・ビアを置く・穴を 0.1 動かす・長円に戻す・爪を φ4.4 に・箱の穴を 0.4 広げる・V3V3 のベタを足す、の 7 通りで落ちる）。
  足跡は `tests/test_choc_v2.py::test_the_stab_holes_are_what_we_decided`（足跡・図との照合。壊す 8 通り）・`test_the_stab_footprint_is_the_holes`（壊す 4 通り）。
  **長円の例外 `HELD_STAB_SLOTS` を消した**: 板の長円 0・JLC に送るドリルのファイルの短い長円 0（`test_every_slot_on_the_board_is_long_enough_or_round`・
  `test_the_drill_files_sent_to_jlc_have_no_short_slot`。前の長円に戻すと 16 件で落ちる `test_the_slot_check_notices_the_old_stab_slots`）。

**プレートの開口（§10-6 の見直し）**: 販売者のプレートの足跡の値に戻した（支点 11.906・羽の幅 6.0625 = 8.87125〜14.9375・手前 −9.45・
奥 10.85・桟 1.82・ワイヤの帯 ±8.375 を 9.85 まで）。**支点 24.0 のための +0.1（羽の外の辺 15.0375）を消した。**残した妥協は 5 つだけ
（`foundry/mech.py` の `CHOC_V2_STAB_PLATE` のコメントにも同じ理由）:
1. 羽の奥の端 10.85 → **10.72**: STAB_KERF を足すと 1 段奥のスイッチの開口との帯が 1.075 で、刷れる帯の下限 1.2 を割る（10.72 で 1.205）
2. スペースの羽の手前（外形から 0.225）を外形の外まで伸ばし、切り離された枠を別に刷る（O15 で利用者の判断待ち。変えていない）
3. 桟の上の小さな突起（幅 0.525 になる）を穴に含めた
4. 円弧・角の丸みを外接する矩形に（穴が大きくなる向きだけ）。羽の内の辺は左右の和 8.87125
5. **左 Shift の左の羽が角の開口（XIAO の角）へ 0.075 かかって、プレートの外の開口とつながる**（§10-6。角へ伸ばして板を足す所が無い。スイッチの枠は右の羽の外側〔幅 1.58〕で板につながるので、別に刷る枠は要らない。2 回目の V2 監査 E-7 で「妥協は 4 つだけ」から足した）
刷った穴の縮みは STAB_KERF（片側 0.15・HHKB #30 の実測）が受け持つ。これは形の妥協ではなく刷り方の補正。
検査: `tests/test_choc_v2.py::test_the_plate_stab_opening_is_salicylics_but_the_listed_changes`（15.0375 に戻すと落ちる）・
`test_the_plate_stab_opening_contains_salicylics`（羽を 0.1 縮めると落ちる）。

**キャップ・ケース・組み立て**
- キャップのスタビの受け口: 支点 **±11.9**。**E 重要 1（掴みが 0.45）を直した**: 図の断面 A-A（ねじの軸 1.94 = M2 と同じ縮尺）で、軸の十字の下は
  スライダーの胴（幅 約 5.5）が箱の上面の口の中を上下する。台の下端と胴の上面の距離は押しても変わらないので、**台を口より細く（φ5.1）して
  2.0 掴む**（前の 4.4 倍）。押し切ると台は箱の上面から 1.45 下へ入る（組み立てモデルで押し切りの干渉 0。台を φ5.9 にすると当たって落ちる検査）。
  値は [暫定]。**新しい小片 `coupon_stab_return`**（基板の代わりの板 1.6〈本番と同じ穴の位置・刷った穴は片側 0.15 広げる〉＋本番の 2.25u のキャップ）で、
  スタビをねじで留め、スイッチを挿し、キャップを押し切って離し、**スタビの両端の軸がキャップと一緒に上まで戻るか**を 10 回見る。
- **E 重要 2（ねじの頭）**: 図の断面で頭 φ3.7・厚さ 1.5（[暫定]）。床の内側に頭の下の止まり穴 8 個（φ3.7 ＋ 片側 0.4・深さ 0.4）を足した（止まり穴は 264）。
  頭の下の床まで 0.3 → 穴の底まで 0.7。組み立てモデルの頭も φ3.7 × 1.5 に。
- 組み立てモデルのスタビ: 爪・ワイヤを足跡の 8.24 に、押したときは箱の上面の口（5.5 角）が行程だけ空く。

**配線（スタビのキーの周り）**: 板の生成し直しと `route_pcb.py --reroute`（監査の済んだ配線は持ってくる）。
- 行のバス: 箱の穴とねじの穴の禁止域の下を回る。回り道の高さはスタビのキー 4 つともキーの中心の **8.95 下**（バスから 5.6 下。前は 8.35 下）。スペースでは基板の縁（9.825 下）の配線禁止の帯まで線の縁から 0.46。`matrix_routes` の計画のまま引けた（禁止域の円を障害物に足した。板から数えた）
- 左 Shift の左のねじの穴の禁止域が XIAO の奥の列のパッドのすぐ上に来て、VBAT_SW（R_HI への枝）・V3V3（XIAO の 3V3 へ）・SPI_MOSI（D10 へ）の
  通り道を塞いだ（禁止域の下とパッドの上の間 0.73 に、3V3 と D10 へ上から入る 2 本が表で交わる）。Freerouting は余裕 30µm で 3 本引けないまま 14 回回った。
  **決まった形で引いた**（`spec.FIXED_RUNS`・`matrix_routes.fixed_runs`）: VBAT_SW は箱の穴の右を上がり、箱の穴と爪の禁止域の間（y −14.1）を左へ回って R_HI へ（約 30mm 長い・0.3 幅で 0.05Ω）。
  V3V3 は裏で禁止域の下をくぐり、3V3 のパッドの上でビアを立てる。SPI_MOSI は前の表の形のまま、裏の線の端でビアを立てる
- Enter の左の行 2 の回り道が、Freerouting が前に引いた COL14 の裏の線（y −9.14）と重なった（DRC の短絡 1）。COL14 だけ Freerouting で引き直した

**基板の嵌め合いの総点検（非対称の規則・lessons K。2026-09-26）**: めっきの穴は削ると銅が取れるので「きつい側が直せない」。非めっきの穴と外形は削って広げられる。

| 嵌め合い | きつい側に外れたら | ゆるい側に外れたら | いまの選び | 判定 |
|---|---|---|---|---|
| スイッチの中心穴 φ5.05（NPTH）と突起 φ4.8 | 突起が入らずスイッチが浮く → リーマで広げられる（行のバスは穴の縁から 0.725） | スイッチが ±0.125 動くが、位置はプレートの開口 13.95 と端子のはんだで決まる（害なし） | 片側 0.125（公差 −0.08 でも 0.085） | よい |
| 位置決めの丸穴 φ2.1（NPTH） | 下面の突起が当たって浮く → 広げられる | 何も位置決めしていない（害なし） | 突起の角と最悪 0.17 | よい |
| スイッチの端子の穴 φ1.2（めっき） | 足が入らない → **直せない**（めっきを削れない） | はんだが埋める（害なし） | Kailh の推奨 φ1.20・足 0.8 幅 | よい（めっきはゆるい側が正しい） |
| 取付の穴 H0〜H9 φ2.2（NPTH）と M2 | ねじが通らない → 2.4 に広げられる（ナットの下の禁止域の中） | 基板がケースに対して ±0.1 動く（壁との隙 0.5・害なし） | M2 の普通の通し穴 | よい |
| XIAO のパッド・パッド内ビア | ― | パッドは公式 STEP のキャステレーションより 0.6 外へ（はんだの余裕。害なし） | 検査が STEP と照合 | よい（嵌め合いではない） |
| 電池ホルダ BS-16-B4AK003 | ― | パッドは図のランドの大きさ（表面実装・穴なし） | 図のまま | よい |
| 電源スイッチ SS-12D00G3 の穴 φ0.8（めっき） | 足が入らない → **直せない** | はんだが埋める（害なし） | 図の推奨 φ0.8・足の対角 0.58 | よい（めっきはゆるい側） |
| ふたの柱の穴 φ6.0（NPTH）と柱 φ5.2 | ― | 柱は基板の位置を決めていない（害なし） | 片側 0.4 | よい |
| スタビのねじの穴 φ3.0（NPTH） | 入らない → **手で広げる**（半径 2.6 に信号なし） | スタビが締める前に動き、キャップと合わない（直せない） | きつい側（足跡の長円 3.2 × 3.4 より小さい）＋ 禁止域（§10-9） | よい（今回直した） |
| スタビの爪の穴 φ4.0（NPTH）の **y** | 入らない → 手で広げる | 爪が掛からない | 足跡の長円 3 × 4 の長い辺（y）と同じ 4.0 | よい |
| スタビの爪の穴 φ4.0 の **x**（**販売者の 3.0 より 1.0 ゆるい**） | ― | 爪の輪 φ3.5 が x に ±0.25 動ける | ゆるい側を選んだ | **害なし（数で示す）**: スタビの x と y はナット（ねじの穴 φ3.0 の中の胴 φ2.78・±0.11）と箱（箱の穴で x ±0.1）が決め、爪の穴は位置を決めていない。爪が掛かる（返しが基板の裏に引っ掛かる）向きは y で、y の幅は足跡と同じ 4.0。しかも足跡の長円 3 × 4 は JLC の「長円の長さ ≧ 幅 × 2」を満たさず作れない（C 重要 1） |
| スタビの箱の穴の **x** 6.0（Edge.Cuts） | x が片側 0.1 で、外形の公差 −0.2 だときつい → 縁を平やすりで削れる。箱の穴の縁から信号の銅の縁まで最短 0.371（板で測った）で、0.2 削っても 0.17 残る | ― | 足跡・図とも 6.0 | よい（削る余地は 0.2 まで。GND のベタは縁から 0.3 引いてある） |
| スタビの箱の穴の **y** 8.0（**販売者の 7.5 より 0.5 ゆるい**） | ― | 箱 7.30 が y に ±0.35 動ける | 図の推奨 8.00 | **害なし（数で示す）**: y はねじの穴（ナットの胴・±0.11）が決め、箱の穴は位置を決めていない。しかも**JLC のルータの内の角は R0.5**（刃 φ1.0。JLC の記事 <https://jlcpcb.com/blog/rounded-corners-pcb-design>）で、角の丸みに箱（5.80 × 7.30）の尖った角が入るのは y 8.0 だけ: 丸みの中心 (±2.5, ±3.5) から箱の角 (±2.9, ±3.65) まで 0.427 ≦ 0.5（隙 0.073）。7.5 だと中心 (±2.5, ±3.25) から 0.566 > 0.5 で、4 つの角が当たる。x は片側 0.1 なので外形の公差 −0.2 側では 8.0 でも角が当たりうる → **角を丸やすりで削る**（手順書 手順 5 の 1・C-2） |

ゆるい側を選んだ物は 2 つ（爪の穴の x・箱の穴の y）。どちらも位置を決めていない穴で、ゆるさの害が無いことを上の数で示した。
（2026-09-26 の 2 回目の V2 監査 B-1・E-1・E-2: 前の表は爪を「きつい側」と一括りにし、この 2 つのゆるい側を書いていなかった）
直した物はスタビの穴だけ。

### 10-10. 2 回目の V2 監査（5 視点・致命 0・重要 0）の軽微の直し（2026-09-26 夜）

**基板（変えたのは GND の縫いのビアと名札とコートヤードと規則だけ。網の差は 92 網のうち GND のビアだけ）**: 板 5f02d2b0 → **abcd20ff**。
DRC 違反 0・未配線 0・警告 0。`route_pcb.py --keep`（GND 以外の線・ビアを全部前の板から持ってくる。変更前の板で線・ビア・塗りが
同じに戻ることを先に確かめた）。

| 所見 | 直し | 確かめ |
|---|---|---|
| D-1 裏の GND の帯（ROW4 と手前の縁の間・幅 約 1.0・x −124.5〜−97.7）にビアが無く、帯の先から最寄りのビアまで**銅の上の道のり 33.3**（アンテナのチップから 7.3） | 帯の真ん中の y −47.12 に 5.5 おき 5 本（`spec.GND_STITCH_AT`・route_pcb が最後に打つ・置けなければ止まる）。ROW4 の線の縁まで 0.42・外形まで 0.505 | 道のり 33.3 → **3.1**（`test_the_gnd_strips_the_audit_named_reach_a_via`・ビアを消した写しで 30 超に戻る検査）。絵 `build/cckb/pcb_gnd_strip_D1_before_after.png` |
| D-2 表の島（左 Shift の左の箱の穴を VBAT_SW が U 字に囲む所）の先から 12.3 | **勧めの「左上に 1 本で 3 以下」はできない**: U の左の腕 1.006・上の腕 0.8 にビア（φ0.6 ＋ 線との間 0.25 ＋ 外形との間 0.35 = 1.2）が入らない。島の中の置ける点を全部試し、最遠をいちばん縮める U の右上に 1 本 | 12.3 → **10.3**。残りは腕の中の細い塗り（幅 0.25〜0.46）で、消すかはベタの形の変更（open-gaps P14）。絵 `pcb_gnd_island_D2_before_after.png` |
| C-3 R_LO の名札がパッドのマスクの開口から 0.081 | 名札を部品の中心の右 3.2 → 3.35 | 0.231。板のシルクの字 208 個の最小（`test_no_silk_text_is_near_a_mask_opening`・下限 0.15）。絵 `pcb_silk_R_LO_before_after.png` |
| C-4 穴と銅の距離が KiCad の既定 0.25（JLC の PTH と線は 0.28） | `.kicad_pro` の min_hole_clearance を 0.28（`spec.DRC_PTH_HOLE_CLEARANCE`・`pcb_rules.JLC["pth_to_track"]`）。ベタは 0.28 で塗り直し（表 −56.7・裏 −60.9 mm²） | 前の板をこの規則で見ると hole_clearance **206 件**、塗り直した板は 0。写しの規則を 0.30 にすると DRC が出す検査 |
| B-3 スタビの足跡に裏のコートヤードが無い | B.CrtYd を左右に（箱 5.80 × 7.30・ねじの頭 φ3.85・爪の穴 φ4.0 と先 10.95 ＋ 0.25） | `test_the_stab_footprint_has_a_bottom_courtyard`（消す・縮めると落ちる）。ケースの支え 4 本がコートヤードに掛かり（左右の形ごとに見る。`board_geometry` の back_parts）、うち 2 本は下の E-6 の止まり穴の肉 0.4 を割ったので動かした（`spec.SUPPORTS` のコメント） |

**D-1 の帯は V1 の板（`main`・571aab5・板 d158cb59）にも同じ形である**（2026-09-26 に `git show main:` の板で道のり 33.2 を測った）。
`main` は触っていない。V1 で発注するなら同じ直しが要る（利用者が決めること）。

**監査の外で測って見つけた物**（直していない・open-gaps P14）: 同じ道のりの物差しで板全体を測ると、裏の本土の中の信号の束の間の細い帯
（x 約 +86・y 約 −10 で 26.6、x 約 +63・y 約 −12 で 17.0、x 約 +52・y 約 −10 の島で 12.9）も長い。どれも幅が狭くビアが入るかは未確認。

**記録・ケース・キャップ・ファーム**:
- B-1・E-1・E-2: 上の §10-9 の嵌め合いの表を書き直した（爪の穴の x・箱の穴の y はゆるい側で、害が無いことを数で示す）。E-7: プレートの妥協を 5 つに（`foundry/mech.py` のコメントも）
- E-3: `coupon_stem` のスタビの板を、支点 24.0 / 23.8 の 2 枚から、**支点 23.8・十字の穴の幅 1.31 / 1.36 / 1.41 の 3 枚**に。軸が戻らなければ**まず幅を締める**（`provisional-values-case.md`）。台 φ5.1 と十字の穴 4.10 の端の肉は 0.5
- E-6: ねじの頭の読みが 2 つ（φ3.7 × 1.5 / φ3.85 × 1.6）。大きい方を持ち、床の止まり穴を φ4.5 → **φ4.85**（片側 0.5 = 位置のずれ ±0.275 ＋ 0.2）
- E-4・E-8・C-2: 手順書（手順 5 の 1 の理由・手順 6 の 5 で軸を指で引き上げる・箱の穴の角を丸やすりで）
- E-5: スタビの断面 4 枚（横・横の押し切り・支点・スペース）を `assembly.render_all` で毎回出す
- A-1: `check_zmk_config` が xiao_serial（D6・D7）も見る（ボードの dts の写し `foundry/upstream/xiao_ble_zmk.dts` か overlay）
- C（範囲外）: `order-steps.md` を V2 に（ダイオード 62 個とも 90°・D_PWR 180°・スタビの行）

## 検討して捨てた案

| 案 | 捨てた理由 |
|---|---|
| スイッチを 90° / 270° に回して、位置決め穴をバスから逃がす | どの向きでも端子か位置決め穴がキー中心の 4〜6 下の帯に来る（§5）。端子の位置も変わり、列の配線まで引き直しになる |
| サリチル酸さんの足跡（端子が下・位置決め (5, −5.55)） | 位置決めが図の 5.15 と 0.4 違う。端子も V1 と逆向きで、配線を残せない |
| スタビ C（Gateron KS-57）・D（V1 のスタビを流用） | §3-2。高さ（2.35 / 0.6 低い）と行程 3.2 を満たすか確かめられない。D はプレートを 1.2 に縛る |
| 中心の突起を切る | 62 本。切り口の高さがばらつき、手間も大きい |

## この決定が乗っている前提（動いたら読み直す）

- スイッチは直付け（D3）・基板 1.6（O3）・床 1.2（O10）・キャップは自分で刷る（D14）。
- スタビの寸法はメーカーの公式の図ではなく、販売者が公開した抜粋に乗っている。公式の図が出たら突き合わせ直す。
- 高さは「ハウジングの下面が基板に着く」読みに乗っている（§8 の未確認 1）。

## 覆す前に読むこと

- Kailh CPG135301D01（上の URL）の 1 ページ目。V1 の CPG135001D01 と並べて読む
- kiswitch `SW_Kailh_Choc_V2.kicad_mod`・サリチル酸さんの `KiCAD_FootPrint`（`kbd_Stabilizer.pretty/Choc_v2_PCBMountStab_2u`・
  `kbd_SW_Hole.pretty/Stab_Hole_Choc_v2_PCBMount_2u`）
- サリチル酸さんの記事 <https://salicylic-acid3.hatenablog.com/entry/chocv2-stab-guide>（スタビの図 3 枚・向きの注意・基板とプレートの厚さ）
- 遊舎工房 <https://shop.yushakobo.jp/products/13985>・<https://shop.yushakobo.jp/products/kailh-choc-v2>、
  共立 <https://eleshop.jp/shop/g/gQ5DV1F/>・<https://eleshop.jp/shop/g/gQ5DV1T/>、Keeb-On <https://keeb-on.com/products/stabilizer-chocv2>
- Gateron KS-57B210T <https://gateron.com/u_file/2311/22/file/GATERONLowProfilePlateMountedStabilizer2U-KS-57B210T.pdf>
- Keebio `Kailh-Choc-V2-2u-Stabilizer-CPG1353G24D01-Cutout.kicad_mod`（Kailh の品番らしい CPG1353G24D01 の開口 6.5 × 9.5 を ±12.0。
  **この品番の図面と売り場は見つけていない**）
