ms0216/keyboard-foundry/projects/cckb/docs/decisions/2026-09-28-keycap-skin.md

# キーキャップの天板を場所ごとの厚さにする（ステムの上は膜。**既定の膜 1.0・上面 14.4 → 14.2**）

- **日付:** 2026-09-28（膜 0.6・上面 13.8）→ **2026-10-03 利用者の決定で既定の膜を 1.0（上面 14.2）に**（§8）
- **状態:** 決定（利用者）。**いまの値は §8**。§1・§3〜§7 の「いま」は 2026-09-28 の膜 0.6 の記録（見出しに書いた）。
  膜 0.6 は見積りで縁を押すとステムのまわりの輪が割れる（§4）ので既定にしない。`coupon_skin` で 0.8 が割れなければ 0.8（14.0）に下げてよい
- **決めた人:** 利用者（2026-09-28: 膜 0.6・外は下へ 1.0・押し切りで何にも 0.1 残す。**2026-10-03: 既定の膜 1.0**）。形・数の導き方・小片は Claude（枝 `cckb-keycap-skin`）

## 1. なぜ決める必要が生じたか

天板はステムの上面から一様に 1.2（`KEYCAP_TOP_T`）で、キャップの上面は机から 14.4。利用者の考え:
ステムの真上の天板は下からステムの上面に支えられるので曲げの硬さが要らず、薄くできる。硬さが要るのは
ステムから離れた所（キーの縁）だけ。そこで

- ステムの上の膜 **0.6**（上面 = ステムの上面 ＋ 0.6）
- それより外は下へ **1.0** まで厚くする。ただし押し切り（行程の最大 3.05）で天板の下面が、ハウジングの上面 5.30・
  静音のつば 5.70（φ7.9）に **0.1 以上**残る所だけ。つばの輪とステムの上は膜だけ
- 筒（十字を掴む）は膜から下げ、掴む深さはそのまま。2.25u のスタビの受け口も新しい天板に合わせる

## 2. 事実（数の出所）

| 値 | 数 | 出所 |
|---|---|---|
| ステムの上面 | 基板の上 8.60 | Kailh 図 CPG1353S01D02-01（正面図 6.40 ＋ 2.20）・`spec.SWITCH_STEM_ABOVE_PCB` |
| ハウジングの上面・つば | 5.30・5.70（φ7.9 は縮尺で読んだ [暫定]） | 同・`spec.SWITCH_TOP_ABOVE_PCB`・`SWITCH_COLLAR_*` |
| 行程 | 2.8 ± 0.25 → 最大 3.05 | 静音の図の仕様欄 9 |
| スタビの箱の上面・軸の上端 | 5.00・8.60 | 仕入れ先の図（参照）`mech.CHOC_V2_STAB_SOURCES` |
| 上の胴の平面の大きさ | 図に無い → 組み立ての包絡（開口と同じ 13.95 角）を使う | `assembly.switch_solids` |
| 刷る層 | 0.2（スライサーは層の真ん中で切る） | `docs/knowledge/case-and-print.md` の前提・`case_spec.PRINT_LAYER` |
| PLA の E | 2580 MPa（前の見積りと同じ値） | 利用者の指定 |
| PLA の強さ | 引張 39 ± 2 MPa・曲げ 76 ± 3 MPa（Bambu PLA Basic の TDS。**検索結果の要約で読んだ。PDF は開けなかった**） | [TDS](https://wiki.bambulab.com/filament-acc/abs-asa-pc/bambu_pla_basic_technical_data_sheet.pdf) |

## 3. 積み上げ（spec の数から。机 = 0）— **2026-09-28 の膜 0.6 の記録。いまの値は §8**

| | 前 | 膜 0.6（2026-09-28） |
|---|---|---|
| 床 `CASE_FLOOR` | 1.2 | 1.2 |
| 基板の下の空き `UNDER_PCB` | 1.8 | 1.8 |
| 基板 `PCB_T` | 1.6（上面 4.6） | 1.6（上面 4.6） |
| ステムの上面（＋ 8.6） | 13.2 | 13.2 |
| **キャップの上面（＋ `KEYCAP_TOP_T`）** | **14.4**（＋ 1.2） | **13.8**（＋ 0.6） |
| 縁（基板 ＋ 7.0） | 11.6 | 11.6 |
| 押し切ったキャップの上面（− 3.05） | 11.35（縁より 0.25 低い） | **10.75（縁より 0.85 低い）** |

押し切ったキャップが縁より低いのは前からで（0.25）、深くなっただけ。縁（壁の上面）はキャップの外 1.3 以上離れた幅 1.3 の帯で、
端のキーの外の縁を指先で押し切ったとき、指が縁に触れて止まるかもしれない程度（`section_keycap_rim_pressed.png`）。
鞄の中で押されにくくなる向き。指で確かめてはいない（組んでから端のキーを押して見る）。

天板の場所ごとの厚さ（`keycaps.plate_levels` が spec から導き、層の倍数に切り下げる）。上面は基板の上 9.2:

| 場所 | 上限 = 9.2 −（障害物 ＋ 0.1 ＋ 3.05） | 層で切り下げ | 押し切りの隙 |
|---|---|---|---|
| ステムの上（φ6.5 の内） | ―（下面 = ステムの上面・ステムと一緒に動く） | **膜 0.6** | ― |
| ハウジングの上（13.95 ＋ 片側 0.2。1u はスカートまで） | 9.2 − 8.45 = 0.75 | **0.6** | 0.25 |
| つばの上の輪（φ6.5〜8.7） | 9.2 − 8.85 = **0.35** | **0.2（1 層）** | 0.25 |
| それより外（1.5u 以上の両脇・スタビの上） | スタビの箱 9.2 − 8.15 = 1.05 | **1.0** | 0.15 |

- **つばの上の輪は膜 0.6 にできない**: 押し切るとステムの上面は 8.60 − 3.05 = 5.55 まで下がり、つばの上面 5.70 より
  0.15 下に入る。膜をつばの上まで 0.6 にすると押し切りでつばに 0.15 当たる（前の案で 0.25 の窪みを彫っていた理由）。
  上面を 9.2 にしたままつばに 0.1 残すと、輪は 0.35 まで。0.35 は 0.2 層で 2 層目の真ん中（0.3）が中に入るので 0.4 に刷られ、
  隙は 0.05 になる。だから 1 層 0.2 に切り下げた。
- **ハウジングの上も 1.0 にできない**: 上限 0.75 を層で 0.6。1u はハウジングの逃げ（片側 7.175）とスカートの内側（7.275）の
  間が 0.1 しか残らないので、逃げをスカートまで広げた（`KEYCAP_PLATE_MIN_W`）。**1u に 1.0 の所は無い**。
- スタビの受け口: 台（φ5.1）の下端はステムの上面から 2.0 のまま（掴む深さそのまま）。台は 1.0 の天板から下がる。
  十字の穴の上に残す天板 0.6 → **0.4**（`STAB_SOCKET_TOP_KEEP`）で、穴の上端は軸の上端の 0.2 上。
- スカートの下端は動かさない（ステムの上面から 1.0 下）。見える側面は 2.2 → 1.6。
- 62 個の体積 35.2 → 22.2 cm³（約 −16g）。

## 4. 曲げ・抜き差しの見積り（`projects/cckb/tools/keycap_bending.py`）— §4-1 の「膜 0.6」の列は 2026-09-28 の記録。膜 1.0 の梁は §8

### 4-1. 梁（前の見積りと同じ方法）

片持ちの梁。支えから縁まで x で切った断面（天板＋スカート）の I(x) を刷る形から測り、縁に 3 N、δ = ∫P(x_e − x)²/(EI) dx。

| | 前（1.2） | 膜 0.6（2026-09-28） | 比 |
|---|---|---|---|
| 1u スカートあり（支え = ステムの外周 3.25 → 縁 9.0） | 13.9 µm・5.1 MPa | 41.8 µm・11.4 MPa | 3.0 倍 |
| 1u 天板だけ（両脇のスカートを除く） | 34.5 µm・5.9 MPa | 282.7 µm・26.2 MPa | 8.2 倍 |
| 2.25u スカートあり（支え = スタビの台の外周 14.45 → 縁 20.9） | 19.4 µm・5.4 MPa | 43.9 µm・8.5 MPa | 2.3 倍 |
| 2.25u 天板だけ | 46.2 µm・5.2 MPa | 79.8 µm・7.4 MPa | 1.7 倍 |

### 4-2. ステムのまわり（梁では見えない所）

**曲げの力がいちばん大きいのは縁ではなく支え（ステム）のまわり。**縁の荷重は、筒へ渡るとき必ず
つばの上の輪（r 3.25〜4.35）を通る（輪より内は膜と筒しか無い）。梁は断面を x で切るので、この集まりが見えない。
そこで円板（Kirchhoff・ν 0.35）を r の 1 次元の有限要素で解いた: 内の縁 = 筒の外周 r 2.75 を固定、1u の縁の真ん中
r 9.0 に 3 N、スカートは入れない（縁は自由）。厚さは `plate_levels` の値。

| 膜 | 上面 | 輪 | 縁のたわみ | 最大の曲げ応力（輪の内の縁） |
|---|---|---|---|---|
| 前 1.2（窪み 0.95） | 14.4 | 0.95 | 48 µm | **10.0 MPa** |
| 0.6（2026-09-28 の決定） | 13.8 | 0.2 | 1019 µm | **117.5 MPa** |
| 0.8（控え） | 14.0 | 0.4 | 290 µm | 43.2 MPa |
| **1.0（いま・2026-10-03）** | **14.2** | **0.6** | **119 µm** | **22.0 MPa** |
| 1.2（新しい式） | 14.4 | 0.8 | 60 µm | 13.2 MPa |

- 一様な板で検算: 厚さ 0.6 と 1.2 で応力の比 4.0（1/t²）・たわみの比 7.9（1/t³）。1.2 のたわみ 38 µm は梁の「天板だけ」34.5 µm と同じ桁。
- **縁に爪をかけて片側からこじって抜くのも、同じ形（荷重の向きが逆なだけ）**。抜く力は測っていない（Choc V2 の十字の保持力の公開値は見つけていない）。
- 引張強さ 39 MPa に対して、0.6 は 3 N で約 3 倍、0.8 は約 1.1 倍。**1.0 で約 0.56 倍、前の 1.2 で約 0.26 倍**。
  繰り返しの荷重（打鍵）では静的な強さより低いところで割れる。

**結論（見積り）: 2026-09-28 に利用者の決めた形（膜 0.6・輪 0.2）は、キーの縁を押すと輪から割れる恐れが高い。**
**→ 2026-10-03 利用者の決定: 既定を膜 1.0（輪 0.6・22 MPa）にする（§8）。**
「ステムの上は支えられるので薄くてよい」は膜の真ん中（φ5.7 の内）には当たるが、支えのすぐ外の輪は、
縁からの曲げをすべて筒へ渡す所で、しかもつばの逃げのためにいちばん薄くなる所。

## 5. 小片 coupon_skin（本番の 1u を膜 0.6 / 0.8 / 1.0 で）

- 本番の 1u のキャップを `KEYCAP_TOP_T` だけ替えて 3 個（場所ごとの厚さは同じ式。輪は 0.2 / 0.4 / 0.6）。スカートの手前の下端に
  切り欠き 1 本 = 0.6・2 本 = 0.8・3 本 = 1.0。A1 mini で 12 分・1.14 cm³。
- **0.6 と 0.8 は利用者の決定。1.0 は §4-2 の見積りで引張強さの半分を下回る最初の厚さとして Claude が足した。**
- やること: 静音のスイッチに挿し、天板の縁に爪をかけて 10 回抜き差し・縁の真ん中を指で強く押す（10 回）。
  膜・輪が割れないか・白くならないか・筒が取れないか・押したたわみが気にならないか。
- **2026-10-03 から既定は 1.0（切り欠き 3 本）**。0.8 が割れなければ `spec.KEYCAP_TOP_T` を 0.8 にして `case.py` で出し直してよい
  （全体の厚さは 0.6 / 0.8 / 1.0 で 13.8 / 14.0 / 14.2。検査 `tests/test_cckb_interface.py` の上限は 14.2 なので、下げる分には直さなくても通る。
  場所ごとの厚さを固定している `test_the_keycap_plate_clears_…` の期待値は直す）。膜は 1 つの定数。

## 6. 回した検査（2026-09-28・膜 0.6 のとき。2026-10-03 に回した物は §8）

- `keycaps.plate_levels`: 障害物の上面 ＋ 0.1 を割ったら・スタビの箱に当たる厚さなら・輪が 1 層を割るなら落とす
  （`test_the_plate_levels_refuse_what_cannot_clear_or_print`）
- 押し切りで天板の下面がハウジング・つば・スタビの箱に 0.1 以上（`test_the_keycap_plate_clears_the_housing_the_collar_and_the_stab_box`、
  数は図の値から）。**壊して落ちる**: つばの上の逃げを消す・ハウジングの上に厚い天板を置く → 押し切りのキャップが
  スイッチ（図の包絡）に当たる（`test_the_pressed_check_notices_a_plate_over_the_switch`）
- 組み立ての干渉（押す前・押し切り）をプレート無し・ありの両方で 0（`test_pressed_keycaps_hit_nothing`・`assembly.py`）
- 全体の厚さ 13.8 以下（`z_problems`。膜 0.8 で落ちる）・縁 ≧ 押し切ったキャップ・ふた・角のふた・電源スイッチのレバー（O13）・
  USB のプラグ・XIAO は高さがキャップに依らず前と同じ検査が通る
- 肉の刺し検査（膜 0.6・ハウジングの上 0.6・輪 0.2・2.25u の外 1.0・スカート・筒の腕の先）
- スライス: A1 mini 14/14・K1 Max（`tools/kb cckb slice`）。キャップは 18 層（3.6）。**輪が 1 層で刷られることを G-code で見た**（§7）
- 基板は変わらない（sha256 abcd20ff…）
- 全検査 `REQUIRE_KICAD=1 .venv/bin/pytest tests -q`: **468 passed・飛ばし 0**（7 分 24 秒）。発注の門 `tools/kb cckb gate`: 閉 #1・#4（前と同じ）
- 断面: `build/cckb/keycap_skin_before_after.png`（前後・押す前と押し切り・`projects/cckb/tools/draw_keycap_skin.py`）・
  `section_keycap_rim_pressed.png`（左端の Tab を押し切った所と縁）・`section_keycap_socket*.png`・`section_stab_across*.png`。
  組み立ての `.blend` も出し直した（`assembly.py`）

## 7. 刷り方

キャップは天板をベッドに刷る（上下を返す）。**膜 1.0（いま）: 膜・ハウジングの上・外は 1〜5 層目、輪は 1〜3 層目。キャップは 20 層（4.0）**。
膜 0.6（2026-09-28）のときは: 膜は 1〜3 層目・輪は 1 層目だけ・ハウジングの上は 1〜3 層目・外は 1〜5 層目・18 層。
輪は上に何も載らない薄い所で、上から見ると膜の中に φ6.5〜8.7 の輪が透けて見えうる（白い PLA は透ける。3 層なら 1 層より見えにくいはずだが刷って見ていない）。

## 検討して捨てた案

| 案 | 捨てた理由 |
|---|---|
| 輪も膜 0.6（つばの上を彫らない） | 押し切りでつばに 0.15 当たる（利用者の条件 0.1 の隙を割る）。壊す検査で当たることを見た |
| 輪を 0.35 で設計 | 0.2 層で 0.4 に刷られ、隙 0.05（条件割れ） |
| ハウジングの上を 0.75 で設計 | 同じく 0.8 に刷られ、隙 0.05 |

## この決定が乗っている前提（**動いたら読み直す**）

- 行程の最大 3.05（静音）・つば 5.70・φ7.9・ハウジング 5.30 と上の胴の平面（包絡 13.95 角）。見本で上の胴が小さいと分かれば、
  逃げを狭めて 1u にも 1.0 の帯を残せる
- 0.2 層で刷る（層を変えると `PRINT_LAYER` を直す。輪の厚さが変わる）
- スタビの軸の上端 = ステムの上面（どちらも 8.60）

## 覆す前に読むこと

§4-2・§8。膜の厚さを変えるときは `spec.KEYCAP_TOP_T` だけを変える（外・輪・ハウジングの上は式が導く）。

## 8. 2026-10-03 利用者の決定: 既定の膜を 1.0 にする（上面 14.2）

**理由**: 膜 0.6 では、押し切りで静音のつばに 0.1 残すために、つばの上の輪が 1 層 0.2 になる。§4-2 の見積りで、キーの縁を
3 N で押すと輪に 118 MPa（PLA の引張強さ 約 39）= 割れる。膜 1.0 なら輪は 0.6 で 約 22 MPa（強さの 約 0.56 倍）。
**`coupon_skin`（0.6 / 0.8 / 1.0）を刷って 0.8 が割れなければ、0.8（14.0・輪 0.4・見積り 43 MPa）に下げてよい。**

変えたのは `spec.KEYCAP_TOP_T` 0.6 → 1.0 だけ。ほかは `keycaps.plate_levels` が導く。上面は基板の上 9.6:

| 場所 | 上限 = 9.6 −（障害物 ＋ 0.1 ＋ 3.05） | 層で切り下げ | 押し切りの隙 | 膜 0.6 のとき |
|---|---|---|---|---|
| ステムの上（φ6.5 の内） | ―（下面 = ステムの上面） | **膜 1.0** | ― | 0.6 |
| ハウジングの上 | 9.6 − 8.45 = 1.15（外の 1.0 を超えない） | **1.0** | **0.25** | 0.6（隙 0.25） |
| つばの上の輪（φ6.5〜8.7） | 9.6 − 8.85 = 0.75 | **0.6（3 層）** | **0.25** | 0.2（隙 0.25） |
| それより外（1.5u 以上の両脇・スタビの上） | スタビの箱 9.6 − 8.15 = 1.45。`KEYCAP_PLATE_T` 1.0 | **1.0** | **0.55** | 1.0（隙 0.15） |

| 積み上げ（机 = 0） | 天板 1.2（〜09-27） | 膜 0.6（09-28） | **膜 1.0（いま）** |
|---|---|---|---|
| ステムの上面 | 13.2 | 13.2 | 13.2 |
| **キャップの上面** | 14.4 | 13.8 | **14.2** |
| 縁 | 11.6 | 11.6 | 11.6 |
| 押し切ったキャップの上面（− 3.05） | 11.35（縁より 0.25 低い） | 10.75（0.85 低い） | **11.15（縁より 0.45 低い）** |

- **天板は輪を除いて一様に 1.0** になった（膜 = ハウジングの上 = 外）。ハウジングの上の逃げ（`KEYCAP_HOUSING_MARGIN`・`KEYCAP_PLATE_MIN_W`）は
  式に残るが、いまは削る物が無い（膜を 0.8 以下にするとまた働く）。
- スタビの受け口: 十字の穴の上に残す天板は 0.4 のまま（`STAB_SOCKET_TOP_KEEP`）。穴の上端は軸の上端の **0.6 上**（膜 0.6 では 0.2）。掴む深さ 2.0 のまま。
- スカートの下端は動かさない。見える側面は 1.6 → **2.0**（天板 1.2 では 2.2）。
- 梁の見積り（§4-1 と同じ方法・膜 1.0）: 1u スカートあり 19.6 µm・6.6 MPa／天板だけ 60.9 µm・9.3 MPa、
  2.25u スカートあり 27.5 µm・7.1 MPa／天板だけ 79.8 µm・7.4 MPa。
- 62 個の体積 22.2 → **30.3 cm³**（天板 1.2 は 35.2）。A1 mini のスライスで 2 枚 **5h04m・29.9 cm³・約 37g**
  （`keycaps_set_1u` 3h42m・21.59 cm³、`keycaps_set_wide` 1h22m・8.30 cm³。膜 0.6 は 3h48m・21.8 cm³・約 27g）。

**2026-10-03 に回した検査**

- 押し切りで天板の下面がハウジング・つば・スタビの箱に 0.1 以上（上の表の 0.25 / 0.25 / 0.55）・厚さが層の倍数・
  場所ごとの厚さが (1.0, 1.0, 0.6, 1.0)（`test_the_keycap_plate_clears_the_housing_the_collar_and_the_stab_box`）
- **壊して落ちる**: つばの上の逃げを消すと押し切りでつばに当たる。ハウジングの上の逃げは膜 1.0 では働いていないので、
  外を 1.4 にして逃げが働く形にしてから逃げを消すと当たる・消さなければ当たらない（`test_the_pressed_check_notices_a_plate_over_the_switch`）。
  外 1.6 はスタビの箱に当たるので式が落とす・膜 0.4 は輪が 1 層を割るので落とす（`test_the_plate_levels_refuse_…`）
- 全体の厚さ 14.2 以下（`z_problems`）。**膜 1.2（14.4）で落ちる**・床 1.6・ステム 8.7 でも落ちる（`test_the_z_check_notices_a_break`）
- 組み立ての干渉 0（押す前・押し切り）・経路 0（`assembly.py`）。`.blend` と断面を出し直した
- スライス: A1 mini 14/14（キャップは 20 層）。**輪が 3 層で刷られることを G-code では見ていない**（膜 0.6 のときは 1 層を G-code で見た）。K1 Max は回していない
- 基板は変わらない（sha256 abcd20ff…）
- 全検査 `REQUIRE_KICAD=1 .venv/bin/pytest tests -q`: **468 passed・飛ばし 0**（7 分 24 秒）。発注の門 `tools/kb cckb gate`: 閉 #1・#4（前と同じ）

## まだ決めていないこと

| 項目 | 決められない理由 |
|---|---|
| 膜を 0.8（14.0）に下げるか | `coupon_skin` を刷って、0.8 が抜き差しと縁の押しで割れないかを見てから利用者が決める。見積りでは 0.8 は 43 MPa（引張強さの 約 1.1 倍）で際どい |
