ms0216/keyboard-foundry/projects/cckb/docs/decisions/2026-09-24-power-switch.md

# 電源スイッチを秋月の SS-12D00G3（表・レバーが上）にし、右のふたの穴から爪で動かす

- **日付:** 2026-09-24
- **状態:** 決定（部品と置き方は利用者。寸法・配線・ケースの形はこの記録）
- **決めた人:** 利用者（部品と置き方の案）・Claude（寸法と検査）

**結論**: 電源スイッチを LCSC の MK-12C02-G025（C778186・基板の裏・横へ出るつまみを右の側面の窪みから操作）から、
秋月電子の **SS-12D00G3**（115707・¥20・スルーホール・レバーが上）に替えた。**基板の表の右の縁**に長辺を y に向けて置き、
レバーは**右のふた（電池のふた）の穴**の中に来る。先はふたの上面より名目で 0.1 下（出っ張らせない）で、爪で上から押す。
**奥へ押すと入**（ふたに「ON ↑」を彫った）。電池ホルダは**左へ 3.8** 寄せた。足は付けた後で基板の下面から 1.0 に切る。
板の変更は SW_PWR と BT1 の位置と、網 **VBAT_IN・VBAT_SW** の右の角の部分の配線だけ（ほかの 88 網は前の板と同じ）。

図: `build/cckb/psw_section.png`（断面・スイッチを 1 つの部品として囲んだ）・`build/cckb/psw_corner_iso.png`（右の角・ふたを
持ち上げた）・`build/cckb/interface_corner_right.png`（平面と断面 B・C）

## 1. なぜ決める必要が生じたか

利用者が 2026-09-24 に決めた: 国内で買える品にする（前の品は LCSC で最小 5 個・送料が部品代より高い）。候補は
**SK-12D11VG3（横レバー）**・**LCSC の MK-12C02-G025（いまの品）**・**SS-12D00G3（上レバー）** の 3 つで、利用者が
SS-12D00G3 を上へ向けてふたの穴から操作する案を選んだ。横レバーの案は、前の検討でホルダを 5.5 動かす必要があり、
右の壁の切り欠きと窪みも残る（利用者の比較による。ここでは測り直していない）。

## 2. 事実（読んだもの）

秋月の PDF <https://akizukidenshi.com/goodsaffix/AKIZUKI-SS-12D00G3.pdf>。1〜4 ページ目が仕様書 JBL-SS/SK-2010
（XIAMEN JINBEILI・2019-03-01 A 版）、5 ページ目が図面 DRWG. NO SS12D00GXX-A03（2020-06-15）。商品ページ
<https://akizukidenshi.com/catalog/g/g115707/>（2026-09-24 に見た: ¥20・通販在庫 38,944・長さ 6.5 = 3.5＋3.0）。

| | 値 | 出所 |
|---|---|---|
| 機能・定格 | 1P2T・ノンショーティング・DC 30V 0.3A・接触抵抗 100mΩ 以下・絶縁 100MΩ 以上（端子と枠も） | 仕様書 1〜4.3・図面 |
| 寿命・作動力 | 10,000 回・230±80gf（先から 3mm で） | 仕様書 5.1・6.1 |
| 使う温度 | 図面 −20〜+70℃、仕様書 6.9 は −20〜+60℃ | 図面・仕様書（狭い方を採る） |
| 本体 | 8.5 × 3.7・高さ 3.5±0.1（台座の下面から） | 図面 |
| レバー | 1.5 角・本体の上に X = 3.0・ストローク 2。上面図の窓は本体の中心 | 図面（窓の位置は図を読んだ） |
| 足 | 0.5 × 0.3 を 2.5 間隔で 3 本・台座の下面から 3.9±0.2（全体 7.4±0.2） | 図面 |
| 推奨の穴 | 3-φ0.8・2.5 間隔 | 図面の PCB LAYOUT |
| 共通 | 真ん中 | 図面の回路図 |
| 一般公差 | 1.5 以下 ±0.1・1.5 を超える ±0.2 | 図面の欄 |
| 手はんだ | 320±5℃・2±1 秒 | 仕様書 6.3 |
| **枠の爪** | 台座の下へ折り返した金属の爪 4 つが下へ出る（側面図は外側の足の脇、端面図は長辺の縁）。**寸法の記載なし** | 図面（縮尺 4:1 の図を 600dpi で読んで側面図 0.39・端面図 0.30〔2026-09-24 監査 audit-psw.md 軽微 1 で 0.37 は読み違いと訂正〕）・秋月の商品写真（本体 3.5 を物差しに 0.36）。読みの範囲は 0.30〜0.39、`spec.PSW_TAB` の 0.4 は大きい側（安全側） |

**依頼の数字との違い**: 依頼は「基板の上面 4.6 → 本体の上面 8.1 → レバーの先 11.1」だったが、**爪 0.4 の分だけ本体が浮く**
（台座の下面から 3.5 と 3.9 を測る図なので、爪は寸法の外）。名目で本体の上面 8.5・レバーの先 11.5（ふたの上面 11.6 の 0.1 下）。
公差（本体 ±0.1・レバー ±0.2）に加え、**基板の厚さの公差 ±0.16**（JLC の 1.6mm 板 ±10%・
<https://jlcpcb.com/capabilities/pcb-capabilities>）も積む。基板は床のボスに下面で載り、ふた（rim）は名目 1.6 で刷った
固定の立体なので、**基板が厚いほどレバーの先はふたに対して相対的に上がる**（2026-09-24 の監査 audit-psw.md 重要 1 で
この項が抜けていたと判明。最初の記録は本体 ±0.1・レバー ±0.2 だけで最悪 +0.2 としていたが誤り）。
3 つを積むと 11.04〜11.96 で、**最悪ではふたの上面から 0.36 出る**。爪の出は [暫定]（`spec.PSW_TAB`）。
→ open-gaps **O13** で利用者に選んでもらう（§まだ決めていないこと）。

## 3. 効く条件

| # | 条件 | 実データ | 何で確かめたか |
|---|---|---|---|
| 1 | 鞄の中でレバーが出ない | 先は名目 −0.1（最悪 +0.36。本体 ±0.1・レバー ±0.2・基板の厚さ ±0.16 を積む） | 外（図面・JLC の PCB Capabilities）＋ 爪は図の縮尺と写真（[暫定]）。検査 `nail_problems`（名目）・`psw_tip_margin`（最悪を表示） |
| 2 | 爪で上から動かせる | 穴の両端に爪 1.0（`PSW_SLOT_NAIL`）＋隙 0.4。爪（厚さ 1.0 の箱）がレバーの先から 0.5 下まで入る | 自分の生成物（組み立て）。**爪の形は仮定**（下）→ 試し刷り（P4） |
| 3 | ふたを真上に外せる・付けられる | レバーは穴の中を縦に抜ける | 組み立ての経路 `path_problems`（穴を狭めると落ちる） |
| 4 | 電池の出し入れ・柱との間 3.0 以上 | ホルダの左と柱の間 7.4 | `test_the_corner_parts_fit_their_corners` |
| 5 | ホルダの動きが最小 | 本体（最大 3.9）の右を基板の縁に揃え、2 つのコートヤード（余白 0.25 ずつ）が触れない所まで: 3.8 | 同上（ホルダを 0.5 戻すと落ちる）・DRC（courtyards_overlap 0） |
| 6 | 本体が基板・ふたの空間の中 | 本体の右 143.175 = 基板の縁、壁の内面まで 0.5 | 同上・組み立ての干渉 0 |
| 7 | 足が床に当たらない | 切らないと基板の下に 1.9〜2.3（下の空き 1.8）→ 1.0 に切る。**床は厚くしない・掘らない** | 組み立て（切らない足は床に当たる: `test_the_power_switch_pins_must_be_trimmed`） |
| 8 | 穴が図の足に合う | φ0.8・2.5 間隔・ランド φ1.6 | 外（図面）↔ 板（`test_the_power_switch_pads_hold_the_terminals_of_the_drawing`） |
| 9 | 金属の枠が表の違う網をまたがない | 爪の下（本体の両端 ＋0.3）に表の銅を置かない（`PSW_TAB_KEEPOUT`） | 板の塗った後の銅（`test_nothing_on_top_under_the_power_switch_frame_tabs`） |
| 10 | 入の向き | レバーの側の足が共通と繋がる（図の読み）→ 奥の足を VBAT_SW・ふたに ON ↑ | 図の読み（**未**: テスター・P5）。板の向きは `test_the_on_side_of_the_power_switch_is_the_marked_side` |
| 11 | 国内で買える・安い・在庫 | 秋月 ¥20・38,944 | 外（商品ページ） |

**爪の形の仮定**: 爪を「厚さ NAIL_T 1.0・幅はレバーと同じ」の箱として、穴の端から上に差し込む。実際の爪の先は曲がっていて、
穴の幅 2.4 の向きに置くと沈みは小さい。穴の長さの向き（y）に爪を立てて差す使い方を想定している。**刷って確かめる**（P4）。

## 4. 影響範囲（端から端まで）

- **回路**: CR1632 ＋ → BT1.1（VBAT_IN）→ SW_PWR.2（真ん中）→ 入で SW_PWR.1（奥）→ VBAT_SW → 分圧・D_PWR。SW_PWR.3 は空き
  （`circuit.py`・`foundry/pinmap.py` の `slide_ss12d00`。耳 4 つのパッドは無くなった）
- **基板**: SW_PWR（表・`lib/cckb.pretty/SW_SS-12D00G3`）を (141.225, −38.6)、BT1 を (124.7, −38.6)（前は 128.5）。
  網 VBAT_IN は表で ＋ のパッドから真ん中の足へ真っすぐ 4.4、VBAT_SW は裏の長い線（y −28.392）の右端 118.689 から
  133.517 まで伸ばして 45° で奥の足へ（Freerouting・`route_pcb.py --reroute VBAT_IN,VBAT_SW --clear 95.25,-47.925,143.175,-28.575`）。
  前の位置決めの穴（φ0.9 ×2）が無くなったので、**DRC の npth_inside_courtyard を警告に下げるのをやめた**（spec.DRC_SEVERITY を消した）。
  DRC 違反 0・未配線 0・警告 3（silk_edge_clearance・前と同じ 3 件）
- **発注ファイル**: BOM 4 行・CPL 69 行は変わらない（スイッチは前から手はんだ）
- **ケース**: トレイの右の壁の切り欠きと指の窪み、右のふたのひれを消した。右のふたにレバーの穴 6.4 × 2.4 と刻印「ON ↑」（深さ 0.4）
- **組み立てモデル**: 電源スイッチは表の 1 つの立体（本体・レバーの動く範囲・切った足）。爪の検査を上から入る形に書き直した
- **手順書・買い物**: 秋月で 3 個。ホルダを先に付け、スイッチは表から差して裏から付け、足を切る（assembly-guide 手順 3・4）

## 5. 決めたこと

上の結論のとおり。値は `spec.py` の `PSW_*`・`HOLDER_AT`、`case_spec.py` の `PSW_SLOT_*`・`PSW_MARK_*`・`PSW_NAIL_REACH`。

## 検討して捨てた案

| 案 | 捨てた理由 |
|---|---|
| 本体の長辺を x に置く | ホルダを 8.5＋隙 ほど左へ動かすことになり、柱との間 3.0（電池を取り出す指の場所）を割る |
| スイッチをホルダの左（柱との間）に置く | 空きは 10.5 あるが、電池を取り出す指・道具の入る側を塞ぐ。利用者の案は「右の角・ホルダを左へ」 |
| 足を切らずに床を掘る | 足の先は机から 0.9〜1.1 まで下がる。床 1.2 の中で止めると床が 0.1 前後しか残らない（肉厚の下限 1.2）。床に穴を開けると足が裏から見える |
| レバーの先を必ずふたの上面より下にする（縁を上げる・ふたの上に土手・レバーを切る） | どれも見た目・手間が変わる（利用者が決めること）→ O13 |

## この決定が乗っている前提（動いたら読み直す）

- 爪の出 0.4（[暫定]）。大きいとレバーがふたから出る（O13）、小さいと足の出が増える（切るので影響は小さい）
- 縁の高さ `RIM_ABOVE_PCB` 7.0・ふた 1.2（ホルダで決まる）。縁を動かすとレバーの先との差が動く
- 「レバーの側の足が共通と繋がる」（図の読み）。違ったら刻印の向き `PSW_ON` を反対にする（板はそのまま）

## まだ決めていないこと

| 項目 | 決められない理由 |
|---|---|
| O13 レバーの先が公差の最悪でふたの上面から 0.36 出うる（基板の厚さの公差を入れる前は 0.2 と書いていた） | 直し方が見た目か手間（利用者が決める）。届いた 1 個を測れば、出ないと分かることもある |
